roberto314/Unicomp3/USB-Serial InputBoard/pdf/USB-Serial InputBoard.pdf

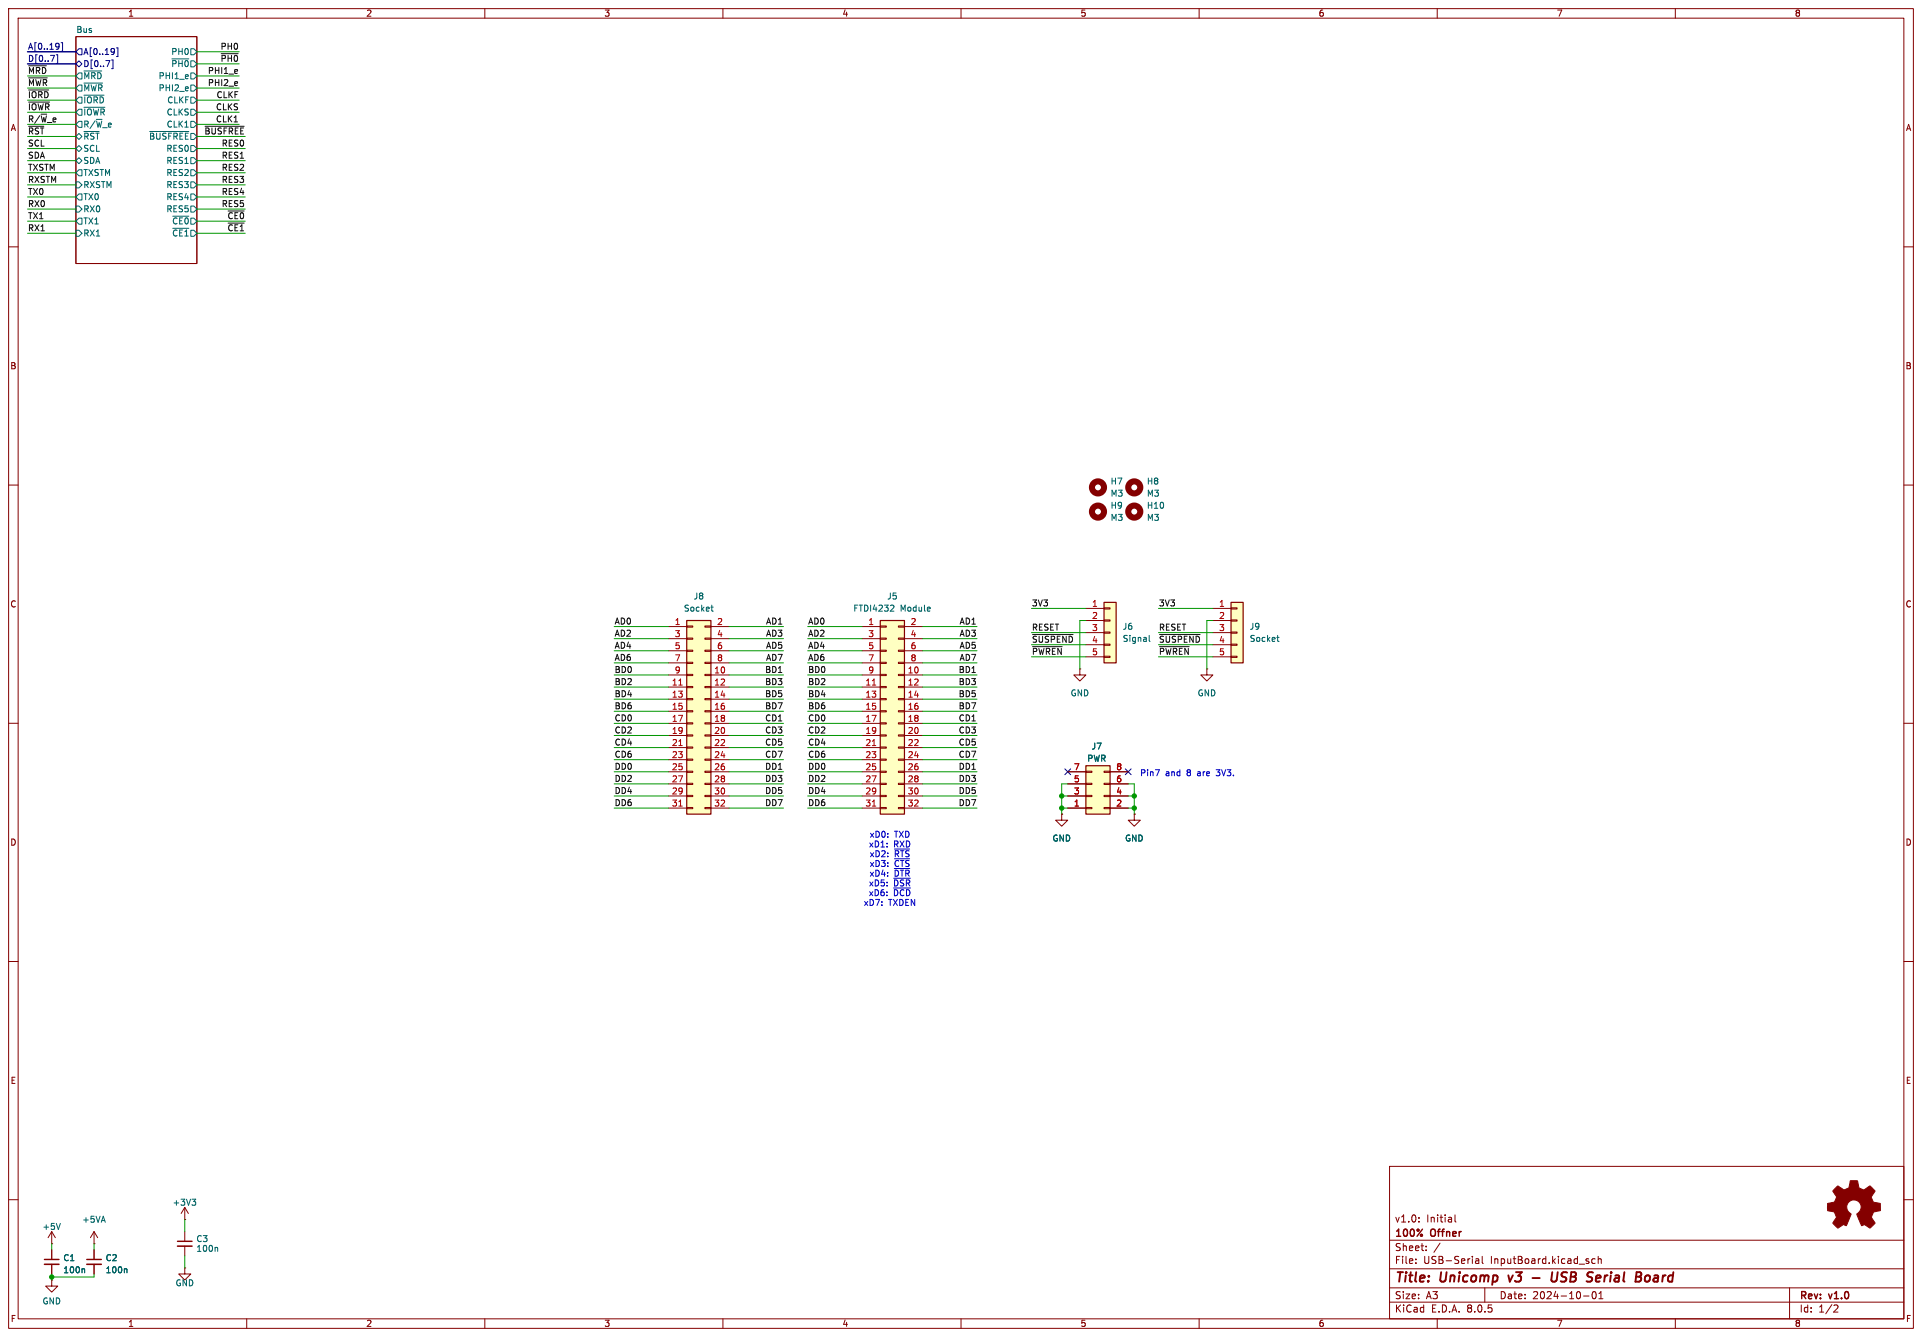
[picture p14: page 1]

xD0: TXD
xD1: RXD
xD2: ~{RTS} xD3: ~{CTS} xD4: ~{DTR} xD5: ~{DSR} xD6: ~{DCD} xD7: TXDEN

Id: 1/2 Title: Unicomp v3 - USB Serial Board

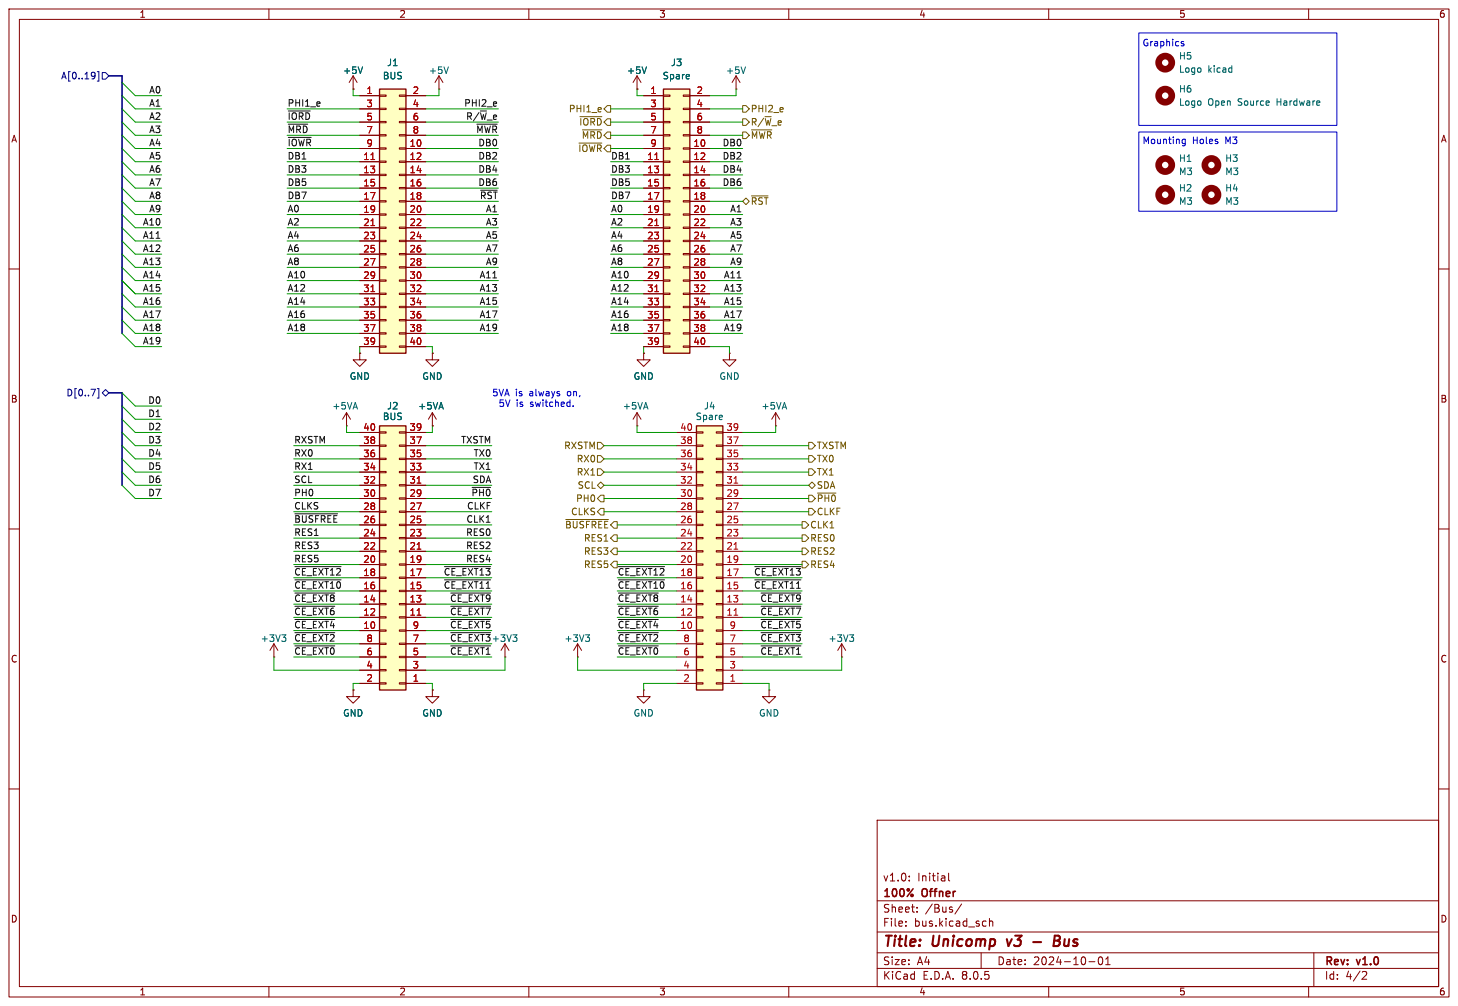
[picture p15: page 2]

Id: 4/2 Title: Unicomp v3 - Bus
