roberto314/Unicomp3/empty Boards/cpu_template_with_buffer/pdf/cpu_template_with_buffer.pdf

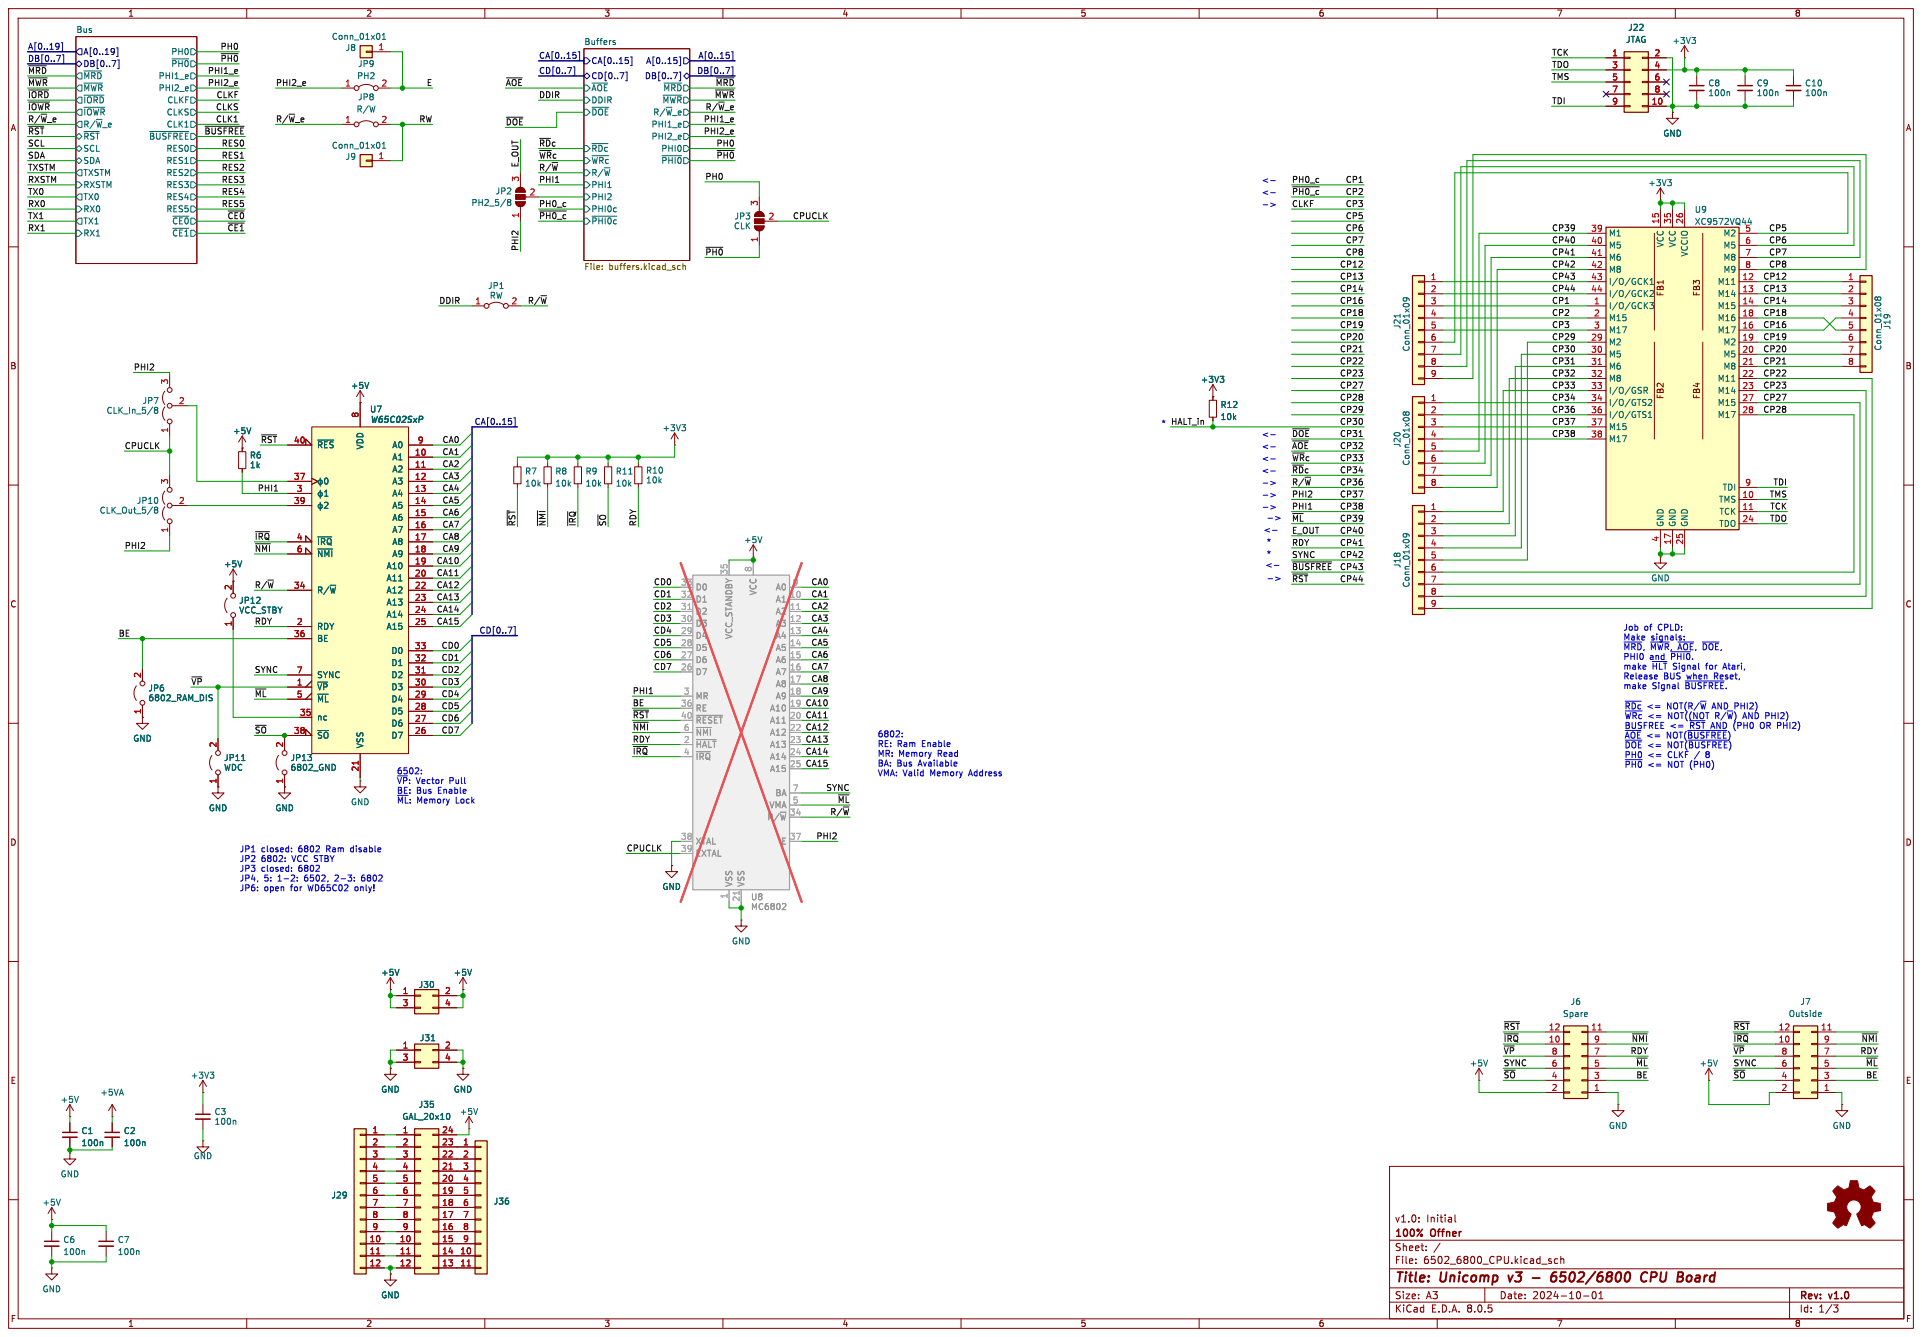
[picture p16: page 1]

DB[0..7] Buffers File: buffers.kicad_sch
PHI1_e CD6

~{DOE}<= NOT(~{BUSFREE}) PH0 <= CLKF / 8 ~{PH0}<= NOT (PH0) * <-

<- <- 6502: ~{VP}:Vector Pull BE: Bus Enable ~{ML}:Memory Lock

~{MRD},~{MWR},~{AOE},~{DOE}, PHI0 and ~{PHI0}. make ~{HLT}Signal for Atari, Release BUS when Reset, make Signal ~{BUSFREE}. <-
E_OUT

1 A1 10 A2 11 A3 12 A4 13 A5 14 A6 15 A7 16 A8 17 A9 18 A10 19 ~{HALT} 2 A11 20 VSS 21 A12 22 A13 23 A14 24 A15 25 D7 26 D6 27 D5 28 D4 29 MR 3 D3 30 D2 31 D1 32 D0 33 R/~{W}34 VCC_STANDBY 35 RE 36 E

~{RDc}<= NOT(R/~{W}AND PHI2)
~{WRc}<= NOT((NOT R/~{W})AND PHI2) BUSFREE <= ~{RST}AND (PH0 OR PHI2)

6802: RE: Ram Enable MR: Memory Read BA: Bus Available VMA: Valid Memory Address

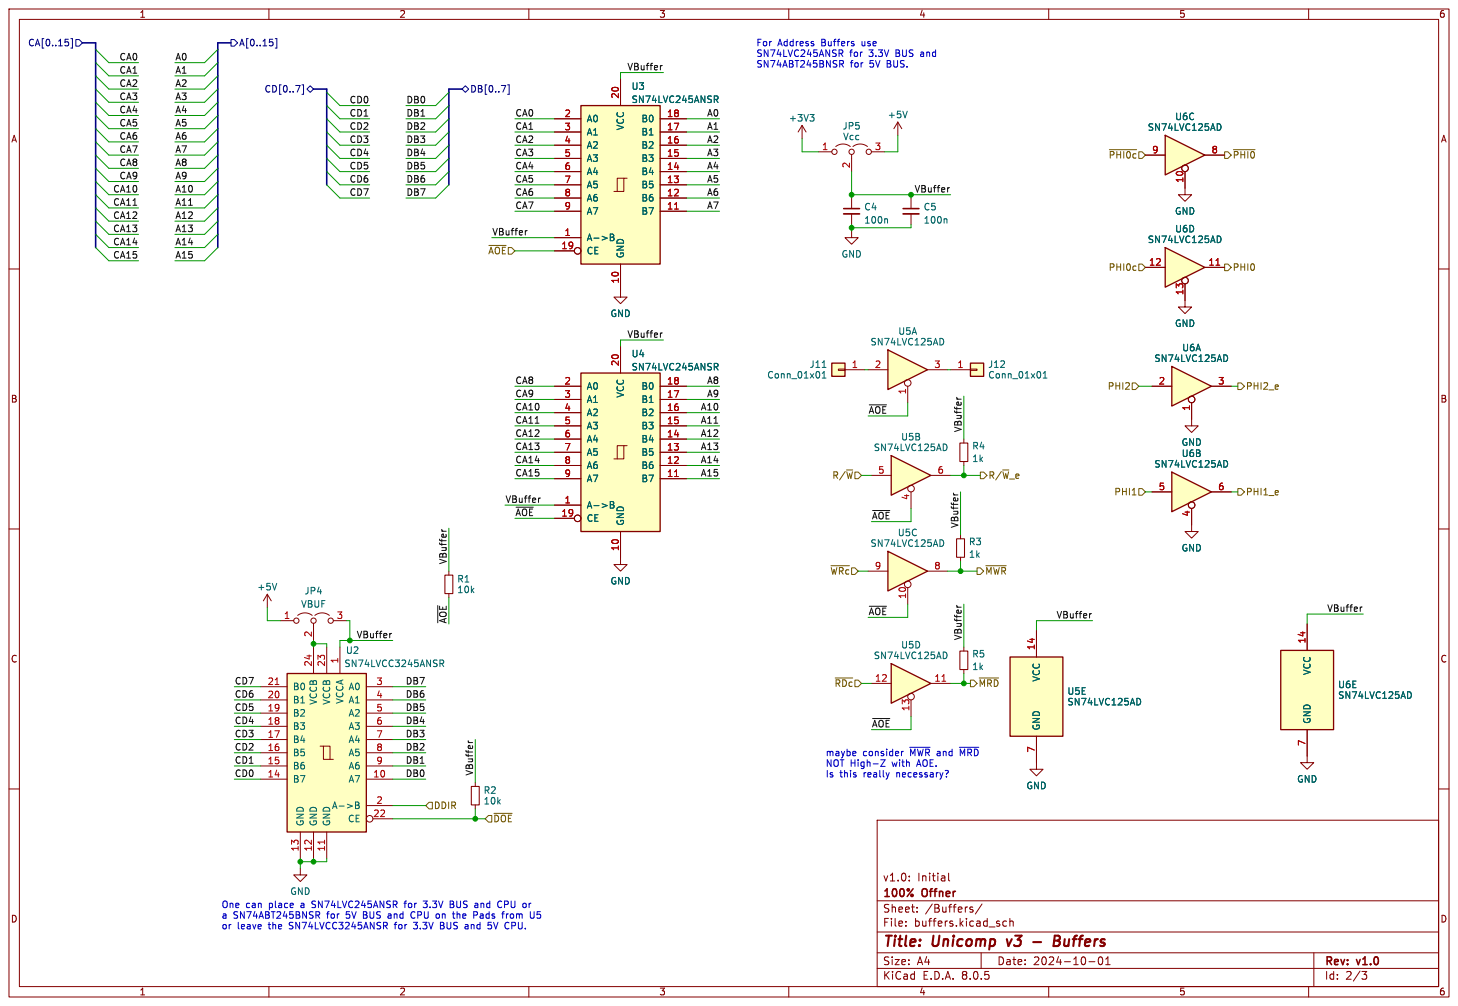
[picture p17: page 2]

1 A7 10 GND 11 GND 12 GND 13 B7 14 B6 15 B5 16 B4 17 B3 18 B2 19 A->B 2 B1 20 B0 21 CE 22 VCCB 23 VCCB 24 A0 3 A1 4 A2 5 A3 6 A4 7 A5 8 A6 9 U2 SN74LVCC3245ANSR

One can place a SN74LVC245ANSR for 3.3V BUS and CPU or a SN74ABT245BNSR for 5V BUS and CPU on the Pads from U5

Id: 2/3 Title: Unicomp v3 - Buffers

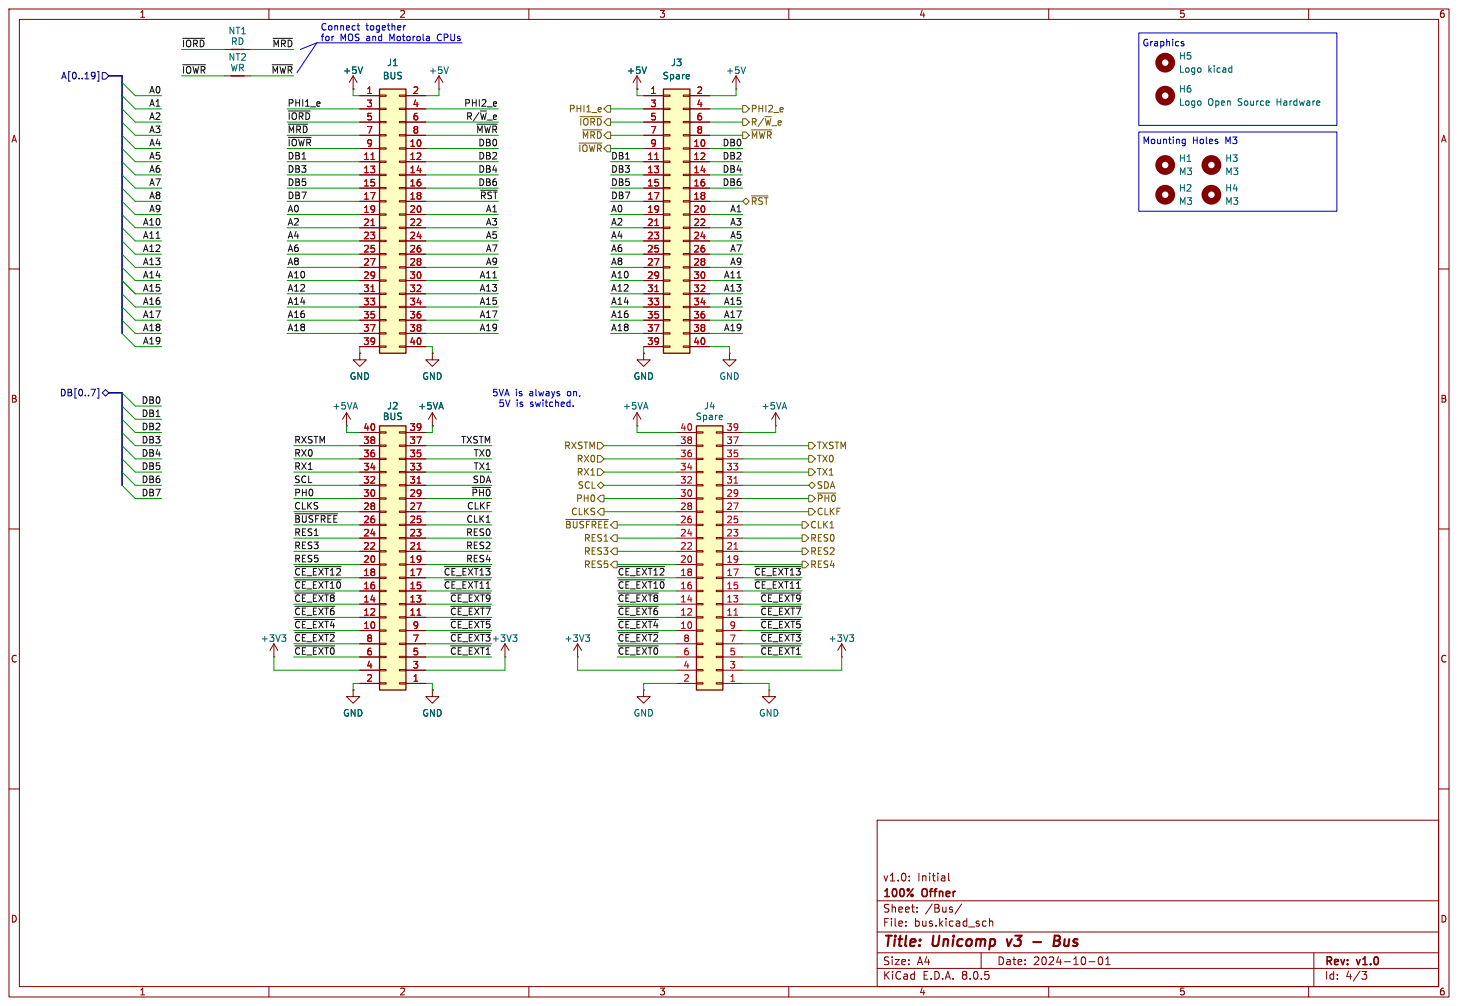
[picture p18: page 3]

Id: 4/3 Title: Unicomp v3 - Bus
