roberto314/Unicomp3/empty Boards/emptyBoard/pdf/emptyBoard.pdf

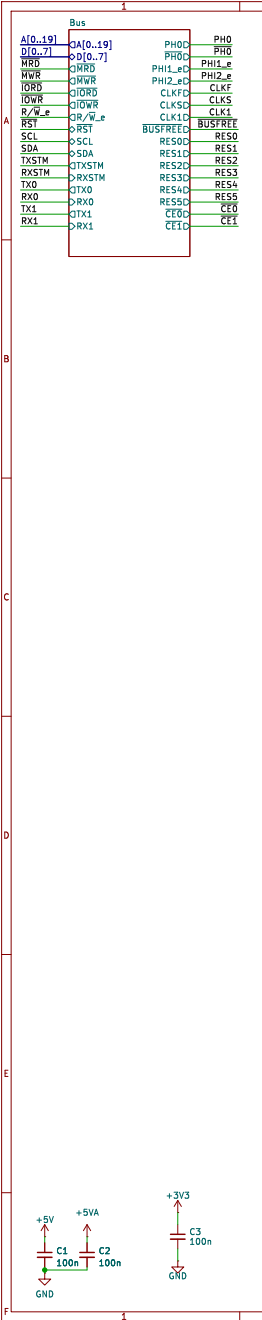
[picture p19: page 1]

Id: 1/2 Title: Unicomp v3 - xxx Board

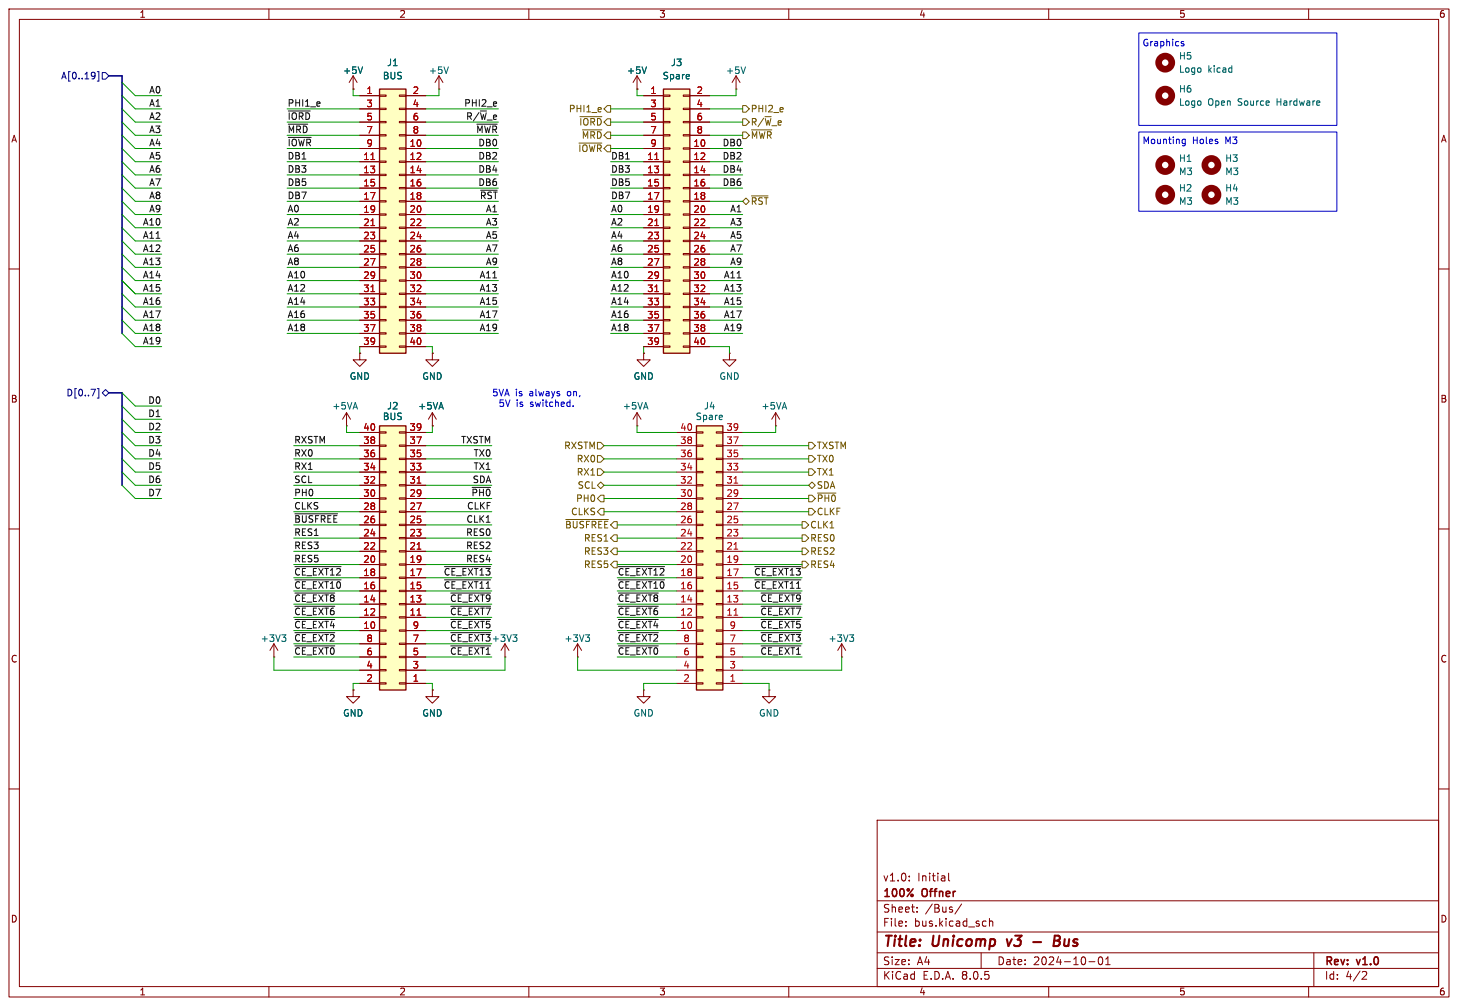
[picture p20: page 2]

Logo Open Source Hardware H5

Id: 4/2 Title: Unicomp v3 - Bus
