roberto314/Unicomp3/SerialBoards/MOT_SerialBoard/MOT_Serial_v11/pdf/MOT_Serial_v11.pdf

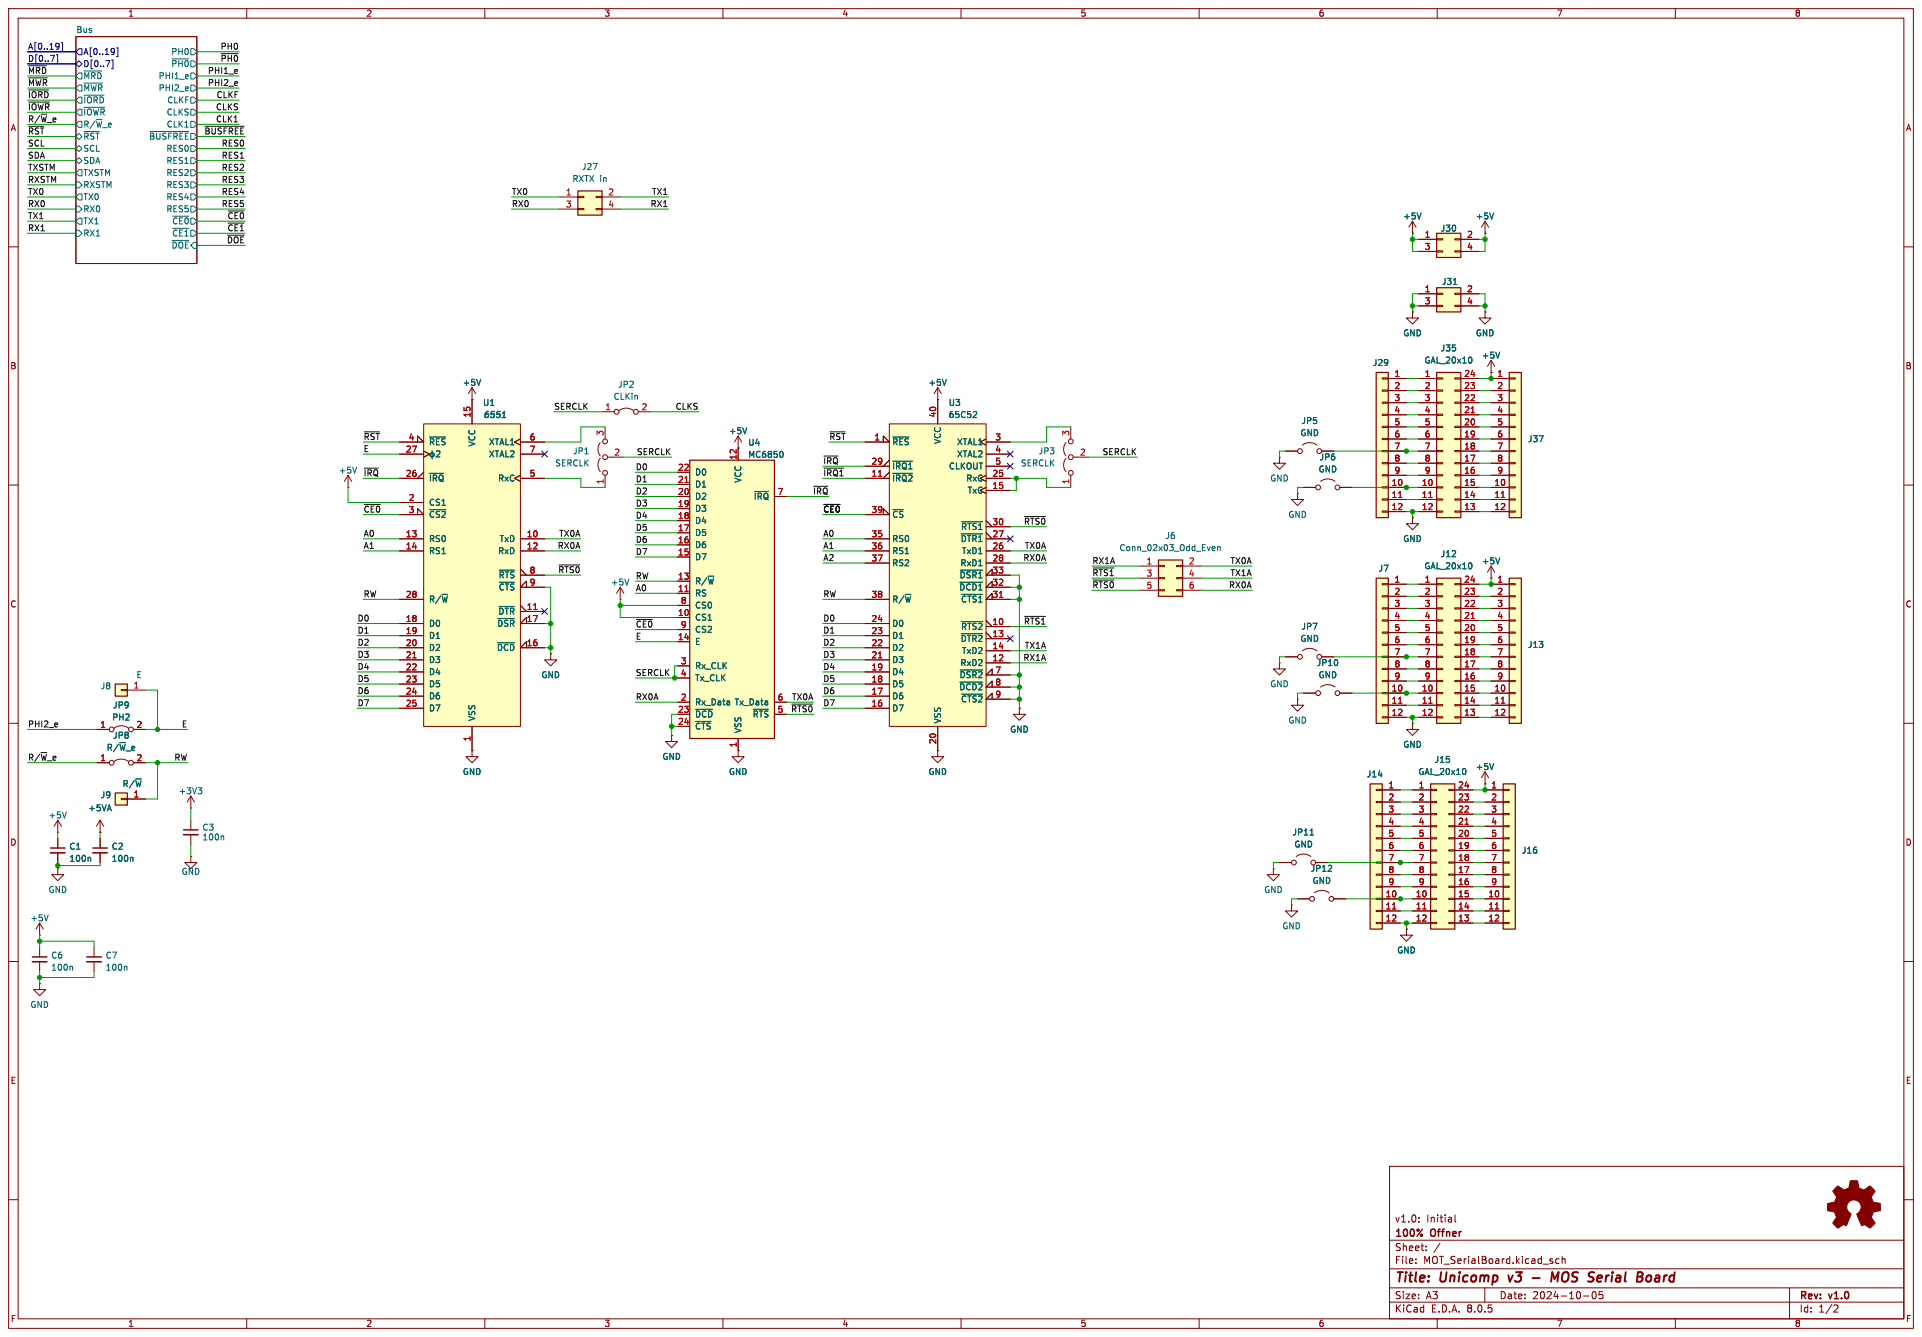
[picture p23: page 1]

1 TxD 10 ~{DTR}11 RxD 12 RS0 13 RS1 14 VCC 15

Id: 1/2 Title: Unicomp v3 - MOS Serial Board

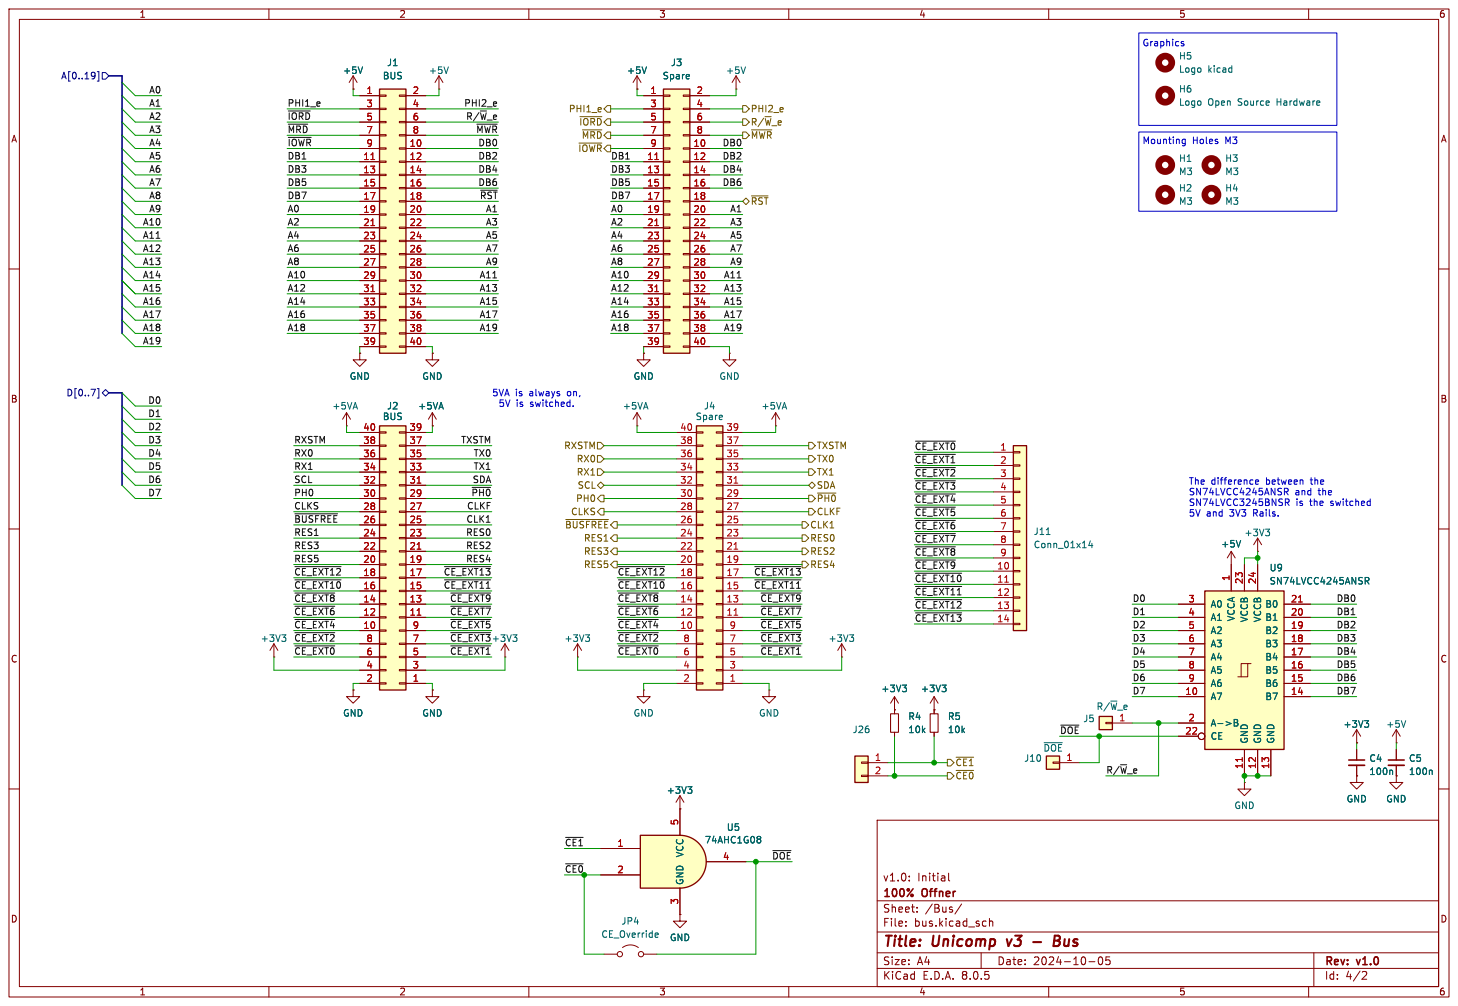
[picture p24: page 2]

5V and 3V3 Rails. Mounting Holes M3 Graphics 5VA is always on, 5V is switched. GND
DB3 DB7 ~{MRD}
~{IOWR}

Logo Open Source Hardware

1 A7 10 GND 11 GND 12 GND 13 B7 14 B6 15 B5 16 B4 17 B3 18 B2 19 A->B 2 B1 20 B0 21 CE 22 VCCB 23 VCCB 24 A0 3 A1 4 A2 5 A3 6 A4 7 A5 8 A6 9 +3V3 GND GND GND

1 A7 10 GND 11 GND 12 GND 13 B7 14 B6 15 B5 16 B4 17 B3 18 B2 19 A->B 2 B1 20 B0 21 CE 22 VCCB 23 VCCB 24 A0 3 A1 4 A2 5 A3 6 A4 7 A5 8 A6 9 U9SN74LVCC4245ANSR

Id: 4/2 Title: Unicomp v3 - Bus
