roberto314/Unicomp3/ParallelBoards/IEC_Extension/IEC_Extension_v1.0/pdf/IEC_Extension.pdf

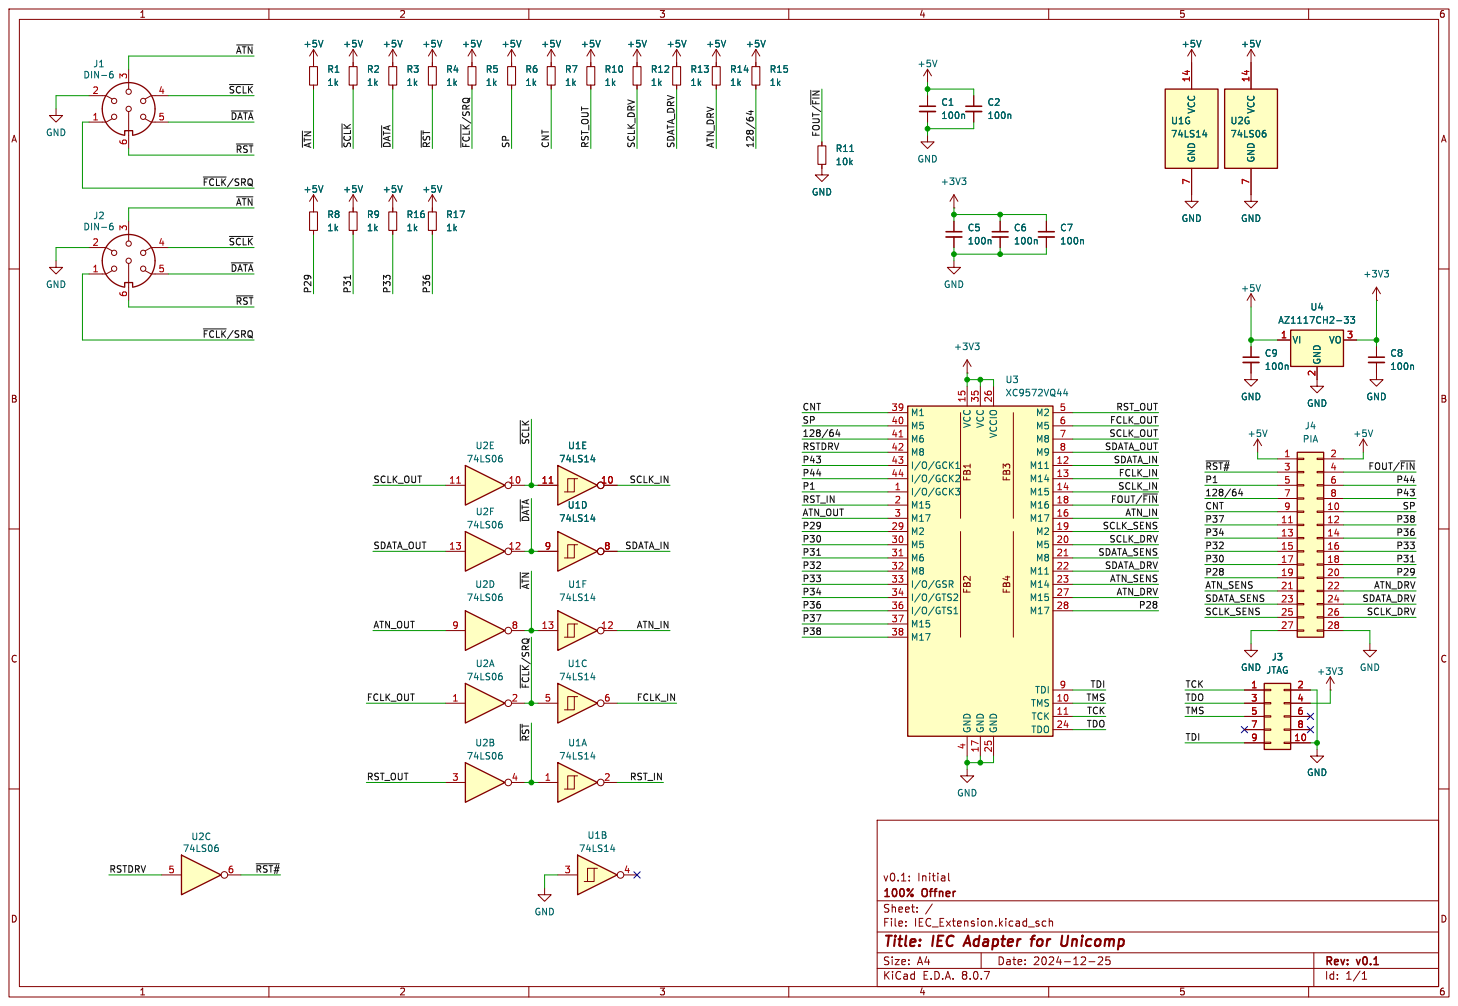
[picture p25: page 1]

Id: 1/1 Title: IEC Adapter for Unicomp
