roberto314/Unicomp3/CPU_Boards/AdapterBoards/6803DIP_Addon/pdf/6803_Addon.pdf

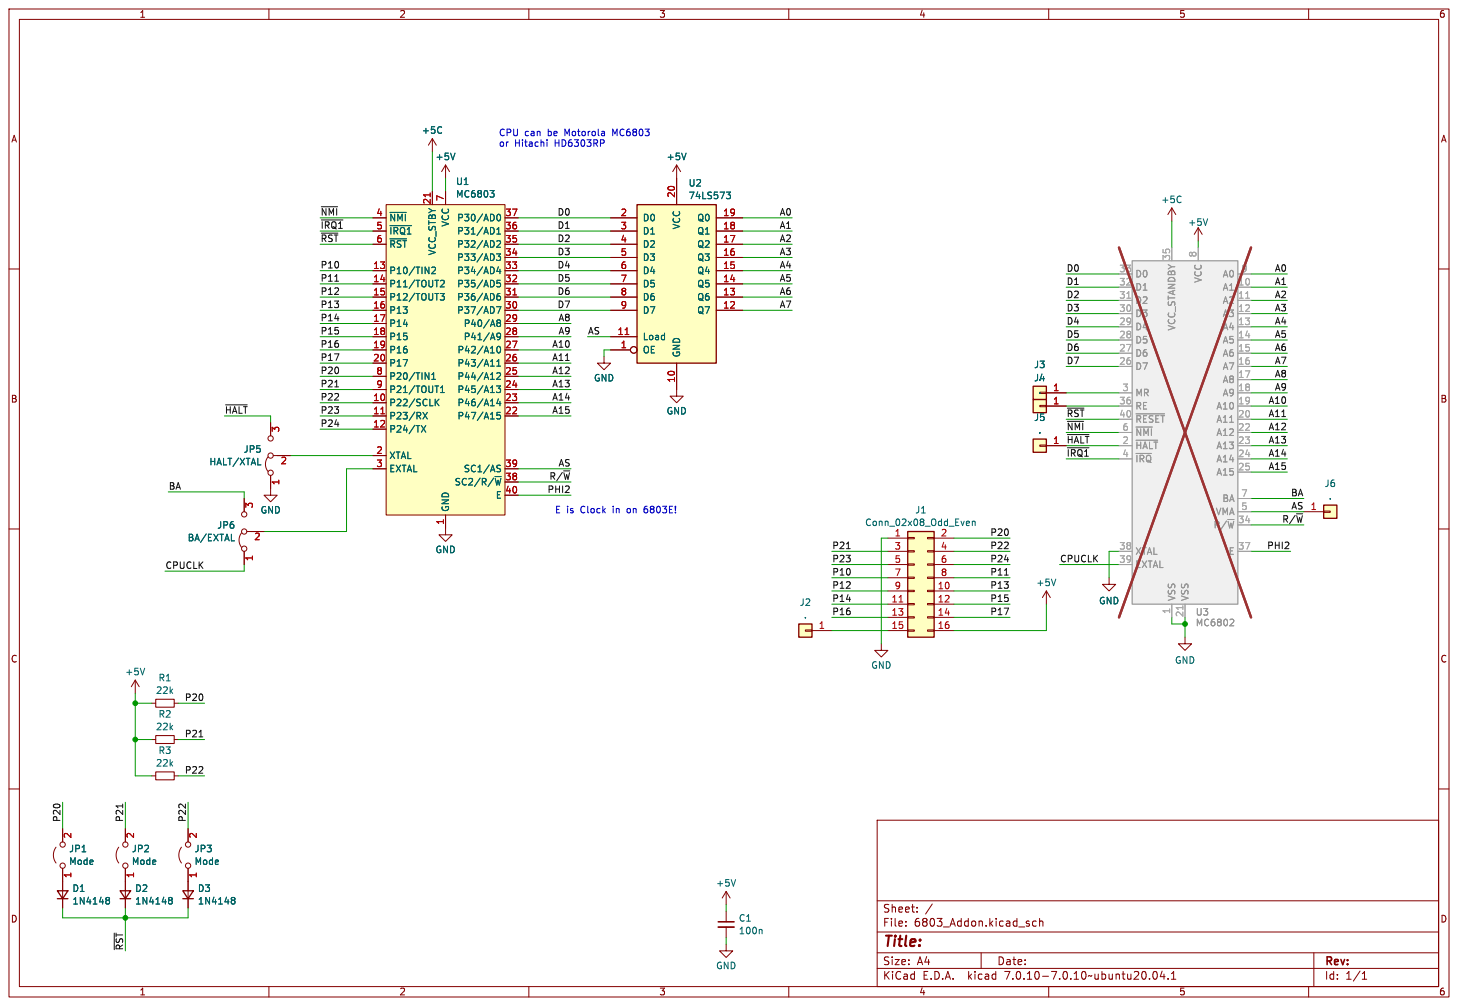
[picture p26: page 1]

1 P22/SCLK 10 P23/RX 11 P24/TX 12 P10/TIN2 13 P11/TOUT2 14 P12/TOUT3 15 P13 16 P14 17 P15 18 P16 19 XTAL 2 P17 20 VCC_STBY 21 P47/A15 22 P46/A14 23 P45/A13 24 P44/A12 25 P43/A11 26 P42/A10 27 P41/A9 28 P40/A8 29 EXTAL 3 P37/AD7 30 P36/AD6 31 P35/AD5 32 P34/AD4 33 P33/AD3 34 P32/AD2 35 P31/AD1 36 P30/AD0 37 SC2/R/~{W}38 SC1/AS 39 ~{NMI} 4 E

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

Id: 1/1 Title: File: 6803_Addon.kicad_sch Sheet: /
