roberto314/Unicomp3/RamRomBoard/schematics_v10/pdf/RamRomBoard.pdf

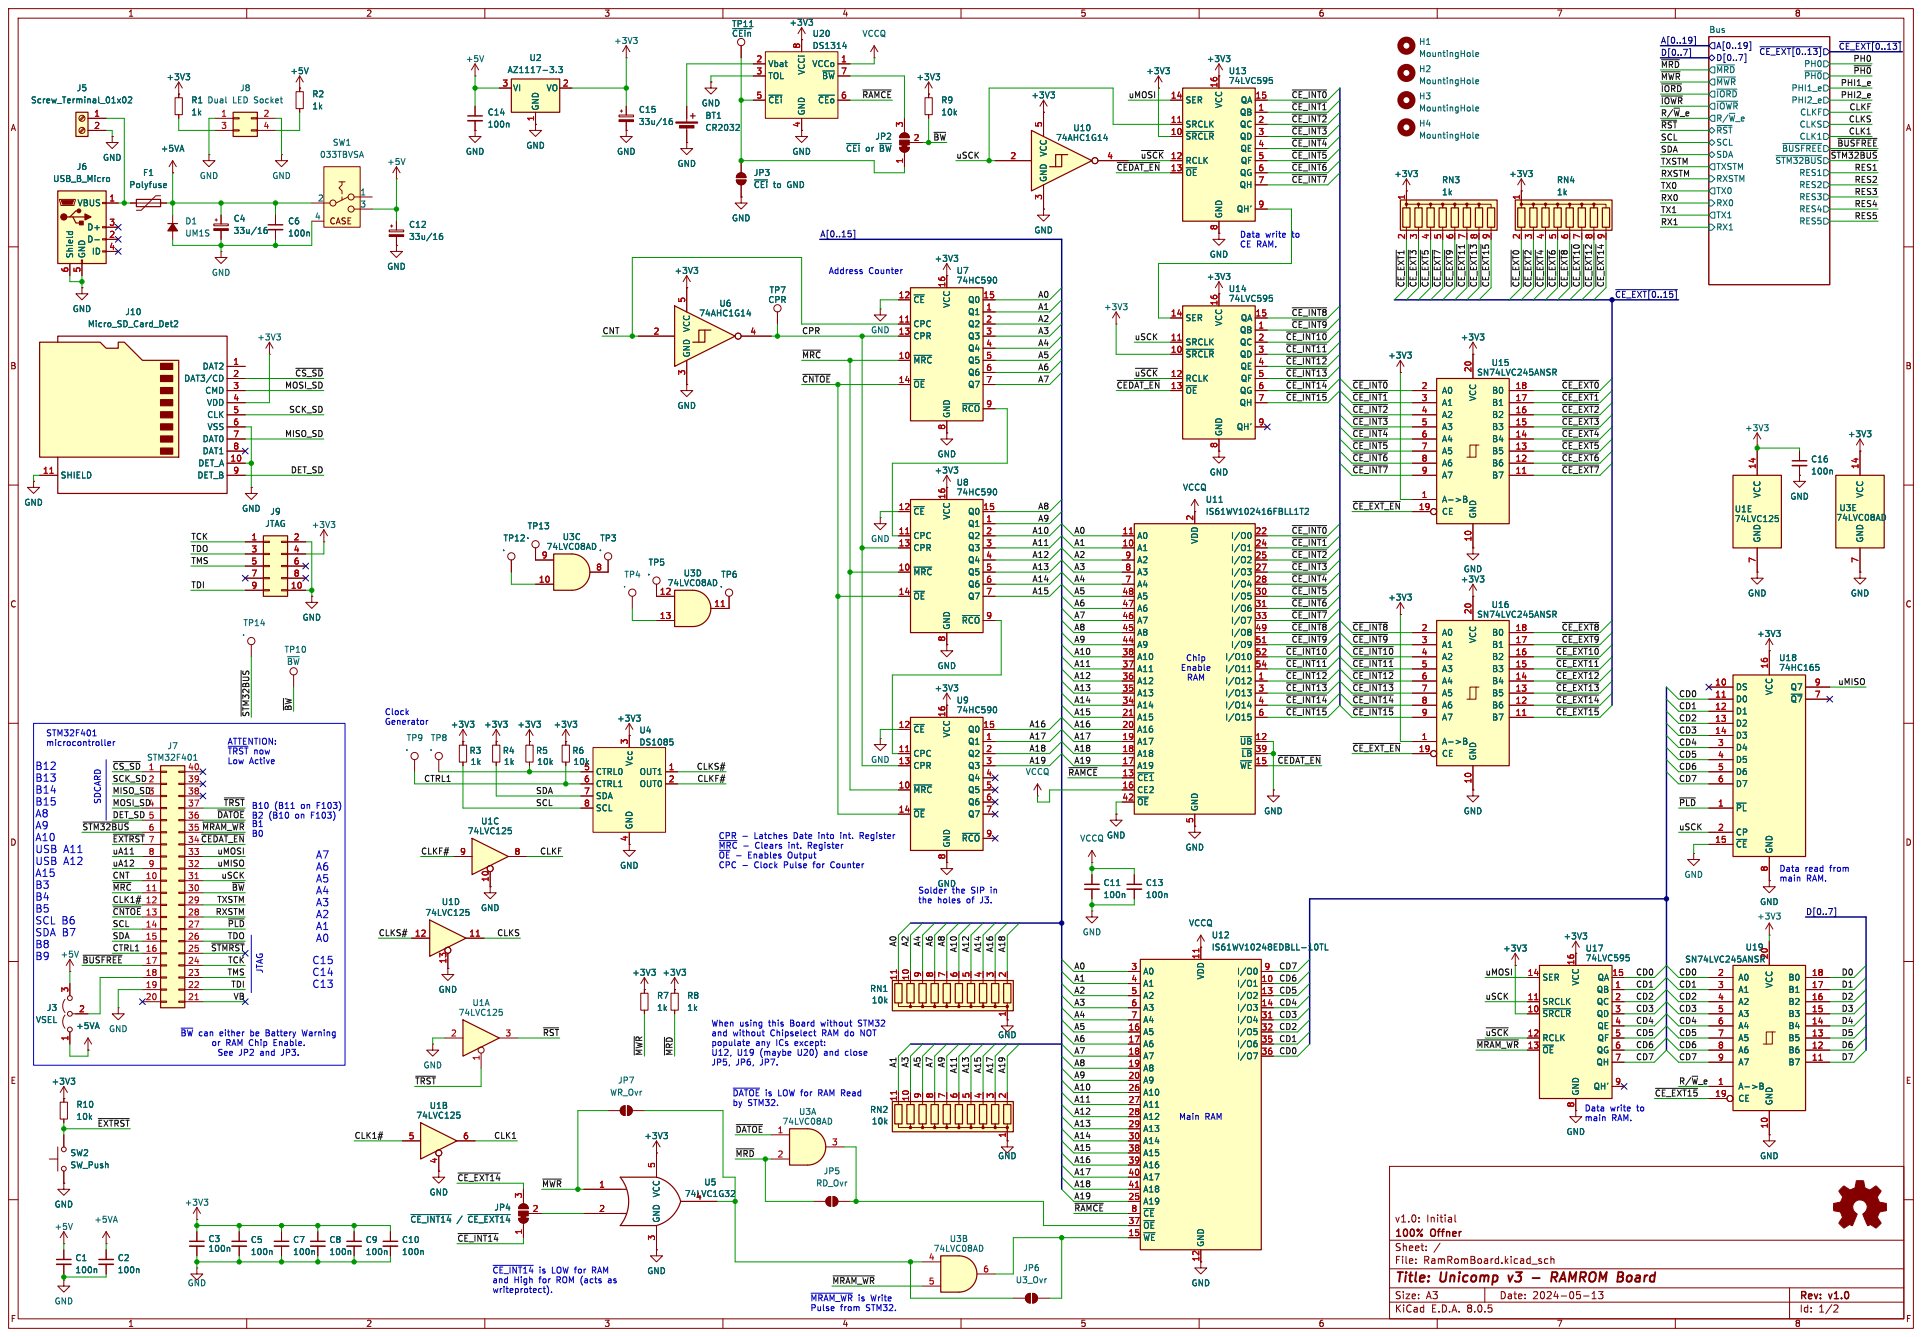
[picture p27: page 1]

+3V3 GND GND GND
TP11 ~{CEin} JP3 ~{CEi}to GND GND
JP2 ~{CEi}or ~{BW} +3V3 GND

3 U20 DS1314 VCCo 1 Vbat 2 TOL 3 GND

4 ~{CEi} 5 ~{CEo}6 ~{BW} VCCi 7

Data write to CE RAM. B10 (B11 on F103) B2 (B10 on F103) ATTENTION: ~{TRST}now

and High for ROM (acts as writeprotect). SDCARD
~{RST} MISO_SD

CPR - Latches Date into int. Register
~{MRC}- Clears int. Register
1k GND

main RAM. Solder the SIP in

the holes of J3. ~{CE_INT14}is LOW for RAM

~{DATOE}is LOW for RAM Read

Id: 1/2 Title: Unicomp v3 - RAMROM Board

~{MRAM_WR}is Write Pulse from STM32.

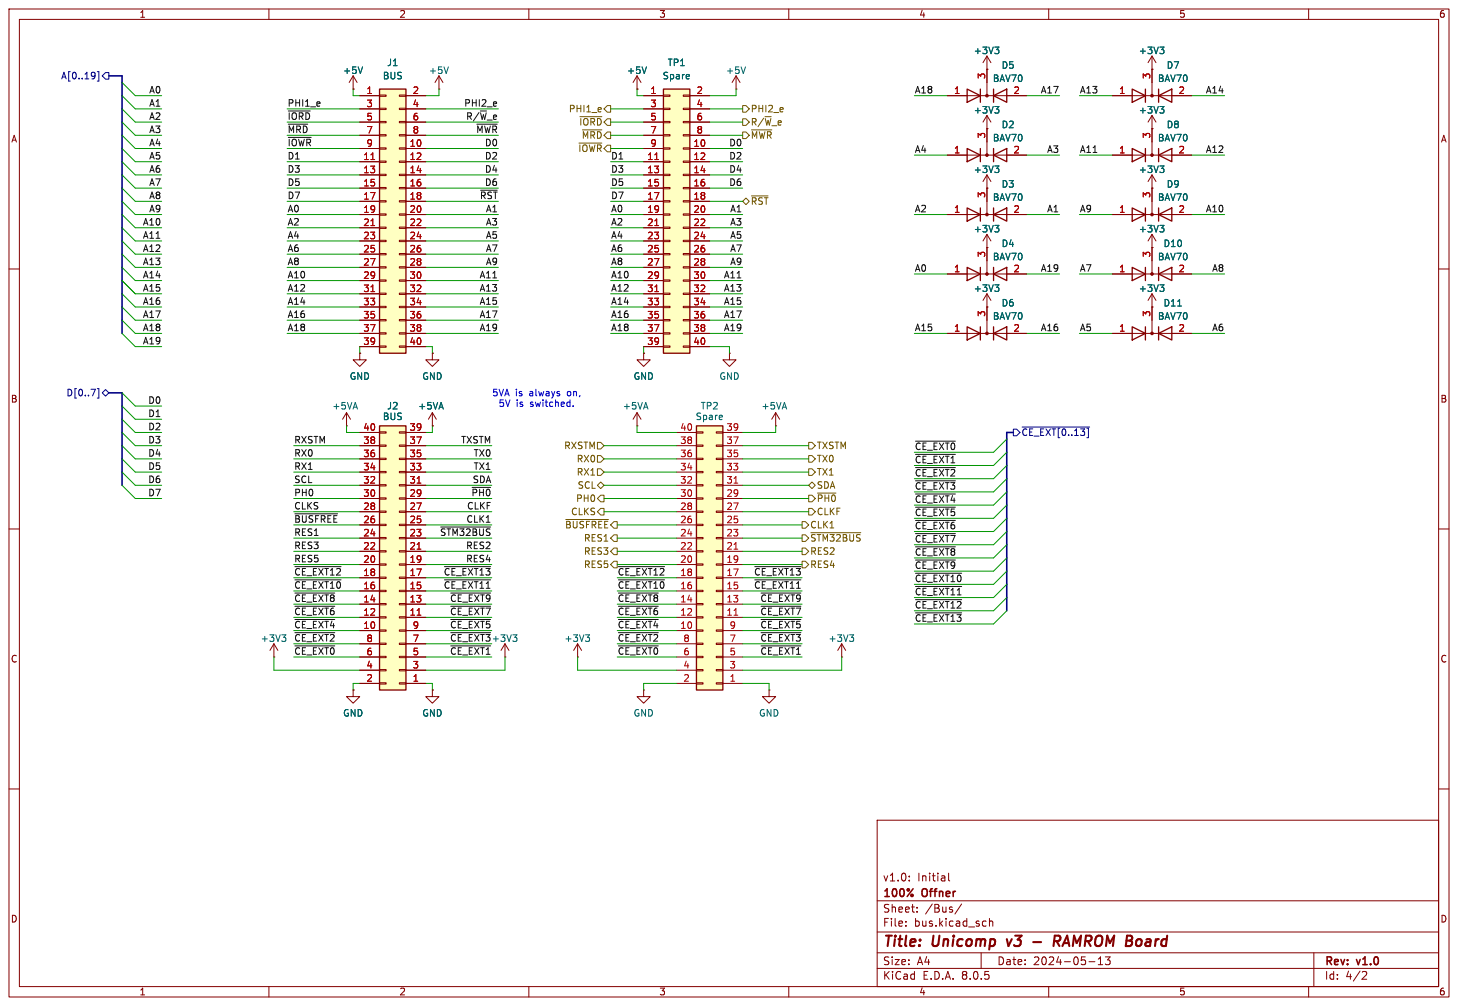
[picture p28: page 2]

Id: 4/2 Title: Unicomp v3 - RAMROM Board
