roberto314/Unicomp3/CPU_Boards/6809_CPU/schematics_v10/pdf/6809_CPU.pdf

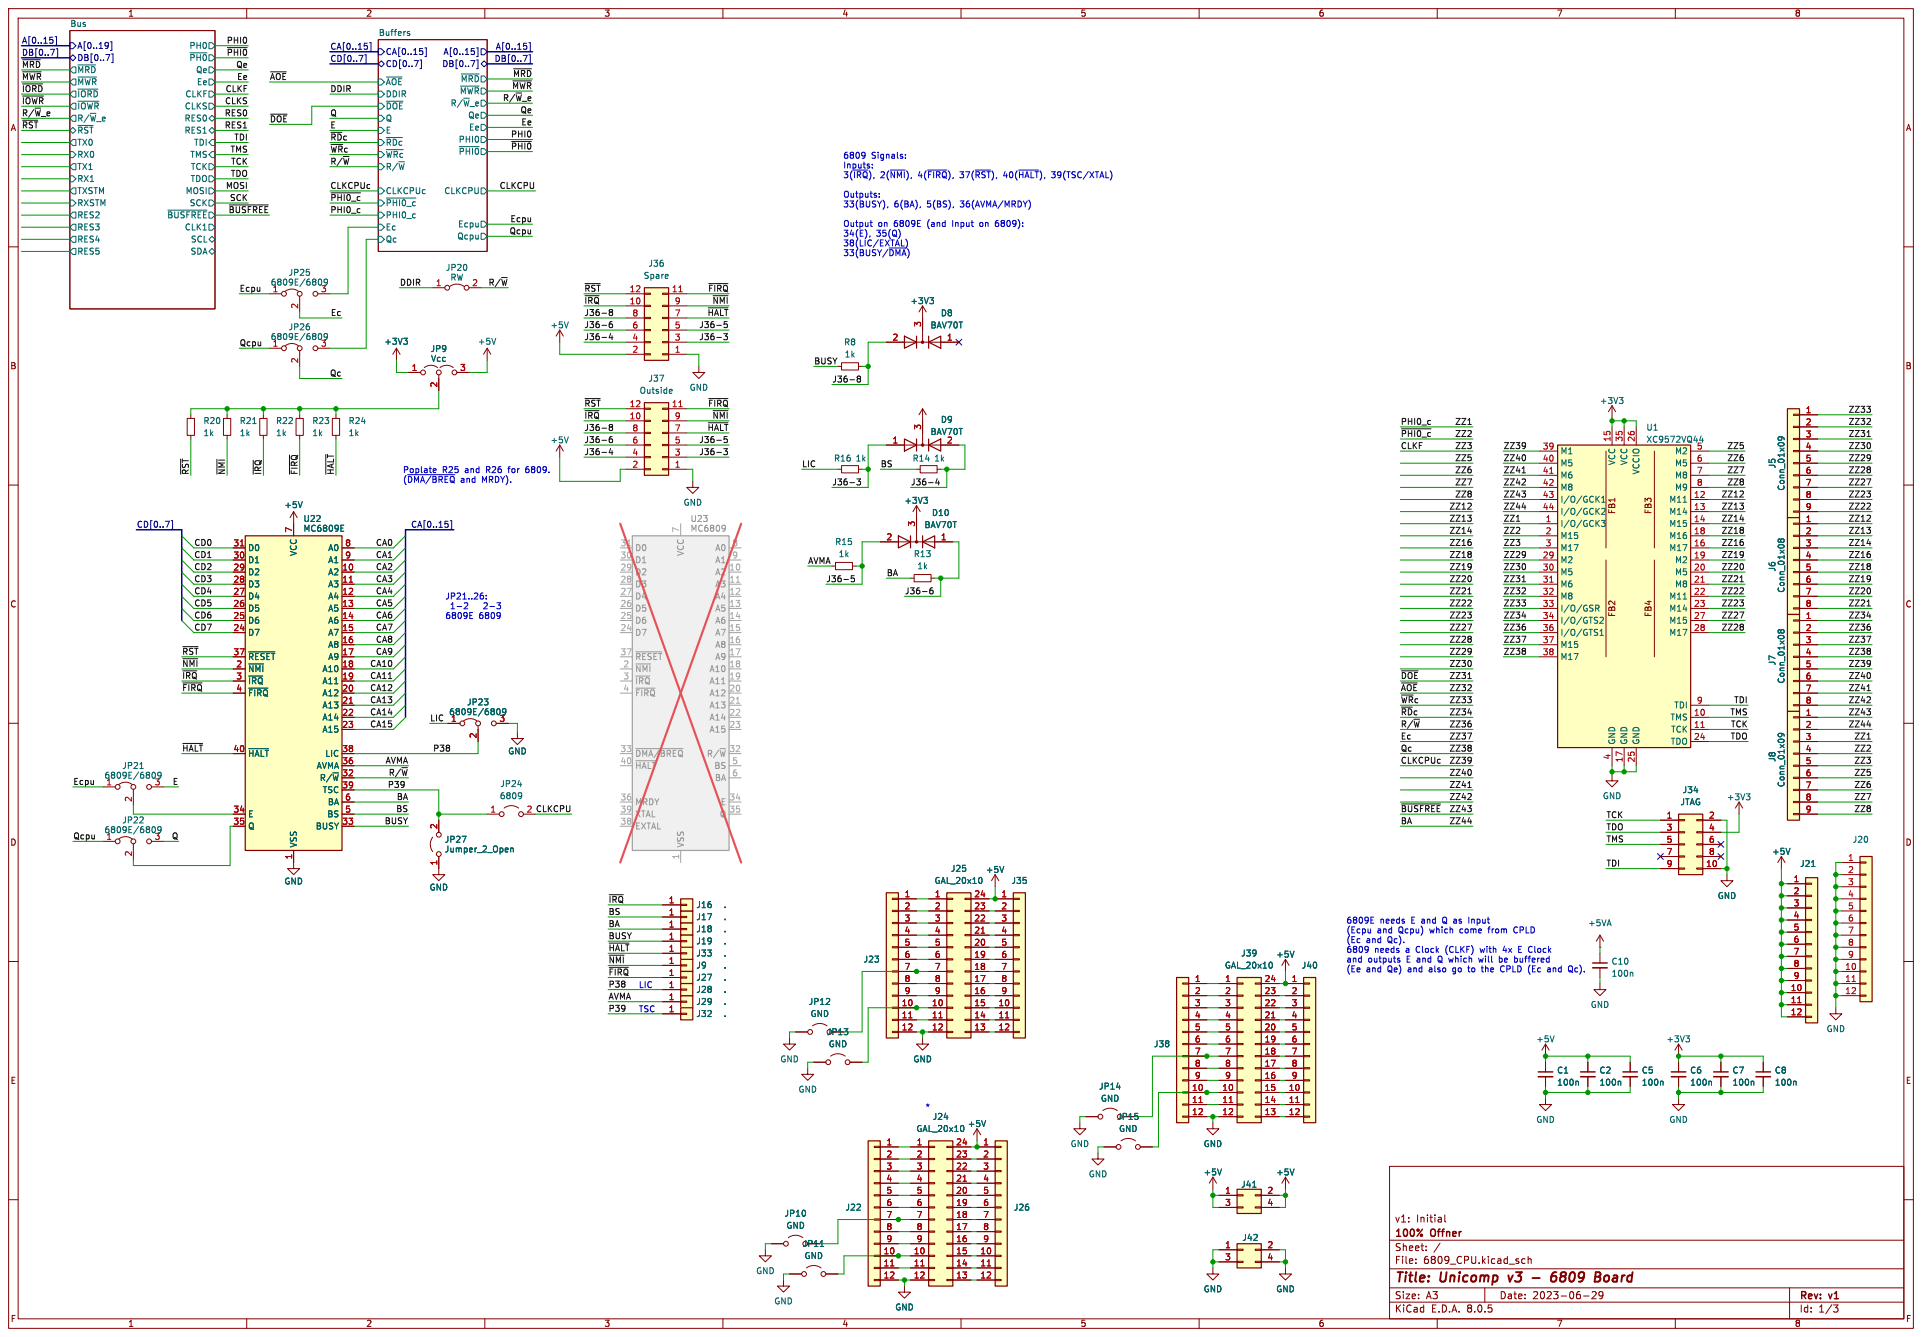
[picture p29: page 1]

TDI RES0 RES1 TCK MOSI SCK
J36-8 ~{RST} CLKCPU
J36 Spare GND

Inputs:
3(~{IRQ}),2(~{NMI}),4(~{FIRQ}),37(~{RST}),40(~{HALT}),39(TSC/XTAL)

Outputs:
33(BUSY), 6(BA), 5(BS), 36(AVMA/MRDY)

Output on 6809E (and Input on 6809):
38(LIC/EXTAL)
33(BUSY/~{DMA})

1 A2 10 A3 11 A4 12 A5 13 A6 14 A7 15 A8 16 A9 17 A10 18 A11 19 ~{NMI} 2 A12 20 A13 21 A14 22 A15 23 D7 24 D6 25 D5 26 D4 27 D3 28 D2 29 ~{IRQ} 3 D1 30 D0 31 R/~{W}32 ~{DMA/BREQ} 33 E

(Ee and Qe) and also go to the CPLD (Ec and Qc). LIC
TSC

(Ecpu and Qcpu) which come from CPLD
(Ec and Qc). 6809 needs a Clock (CLKF) with 4x E Clock and outputs E and Q which will be buffered

Id: 1/3 Title: Unicomp v3 - 6809 Board

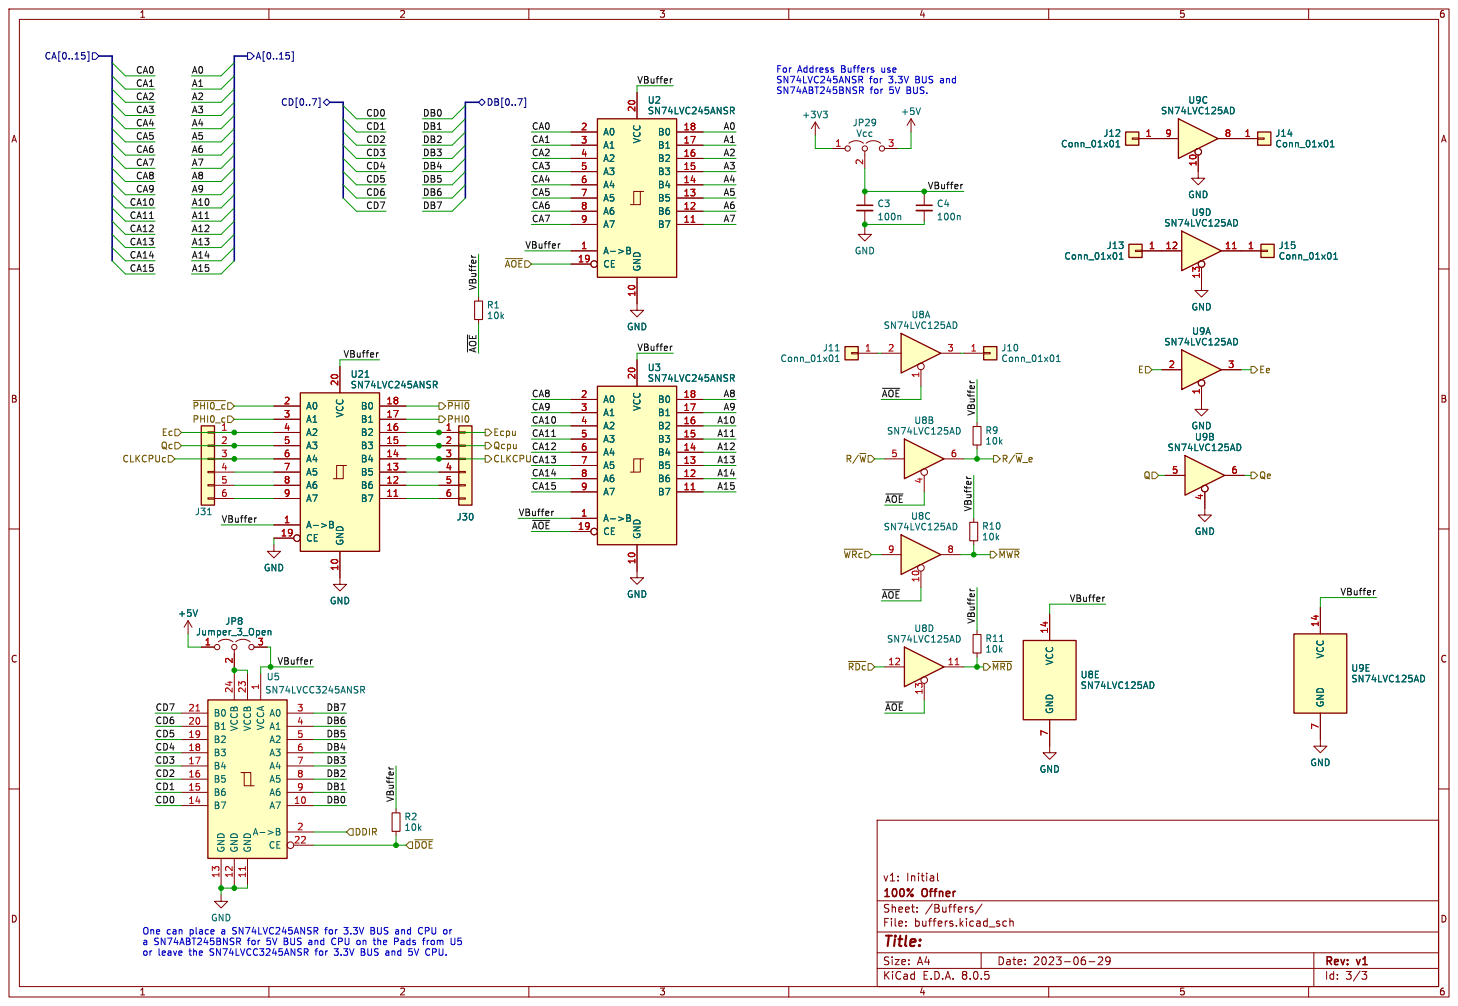
[picture p30: page 2]

1 A7 10 GND 11 GND 12 GND 13 B7 14 B6 15 B5 16 B4 17 B3 18 B2 19 A->B 2 B1 20 B0 21 CE 22 VCCB 23 VCCB 24 A0 3 A1 4 A2 5 A3 6 A4 7 A5 8 A6 9 U5 SN74LVCC3245ANSR

One can place a SN74LVC245ANSR for 3.3V BUS and CPU or a SN74ABT245BNSR for 5V BUS and CPU on the Pads from U5

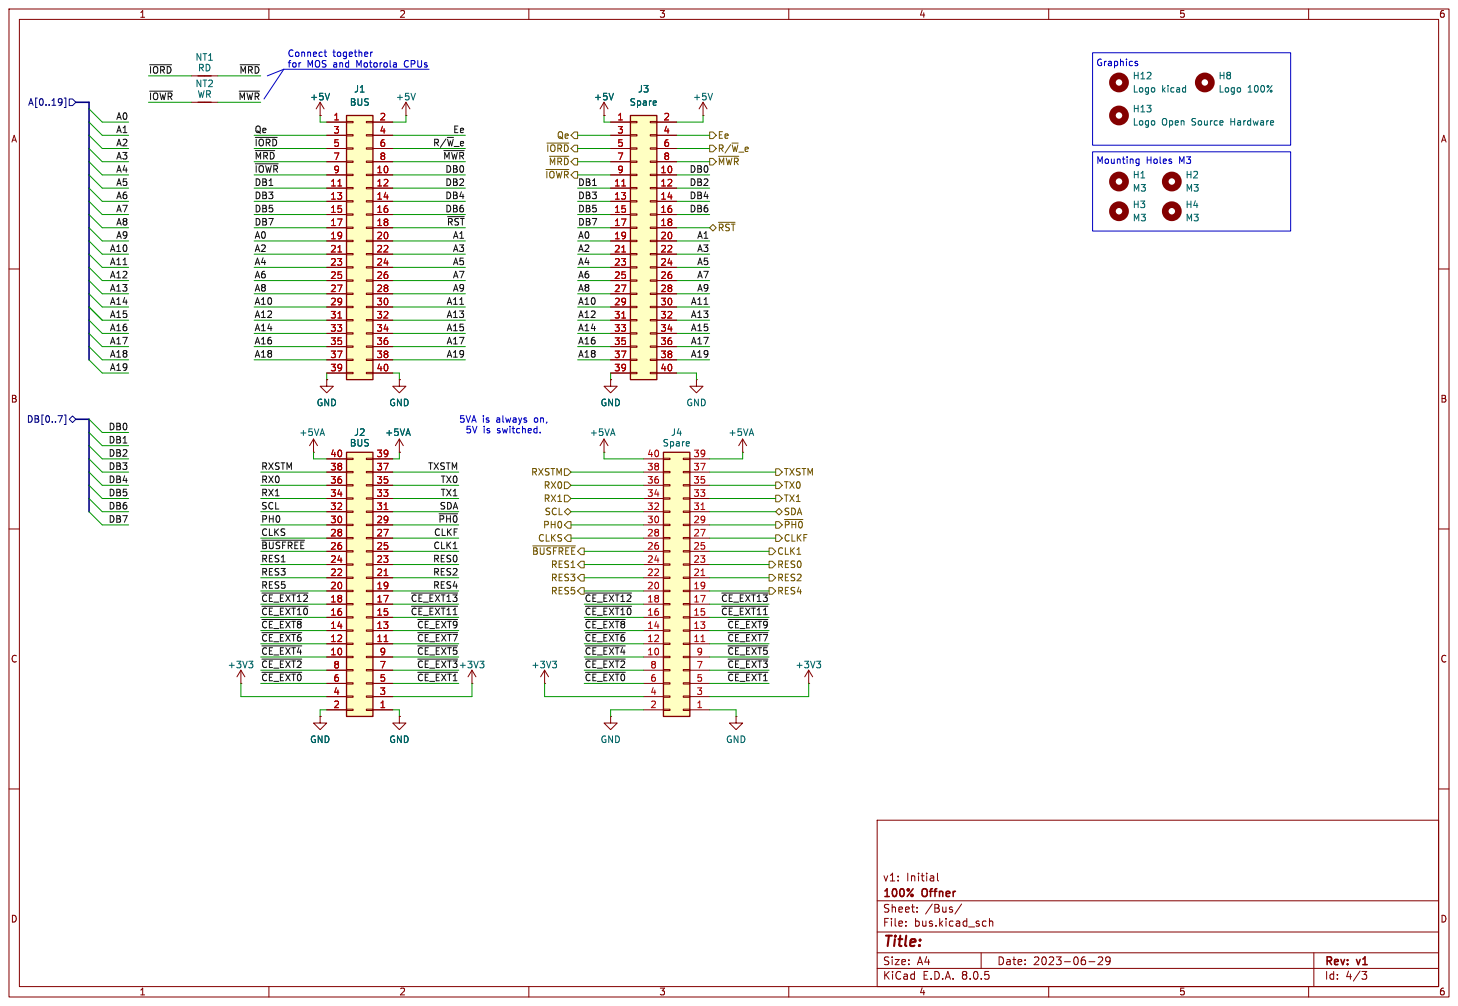
[picture p31: page 3]

Logo Open Source Hardware NT2 WR
