roberto314/Unicomp3/FloppyControllerBoards/schematics_v10/WD1771_Board/pdf/WD1771_Board.pdf

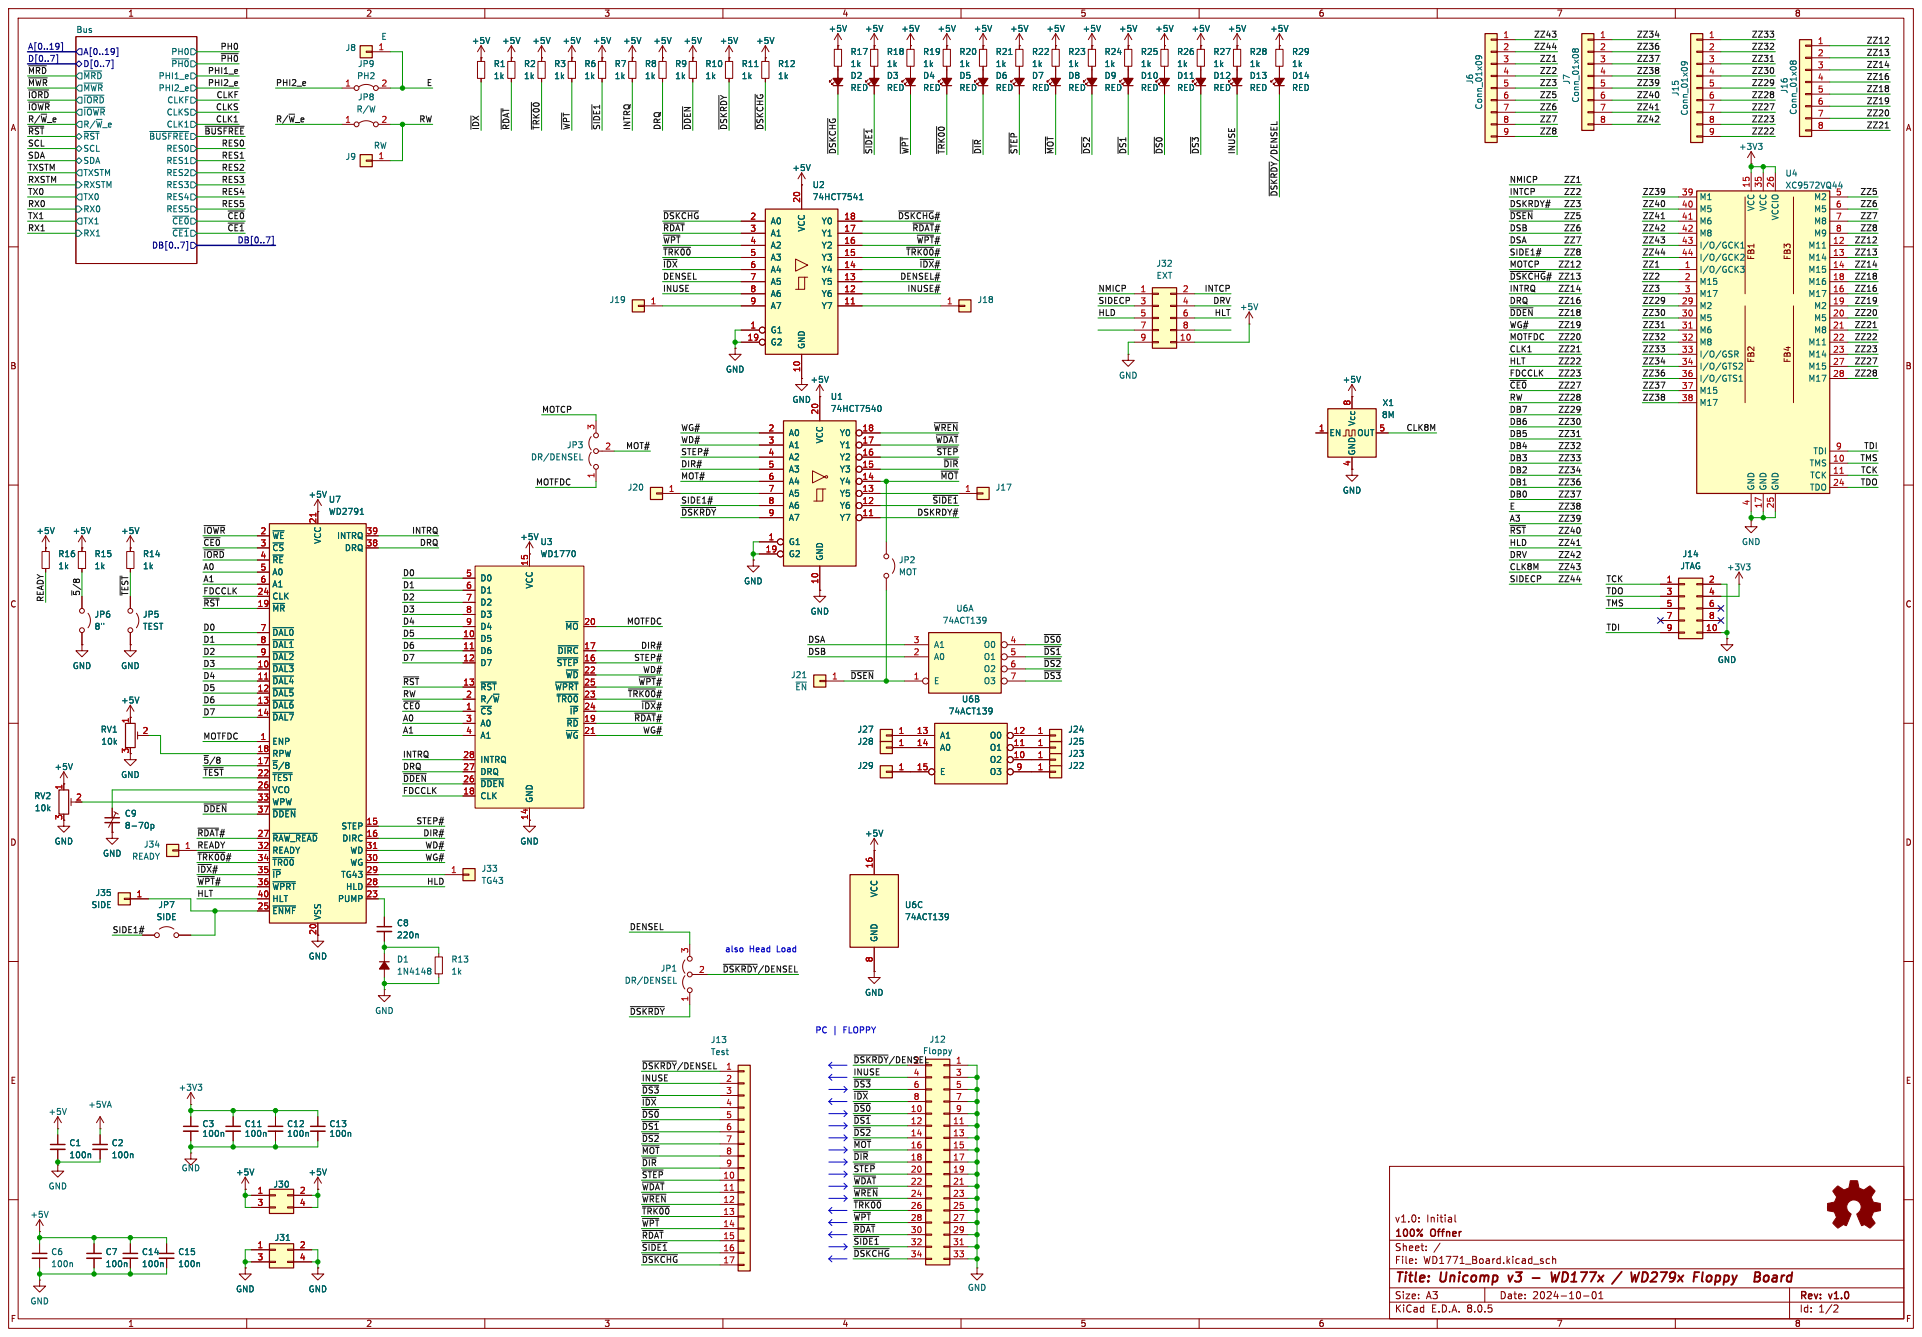
[picture p32: page 1]

~{IDX}# DENSEL# ~{IDX} DRQ

INUSE# STEP# WD# DIR# WG# MOT#

~{RST} SIDECP DRV HLD

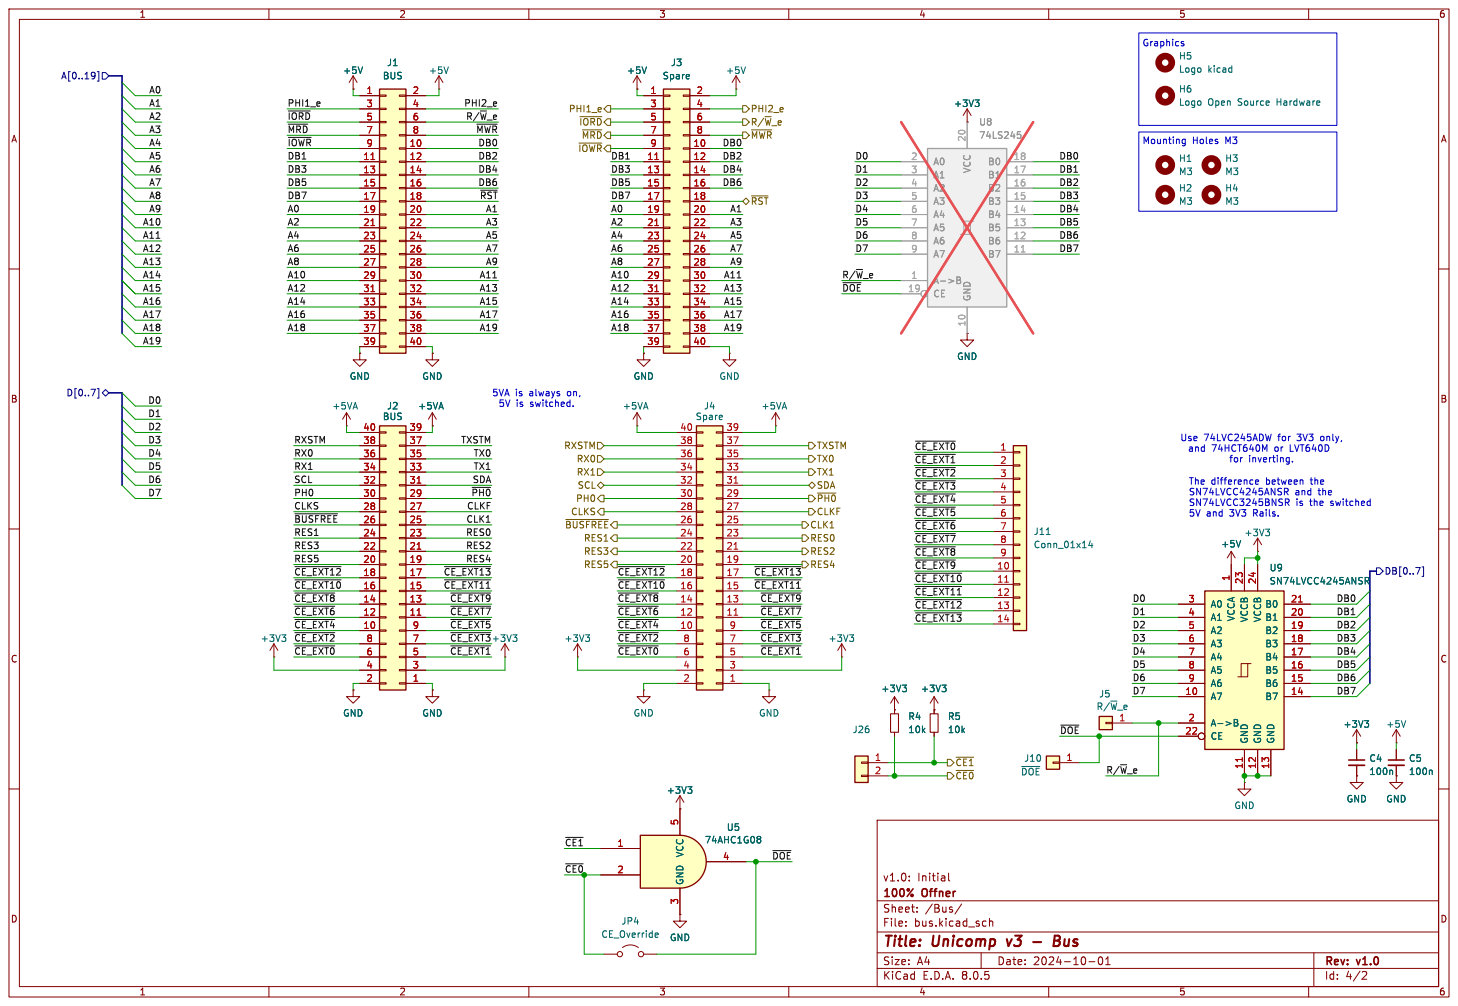
[picture p33: page 2]

5V and 3V3 Rails. Use 74LVC245ADW for 3V3 only, and 74HCT640M or LVT640D

1 A7 10 GND 11 GND 12 GND 13 B7 14 B6 15 B5 16 B4 17 B3 18 B2 19 A->B 2 B1 20 B0 21 CE 22 VCCB 23 VCCB 24 A0 3 A1 4 A2 5 A3 6 A4 7 A5 8 A6 9 U9SN74LVCC4245ANSR

1 A7 10 GND 11 GND 12 GND 13 B7 14 B6 15 B5 16 B4 17 B3 18 B2 19 A->B 2 B1 20 B0 21 CE 22 VCCB 23 VCCB 24 A0 3 A1 4 A2 5 A3 6 A4 7 A5 8 A6 9 +3V3

Id: 4/2 Title: Unicomp v3 - Bus
