roberto314/Unicomp3/MMU_Board/schematics/MMU_v1/MMU_v1.kicad_pcb

## KiCad design MMU_Board/schematics/MMU_v1/MMU_v1.kicad_pcb (2025-03-13)

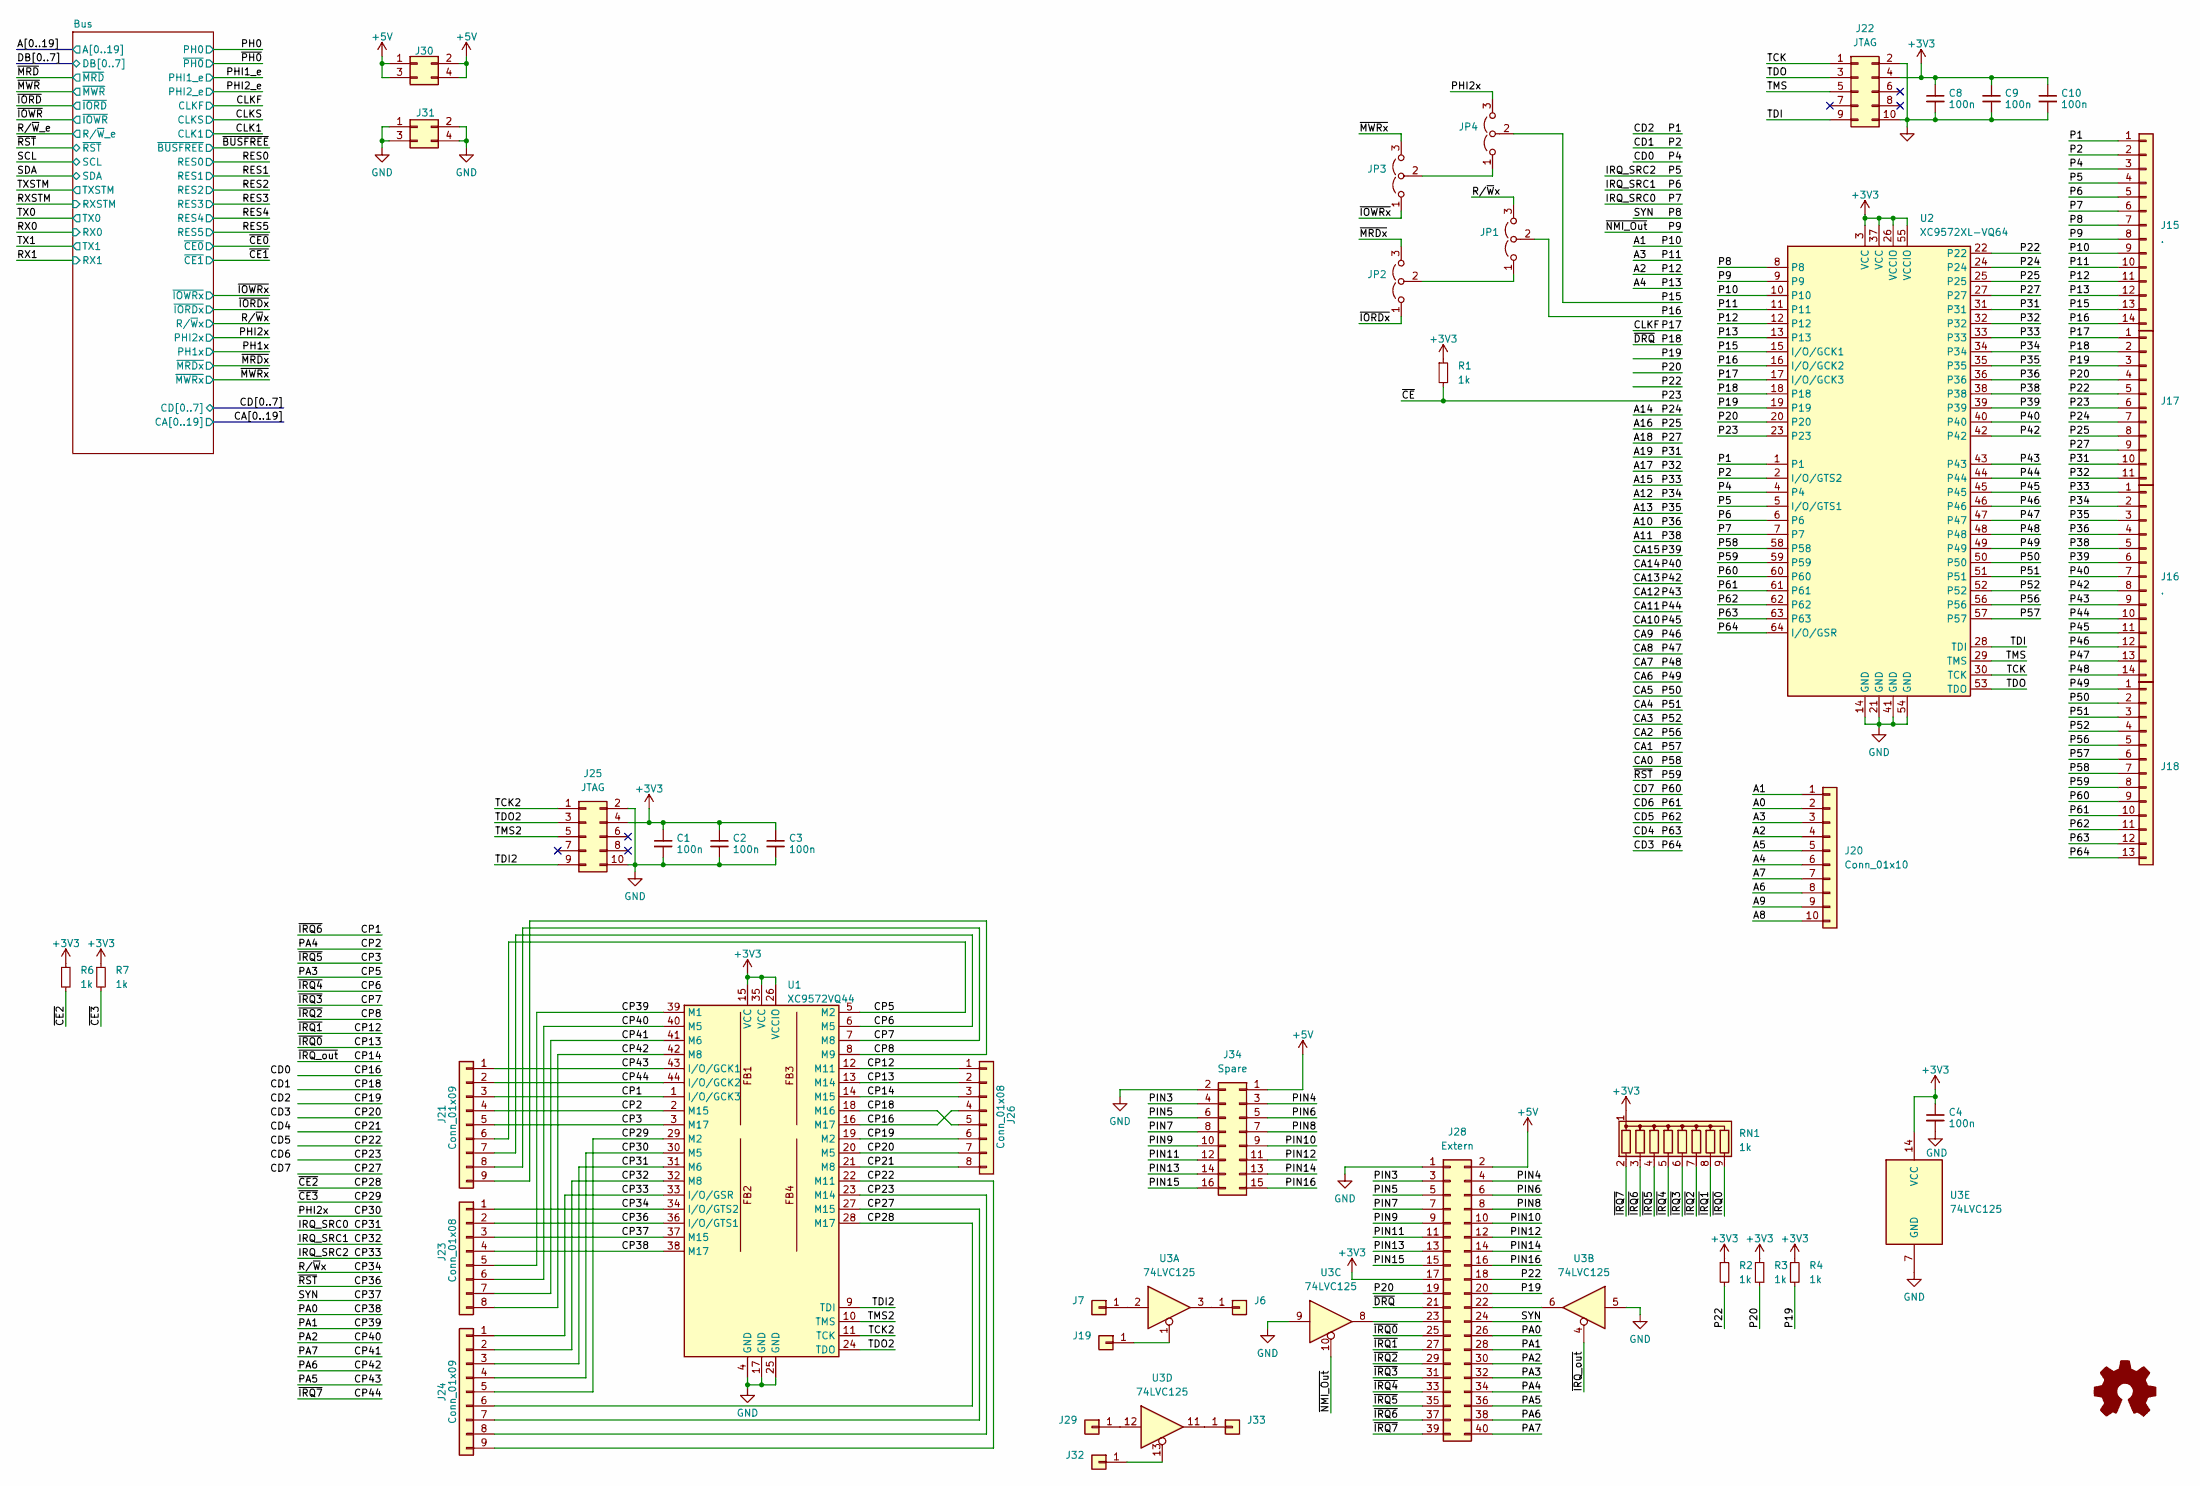
[picture p71: schematic MMU_v1.kicad_sch, Unicomp v3 - MMU Board]

Parts:
C1, C2, C3, C4, C8, C9, C10: 100n; C_1206_3216Metric
J6, J7, J19, J29, J32, J33: Conn_01x01; PinSocket_1x01_P1.27mm_Vertical
J15, J16: .; PinSocket_1x14_P2.00mm_Vertical
J17: Conn_01x11; PinSocket_1x11_P2.00mm_Vertical
J18: Conn_01x13; PinSocket_1x13_P2.00mm_Vertical
J20: Conn_01x10; PinSocket_1x10_P2.00mm_Vertical
J21, J24: Conn_01x09; PinHeader_1x09_P2.54mm_Vertical
J22, J25: JTAG; PinHeader_2x05_P2.54mm_Horizontal
J23, J26: Conn_01x08; PinHeader_1x08_P2.54mm_Vertical
J28: Extern; PinHeader_2x20_P2.54mm_Horizontal
J30, J31: Conn_02x02_Odd_Even; PinSocket_2x02_P2.54mm_Vertical
J34: Spare; PinSocket_2x08_P2.54mm_Vertical
JP1, JP2, JP3, JP4: Jumper_3_Open; SolderJumper-3_P1.3mm_Open_RoundedPad1.0x1.5mm
R1, R2, R3, R4, R6, R7: 1k; R_1206_3216Metric_Pad1.30x1.75mm_HandSolder
RN1: 1k; R_Array_SIP9
U1: XC9572VQ44; TQFP-44_10x10mm_P0.8mm
U2: XC9572XL-VQ64; TQFP-64_10x10mm_P0.5mm
U3: 74LVC125; SOIC-14_3.9x8.7mm_P1.27mm

Connections:
+3V3: C1.1, C2.1, C3.1, C4.1, C8.1, C9.1, C10.1, J22.4, J25.4, J28.17, R1.1, R2.1, R3.1, R4.1, R6.1, R7.1, RN1.1 (common), U1.15 (VCC), U1.26 (VCCIO), U1.35 (VCC), U2.3 (VCC), U2.26 (VCCIO), U2.37 (VCC), U2.55 (VCCIO), U3.14 (VCC); also elsewhere on the board
+5V: J28.2, J30.1, J30.2, J30.3, J30.4, J34.1; also elsewhere on the board
/A0: J20.2; also elsewhere on the board
/A1: J15.9, J20.1, U2.10; also elsewhere on the board
/A2: J15.11, J20.4, U2.12; also elsewhere on the board
/A3: J15.10, J20.3, U2.11; also elsewhere on the board
/A4: J15.12, J20.6, U2.13; also elsewhere on the board
/A5: J20.5; also elsewhere on the board
/A6: J20.8; also elsewhere on the board
/A7: J20.7; also elsewhere on the board
/A8: J20.10; also elsewhere on the board
/A9: J20.9; also elsewhere on the board
/A10: J16.4, U2.36; also elsewhere on the board
/A11: J16.5, U2.38; also elsewhere on the board
/A12: J16.2, U2.34; also elsewhere on the board
/A13: J16.3, U2.35; also elsewhere on the board
/A14: J17.7, U2.24; also elsewhere on the board
/A15: J16.1, U2.33; also elsewhere on the board
/A16: J17.8, U2.25; also elsewhere on the board
/A17: J17.11, U2.32; also elsewhere on the board
/A18: J17.9, U2.27; also elsewhere on the board
/A19: J17.10, U2.31; also elsewhere on the board
/CA0: J18.7, U2.58; also elsewhere on the board
/CA1: J18.6, U2.57; also elsewhere on the board
/CA2: J18.5, U2.56; also elsewhere on the board
/CA3: J18.4, U2.52; also elsewhere on the board
/CA4: J18.3, U2.51; also elsewhere on the board
/CA5: J18.2, U2.50; also elsewhere on the board
/CA6: J18.1, U2.49; also elsewhere on the board
/CA7: J16.14, U2.48; also elsewhere on the board
/CA8: J16.13, U2.47; also elsewhere on the board
/CA9: J16.12, U2.46; also elsewhere on the board
/CA10: J16.11, U2.45; also elsewhere on the board
/CA11: J16.10, U2.44; also elsewhere on the board
/CA12: J16.9, U2.43; also elsewhere on the board
/CA13: J16.8, U2.42; also elsewhere on the board
/CA14: J16.7, U2.40; also elsewhere on the board
/CA15: J16.6, U2.39; also elsewhere on the board
/CD0: J15.3, U2.4; also elsewhere on the board
/CD1: J15.2, U2.2 (I/O/GTS2); also elsewhere on the board
/CD2: J15.1, U2.1; also elsewhere on the board
/CD3: J18.13, U2.64 (I/O/GSR); also elsewhere on the board
/CD4: J18.12, U2.63; also elsewhere on the board
/CD5: J18.11, U2.62; also elsewhere on the board
/CD6: J18.10, U2.61; also elsewhere on the board
/CD7: J18.9, U2.60; also elsewhere on the board
/CLKF: J17.1, U2.17 (I/O/GCK3); also elsewhere on the board
/CP1: J21.3, J28.37, RN1.3 (R2), U1.1 (I/O/GCK3)
/CP2: J21.4, J28.34, U1.2 (M15)
/CP3: J21.5, J28.35, RN1.4 (R3), U1.3 (M17)
/CP5: J21.6, J28.32, U1.5 (M2)
/CP6: J21.7, J28.33, RN1.5 (R4), U1.6 (M5)
/CP7: J21.8, J28.31, RN1.6 (R5), U1.7 (M8)
/CP8: J21.9, J28.29, RN1.7 (R6), U1.8 (M9)
/CP12: J26.1, J28.27, RN1.8 (R7), U1.12 (M11)
/CP13: J26.2, J28.25, RN1.9 (R8), U1.13 (M14)
/CP14: J26.3, U1.14 (M15), U3.4
/CP16: J26.4, U1.16 (M17)
/CP18: J26.5, U1.18 (M16)
/CP19: J26.6, U1.19 (M2)
/CP20: J26.7, U1.20 (M5)
/CP21: J26.8, U1.21 (M8)
/CP22: J24.9, U1.22 (M11)
/CP23: J24.8, U1.23 (M14)
/CP27: J24.7, U1.27 (M15)
/CP28: J24.6, R6.2, U1.28 (M17)
/CP29: J24.5, R7.2, U1.29 (M2)
/CP30: J24.4, JP4.3 (B), U1.30 (M5); also elsewhere on the board
/CP31: J15.6, J24.3, U1.31 (M6), U2.7
/CP32: J15.5, J24.2, U1.32 (M8), U2.6
/CP33: J15.4, J24.1, U1.33 (I/O/GSR), U2.5 (I/O/GTS1)
/CP34: J23.1, JP1.3 (B), U1.34 (I/O/GTS2); also elsewhere on the board
/CP36: J18.8, J23.2, U1.36 (I/O/GTS1), U2.59; also elsewhere on the board
/CP37: J15.7, J23.3, J28.24, U1.37 (M15), U2.8
/CP38: J23.4, J28.26, U1.38 (M17)
/CP39: J23.5, J28.28, U1.39 (M1)
/CP40: J23.6, J28.30, U1.40 (M5)
/CP41: J23.7, J28.40, U1.41 (M6)
/CP42: J23.8, J28.38, U1.42 (M8)
/CP43: J21.1, J28.36, U1.43 (I/O/GCK1)
/CP44: J21.2, J28.39, RN1.2 (R1), U1.44 (I/O/GCK2)
/P9: J15.8, U2.9, U3.10
/P15: J15.13, JP4.2 (C), U2.15 (I/O/GCK1)
/P16: J15.14, JP1.2 (C), U2.16 (I/O/GCK2)
/P18: J17.2, J28.21, U2.18
/P19: J17.3, J28.20, R4.2, U2.19
/P20: J17.4, J28.19, R3.2, U2.20
/P22: J17.5, J28.18, R2.2, U2.22
/P23: J17.6, R1.2, U2.23
/PIN3: J28.3, J34.4
/PIN4: J28.4, J34.3
/PIN5: J28.5, J34.6
/PIN6: J28.6, J34.5
/PIN7: J28.7, J34.8
/PIN8: J28.8, J34.7
/PIN9: J28.9, J34.10
/PIN10: J28.10, J34.9
/PIN11: J28.11, J34.12
/PIN12: J28.12, J34.11
/PIN13: J28.13, J34.14
/PIN14: J28.14, J34.13
/PIN15: J28.15, J34.16
/PIN16: J28.16, J34.15
/TCK: J22.1, U2.30 (TCK)
/TCK2: J25.1, U1.11 (TCK)
/TDI: J22.9, U2.28 (TDI)
/TDI2: J25.9, U1.9 (TDI)
/TDO: J22.3, U2.53 (TDO)
/TDO2: J25.3, U1.24 (TDO)
/TMS: J22.5, U2.29 (TMS)
/TMS2: J25.5, U1.10 (TMS)
/~IORDx: JP2.1 (A); also elsewhere on the board
/~IOWRx: JP3.1 (A); also elsewhere on the board
/~MRDx: JP2.3 (B); also elsewhere on the board
/~MWRx: JP3.3 (B); also elsewhere on the board
GND: C1.2, C2.2, C3.2, C4.2, C8.2, C9.2, C10.2, J22.2, J22.10, J25.2, J25.10, J28.1, J31.1, J31.2, J31.3, J31.4, J34.2, U1.4 (GND), U1.17 (GND), U1.25 (GND), U2.14 (GND), U2.21 (GND), U2.41 (GND), U2.54 (GND), U3.5, U3.7 (GND), U3.9; also elsewhere on the board
unnamed: J6.1, U3.3
unnamed: J7.1, U3.2
unnamed: J19.1, U3.1
unnamed: J28.22, U3.6
unnamed: J28.23, U3.8
unnamed: J29.1, U3.12
unnamed: J32.1, U3.13
unnamed: J33.1, U3.11
unnamed: JP1.1 (A), JP2.2 (C)
unnamed: JP3.2 (C), JP4.1 (A)
