roberto314/Unicomp3/MMU_Board/schematics/MMU_v1/MMU_v1.kicad_pcb

## KiCad design MMU_Board/schematics/MMU_v1/MMU_v1.kicad_pcb (continued)

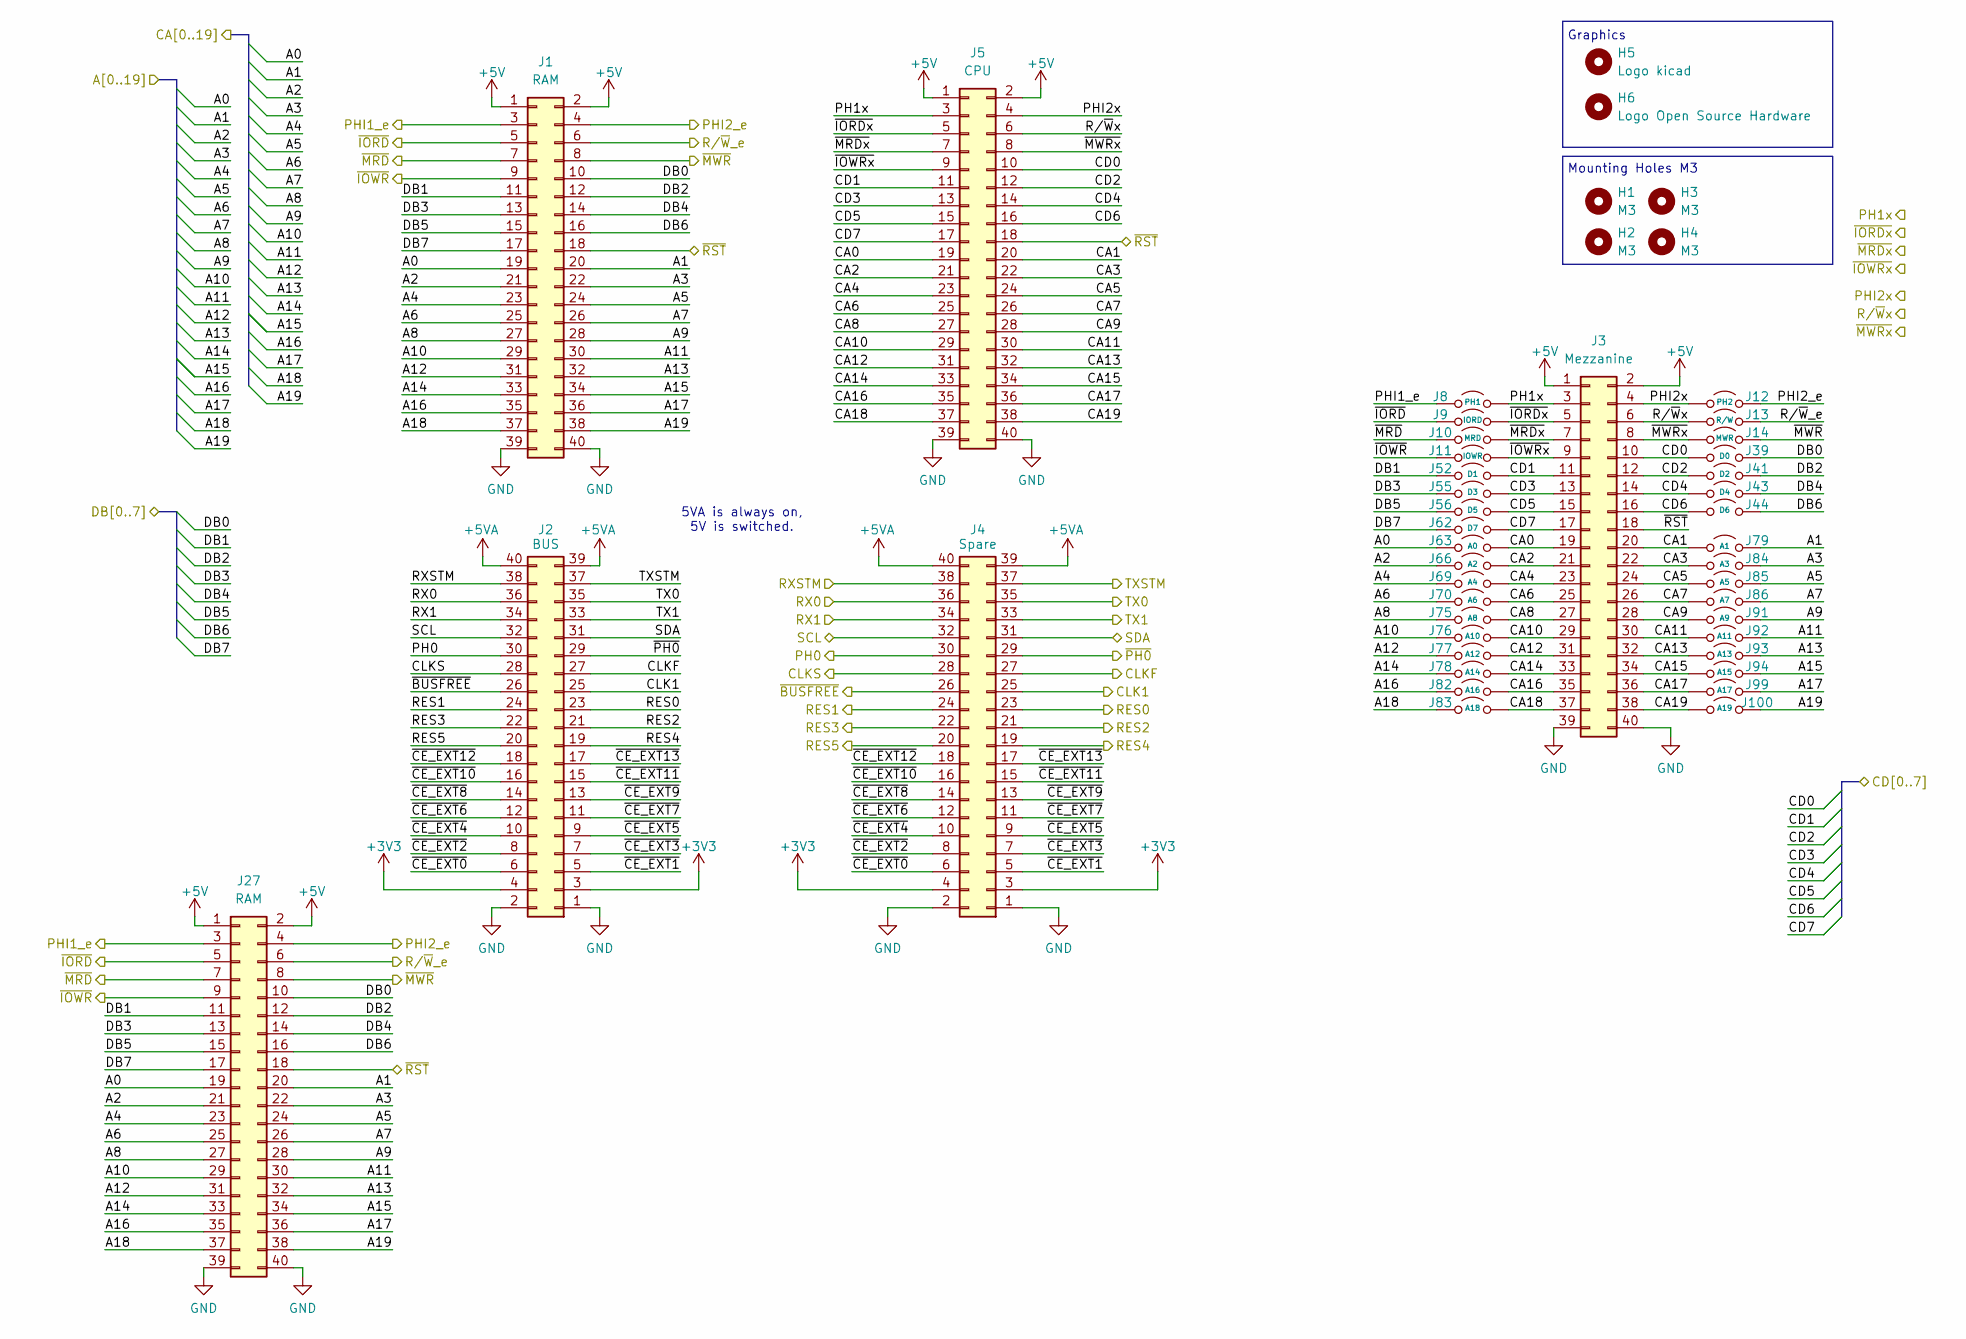
[picture p72: schematic bus.kicad_sch, Unicomp v3 - Bus]

Parts:
H1, H2, H3, H4: M3; MountingHole_3.2mm_M3
H5: Logo kicad; KiCad-Logo2_6mm_SilkScreen
H6: Logo Open Source Hardware; OSHW-Logo2_7.3x6mm_SilkScreen
J1, J27: RAM; PinSocket_2x20_P2.54mm_Vertical
J2: BUS; PinSocket_2x20_P2.54mm_Vertical
J3: Mezzanine; PinSocket_2x20_P2.54mm_Vertical_SMD
J4: Spare; PinSocket_2x20_P2.54mm_Vertical
J5: CPU; PinSocket_2x20_P2.54mm_Vertical
J8: PH1; SolderJumper-2_P1.3mm_Open_RoundedPad1.0x1.5mm
J9: IORD; SolderJumper-2_P1.3mm_Open_RoundedPad1.0x1.5mm
J10: MRD; SolderJumper-2_P1.3mm_Open_RoundedPad1.0x1.5mm
J11: IOWR; SolderJumper-2_P1.3mm_Open_RoundedPad1.0x1.5mm
J12: PH2; SolderJumper-2_P1.3mm_Open_RoundedPad1.0x1.5mm
J13: R/W; SolderJumper-2_P1.3mm_Open_RoundedPad1.0x1.5mm
J14: MWR; SolderJumper-2_P1.3mm_Open_RoundedPad1.0x1.5mm
J39: D0; SolderJumper-2_P1.3mm_Open_RoundedPad1.0x1.5mm
J41: D2; SolderJumper-2_P1.3mm_Open_RoundedPad1.0x1.5mm
J43: D4; SolderJumper-2_P1.3mm_Open_RoundedPad1.0x1.5mm
J44: D6; SolderJumper-2_P1.3mm_Open_RoundedPad1.0x1.5mm
J52: D1; SolderJumper-2_P1.3mm_Open_RoundedPad1.0x1.5mm
J55: D3; SolderJumper-2_P1.3mm_Open_RoundedPad1.0x1.5mm
J56: D5; SolderJumper-2_P1.3mm_Open_RoundedPad1.0x1.5mm
J62: D7; SolderJumper-2_P1.3mm_Open_RoundedPad1.0x1.5mm
J63: A0; SolderJumper-2_P1.3mm_Open_RoundedPad1.0x1.5mm
J66: A2; SolderJumper-2_P1.3mm_Open_RoundedPad1.0x1.5mm
J69: A4; SolderJumper-2_P1.3mm_Open_RoundedPad1.0x1.5mm
J70: A6; SolderJumper-2_P1.3mm_Open_RoundedPad1.0x1.5mm
J75: A8; SolderJumper-2_P1.3mm_Open_RoundedPad1.0x1.5mm
J76: A10; SolderJumper-2_P1.3mm_Open_RoundedPad1.0x1.5mm
J77: A12; SolderJumper-2_P1.3mm_Open_RoundedPad1.0x1.5mm
J78: A14; SolderJumper-2_P1.3mm_Open_RoundedPad1.0x1.5mm
J79: A1; SolderJumper-2_P1.3mm_Open_RoundedPad1.0x1.5mm
J82: A16; SolderJumper-2_P1.3mm_Open_RoundedPad1.0x1.5mm
J83: A18; SolderJumper-2_P1.3mm_Open_RoundedPad1.0x1.5mm
J84: A3; SolderJumper-2_P1.3mm_Open_RoundedPad1.0x1.5mm
J85: A5; SolderJumper-2_P1.3mm_Open_RoundedPad1.0x1.5mm
J86: A7; SolderJumper-2_P1.3mm_Open_RoundedPad1.0x1.5mm
J91: A9; SolderJumper-2_P1.3mm_Open_RoundedPad1.0x1.5mm
J92: A11; SolderJumper-2_P1.3mm_Open_RoundedPad1.0x1.5mm
J93: A13; SolderJumper-2_P1.3mm_Open_RoundedPad1.0x1.5mm
J94: A15; SolderJumper-2_P1.3mm_Open_RoundedPad1.0x1.5mm
J99: A17; SolderJumper-2_P1.3mm_Open_RoundedPad1.0x1.5mm
J100: A19; SolderJumper-2_P1.3mm_Open_RoundedPad1.0x1.5mm

Connections:
+3V3: J2.3, J2.4, J4.3, J4.4; also elsewhere on the board
+5V: J1.1, J1.2, J3.1, J3.2, J5.1, J5.2, J27.1, J27.2; also elsewhere on the board
+5VA: J2.39, J2.40, J4.39, J4.40
/A0: J1.19, J27.19, J63.1 (A); also elsewhere on the board
/A1: J1.20, J27.20, J79.1 (A); also elsewhere on the board
/A2: J1.21, J27.21, J66.1 (A); also elsewhere on the board
/A3: J1.22, J27.22, J84.1 (A); also elsewhere on the board
/A4: J1.23, J27.23, J69.1 (A); also elsewhere on the board
/A5: J1.24, J27.24, J85.1 (A); also elsewhere on the board
/A6: J1.25, J27.25, J70.1 (A); also elsewhere on the board
/A7: J1.26, J27.26, J86.1 (A); also elsewhere on the board
/A8: J1.27, J27.27, J75.1 (A); also elsewhere on the board
/A9: J1.28, J27.28, J91.1 (A); also elsewhere on the board
/A10: J1.29, J27.29, J76.1 (A); also elsewhere on the board
/A11: J1.30, J27.30, J92.1 (A); also elsewhere on the board
/A12: J1.31, J27.31, J77.1 (A); also elsewhere on the board
/A13: J1.32, J27.32, J93.1 (A); also elsewhere on the board
/A14: J1.33, J27.33, J78.1 (A); also elsewhere on the board
/A15: J1.34, J27.34, J94.1 (A); also elsewhere on the board
/A16: J1.35, J27.35, J82.1 (A); also elsewhere on the board
/A17: J1.36, J27.36, J99.1 (A); also elsewhere on the board
/A18: J1.37, J27.37, J83.1 (A); also elsewhere on the board
/A19: J1.38, J27.38, J100.1 (A); also elsewhere on the board
/Bus/~CE_EXT0: J2.6, J4.6
/Bus/~CE_EXT1: J2.5, J4.5
/Bus/~CE_EXT2: J2.8, J4.8
/Bus/~CE_EXT3: J2.7, J4.7
/Bus/~CE_EXT4: J2.10, J4.10
/Bus/~CE_EXT5: J2.9, J4.9
/Bus/~CE_EXT6: J2.12, J4.12
/Bus/~CE_EXT7: J2.11, J4.11
/Bus/~CE_EXT8: J2.14, J4.14
/Bus/~CE_EXT9: J2.13, J4.13
/Bus/~CE_EXT10: J2.16, J4.16
/Bus/~CE_EXT11: J2.15, J4.15
/Bus/~CE_EXT12: J2.18, J4.18
/Bus/~CE_EXT13: J2.17, J4.17
/CA0: J3.19, J5.19, J63.2 (B); also elsewhere on the board
/CA1: J3.20, J5.20, J79.2 (B); also elsewhere on the board
/CA2: J3.21, J5.21, J66.2 (B); also elsewhere on the board
/CA3: J3.22, J5.22, J84.2 (B); also elsewhere on the board
/CA4: J3.23, J5.23, J69.2 (B); also elsewhere on the board
/CA5: J3.24, J5.24, J85.2 (B); also elsewhere on the board
/CA6: J3.25, J5.25, J70.2 (B); also elsewhere on the board
/CA7: J3.26, J5.26, J86.2 (B); also elsewhere on the board
/CA8: J3.27, J5.27, J75.2 (B); also elsewhere on the board
/CA9: J3.28, J5.28, J91.2 (B); also elsewhere on the board
/CA10: J3.29, J5.29, J76.2 (B); also elsewhere on the board
/CA11: J3.30, J5.30, J92.2 (B); also elsewhere on the board
/CA12: J3.31, J5.31, J77.2 (B); also elsewhere on the board
/CA13: J3.32, J5.32, J93.2 (B); also elsewhere on the board
/CA14: J3.33, J5.33, J78.2 (B); also elsewhere on the board
/CA15: J3.34, J5.34, J94.2 (B); also elsewhere on the board
/CA16: J3.35, J5.35, J82.2 (B)
/CA17: J3.36, J5.36, J99.2 (B)
/CA18: J3.37, J5.37, J83.2 (B)
/CA19: J3.38, J5.38, J100.2 (B)
/CD0: J3.10, J5.10, J39.2 (B); also elsewhere on the board
/CD1: J3.11, J5.11, J52.2 (B); also elsewhere on the board
/CD2: J3.12, J5.12, J41.2 (B); also elsewhere on the board
/CD3: J3.13, J5.13, J55.2 (B); also elsewhere on the board
/CD4: J3.14, J5.14, J43.2 (B); also elsewhere on the board
/CD5: J3.15, J5.15, J56.2 (B); also elsewhere on the board
/CD6: J3.16, J5.16, J44.2 (B); also elsewhere on the board
/CD7: J3.17, J5.17, J62.2 (B); also elsewhere on the board
/CLK1: J2.25, J4.25
/CLKF: J2.27, J4.27; also elsewhere on the board
/CLKS: J2.28, J4.28
/CP30: J3.4, J5.4, J12.2 (B); also elsewhere on the board
/CP34: J3.6, J5.6, J13.2 (B); also elsewhere on the board
/CP36: J1.18, J3.18, J5.18, J27.18; also elsewhere on the board
/DB0: J1.10, J27.10, J39.1 (A)
/DB1: J1.11, J27.11, J52.1 (A)
/DB2: J1.12, J27.12, J41.1 (A)
/DB3: J1.13, J27.13, J55.1 (A)
/DB4: J1.14, J27.14, J43.1 (A)
/DB5: J1.15, J27.15, J56.1 (A)
/DB6: J1.16, J27.16, J44.1 (A)
/DB7: J1.17, J27.17, J62.1 (A)
/PH0: J2.30, J4.30
/PH1x: J3.3, J5.3, J8.2 (B)
/PHI1_e: J1.3, J8.1 (A), J27.3
/PHI2_e: J1.4, J12.1 (A), J27.4
/RES0: J2.23, J4.23
/RES1: J2.24, J4.24
/RES2: J2.21, J4.21
/RES3: J2.22, J4.22
/RES4: J2.19, J4.19
/RES5: J2.20, J4.20
/RX0: J2.36, J4.36
/RX1: J2.34, J4.34
/RXSTM: J2.38, J4.38
/R/~W_e: J1.6, J13.1 (A), J27.6
/SCL: J2.32, J4.32
/SDA: J2.31, J4.31
/TX0: J2.35, J4.35
/TX1: J2.33, J4.33
/TXSTM: J2.37, J4.37
/~BUSFREE: J2.26, J4.26
/~IORDx: J3.5, J5.5, J9.2 (B); also elsewhere on the board
/~IORD: J1.5, J9.1 (A), J27.5
/~IOWRx: J3.9, J5.9, J11.2 (B); also elsewhere on the board
/~IOWR: J1.9, J11.1 (A), J27.9
/~MRDx: J3.7, J5.7, J10.2 (B); also elsewhere on the board
/~MRD: J1.7, J10.1 (A), J27.7
/~MWRx: J3.8, J5.8, J14.2 (B); also elsewhere on the board
/~MWR: J1.8, J14.1 (A), J27.8
/~PH0: J2.29, J4.29
GND: J1.39, J1.40, J2.1, J2.2, J3.39, J3.40, J4.1, J4.2, J5.39, J5.40, J27.39, J27.40; also elsewhere on the board

Notes on the sheet:
Graphics
5VA is always on, 5V is switched.
Mounting Holes M3

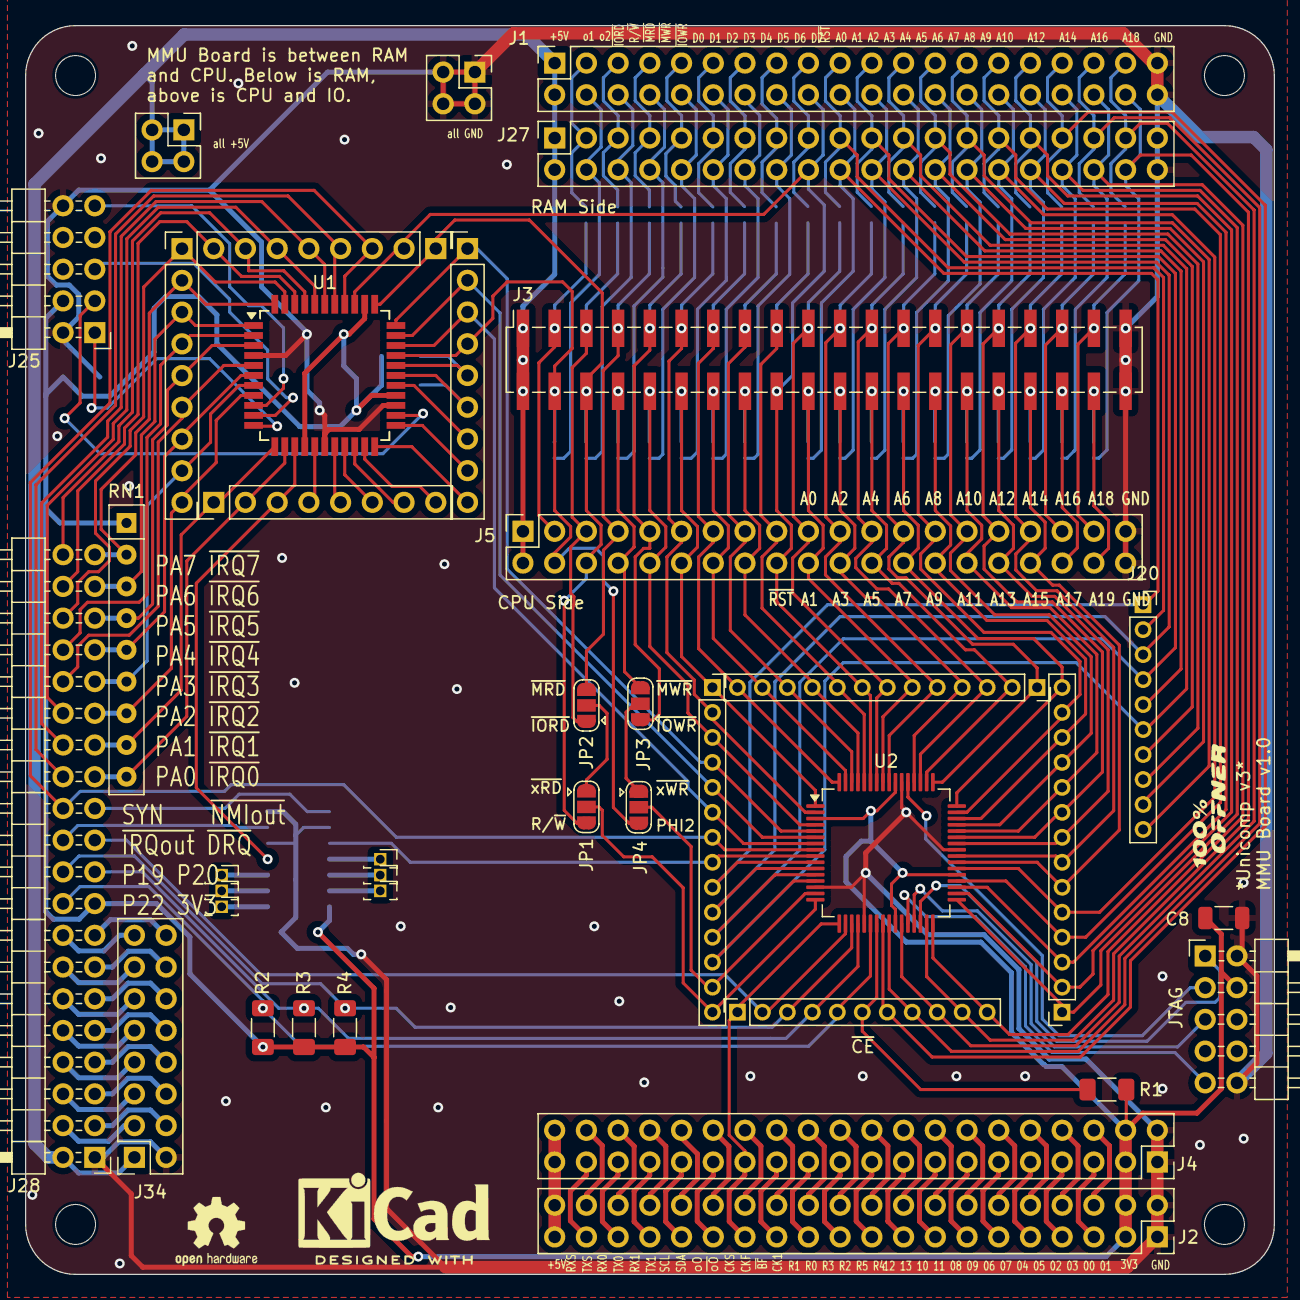
[picture p73: board MMU_v1.kicad_pcb from above]

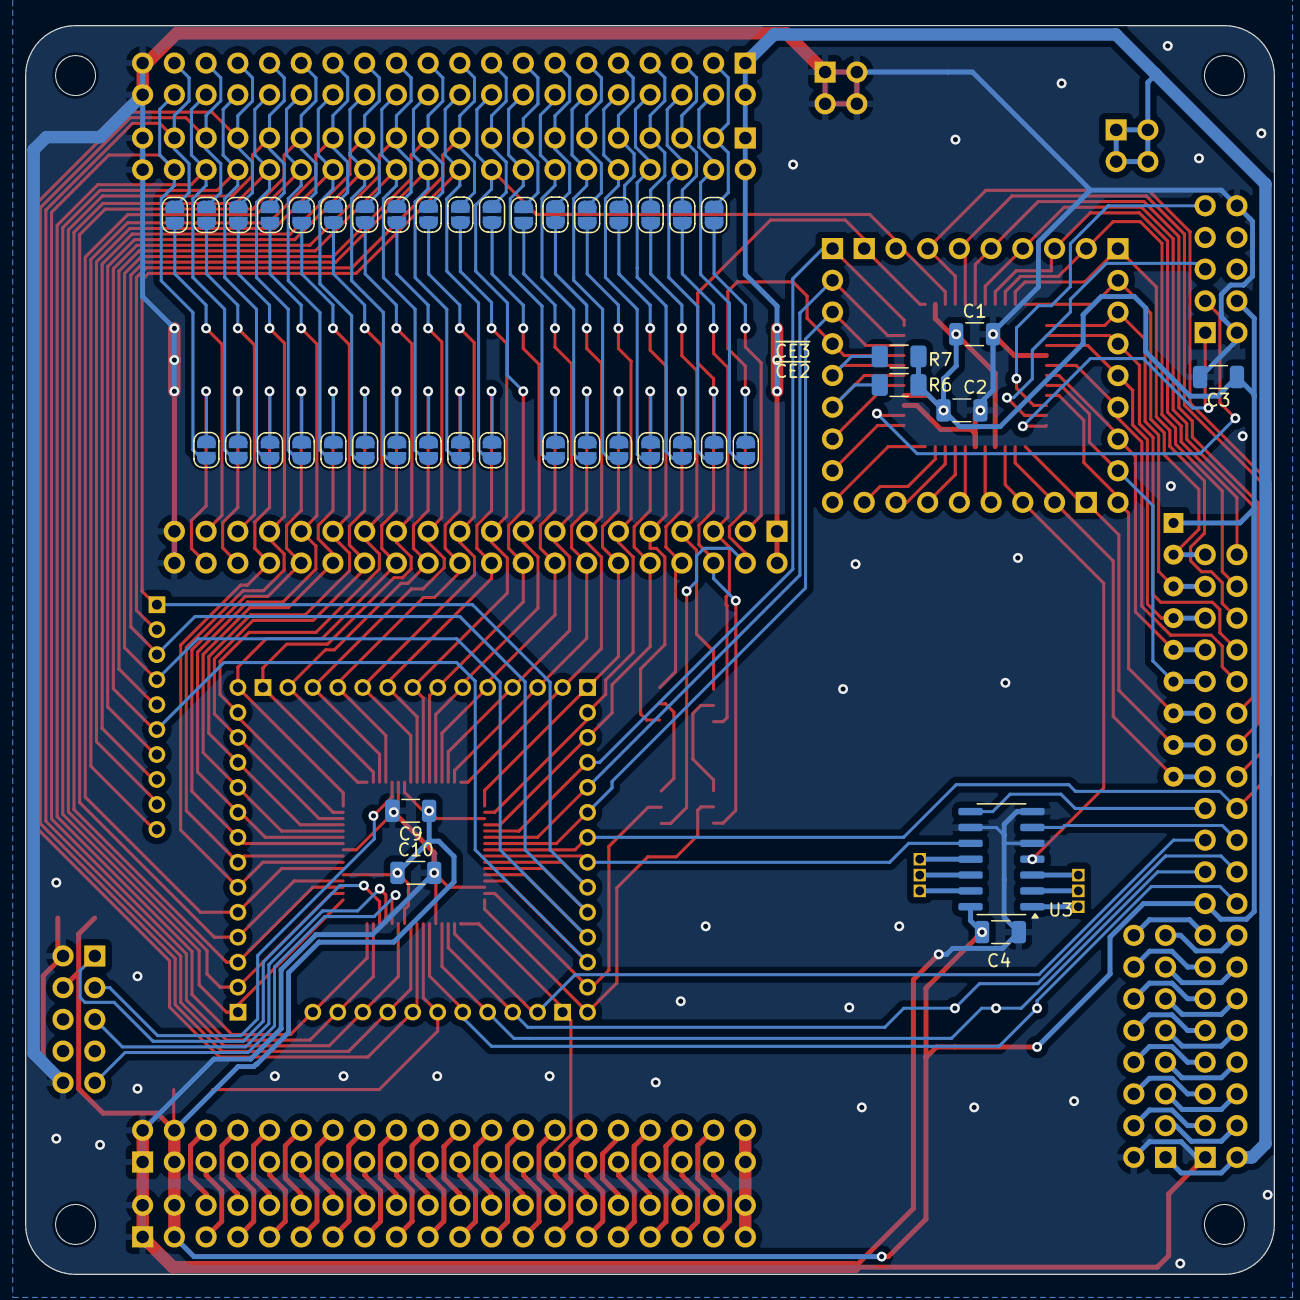
[picture p74: board MMU_v1.kicad_pcb from below]

Board: 2 copper layers, 100.0 x 100.0 mm, 89 parts (44 on the bottom side), 180 nets.
