roberto314/Unicomp3/ParallelBoards/MOS_Parallel_Board/MOS_Parallel_v1.0/MP_Board.kicad_pcb

## KiCad design ParallelBoards/MOS_Parallel_Board/MOS_Parallel_v1.0/MP_Board.kicad_pcb (2024-10-24)

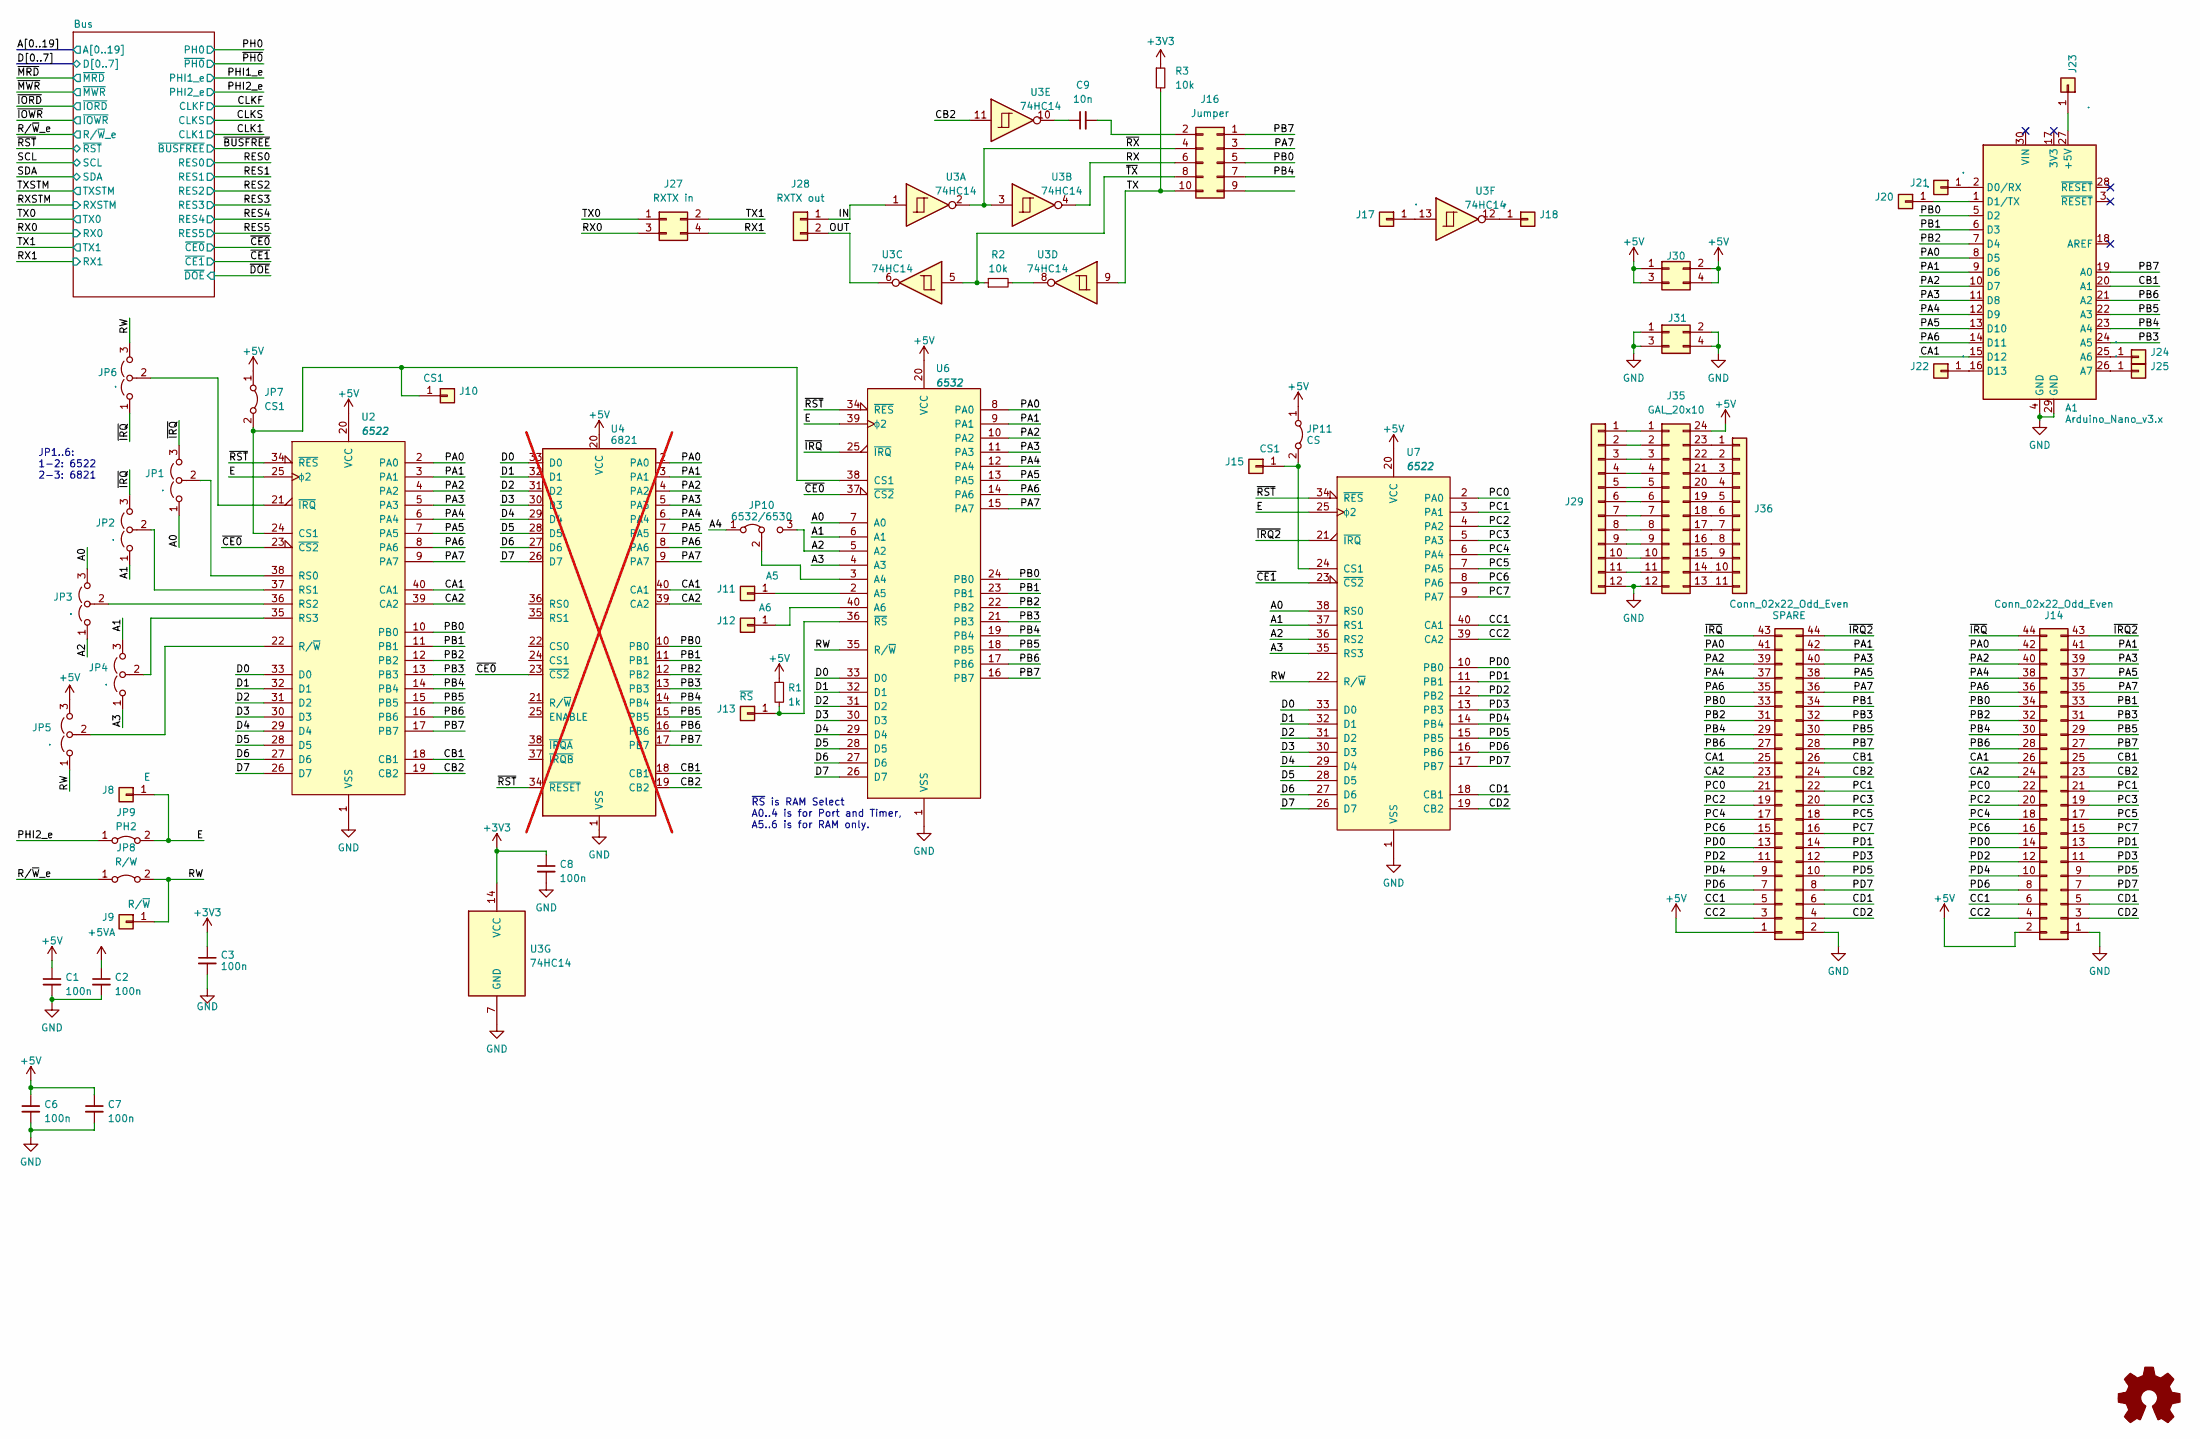
[picture p75: schematic MP_Board.kicad_sch, Unicomp v3 - MOS Parallel Board]

Parts:
A1: Arduino_Nano_v3.x; Arduino_Nano
C1, C2, C3, C6, C7, C8: 100n; C_1206_3216Metric
C9: 10n; C_1206_3216Metric
J8: E; PinHeader_1x01_P2.00mm_Vertical
J9: R/~{W}; PinHeader_1x01_P2.00mm_Vertical
J10, J15: CS1; PinHeader_1x01_P2.00mm_Vertical
J11: A5; PinHeader_1x01_P2.00mm_Vertical
J12: A6; PinHeader_1x01_P2.00mm_Vertical
J13: ~{RS}; PinHeader_1x01_P2.00mm_Vertical
J14: Conn_02x22_Odd_Even; PinHeader_2x22_P2.54mm_Horizontal
J16: Jumper; PinSocket_2x05_P2.54mm_Vertical
J17, J18, J20, J21, J22, J23, J24, J25: .; PinHeader_1x01_P2.00mm_Vertical
J27: RXTX in; PinSocket_2x02_P2.54mm_Vertical
J28: RXTX out; PinSocket_1x02_P2.54mm_Vertical
J29: Conn_01x12; PinSocket_1x12_P2.54mm_Vertical
J30, J31: Conn_02x02_Odd_Even; PinSocket_2x02_P2.54mm_Vertical
J35: GAL_20x10; DIP-24_W7.62mm
J36: Conn_01x11; PinSocket_1x11_P2.54mm_Vertical
JP1, JP2, JP3, JP4, JP5, JP6: .; PinHeader_1x03_P2.54mm_Vertical
JP7: CS1; SolderJumper-2_P1.3mm_Bridged_RoundedPad1.0x1.5mm
JP8: R/W; SolderJumper-2_P1.3mm_Bridged_RoundedPad1.0x1.5mm
JP9: PH2; SolderJumper-2_P1.3mm_Bridged_RoundedPad1.0x1.5mm
JP10: 6532/6530; SolderJumper-3_P1.3mm_Bridged12_Pad1.0x1.5mm_NumberLabels
JP11: CS; SolderJumper-2_P1.3mm_Bridged_RoundedPad1.0x1.5mm
R1: 1k; R_1206_3216Metric_Pad1.30x1.75mm_HandSolder
R2, R3: 10k; R_1206_3216Metric_Pad1.30x1.75mm_HandSolder
SPARE: Conn_02x22_Odd_Even; PinSocket_2x22_P2.54mm_Vertical
U2, U7: 6522; DIP-40_W15.24mm_Socket
U3: 74HC14; SOIC-14_3.9x8.7mm_P1.27mm
U4: 6821; DIP-40_W15.24mm; not fitted
U6: 6532; DIP-40_W15.24mm_Socket

Connections:
+3V3: C3.1, C8.1, R3.1, U3.14 (VCC); also elsewhere on the board
+5V: C1.1, C6.1, C7.1, J14.2, J30.1, J30.2, J30.3, J30.4, J35.24, JP5.3 (B), JP7.1 (A), JP11.1 (A), R1.1, SPARE.1, U2.20 (VCC), U4.20 (VCC), U6.20 (VCC), U7.20 (VCC); also elsewhere on the board
+5VA: C2.1; also elsewhere on the board
/A0: JP1.1 (A), JP3.3 (B), U6.7 (A0), U7.38 (RS0); also elsewhere on the board
/A1: JP2.1 (A), JP4.3 (B), U6.6 (A1), U7.37 (RS1); also elsewhere on the board
/A2: JP3.1 (A), JP10.3 (B), U6.5 (A2), U7.36 (RS2); also elsewhere on the board
/A3: JP4.1 (A), U6.4 (A3), U7.35 (RS3); also elsewhere on the board
/A4: JP10.1 (A); also elsewhere on the board
/CA1: A1.15 (D12), J14.26, SPARE.25, U2.40 (CA1), U4.40 (CA1); also elsewhere on the board
/CA2: J14.24, SPARE.23, U2.39 (CA2), U4.39 (CA2); also elsewhere on the board
/CB1: A1.20 (A1), J14.25, SPARE.26, U2.18 (CB1), U4.18 (CB1); also elsewhere on the board
/CB2: J14.23, SPARE.24, U2.19 (CB2), U3.11, U4.19 (CB2); also elsewhere on the board
/CC1: J14.6, SPARE.5, U7.40 (CA1); also elsewhere on the board
/CC2: J14.4, SPARE.3, U7.39 (CA2); also elsewhere on the board
/CD1: J14.5, SPARE.6, U7.18 (CB1); also elsewhere on the board
/CD2: J14.3, SPARE.4, U7.19 (CB2); also elsewhere on the board
/D0: U2.33 (D0), U4.33 (D0), U6.33 (D0), U7.33 (D0); also elsewhere on the board
/D1: U2.32 (D1), U4.32 (D1), U6.32 (D1), U7.32 (D1); also elsewhere on the board
/D2: U2.31 (D2), U4.31 (D2), U6.31 (D2), U7.31 (D2); also elsewhere on the board
/D3: U2.30 (D3), U4.30 (D3), U6.30 (D3), U7.30 (D3); also elsewhere on the board
/D4: U2.29 (D4), U4.29 (D4), U6.29 (D4), U7.29 (D4); also elsewhere on the board
/D5: U2.28 (D5), U4.28 (D5), U6.28 (D5), U7.28 (D5); also elsewhere on the board
/D6: U2.27 (D6), U4.27 (D6), U6.27 (D6), U7.27 (D6); also elsewhere on the board
/D7: U2.26 (D7), U4.26 (D7), U6.26 (D7), U7.26 (D7); also elsewhere on the board
/E: J8.1, JP9.2 (B), U2.25 (ϕ2), U6.39 (ϕ2), U7.25 (ϕ2)
/IN: J28.1, U3.1
/OUT: J28.2, U3.6
/PA0: A1.8 (D5), J14.42, SPARE.41, U2.2 (PA0), U4.2 (PA0), U6.8 (PA0); also elsewhere on the board
/PA1: A1.9 (D6), J14.41, SPARE.42, U2.3 (PA1), U4.3 (PA1), U6.9 (PA1); also elsewhere on the board
/PA2: A1.10 (D7), J14.40, SPARE.39, U2.4 (PA2), U4.4 (PA2), U6.10 (PA2); also elsewhere on the board
/PA3: A1.11 (D8), J14.39, SPARE.40, U2.5 (PA3), U4.5 (PA3), U6.11 (PA3); also elsewhere on the board
/PA4: A1.12 (D9), J14.38, SPARE.37, U2.6 (PA4), U4.6 (PA4), U6.12 (PA4); also elsewhere on the board
/PA5: A1.13 (D10), J14.37, SPARE.38, U2.7 (PA5), U4.7 (PA5), U6.13 (PA5); also elsewhere on the board
/PA6: A1.14 (D11), J14.36, SPARE.35, U2.8 (PA6), U4.8 (PA6), U6.14 (PA6); also elsewhere on the board
/PA7: J14.35, J16.3, SPARE.36, U2.9 (PA7), U4.9 (PA7), U6.15 (PA7); also elsewhere on the board
/PB0: A1.5 (D2), J14.34, J16.5, SPARE.33, U2.10 (PB0), U4.10 (PB0), U6.24 (PB0); also elsewhere on the board
/PB1: A1.6 (D3), J14.33, SPARE.34, U2.11 (PB1), U4.11 (PB1), U6.23 (PB1); also elsewhere on the board
/PB2: A1.7 (D4), J14.32, SPARE.31, U2.12 (PB2), U4.12 (PB2), U6.22 (PB2); also elsewhere on the board
/PB3: A1.24 (A5), J14.31, SPARE.32, U2.13 (PB3), U4.13 (PB3), U6.21 (PB3); also elsewhere on the board
/PB4: A1.23 (A4), J14.30, J16.7, SPARE.29, U2.14 (PB4), U4.14 (PB4), U6.19 (PB4); also elsewhere on the board
/PB5: A1.22 (A3), J14.29, SPARE.30, U2.15 (PB5), U4.15 (PB5), U6.18 (PB5); also elsewhere on the board
/PB6: A1.21 (A2), J14.28, SPARE.27, U2.16 (PB6), U4.16 (PB6), U6.17 (PB6); also elsewhere on the board
/PB7: A1.19 (A0), J14.27, J16.1, SPARE.28, U2.17 (PB7), U4.17 (PB7), U6.16 (PB7); also elsewhere on the board
/PC0: J14.22, SPARE.21, U7.2 (PA0); also elsewhere on the board
/PC1: J14.21, SPARE.22, U7.3 (PA1); also elsewhere on the board
/PC2: J14.20, SPARE.19, U7.4 (PA2); also elsewhere on the board
/PC3: J14.19, SPARE.20, U7.5 (PA3); also elsewhere on the board
/PC4: J14.18, SPARE.17, U7.6 (PA4); also elsewhere on the board
/PC5: J14.17, SPARE.18, U7.7 (PA5); also elsewhere on the board
/PC6: J14.16, SPARE.15, U7.8 (PA6); also elsewhere on the board
/PC7: J14.15, SPARE.16, U7.9 (PA7); also elsewhere on the board
/PD0: J14.14, SPARE.13, U7.10 (PB0); also elsewhere on the board
/PD1: J14.13, SPARE.14, U7.11 (PB1); also elsewhere on the board
/PD2: J14.12, SPARE.11, U7.12 (PB2); also elsewhere on the board
/PD3: J14.11, SPARE.12, U7.13 (PB3); also elsewhere on the board
/PD4: J14.10, SPARE.9, U7.14 (PB4); also elsewhere on the board
/PD5: J14.9, SPARE.10, U7.15 (PB5); also elsewhere on the board
/PD6: J14.8, SPARE.7, U7.16 (PB6); also elsewhere on the board
/PD7: J14.7, SPARE.8, U7.17 (PB7); also elsewhere on the board
/PHI2_e: JP9.1 (A); also elsewhere on the board
/RW: J9.1, JP5.1 (A), JP6.3 (B), JP8.2 (B), U6.35 (R/~W), U7.22 (R/~W)
/RX: J16.6, U3.4
/RX0: J27.3; also elsewhere on the board
/RX1: J27.4; also elsewhere on the board
/R/~W_e: JP8.1 (A); also elsewhere on the board
/TX: J16.10, R3.2, U3.9
/TX0: J27.1; also elsewhere on the board
/TX1: J27.2; also elsewhere on the board
/~CE0: U2.23 (~CS2), U4.23 (~CS2), U6.37 (~CS2); also elsewhere on the board
/~CE1: U7.23 (~CS2); also elsewhere on the board
/~IRQ2: J14.43, SPARE.44, U7.21 (~IRQ); also elsewhere on the board
/~IRQ: J14.44, JP1.3 (B), JP2.3 (B), JP6.1 (A), SPARE.43, U6.25 (~IRQ); also elsewhere on the board
/~RST: U2.34 (~RES), U4.34 (~RESET), U6.34 (~RES), U7.34 (~RES); also elsewhere on the board
/~RX: J16.4, U3.2, U3.3
/~TX: J16.8, R2.1, U3.5
GND: A1.4 (GND), A1.29 (GND), C1.2, C2.2, C3.2, C6.2, C7.2, C8.2, J14.1, J29.12, J31.1, J31.2, J31.3, J31.4, J35.12, SPARE.2, U2.1 (VSS), U3.7 (GND), U4.1 (VSS), U6.1 (VSS), U7.1 (VSS); also elsewhere on the board
unnamed: A1.27 (+5V), J23.1
unnamed: A1.25 (A6), J24.1
unnamed: A1.26 (A7), J25.1
unnamed: A1.2 (D0/RX), J21.1
unnamed: A1.1 (D1/TX), J20.1
unnamed: A1.16 (D13), J22.1
unnamed: C9.1, U3.10
unnamed: J10.1, JP7.2 (B), U2.24 (CS1), U6.38 (CS1)
unnamed: J11.1, U6.2 (A5)
unnamed: J12.1, U6.40 (A6)
unnamed: J13.1, R1.2, U6.36 (~RS)
unnamed: J15.1, JP11.2 (B), U7.24 (CS1)
unnamed: C9.2, J16.2
unnamed: J17.1, U3.13
unnamed: J18.1, U3.12
unnamed: J29.1, J35.1
unnamed: J29.2, J35.2
unnamed: J29.3, J35.3
unnamed: J29.4, J35.4
unnamed: J29.5, J35.5
unnamed: J29.6, J35.6
unnamed: J29.7, J35.7
unnamed: J29.8, J35.8
unnamed: J29.9, J35.9
unnamed: J29.10, J35.10
unnamed: J29.11, J35.11
unnamed: J35.13, J36.11
unnamed: J35.14, J36.10
unnamed: J35.15, J36.9
unnamed: J35.16, J36.8
unnamed: J35.17, J36.7
unnamed: J35.18, J36.6
unnamed: J35.19, J36.5
unnamed: J35.20, J36.4
unnamed: J35.21, J36.3
unnamed: J35.22, J36.2
unnamed: J35.23, J36.1
unnamed: JP1.2 (C), U2.38 (RS0)
unnamed: JP2.2 (C), U2.37 (RS1)
unnamed: JP3.2 (C), U2.36 (RS2)
unnamed: JP4.2 (C), U2.35 (RS3)
unnamed: JP5.2 (C), U2.22 (R/~W)
unnamed: JP6.2 (C), U2.21 (~IRQ)
unnamed: JP10.2 (C), U6.3 (A4)
unnamed: R2.2, U3.8

Notes on the sheet:
~{RS} is RAM Select A0..4 is for Port and Timer, A5..6 is for RAM only.
JP1..6: 1-2: 6522 2-3: 6821
