roberto314/Unicomp3/ParallelBoards/MOS_Parallel_Board/MOS_Parallel_v1.0/MP_Board.kicad_pcb

## KiCad design ParallelBoards/MOS_Parallel_Board/MOS_Parallel_v1.0/MP_Board.kicad_pcb (continued)

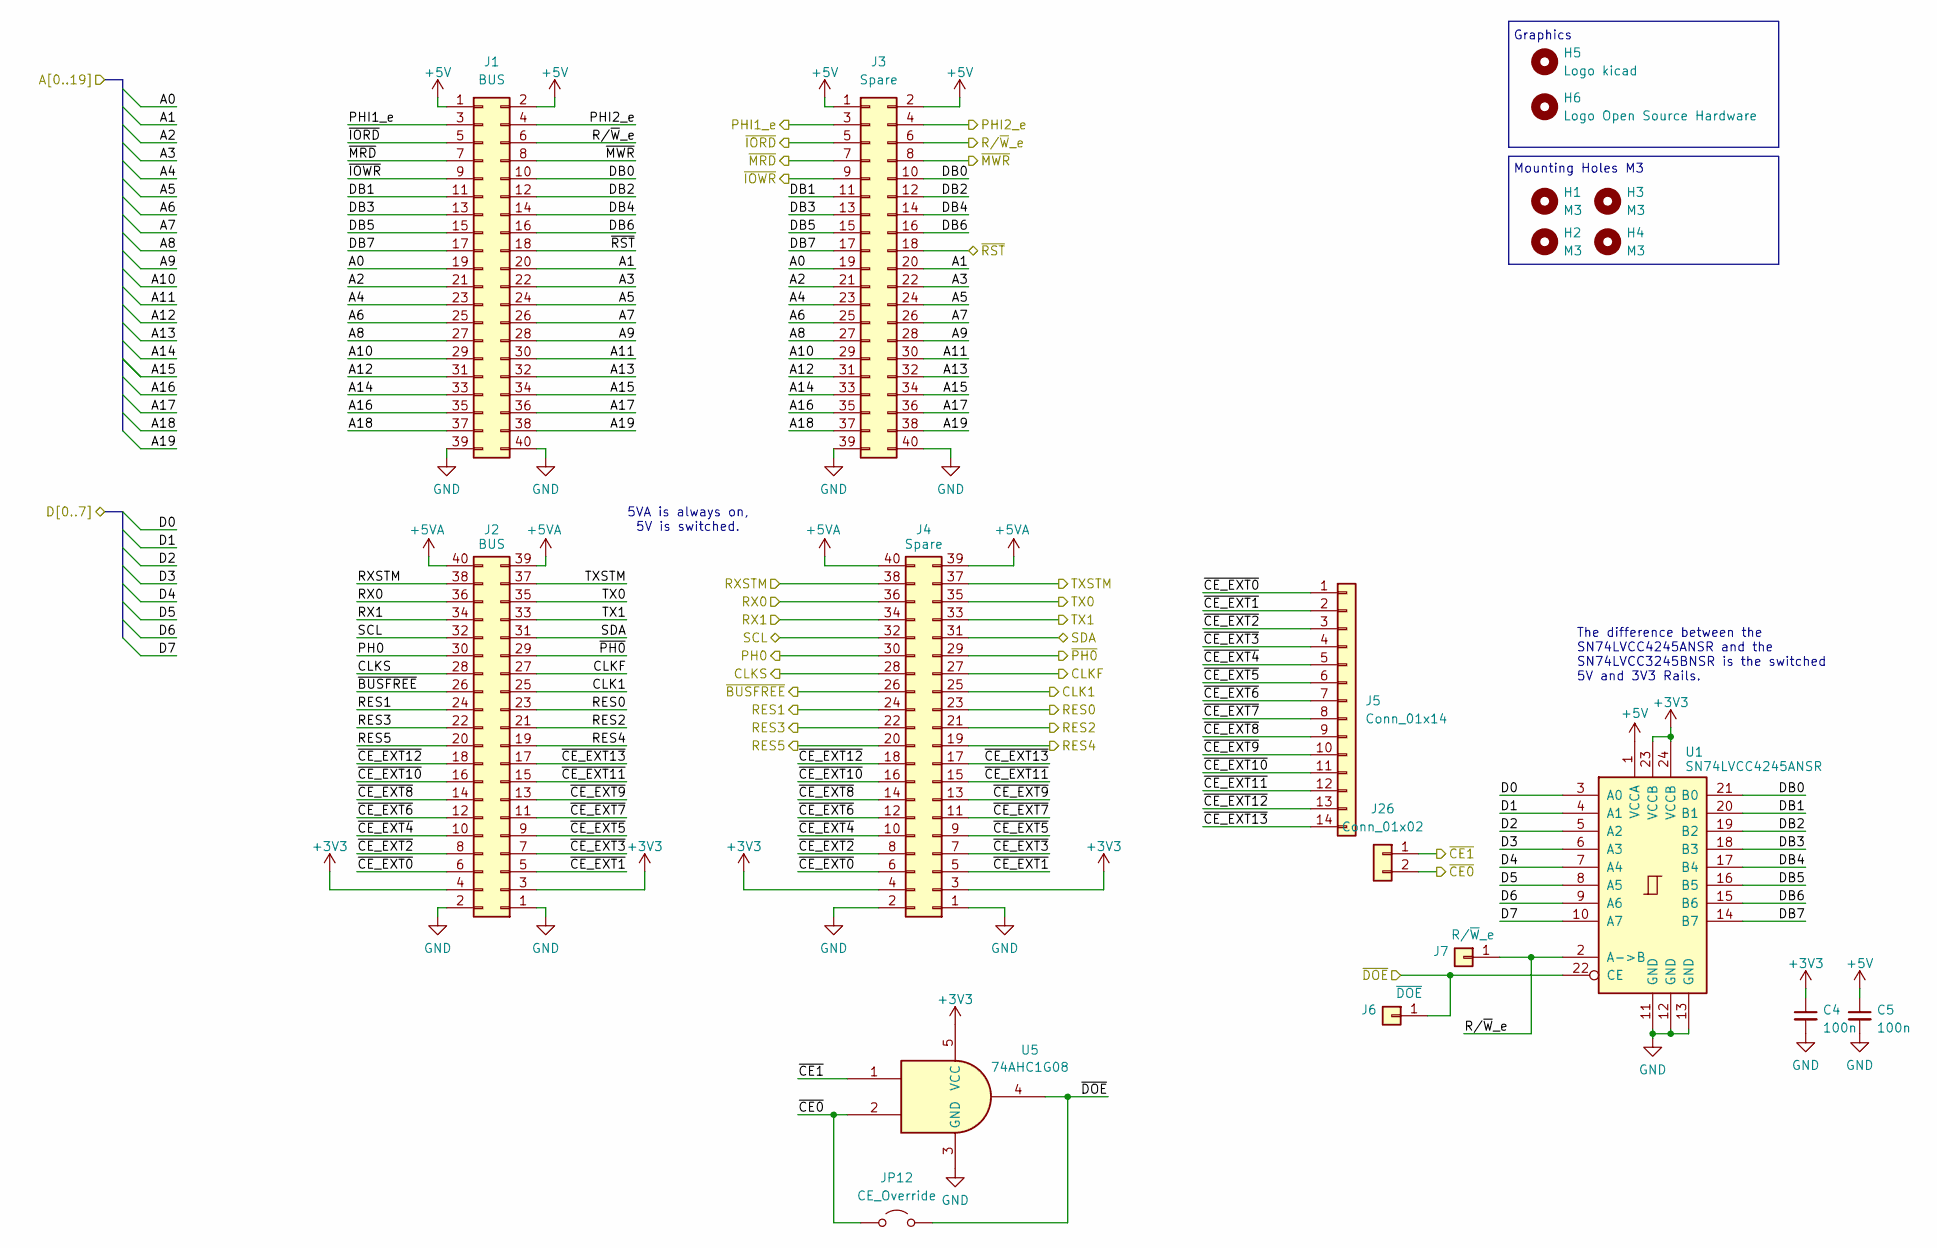
[picture p76: schematic bus.kicad_sch, Unicomp v3 - Bus]

Parts:
C4, C5: 100n; C_1206_3216Metric
H1, H2, H3, H4: M3; MountingHole_3.2mm_M3
H5: Logo kicad; KiCad-Logo2_6mm_SilkScreen
H6: Logo Open Source Hardware; OSHW-Logo2_7.3x6mm_SilkScreen
J1, J2: BUS; PinSocket_2x20_P2.54mm_Vertical
J3, J4: Spare; PinSocket_2x20_P2.54mm_Vertical
J5: Conn_01x14; PinSocket_1x14_P2.54mm_Vertical
J6: ~{DOE}; PinHeader_1x01_P2.00mm_Vertical
J7: R/~{W}_e; PinHeader_1x01_P2.00mm_Vertical
J26: Conn_01x02; PinSocket_1x02_P2.54mm_Vertical
JP12: CE_Override; SolderJumper-2_P1.3mm_Open_RoundedPad1.0x1.5mm
U1: SN74LVCC4245ANSR; SO-24_5.3x15mm_P1.27mm
U5: 74AHC1G08; SOT-23-5_HandSoldering

Connections:
+3V3: C4.1, J2.3, J2.4, J4.3, J4.4, U1.23 (VCCB), U1.24 (VCCB), U5.5 (VCC); also elsewhere on the board
+5V: C5.1, J1.1, J1.2, J3.1, J3.2, U1.1 (VCCA); also elsewhere on the board
+5VA: J2.39, J2.40, J4.39, J4.40; also elsewhere on the board
/A0: J1.19, J3.19; also elsewhere on the board
/A1: J1.20, J3.20; also elsewhere on the board
/A2: J1.21, J3.21; also elsewhere on the board
/A3: J1.22, J3.22; also elsewhere on the board
/A4: J1.23, J3.23; also elsewhere on the board
/A5: J1.24, J3.24
/A6: J1.25, J3.25
/A7: J1.26, J3.26
/A8: J1.27, J3.27
/A9: J1.28, J3.28
/A10: J1.29, J3.29
/A11: J1.30, J3.30
/A12: J1.31, J3.31
/A13: J1.32, J3.32
/A14: J1.33, J3.33
/A15: J1.34, J3.34
/A16: J1.35, J3.35
/A17: J1.36, J3.36
/A18: J1.37, J3.37
/A19: J1.38, J3.38
/Bus/DB0: J1.10, J3.10, U1.21 (B0)
/Bus/DB1: J1.11, J3.11, U1.20 (B1)
/Bus/DB2: J1.12, J3.12, U1.19 (B2)
/Bus/DB3: J1.13, J3.13, U1.18 (B3)
/Bus/DB4: J1.14, J3.14, U1.17 (B4)
/Bus/DB5: J1.15, J3.15, U1.16 (B5)
/Bus/DB6: J1.16, J3.16, U1.15 (B6)
/Bus/DB7: J1.17, J3.17, U1.14 (B7)
/Bus/~CE_EXT0: J2.6, J4.6, J5.1
/Bus/~CE_EXT1: J2.5, J4.5, J5.2
/Bus/~CE_EXT2: J2.8, J4.8, J5.3
/Bus/~CE_EXT3: J2.7, J4.7, J5.4
/Bus/~CE_EXT4: J2.10, J4.10, J5.5
/Bus/~CE_EXT5: J2.9, J4.9, J5.6
/Bus/~CE_EXT6: J2.12, J4.12, J5.7
/Bus/~CE_EXT7: J2.11, J4.11, J5.8
/Bus/~CE_EXT8: J2.14, J4.14, J5.9
/Bus/~CE_EXT9: J2.13, J4.13, J5.10
/Bus/~CE_EXT10: J2.16, J4.16, J5.11
/Bus/~CE_EXT11: J2.15, J4.15, J5.12
/Bus/~CE_EXT12: J2.18, J4.18, J5.13
/Bus/~CE_EXT13: J2.17, J4.17, J5.14
/CLK1: J2.25, J4.25
/CLKF: J2.27, J4.27
/CLKS: J2.28, J4.28
/D0: U1.3 (A0); also elsewhere on the board
/D1: U1.4 (A1); also elsewhere on the board
/D2: U1.5 (A2); also elsewhere on the board
/D3: U1.6 (A3); also elsewhere on the board
/D4: U1.7 (A4); also elsewhere on the board
/D5: U1.8 (A5); also elsewhere on the board
/D6: U1.9 (A6); also elsewhere on the board
/D7: U1.10 (A7); also elsewhere on the board
/PH0: J2.30, J4.30
/PHI1_e: J1.3, J3.3
/PHI2_e: J1.4, J3.4; also elsewhere on the board
/RES0: J2.23, J4.23
/RES1: J2.24, J4.24
/RES2: J2.21, J4.21
/RES3: J2.22, J4.22
/RES4: J2.19, J4.19
/RES5: J2.20, J4.20
/RX0: J2.36, J4.36; also elsewhere on the board
/RX1: J2.34, J4.34; also elsewhere on the board
/RXSTM: J2.38, J4.38
/R/~W_e: J1.6, J3.6, J7.1, U1.2 (A->B); also elsewhere on the board
/SCL: J2.32, J4.32
/SDA: J2.31, J4.31
/TX0: J2.35, J4.35; also elsewhere on the board
/TX1: J2.33, J4.33; also elsewhere on the board
/TXSTM: J2.37, J4.37
/~BUSFREE: J2.26, J4.26
/~CE0: J26.2, JP12.1 (A), U5.2; also elsewhere on the board
/~CE1: J26.1, U5.1; also elsewhere on the board
/~DOE: J6.1, JP12.2 (B), U1.22 (CE), U5.4
/~IORD: J1.5, J3.5
/~IOWR: J1.9, J3.9
/~MRD: J1.7, J3.7
/~MWR: J1.8, J3.8
/~PH0: J2.29, J4.29
/~RST: J1.18, J3.18; also elsewhere on the board
GND: C4.2, C5.2, J1.39, J1.40, J2.1, J2.2, J3.39, J3.40, J4.1, J4.2, U1.11 (GND), U1.12 (GND), U1.13 (GND), U5.3 (GND); also elsewhere on the board

Notes on the sheet:
Graphics
5VA is always on, 5V is switched.
Mounting Holes M3
The difference between the SN74LVCC4245ANSR and the SN74LVCC3245BNSR is the switched 5V and 3V3 Rails.

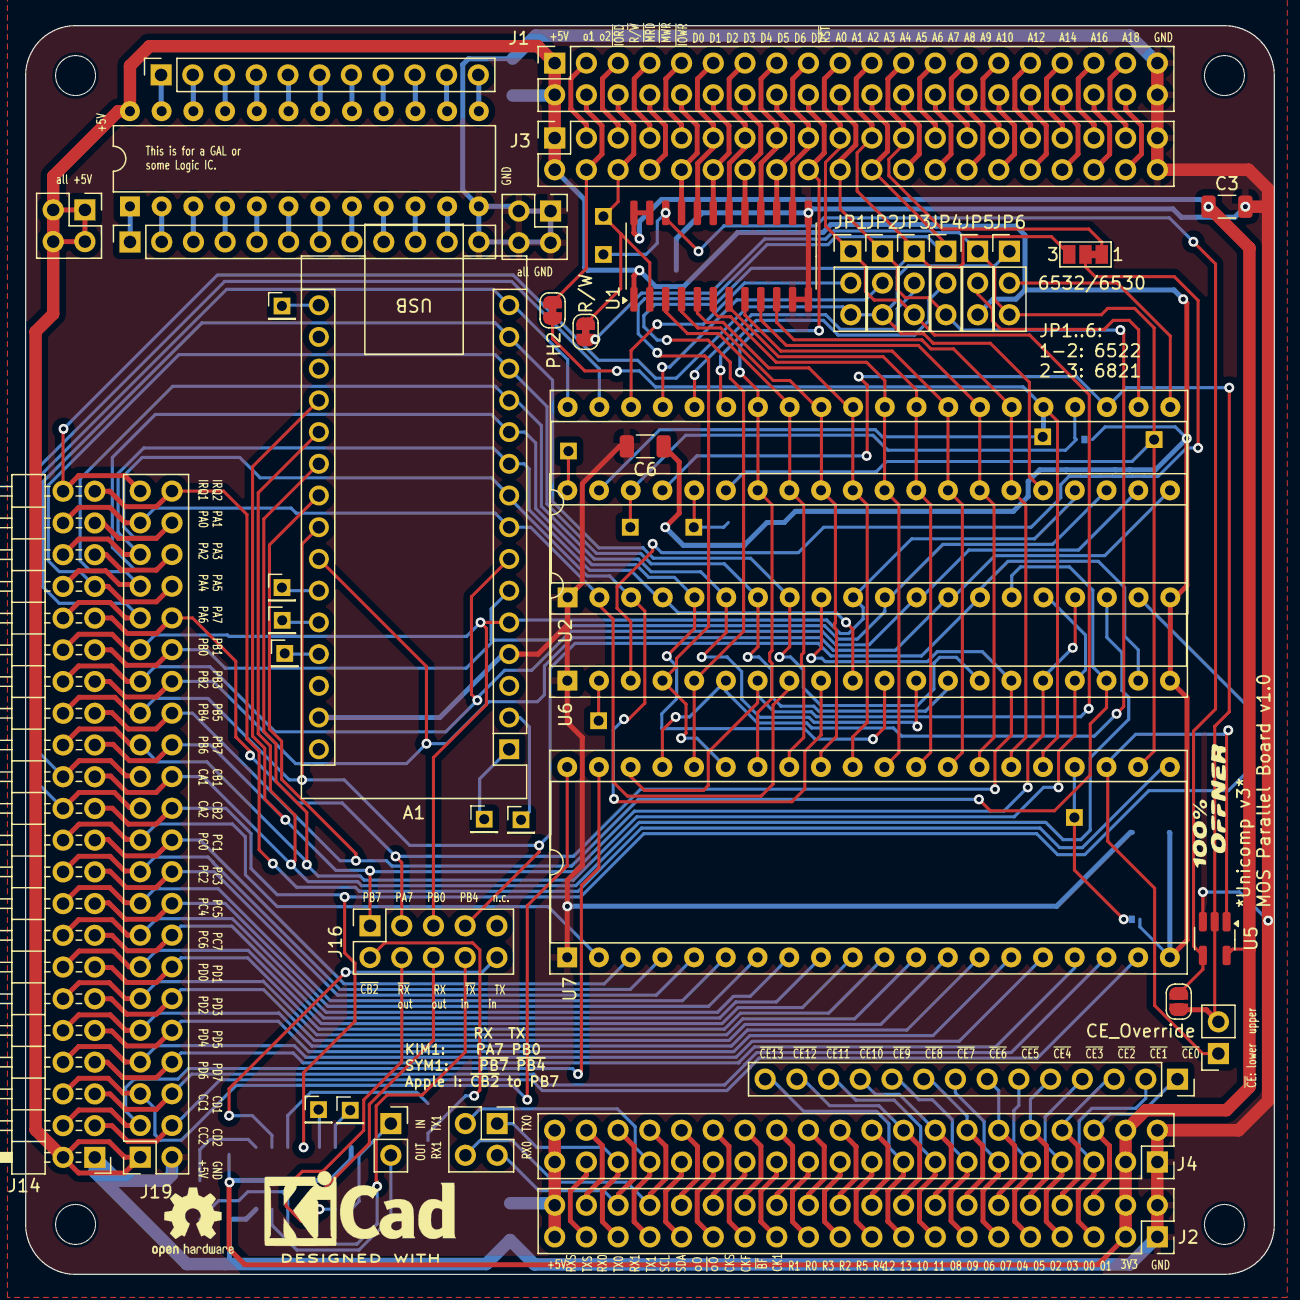
[picture p77: board MP_Board.kicad_pcb from above]

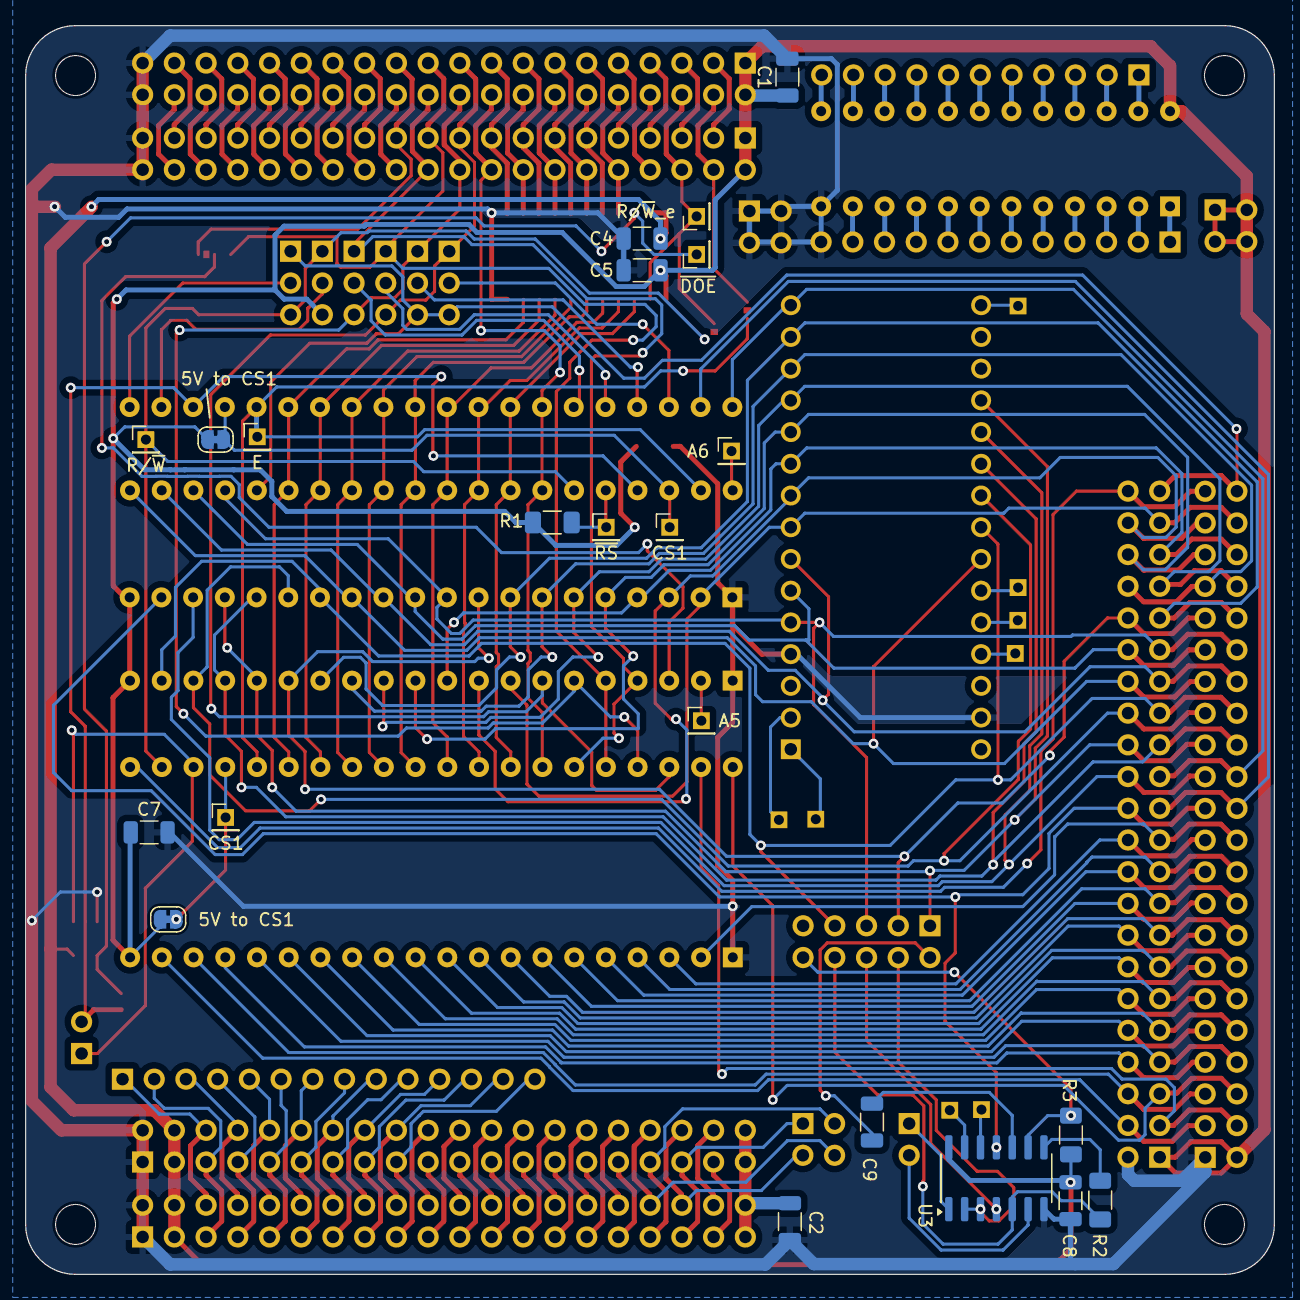
[picture p78: board MP_Board.kicad_pcb from below]

Board: 2 copper layers, 100.0 x 100.0 mm, 70 parts (22 on the bottom side), 180 nets.

Other parts of the board:
J19: Conn_02x22_Odd_Even; PinSocket_2x22_P2.54mm_Vertical

Their connections:
+5V: J19.1; also elsewhere on the board
/CA1: J19.25; also elsewhere on the board
/CA2: J19.23; also elsewhere on the board
/CB1: J19.26; also elsewhere on the board
/CB2: J19.24; also elsewhere on the board
/CC1: J19.5; also elsewhere on the board
/CC2: J19.3; also elsewhere on the board
/CD1: J19.6; also elsewhere on the board
/CD2: J19.4; also elsewhere on the board
/PA0: J19.41; also elsewhere on the board
/PA1: J19.42; also elsewhere on the board
/PA2: J19.39; also elsewhere on the board
/PA3: J19.40; also elsewhere on the board
/PA4: J19.37; also elsewhere on the board
/PA5: J19.38; also elsewhere on the board
/PA6: J19.35; also elsewhere on the board
/PA7: J19.36; also elsewhere on the board
/PB0: J19.33; also elsewhere on the board
/PB1: J19.34; also elsewhere on the board
/PB2: J19.31; also elsewhere on the board
/PB3: J19.32; also elsewhere on the board
/PB4: J19.29; also elsewhere on the board
/PB5: J19.30; also elsewhere on the board
/PB6: J19.27; also elsewhere on the board
/PB7: J19.28; also elsewhere on the board
/PC0: J19.21; also elsewhere on the board
/PC1: J19.22; also elsewhere on the board
/PC2: J19.19; also elsewhere on the board
/PC3: J19.20; also elsewhere on the board
/PC4: J19.17; also elsewhere on the board
/PC5: J19.18; also elsewhere on the board
/PC6: J19.15; also elsewhere on the board
/PC7: J19.16; also elsewhere on the board
/PD0: J19.13; also elsewhere on the board
/PD1: J19.14; also elsewhere on the board
/PD2: J19.11; also elsewhere on the board
/PD3: J19.12; also elsewhere on the board
/PD4: J19.9; also elsewhere on the board
/PD5: J19.10; also elsewhere on the board
/PD6: J19.7; also elsewhere on the board
/PD7: J19.8; also elsewhere on the board
/~IRQ2: J19.44; also elsewhere on the board
/~IRQ: J19.43; also elsewhere on the board
GND: J19.2; also elsewhere on the board
