roberto314/Unicomp3/VideoBoard/schematics/EF9345/EF9345.kicad_pcb

## KiCad design VideoBoard/schematics/EF9345/EF9345.kicad_pcb (2025-03-13)

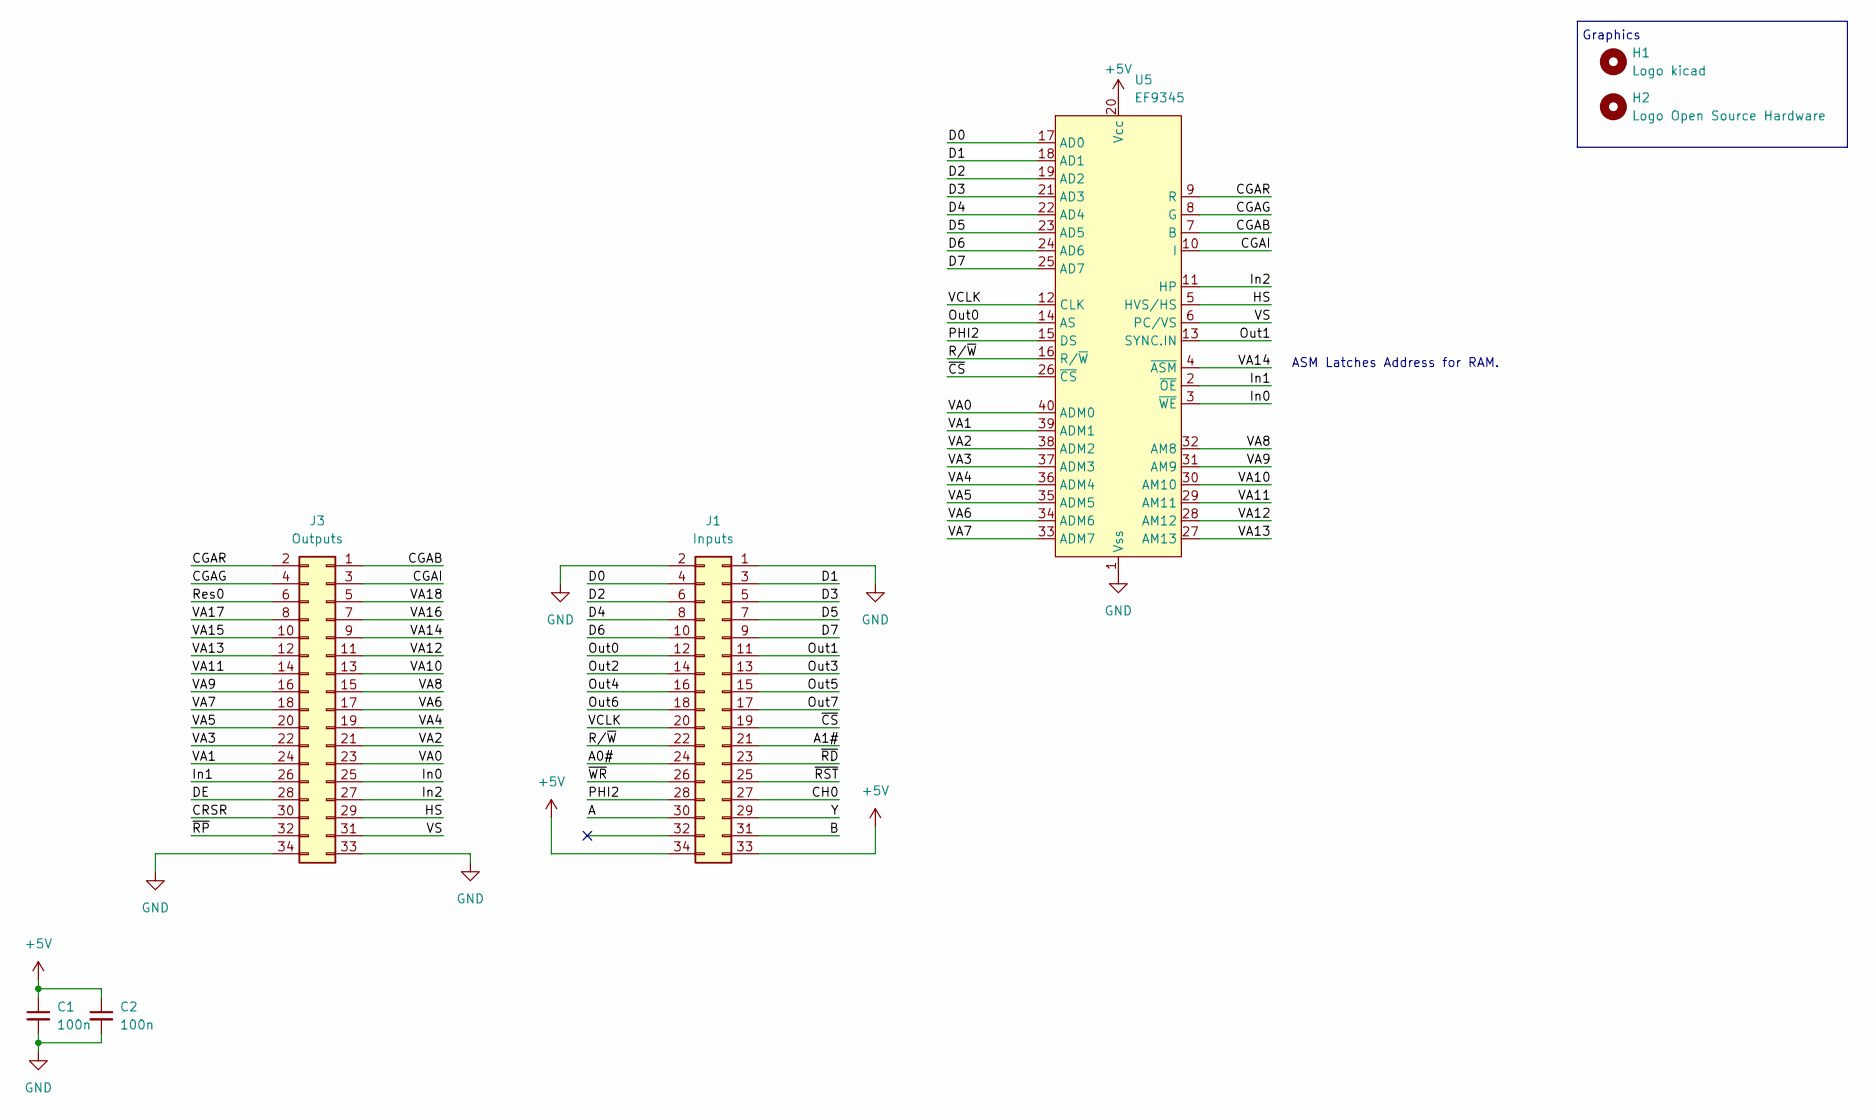
[picture p79: schematic EF9345.kicad_sch, Unicomp v3 - Video Board - EF9345 Adapter]

Parts:
C1, C2: 100n; C_1206_3216Metric_Pad1.33x1.80mm_HandSolder
H1: Logo kicad; KiCad-Logo2_6mm_SilkScreen
H2: Logo Open Source Hardware; OSHW-Logo2_7.3x6mm_SilkScreen
J1: Inputs; PinHeader_2x17_P2.54mm_Vertical
J3: Outputs; PinHeader_2x17_P2.54mm_Vertical
U5: EF9345; DIP-40_W15.24mm_Socket

Connections:
+5V: C1.1, C2.1, J1.33, J1.34, U5.20 (Vcc)
/A: J1.30
/A0#: J1.24
/A1#: J1.21
/B: J1.31
/CGAB: J3.1, U5.7 (B)
/CGAG: J3.4, U5.8 (G)
/CGAI: J3.3, U5.10 (I)
/CGAR: J3.2, U5.9 (R)
/CH0: J1.27
/CRSR: J3.30
/D0: J1.4, U5.17 (AD0)
/D1: J1.3, U5.18 (AD1)
/D2: J1.6, U5.19 (AD2)
/D3: J1.5, U5.21 (AD3)
/D4: J1.8, U5.22 (AD4)
/D5: J1.7, U5.23 (AD5)
/D6: J1.10, U5.24 (AD6)
/D7: J1.9, U5.25 (AD7)
/DE: J3.28
/HS: J3.29, U5.5 (HVS/HS)
/In0: J3.25, U5.3 (~WE)
/In1: J3.26, U5.2 (~OE)
/In2: J3.27, U5.11 (HP)
/Out0: J1.12, U5.14 (AS)
/Out1: J1.11, U5.13 (SYNC.IN)
/Out2: J1.14
/Out3: J1.13
/Out4: J1.16
/Out5: J1.15
/Out6: J1.18
/Out7: J1.17
/PHI2: J1.28, U5.15 (DS)
/Res0: J3.6
/R/~W: J1.22, U5.16 (R/~W)
/VA0: J3.23, U5.40 (ADM0)
/VA1: J3.24, U5.39 (ADM1)
/VA2: J3.21, U5.38 (ADM2)
/VA3: J3.22, U5.37 (ADM3)
/VA4: J3.19, U5.36 (ADM4)
/VA5: J3.20, U5.35 (ADM5)
/VA6: J3.17, U5.34 (ADM6)
/VA7: J3.18, U5.33 (ADM7)
/VA8: J3.15, U5.32 (AM8)
/VA9: J3.16, U5.31 (AM9)
/VA10: J3.13, U5.30 (AM10)
/VA11: J3.14, U5.29 (AM11)
/VA12: J3.11, U5.28 (AM12)
/VA13: J3.12, U5.27 (AM13)
/VA14: J3.9, U5.4 (~ASM)
/VA15: J3.10
/VA16: J3.7
/VA17: J3.8
/VA18: J3.5
/VCLK: J1.20, U5.12 (CLK)
/VS: J3.31, U5.6 (PC/VS)
/Y: J1.29
/~CS: J1.19, U5.26 (~CS)
/~RD: J1.23
/~RP: J3.32
/~RST: J1.25
/~WR: J1.26
GND: C1.2, C2.2, J1.1, J1.2, J3.33, J3.34, U5.1 (Vss)

Notes on the sheet:
Graphics
ASM Latches Address for RAM.

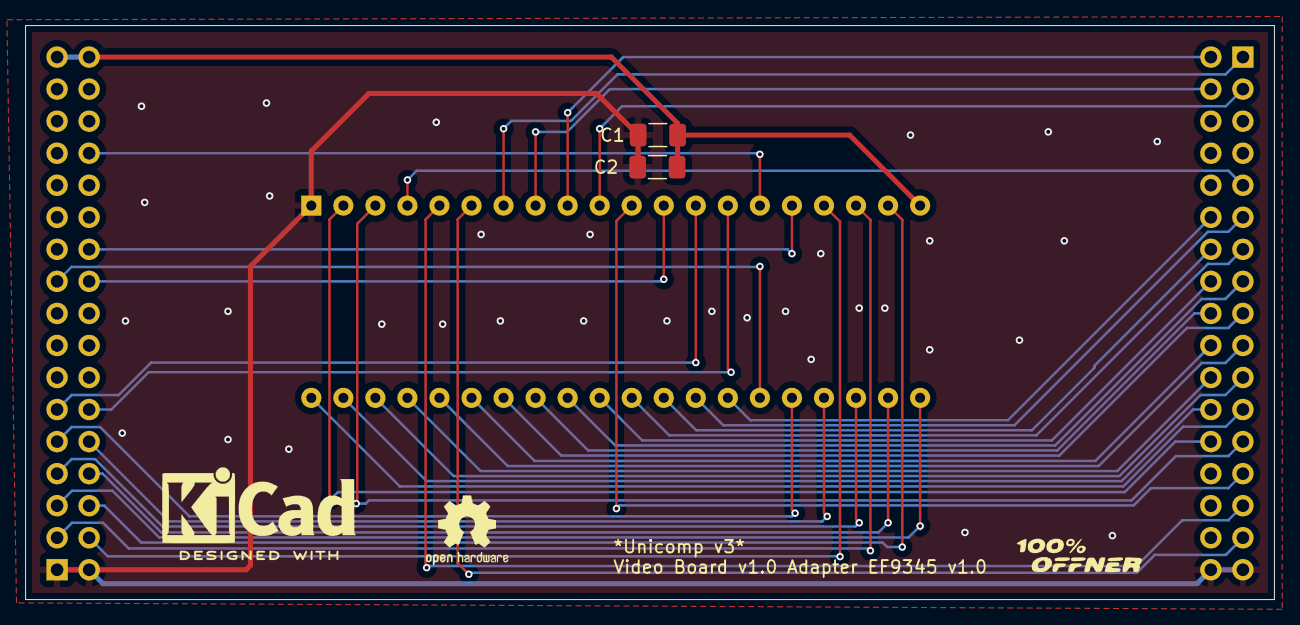
[picture p80: board EF9345.kicad_pcb from above]

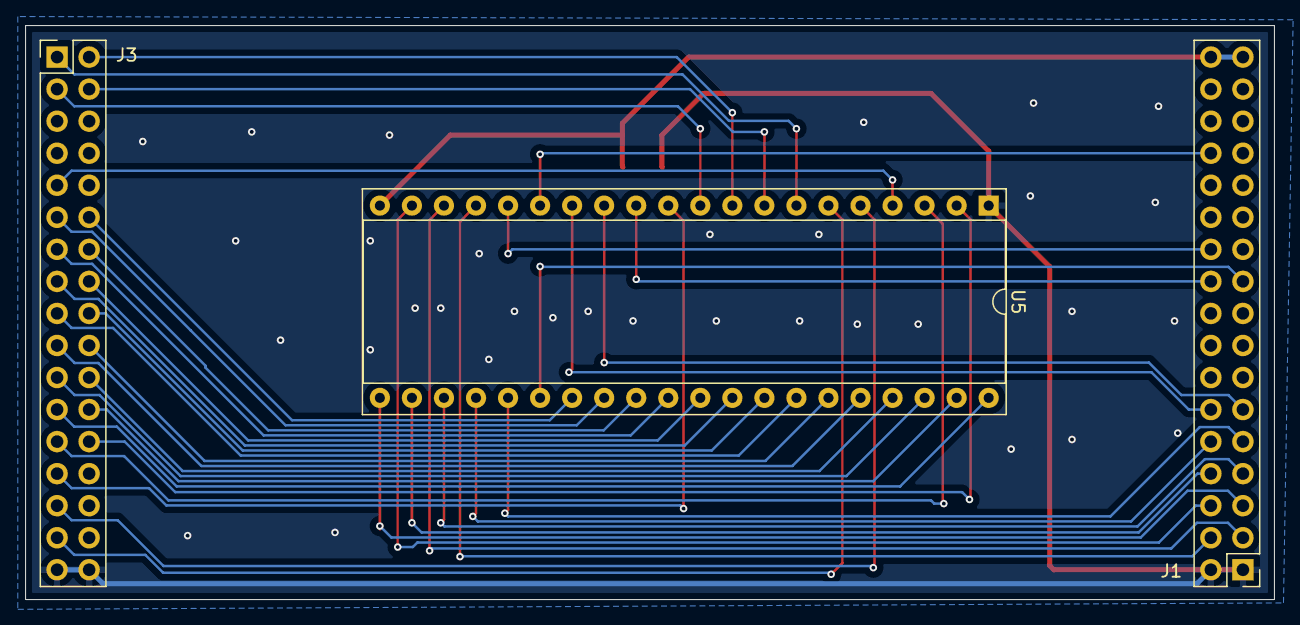
[picture p81: board EF9345.kicad_pcb from below]

Board: 2 copper layers, 99.0 x 45.5 mm, 7 parts (3 on the bottom side), 40 nets.
