roberto314/Unicomp3/VideoBoard/schematics/6847_v1/6847_v1.kicad_pcb

## KiCad design VideoBoard/schematics/6847_v1/6847_v1.kicad_pcb (2025-03-13)

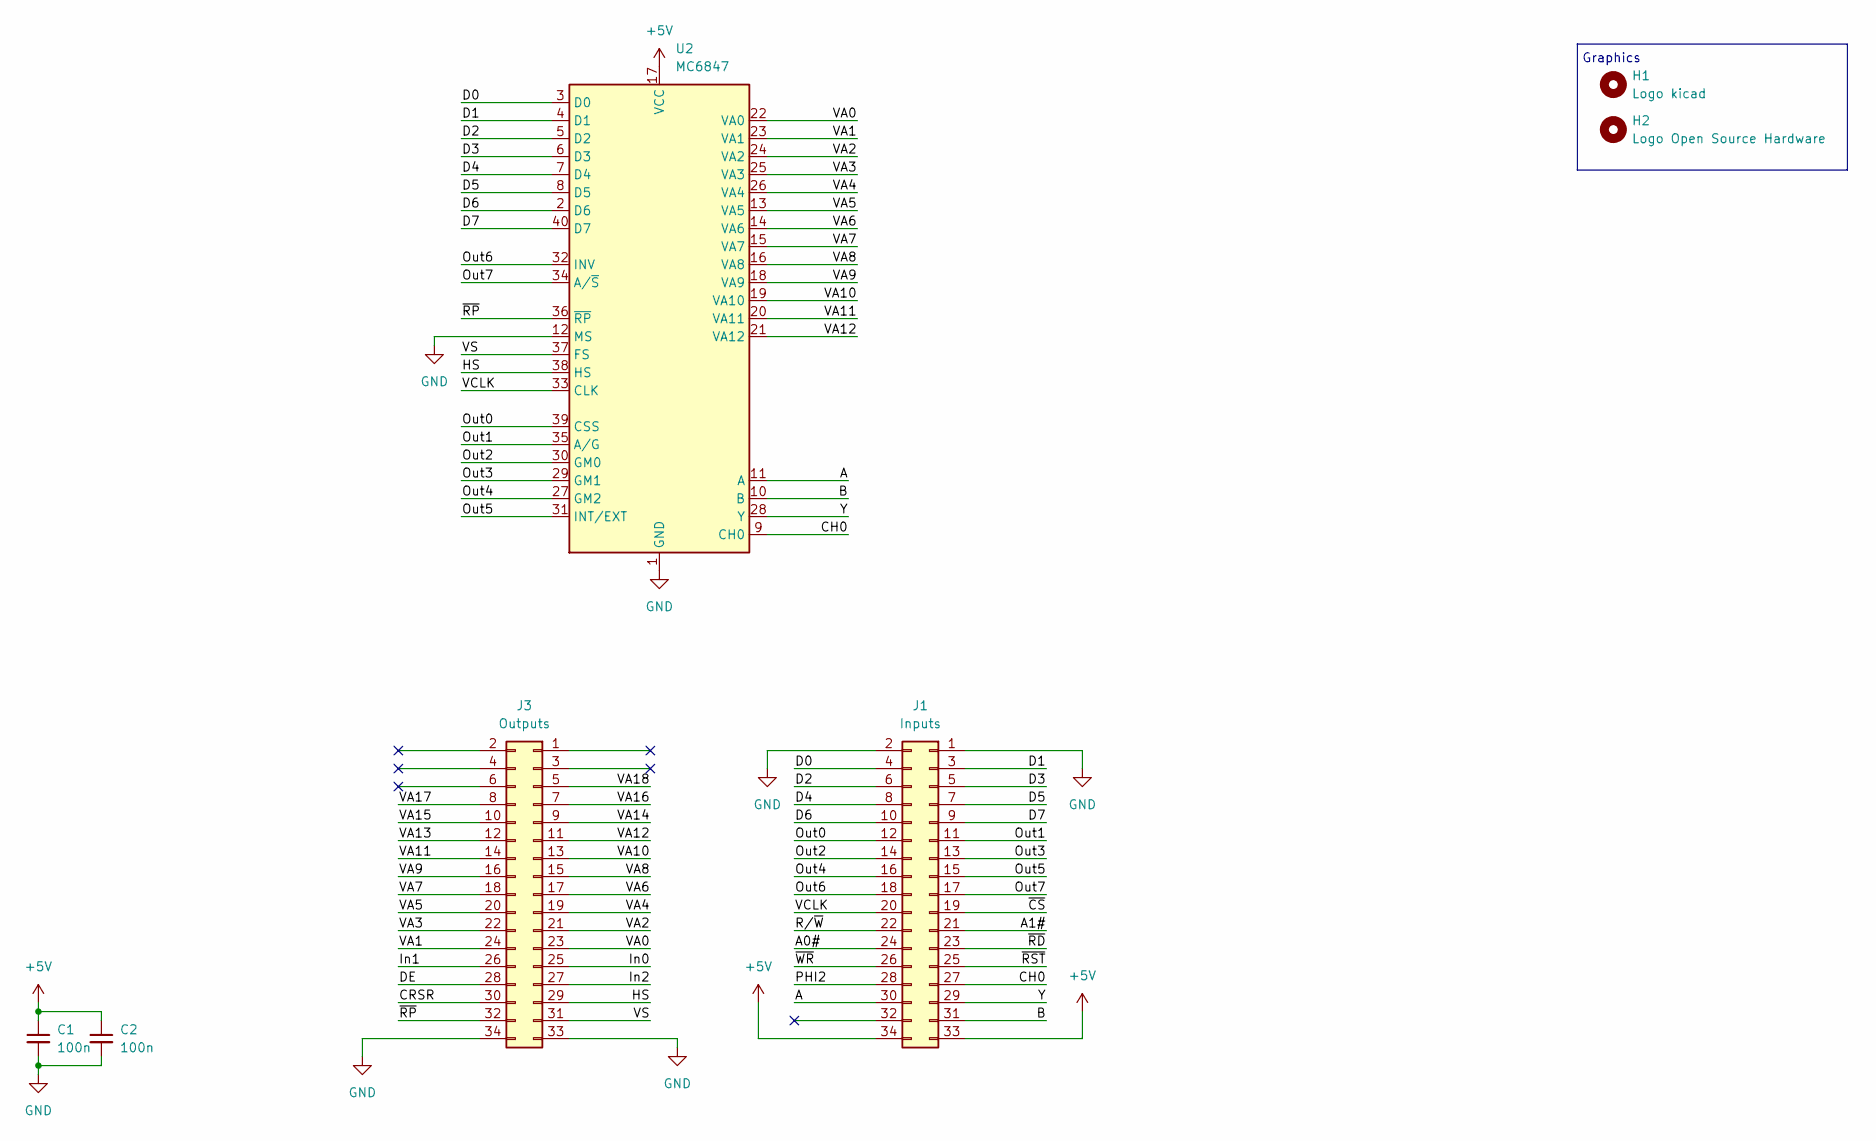
[picture p82: schematic 6847_v1.kicad_sch, Unicomp v3 - Video Board - MC9847 Adapter]

Parts:
C1, C2: 100n; C_1206_3216Metric_Pad1.33x1.80mm_HandSolder
H1: Logo kicad; KiCad-Logo2_6mm_SilkScreen
H2: Logo Open Source Hardware; OSHW-Logo2_7.3x6mm_SilkScreen
J1: Inputs; PinHeader_2x17_P2.54mm_Vertical
J3: Outputs; PinHeader_2x17_P2.54mm_Vertical
U2: MC6847; DIP-40_W15.24mm

Connections:
+5V: C1.1, C2.1, J1.33, J1.34, U2.17 (VCC)
/A: J1.30, U2.11 (A)
/A0#: J1.24
/A1#: J1.21
/B: J1.31, U2.10 (B)
/CH0: J1.27, U2.9 (CH0)
/CRSR: J3.30
/D0: J1.4, U2.3 (D0)
/D1: J1.3, U2.4 (D1)
/D2: J1.6, U2.5 (D2)
/D3: J1.5, U2.6 (D3)
/D4: J1.8, U2.7 (D4)
/D5: J1.7, U2.8 (D5)
/D6: J1.10, U2.2 (D6)
/D7: J1.9, U2.40 (D7)
/DE: J3.28
/HS: J3.29, U2.38 (HS)
/In0: J3.25
/In1: J3.26
/In2: J3.27
/Out0: J1.12, U2.39 (CSS)
/Out1: J1.11, U2.35 (A/G)
/Out2: J1.14, U2.30 (GM0)
/Out3: J1.13, U2.29 (GM1)
/Out4: J1.16, U2.27 (GM2)
/Out5: J1.15, U2.31 (INT/EXT)
/Out6: J1.18, U2.32 (INV)
/Out7: J1.17, U2.34 (A/~S)
/PHI2: J1.28
/R/~W: J1.22
/VA0: J3.23, U2.22 (VA0)
/VA1: J3.24, U2.23 (VA1)
/VA2: J3.21, U2.24 (VA2)
/VA3: J3.22, U2.25 (VA3)
/VA4: J3.19, U2.26 (VA4)
/VA5: J3.20, U2.13 (VA5)
/VA6: J3.17, U2.14 (VA6)
/VA7: J3.18, U2.15 (VA7)
/VA8: J3.15, U2.16 (VA8)
/VA9: J3.16, U2.18 (VA9)
/VA10: J3.13, U2.19 (VA10)
/VA11: J3.14, U2.20 (VA11)
/VA12: J3.11, U2.21 (VA12)
/VA13: J3.12
/VA14: J3.9
/VA15: J3.10
/VA16: J3.7
/VA17: J3.8
/VA18: J3.5
/VCLK: J1.20, U2.33 (CLK)
/VS: J3.31, U2.37 (FS)
/Y: J1.29, U2.28 (Y)
/~CS: J1.19
/~RD: J1.23
/~RP: J3.32, U2.36 (~RP)
/~RST: J1.25
/~WR: J1.26
GND: C1.2, C2.2, J1.1, J1.2, J3.33, J3.34, U2.1 (GND), U2.12 (MS)

Notes on the sheet:
Graphics

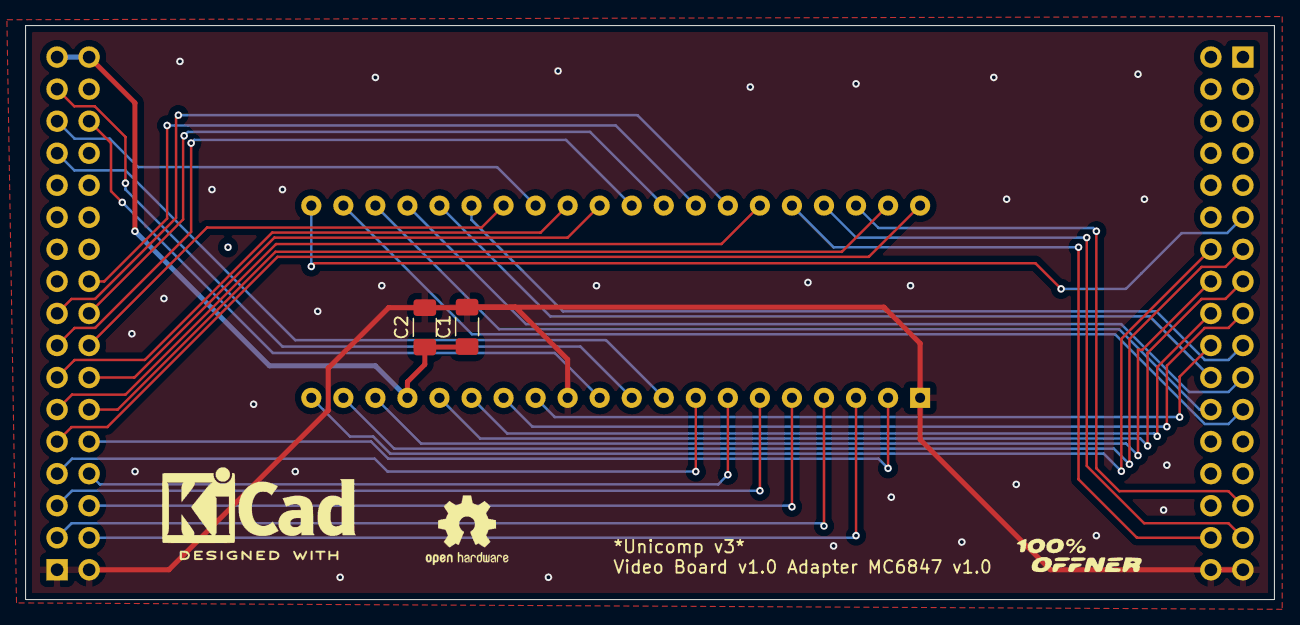
[picture p83: board 6847_v1.kicad_pcb from above]

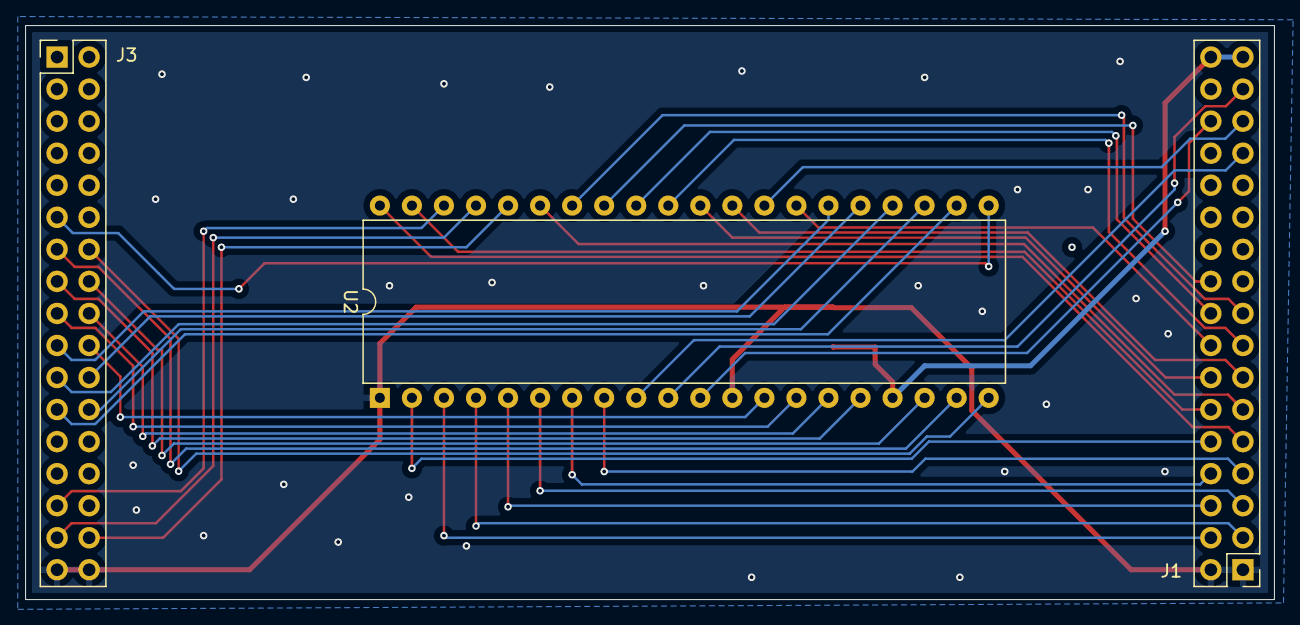
[picture p84: board 6847_v1.kicad_pcb from below]

Board: 2 copper layers, 99.0 x 45.5 mm, 7 parts (3 on the bottom side), 39 nets.
