roberto314/Unicomp3/RamRomBoard/schematics_v11/schematics_v11.kicad_pcb

## KiCad design RamRomBoard/schematics_v11/schematics_v11.kicad_pcb (2025-03-13, an earlier design)

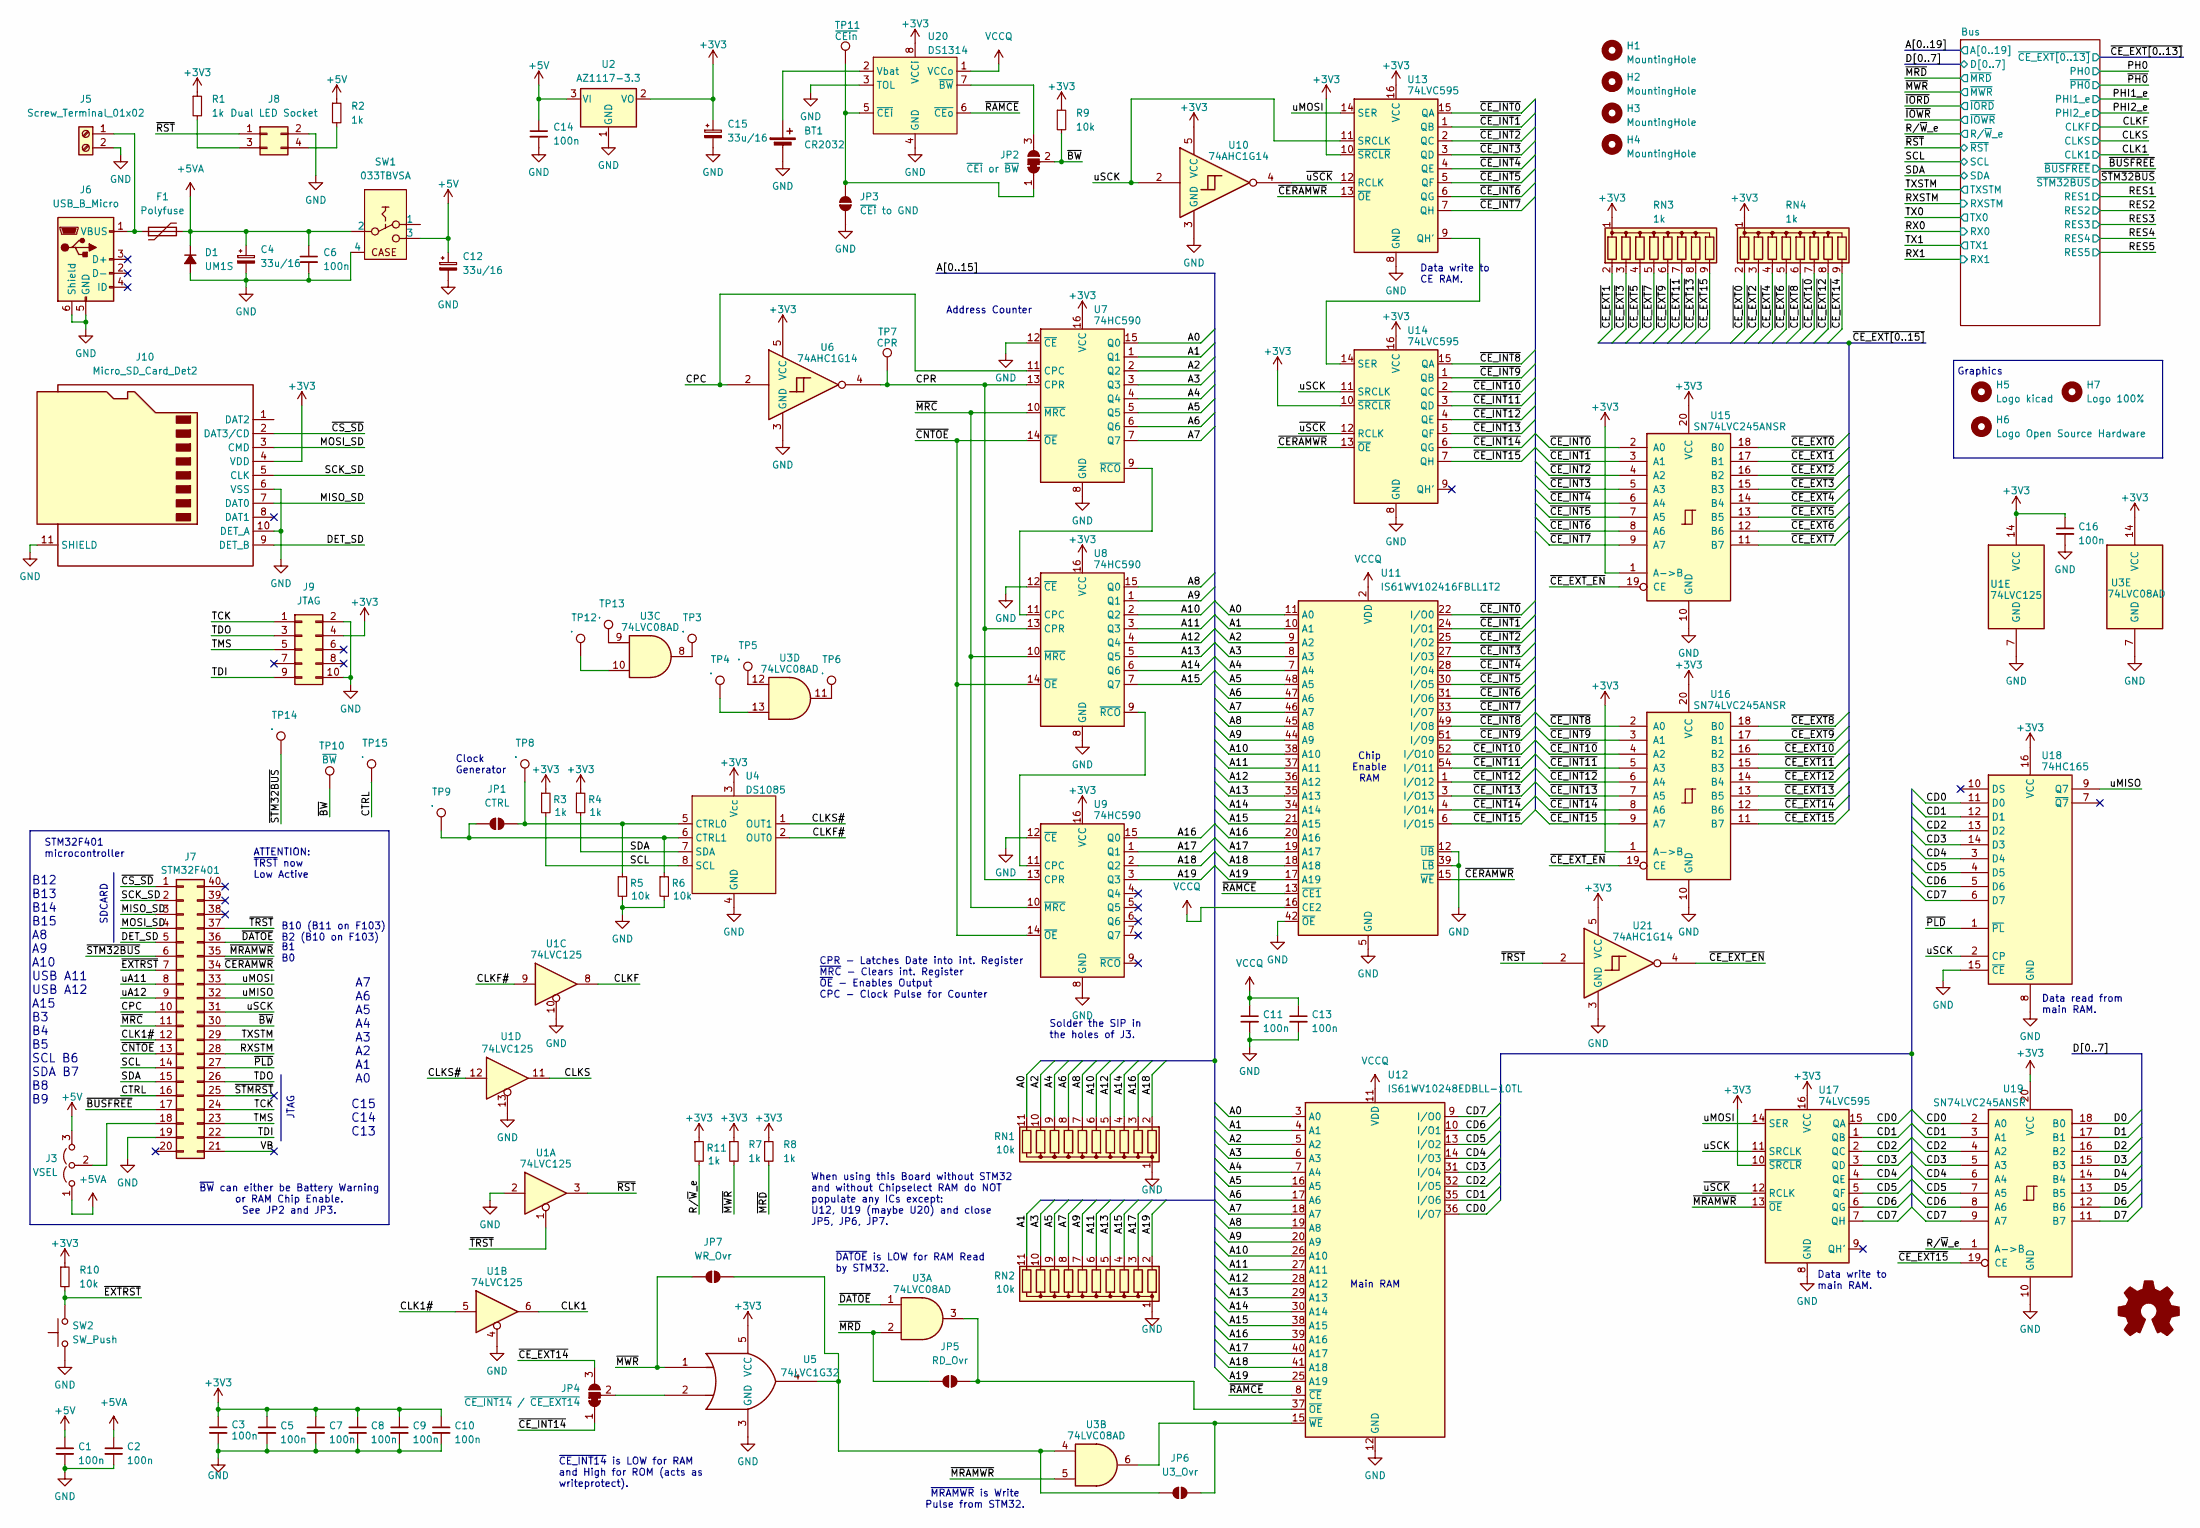
[picture p85: schematic schematics_v11.kicad_sch, Unicomp v3 - RAMROM Board]

Parts:
BT1: CR2032; Battery_CR2032_Horizontal_ThreeHoles
C1, C2, C3, C5, C6, C7, C8, C9, C10, C11, C13, C14, C16: 100n; C_1206_3216Metric
C4, C12, C15: 33u/16; CP_EIA-7343-31_Kemet-D
D1: UM1S; D_SMB
F1: Polyfuse; Fuse_Littelfuse_395Series
H1, H2, H3, H4: MountingHole; MountingHole_3.2mm_M3
H5: Logo kicad; KiCad-Logo2_6mm_SilkScreen
H6: Logo Open Source Hardware; OSHW-Logo2_7.3x6mm_SilkScreen
H7: Logo 100%; Logo_100ProzentOffner_10x2.7mm
J3: VSEL; PinHeader_1x03_P2.54mm_Vertical
J5: Screw_Terminal_01x02; TerminalBlock_RND_205-00012_1x02_P5.00mm_Horizontal
J6: USB_B_Micro; USB_Micro-B_Amphenol_10104110_Horizontal
J7: STM32F401; DIP-40_W15.24mm_Socket_LongPads
J8: Dual LED Socket; PinHeader_2x02_P2.54mm_Vertical
J9: JTAG; PinHeader_2x05_P2.54mm_Horizontal
J10: Micro_SD_Card_Det2; microSD_HC_Hirose_DM3D-SF
JP1: CTRL; SolderJumper-2_P1.3mm_Open_RoundedPad1.0x1.5mm
JP2: ~{CEi} or ~{BW}; SolderJumper-3_P1.3mm_Bridged12_RoundedPad1.0x1.5mm
JP3: ~{CEi} to GND; SolderJumper-2_P1.3mm_Open_RoundedPad1.0x1.5mm
JP4: ~{CE_INT14} / ~{CE_EXT14}; SolderJumper-3_P1.3mm_Bridged12_RoundedPad1.0x1.5mm
JP5: RD_Ovr; SolderJumper-2_P1.3mm_Open_RoundedPad1.0x1.5mm
JP6: U3_Ovr; SolderJumper-2_P1.3mm_Open_RoundedPad1.0x1.5mm
JP7: WR_Ovr; SolderJumper-2_P1.3mm_Open_RoundedPad1.0x1.5mm
R1, R2, R3, R4, R7, R8, R11: 1k; R_1206_3216Metric
R5, R6, R9, R10: 10k; R_1206_3216Metric
RN1, RN2: 10k; R_Array_SIP11
RN3, RN4: 1k; R_Array_SIP9
SW1: 033TBVSA; ToggleSwitch_CTS_033TBVS
SW2: SW_Push; SW_Tactile_SPST_Angled_PTS645Vx31-2LFS
TP3, TP4, TP5, TP6, TP8, TP9, TP12, TP13, TP14, TP15: .; PinHeader_1x01_P1.00mm_Vertical
TP7: CPR; PinHeader_1x01_P1.00mm_Vertical
TP10: ~{BW}; PinHeader_1x01_P1.00mm_Vertical
TP11: ~{CEin}; PinHeader_1x01_P1.00mm_Vertical
U1: 74LVC125; SOIC-14_3.9x8.7mm_P1.27mm
U2: AZ1117-3.3; SOT-223-3_TabPin2
U3: 74LVC08AD; SOIC-14_3.9x8.7mm_P1.27mm
U4: DS1085; SOIC-8_3.9x4.9mm_P1.27mm
U5: 74LVC1G32; SOT-23-5_HandSoldering
U6, U10, U21: 74AHC1G14; SOT-23-5
U7, U8, U9: 74HC590; SOIC-16_3.9x9.9mm_P1.27mm
U11: IS61WV102416FBLL1T2; TSOP-II-54_22.2x10.16mm_P0.8mm
U12: IS61WV10248EDBLL-10TL; TSOP-II-44_10.16x18.41mm_P0.8mm
U13, U14, U17: 74LVC595; SO-16_3.9x9.9mm_P1.27mm
U15, U16, U19: SN74LVC245ANSR; SO-20_5.3x12.6mm_P1.27mm
U18: 74HC165; SOIC-16_3.9x9.9mm_P1.27mm
U20: DS1314; SOIC-8_3.9x4.9mm_P1.27mm

Connections:
+3V3: C3.1, C5.1, C7.1, C8.1, C9.1, C10.1, C15.1, C16.1, J9.4, J10.4 (VDD), R1.1, R3.1, R4.1, R7.1, R8.1, R9.1, R10.1, R11.1, RN3.1 (common), RN4.1 (common), U1.14 (VCC), U2.2 (VO), U3.14 (VCC), U4.3 (Vcc), U5.5 (VCC), U6.5 (VCC), U7.16 (VCC), U8.16 (VCC), U9.16 (VCC), U10.5 (VCC), U13.10 (~SRCLR), U13.16 (VCC), U14.10 (~SRCLR), U14.16 (VCC), U15.1 (A->B), U15.20 (VCC), U16.1 (A->B), U16.20 (VCC), U17.10 (~SRCLR), U17.16 (VCC), U18.16 (VCC), U19.20 (VCC), U20.8 (VCCi), U21.5 (VCC); also elsewhere on the board
+5V: C1.1, C12.1, C14.1, J3.3 (B), R2.1, SW1.3, U2.3 (VI); also elsewhere on the board
+5VA: C2.1, C4.1, C6.1, D1.1 (K), F1.2, J3.1 (A), SW1.2; also elsewhere on the board
/A0: RN1.11 (R10), U7.15 (Q0), U11.11 (A0), U12.3 (A0); also elsewhere on the board
/A1: RN2.11 (R10), U7.1 (Q1), U11.10 (A1), U12.4 (A1); also elsewhere on the board
/A2: RN1.10 (R9), U7.2 (Q2), U11.9 (A2), U12.5 (A2); also elsewhere on the board
/A3: RN2.10 (R9), U7.3 (Q3), U11.8 (A3), U12.6 (A3); also elsewhere on the board
/A4: RN1.9 (R8), U7.4 (Q4), U11.7 (A4), U12.7 (A4); also elsewhere on the board
/A5: RN2.9 (R8), U7.5 (Q5), U11.48 (A5), U12.16 (A5); also elsewhere on the board
/A6: RN1.8 (R7), U7.6 (Q6), U11.47 (A6), U12.17 (A6); also elsewhere on the board
/A7: RN2.8 (R7), U7.7 (Q7), U11.46 (A7), U12.18 (A7); also elsewhere on the board
/A8: RN1.7 (R6), U8.15 (Q0), U11.45 (A8), U12.19 (A8); also elsewhere on the board
/A9: RN2.7 (R6), U8.1 (Q1), U11.44 (A9), U12.20 (A9); also elsewhere on the board
/A10: RN1.6 (R5), U8.2 (Q2), U11.38 (A10), U12.26 (A10); also elsewhere on the board
/A11: RN2.6 (R5), U8.3 (Q3), U11.37 (A11), U12.27 (A11); also elsewhere on the board
/A12: RN1.5 (R4), U8.4 (Q4), U11.36 (A12), U12.28 (A12); also elsewhere on the board
/A13: RN2.5 (R4), U8.5 (Q5), U11.35 (A13), U12.29 (A13); also elsewhere on the board
/A14: RN1.4 (R3), U8.6 (Q6), U11.34 (A14), U12.30 (A14); also elsewhere on the board
/A15: RN2.4 (R3), U8.7 (Q7), U11.21 (A15), U12.38 (A15); also elsewhere on the board
/A16: RN1.3 (R2), U9.15 (Q0), U11.20 (A16), U12.39 (A16); also elsewhere on the board
/A17: RN2.3 (R2), U9.1 (Q1), U11.19 (A17), U12.40 (A17); also elsewhere on the board
/A18: RN1.2 (R1), U9.2 (Q2), U11.18 (A18), U12.41 (A18); also elsewhere on the board
/A19: RN2.2 (R1), U9.3 (Q3), U11.17 (A19), U12.25 (A19); also elsewhere on the board
/CD0: U12.36 (I/O7), U17.15 (QA), U18.11 (D0), U19.2 (A0)
/CD1: U12.35 (I/O6), U17.1 (QB), U18.12 (D1), U19.3 (A1)
/CD2: U12.32 (I/O5), U17.2 (QC), U18.13 (D2), U19.4 (A2)
/CD3: U12.31 (I/O4), U17.3 (QD), U18.14 (D3), U19.5 (A3)
/CD4: U12.14 (I/O3), U17.4 (QE), U18.3 (D4), U19.6 (A4)
/CD5: U12.13 (I/O2), U17.5 (QF), U18.4 (D5), U19.7 (A5)
/CD6: U12.10 (I/O1), U17.6 (QG), U18.5 (D6), U19.8 (A6)
/CD7: U12.9 (I/O0), U17.7 (QH), U18.6 (D7), U19.9 (A7)
/CLK1: U1.6; also elsewhere on the board
/CLK1#: J7.12, U1.5
/CLKF: U1.8; also elsewhere on the board
/CLKF#: U1.9, U4.2 (OUT0)
/CLKS: U1.11; also elsewhere on the board
/CLKS#: U1.12, U4.1 (OUT1)
/CPC: J7.10, U6.2, U7.11 (CPC)
/CPR: TP7.1, U6.4, U7.13 (CPR), U8.13 (CPR), U9.13 (CPR)
/CTRL: J7.16, TP15.1
/D0: U19.18 (B0); also elsewhere on the board
/D1: U19.17 (B1); also elsewhere on the board
/D2: U19.16 (B2); also elsewhere on the board
/D3: U19.15 (B3); also elsewhere on the board
/D4: U19.14 (B4); also elsewhere on the board
/D5: U19.13 (B5); also elsewhere on the board
/D6: U19.12 (B6); also elsewhere on the board
/D7: U19.11 (B7); also elsewhere on the board
/DET_SD: J7.5, J10.9 (DET_B)
/MISO_SD: J7.3, J10.7 (DAT0)
/MOSI_SD: J7.4, J10.3 (CMD)
/RXSTM: J7.28; also elsewhere on the board
/R/~W_e: R11.2, U19.1 (A->B); also elsewhere on the board
/SCK_SD: J7.2, J10.5 (CLK)
/SCL: J7.14, R3.2, U4.8 (SCL); also elsewhere on the board
/SDA: J7.15, R4.2, U4.7 (SDA); also elsewhere on the board
/TCK: J7.24, J9.1
/TDI: J7.22, J9.9
/TDO: J7.26, J9.3
/TMS: J7.23, J9.5
/TXSTM: J7.29; also elsewhere on the board
/VB: J7.21
/uA11: J7.8
/uA12: J7.9
/uMISO: J7.32, U18.9 (Q7)
/uMOSI: J7.33, U13.14 (SER), U17.14 (SER)
/uSCK: J7.31, U10.2, U13.11 (SRCLK), U14.11 (SRCLK), U17.11 (SRCLK), U18.2 (CP)
/~BUSFREE: J7.17; also elsewhere on the board
/~BW: J7.30, JP2.2 (C), R9.2, TP10.1
/~CERAMWR: J7.34, U11.15 (~WE), U13.13 (~OE), U14.13 (~OE)
/~CE_EXT0: RN4.2 (R1), U15.18 (B0); also elsewhere on the board
/~CE_EXT1: RN3.2 (R1), U15.17 (B1); also elsewhere on the board
/~CE_EXT2: RN4.3 (R2), U15.16 (B2); also elsewhere on the board
/~CE_EXT3: RN3.3 (R2), U15.15 (B3); also elsewhere on the board
/~CE_EXT4: RN4.4 (R3), U15.14 (B4); also elsewhere on the board
/~CE_EXT5: RN3.4 (R3), U15.13 (B5); also elsewhere on the board
/~CE_EXT6: RN4.5 (R4), U15.12 (B6); also elsewhere on the board
/~CE_EXT7: RN3.5 (R4), U15.11 (B7); also elsewhere on the board
/~CE_EXT8: RN4.6 (R5), U16.18 (B0); also elsewhere on the board
/~CE_EXT9: RN3.6 (R5), U16.17 (B1); also elsewhere on the board
/~CE_EXT10: RN4.7 (R6), U16.16 (B2); also elsewhere on the board
/~CE_EXT11: RN3.7 (R6), U16.15 (B3); also elsewhere on the board
/~CE_EXT12: RN4.8 (R7), U16.14 (B4); also elsewhere on the board
/~CE_EXT13: RN3.8 (R7), U16.13 (B5); also elsewhere on the board
/~CE_EXT14: JP4.3 (B), RN4.9 (R8), U16.12 (B6)
/~CE_EXT15: RN3.9 (R8), U16.11 (B7), U19.19 (CE)
/~CE_EXT_EN: U15.19 (CE), U16.19 (CE), U21.4
/~CE_INT0: U11.22 (I/O0), U13.15 (QA), U15.2 (A0)
/~CE_INT1: U11.24 (I/O1), U13.1 (QB), U15.3 (A1)
/~CE_INT2: U11.25 (I/O2), U13.2 (QC), U15.4 (A2)
/~CE_INT3: U11.27 (I/O3), U13.3 (QD), U15.5 (A3)
/~CE_INT4: U11.28 (I/O4), U13.4 (QE), U15.6 (A4)
/~CE_INT5: U11.30 (I/O5), U13.5 (QF), U15.7 (A5)
/~CE_INT6: U11.31 (I/O6), U13.6 (QG), U15.8 (A6)
/~CE_INT7: U11.33 (I/O7), U13.7 (QH), U15.9 (A7)
/~CE_INT8: U11.49 (I/O8), U14.15 (QA), U16.2 (A0)
/~CE_INT9: U11.51 (I/O9), U14.1 (QB), U16.3 (A1)
/~CE_INT10: U11.52 (I/O10), U14.2 (QC), U16.4 (A2)
/~CE_INT11: U11.54 (I/O11), U14.3 (QD), U16.5 (A3)
/~CE_INT12: U11.1 (I/O12), U14.4 (QE), U16.6 (A4)
/~CE_INT13: U11.3 (I/O13), U14.5 (QF), U16.7 (A5)
/~CE_INT14: JP4.1 (A), U11.4 (I/O14), U14.6 (QG), U16.8 (A6)
/~CE_INT15: U11.6 (I/O15), U14.7 (QH), U16.9 (A7)
/~CNTOE: J7.13, U7.14 (~OE), U8.14 (~OE), U9.14 (~OE)
/~CS_SD: J7.1, J10.2 (DAT3/CD)
/~DATOE: J7.36, U3.1
/~EXTRST: J7.7, R10.2, SW2.2
/~MRAMWR: J7.35, U3.5, U17.13 (~OE)
/~MRC: J7.11, U7.10 (~MRC), U8.10 (~MRC), U9.10 (~MRC)
/~MRD: JP5.2 (B), R8.2, U3.2; also elsewhere on the board
/~MWR: JP7.2 (B), R7.2, U5.1; also elsewhere on the board
/~PLD: J7.27, U18.1 (~PL)
/~RAMCE: U11.13 (~CE1), U12.8 (~CE), U20.6 (~CEo)
/~RST: J8.1, U1.3; also elsewhere on the board
/~STM32BUS: J7.6, TP14.1; also elsewhere on the board
/~STMRST: J7.25
/~TRST: J7.37, U1.1, U21.2
/~uSCK: U10.4, U13.12 (RCLK), U14.12 (RCLK), U17.12 (RCLK)
GND: BT1.2 (-), C1.2, C2.2, C3.2, C4.2, C5.2, C6.2, C7.2, C8.2, C9.2, C10.2, C11.2, C12.2, C13.2, C14.2, C15.2, C16.2, D1.2 (A), J5.2, J6.5 (GND), J6.6 (Shield), J7.19, J8.2, J9.2, J9.10, J10.6 (VSS), J10.10 (DET_A), J10.11 (SHIELD), JP3.1 (A), R5.2, R6.2, RN1.1 (common), RN2.1 (common), SW1.4, SW2.1, U1.2, U1.4, U1.7 (GND), U1.10, U1.13, U2.1 (GND), U3.7 (GND), U4.4 (GND), U5.3 (GND), U6.3 (GND), U7.8 (GND), U7.12 (~CE), U8.8 (GND), U8.12 (~CE), U9.8 (GND), U9.12 (~CE), U10.3 (GND), U11.5 (GND), U11.12 (~UB), U11.26 (GND), U11.32 (GND), U11.39 (~LB), U11.41 (GND), U11.42 (~OE), U11.53 (GND), U12.12 (GND), U12.34 (GND), U13.8 (GND), U14.8 (GND), U15.10 (GND), U16.10 (GND), U17.8 (GND), U18.8 (GND), U18.15 (~CE), U19.10 (GND), U20.3 (TOL), U20.4 (GND), U21.3 (GND); also elsewhere on the board
unnamed: BT1.1 (+), U20.2 (Vbat)
unnamed: J3.2 (C), J7.18
unnamed: F1.1, J5.1, J6.1 (VBUS)
unnamed: J8.3, R1.2
unnamed: J8.4, R2.2
unnamed: JP1.1 (A), R5.1, TP8.1, U4.5 (CTRL0)
unnamed: JP1.2 (B), R6.1, TP9.1, U4.6 (CTRL1)
unnamed: JP2.1 (A), JP3.2 (B), TP11.1, U20.5 (~CEi)
unnamed: JP2.3 (B), U20.7 (~BW)
unnamed: JP4.2 (C), U5.2
unnamed: JP5.1 (A), U3.3, U12.37 (~OE)
unnamed: JP6.1 (A), U3.6, U12.15 (~WE)
unnamed: JP6.2 (B), JP7.1 (A), U3.4, U5.4
unnamed: TP3.1, U3.8
unnamed: TP4.1, U3.13
unnamed: TP5.1, U3.12
unnamed: TP6.1, U3.11
unnamed: TP12.1, U3.10
unnamed: TP13.1, U3.9
unnamed: U7.9 (~RCO), U8.11 (CPC)
unnamed: U8.9 (~RCO), U9.11 (CPC)
unnamed: U13.9 (QH'), U14.14 (SER)
VCCQ: C11.1, C13.1, U11.2 (VDD), U11.14 (VDD), U11.16 (CE2), U11.23 (VDD), U11.29 (VDD), U11.50 (VDD), U12.11 (VDD), U12.33 (VDD), U20.1 (VCCo)

Notes on the sheet:
SDCARD
B1 B0
When using this Board without STM32 and without Chipselect RAM do NOT populate any ICs except: U12, U19 (maybe U20) and close JP5, JP6, JP7.
Data write to main RAM.
JTAG
ATTENTION: ~{TRST} now Low Active
CPR - Latches Date into int. Register ~{MRC} - Clears int. Register ~{OE} - Enables Output CPC - Clock Pulse for Counter
Graphics
~{CE_INT14} is LOW for RAM and High for ROM (acts as writeprotect).
Data write to CE RAM.
~{BW} can either be Battery Warning or RAM Chip Enable. See JP2 and JP3.
B10 (B11 on F103) B2 (B10 on F103)
Chip Enable RAM
~{DATOE} is LOW for RAM Read by STM32.
A7 A6 A5 A4 A3 A2 A1 A0
Clock Generator
~{MRAMWR} is Write Pulse from STM32.
Solder the SIP in the holes of J3.
B12 B13 B14 B15 A8 A9 A10 USB A11 USB A12 A15 B3 B4 B5 SCL B6 SDA B7 B8 B9
Main RAM
C15 C14 C13
Data read from main RAM.
STM32F401 microcontroller
Address Counter

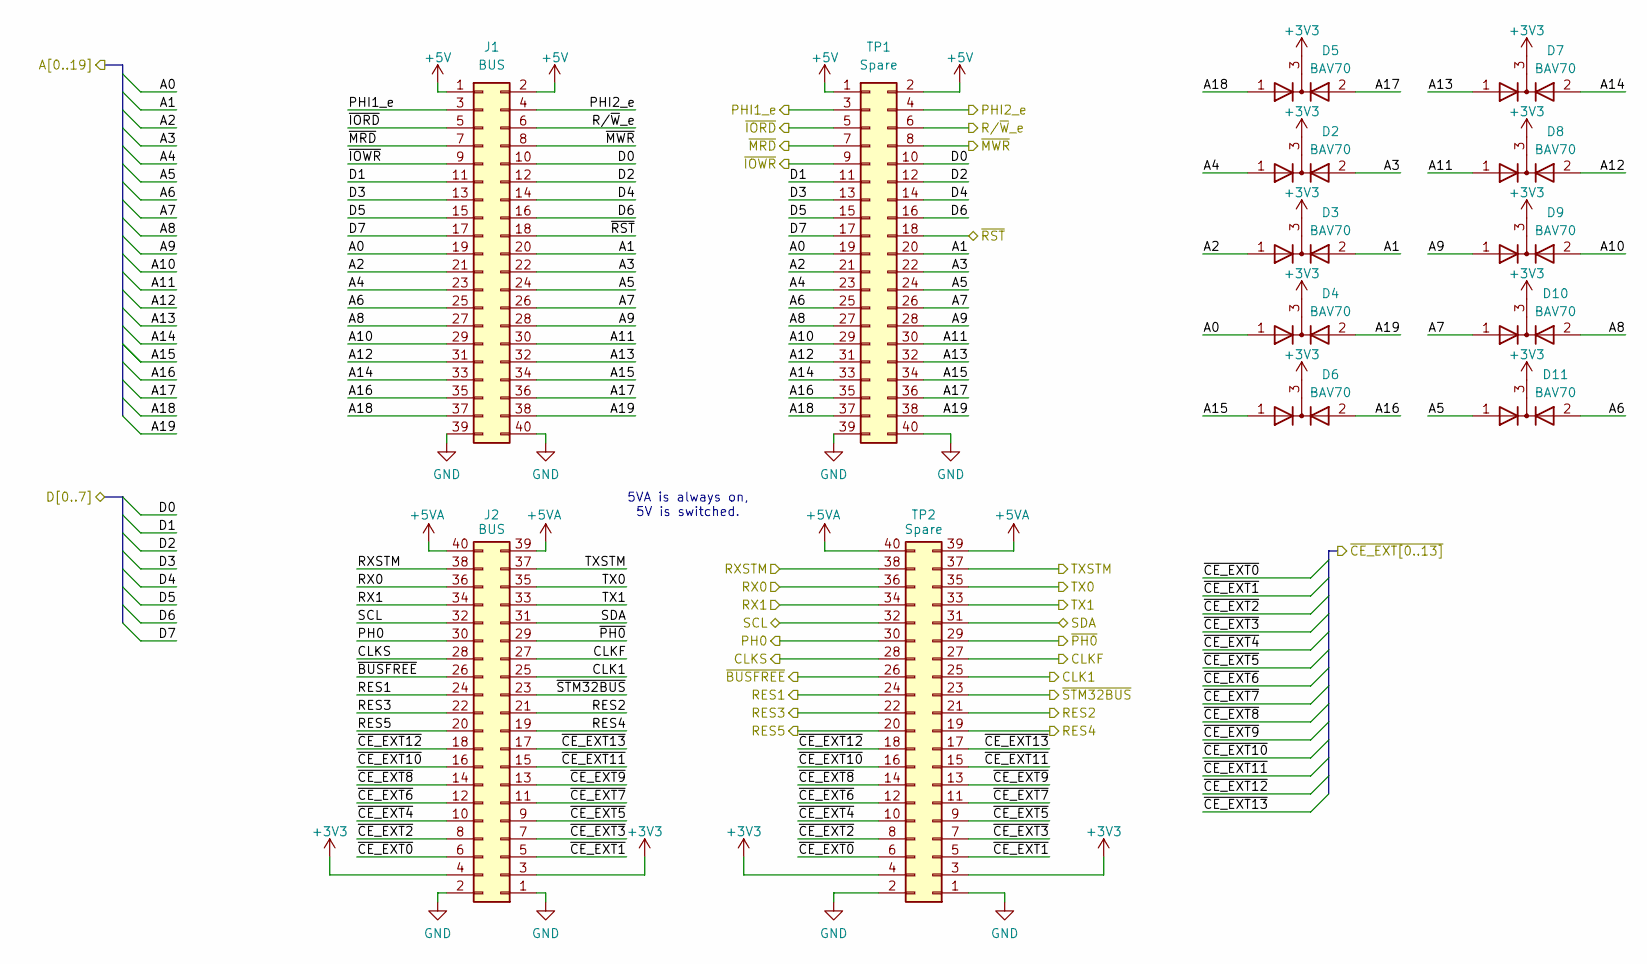
[picture p86: schematic bus.kicad_sch, Unicomp v3 - RAMROM Board]

Parts:
D2, D3, D4, D5, D6, D7, D8, D9, D10, D11: BAV70; SOT-23
J1, J2: BUS; PinSocket_2x20_P2.54mm_Vertical
TP1, TP2: Spare; PinSocket_2x20_P2.54mm_Vertical

Connections:
+3V3: D2.3 (K), D3.3 (K), D4.3 (K), D5.3 (K), D6.3 (K), D7.3 (K), D8.3 (K), D9.3 (K), D10.3 (K), D11.3 (K), J2.3, J2.4, TP2.3, TP2.4; also elsewhere on the board
+5V: J1.1, J1.2, TP1.1, TP1.2; also elsewhere on the board
+5VA: J2.39, J2.40, TP2.39, TP2.40; also elsewhere on the board
/A0: D4.1 (A), J1.19, TP1.19; also elsewhere on the board
/A1: D3.2 (A), J1.20, TP1.20; also elsewhere on the board
/A2: D3.1 (A), J1.21, TP1.21; also elsewhere on the board
/A3: D2.2 (A), J1.22, TP1.22; also elsewhere on the board
/A4: D2.1 (A), J1.23, TP1.23; also elsewhere on the board
/A5: D11.1 (A), J1.24, TP1.24; also elsewhere on the board
/A6: D11.2 (A), J1.25, TP1.25; also elsewhere on the board
/A7: D10.1 (A), J1.26, TP1.26; also elsewhere on the board
/A8: D10.2 (A), J1.27, TP1.27; also elsewhere on the board
/A9: D9.1 (A), J1.28, TP1.28; also elsewhere on the board
/A10: D9.2 (A), J1.29, TP1.29; also elsewhere on the board
/A11: D8.1 (A), J1.30, TP1.30; also elsewhere on the board
/A12: D8.2 (A), J1.31, TP1.31; also elsewhere on the board
/A13: D7.1 (A), J1.32, TP1.32; also elsewhere on the board
/A14: D7.2 (A), J1.33, TP1.33; also elsewhere on the board
/A15: D6.1 (A), J1.34, TP1.34; also elsewhere on the board
/A16: D6.2 (A), J1.35, TP1.35; also elsewhere on the board
/A17: D5.2 (A), J1.36, TP1.36; also elsewhere on the board
/A18: D5.1 (A), J1.37, TP1.37; also elsewhere on the board
/A19: D4.2 (A), J1.38, TP1.38; also elsewhere on the board
/CLK1: J2.25, TP2.25; also elsewhere on the board
/CLKF: J2.27, TP2.27; also elsewhere on the board
/CLKS: J2.28, TP2.28; also elsewhere on the board
/D0: J1.10, TP1.10; also elsewhere on the board
/D1: J1.11, TP1.11; also elsewhere on the board
/D2: J1.12, TP1.12; also elsewhere on the board
/D3: J1.13, TP1.13; also elsewhere on the board
/D4: J1.14, TP1.14; also elsewhere on the board
/D5: J1.15, TP1.15; also elsewhere on the board
/D6: J1.16, TP1.16; also elsewhere on the board
/D7: J1.17, TP1.17; also elsewhere on the board
/PH0: J2.30, TP2.30
/PHI1_e: J1.3, TP1.3
/PHI2_e: J1.4, TP1.4
/RES1: J2.24, TP2.24
/RES2: J2.21, TP2.21
/RES3: J2.22, TP2.22
/RES4: J2.19, TP2.19
/RES5: J2.20, TP2.20
/RX0: J2.36, TP2.36
/RX1: J2.34, TP2.34
/RXSTM: J2.38, TP2.38; also elsewhere on the board
/R/~W_e: J1.6, TP1.6; also elsewhere on the board
/SCL: J2.32, TP2.32; also elsewhere on the board
/SDA: J2.31, TP2.31; also elsewhere on the board
/TX0: J2.35, TP2.35
/TX1: J2.33, TP2.33
/TXSTM: J2.37, TP2.37; also elsewhere on the board
/~BUSFREE: J2.26, TP2.26; also elsewhere on the board
/~CE_EXT0: J2.6, TP2.6; also elsewhere on the board
/~CE_EXT1: J2.5, TP2.5; also elsewhere on the board
/~CE_EXT2: J2.8, TP2.8; also elsewhere on the board
/~CE_EXT3: J2.7, TP2.7; also elsewhere on the board
/~CE_EXT4: J2.10, TP2.10; also elsewhere on the board
/~CE_EXT5: J2.9, TP2.9; also elsewhere on the board
/~CE_EXT6: J2.12, TP2.12; also elsewhere on the board
/~CE_EXT7: J2.11, TP2.11; also elsewhere on the board
/~CE_EXT8: J2.14, TP2.14; also elsewhere on the board
/~CE_EXT9: J2.13, TP2.13; also elsewhere on the board
/~CE_EXT10: J2.16, TP2.16; also elsewhere on the board
/~CE_EXT11: J2.15, TP2.15; also elsewhere on the board
/~CE_EXT12: J2.18, TP2.18; also elsewhere on the board
/~CE_EXT13: J2.17, TP2.17; also elsewhere on the board
/~IORD: J1.5, TP1.5
/~IOWR: J1.9, TP1.9
/~MRD: J1.7, TP1.7; also elsewhere on the board
/~MWR: J1.8, TP1.8; also elsewhere on the board
/~PH0: J2.29, TP2.29
/~RST: J1.18, TP1.18; also elsewhere on the board
/~STM32BUS: J2.23, TP2.23; also elsewhere on the board
GND: J1.39, J1.40, J2.1, J2.2, TP1.39, TP1.40, TP2.1, TP2.2; also elsewhere on the board

Notes on the sheet:
5VA is always on, 5V is switched.

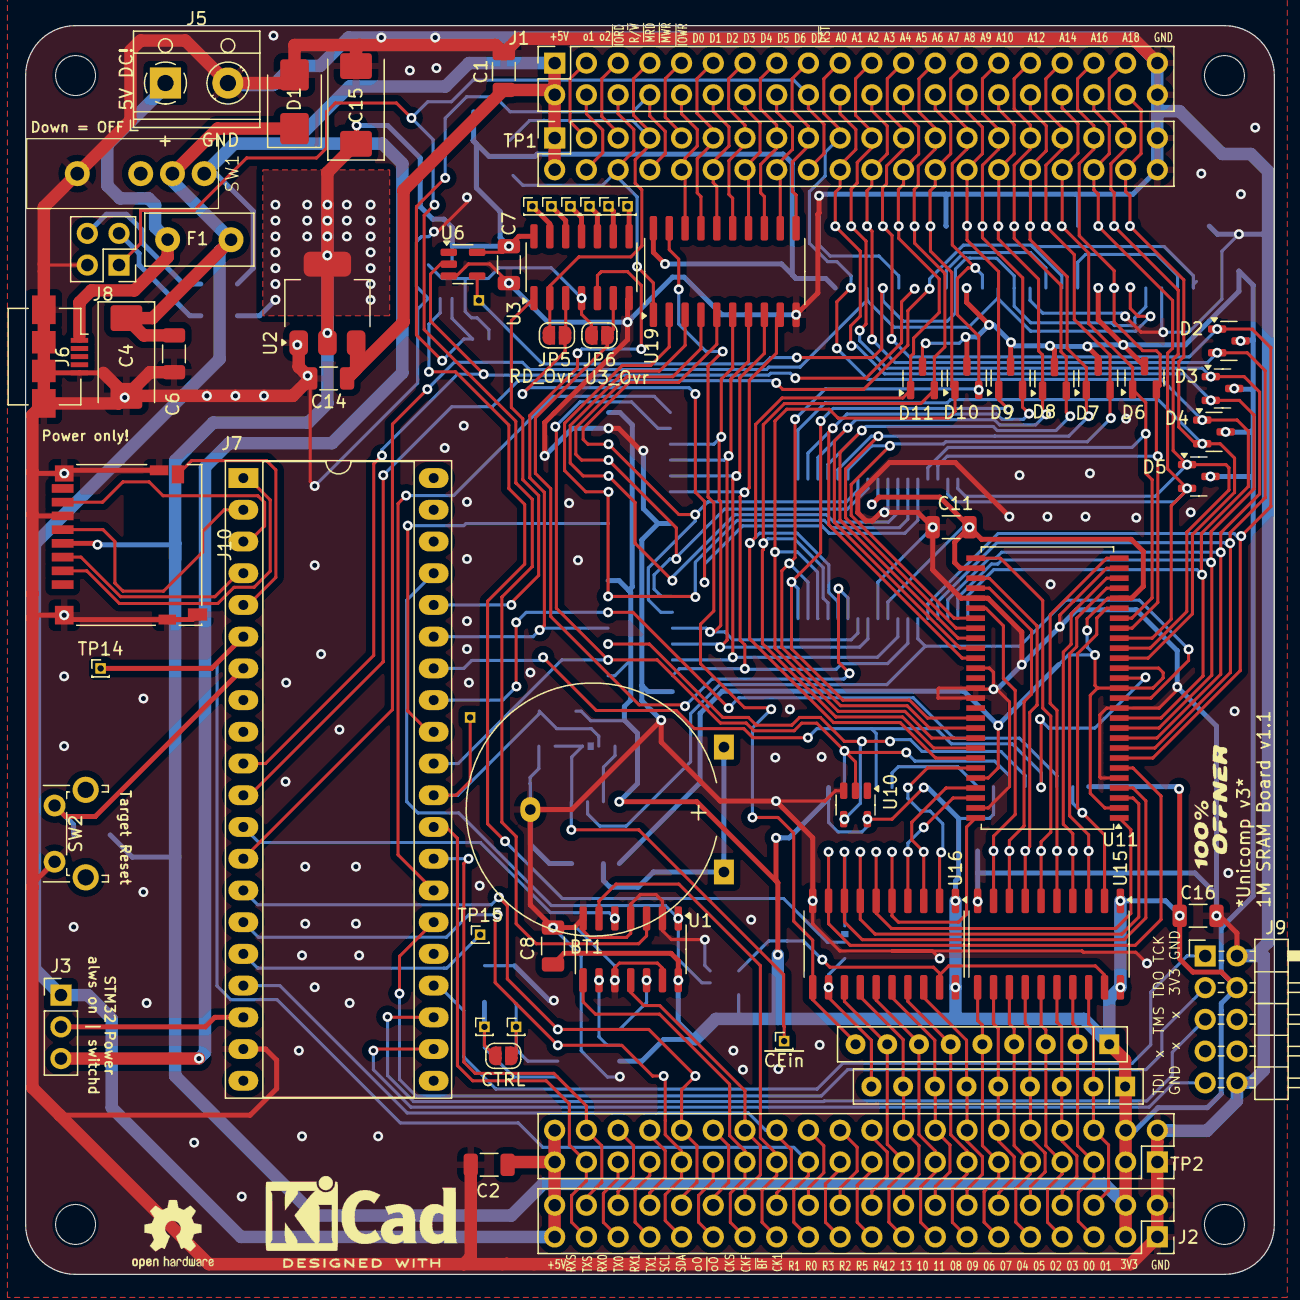
[picture p87: board RamRomBoard/schematics_v11/schematics_v11.kicad_pcb from above]

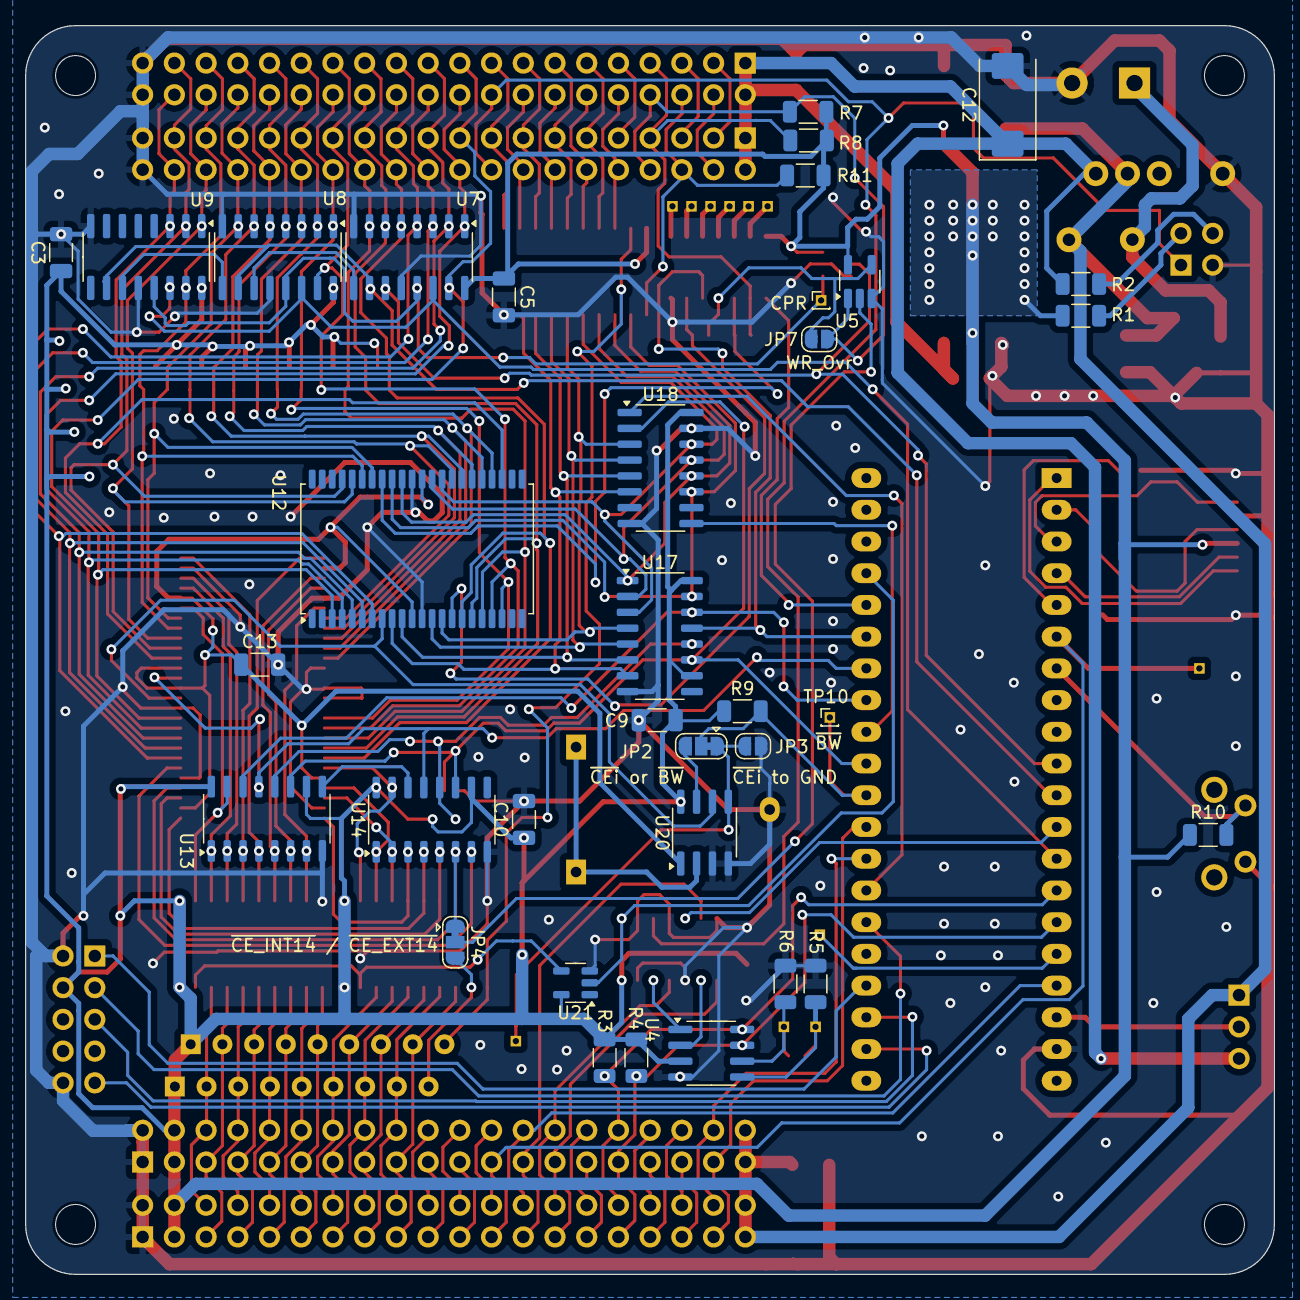
[picture p88: board RamRomBoard/schematics_v11/schematics_v11.kicad_pcb from below]

Board: 2 copper layers, 100.0 x 100.0 mm, 103 parts (35 on the bottom side), 153 nets.
