roberto314/Unicomp3/CPU_Boards/6502_6800_CPU/schematics_v10/6502_6800_CPU.kicad_pcb

## KiCad design CPU_Boards/6502_6800_CPU/schematics_v10/6502_6800_CPU.kicad_pcb (2024-10-24)

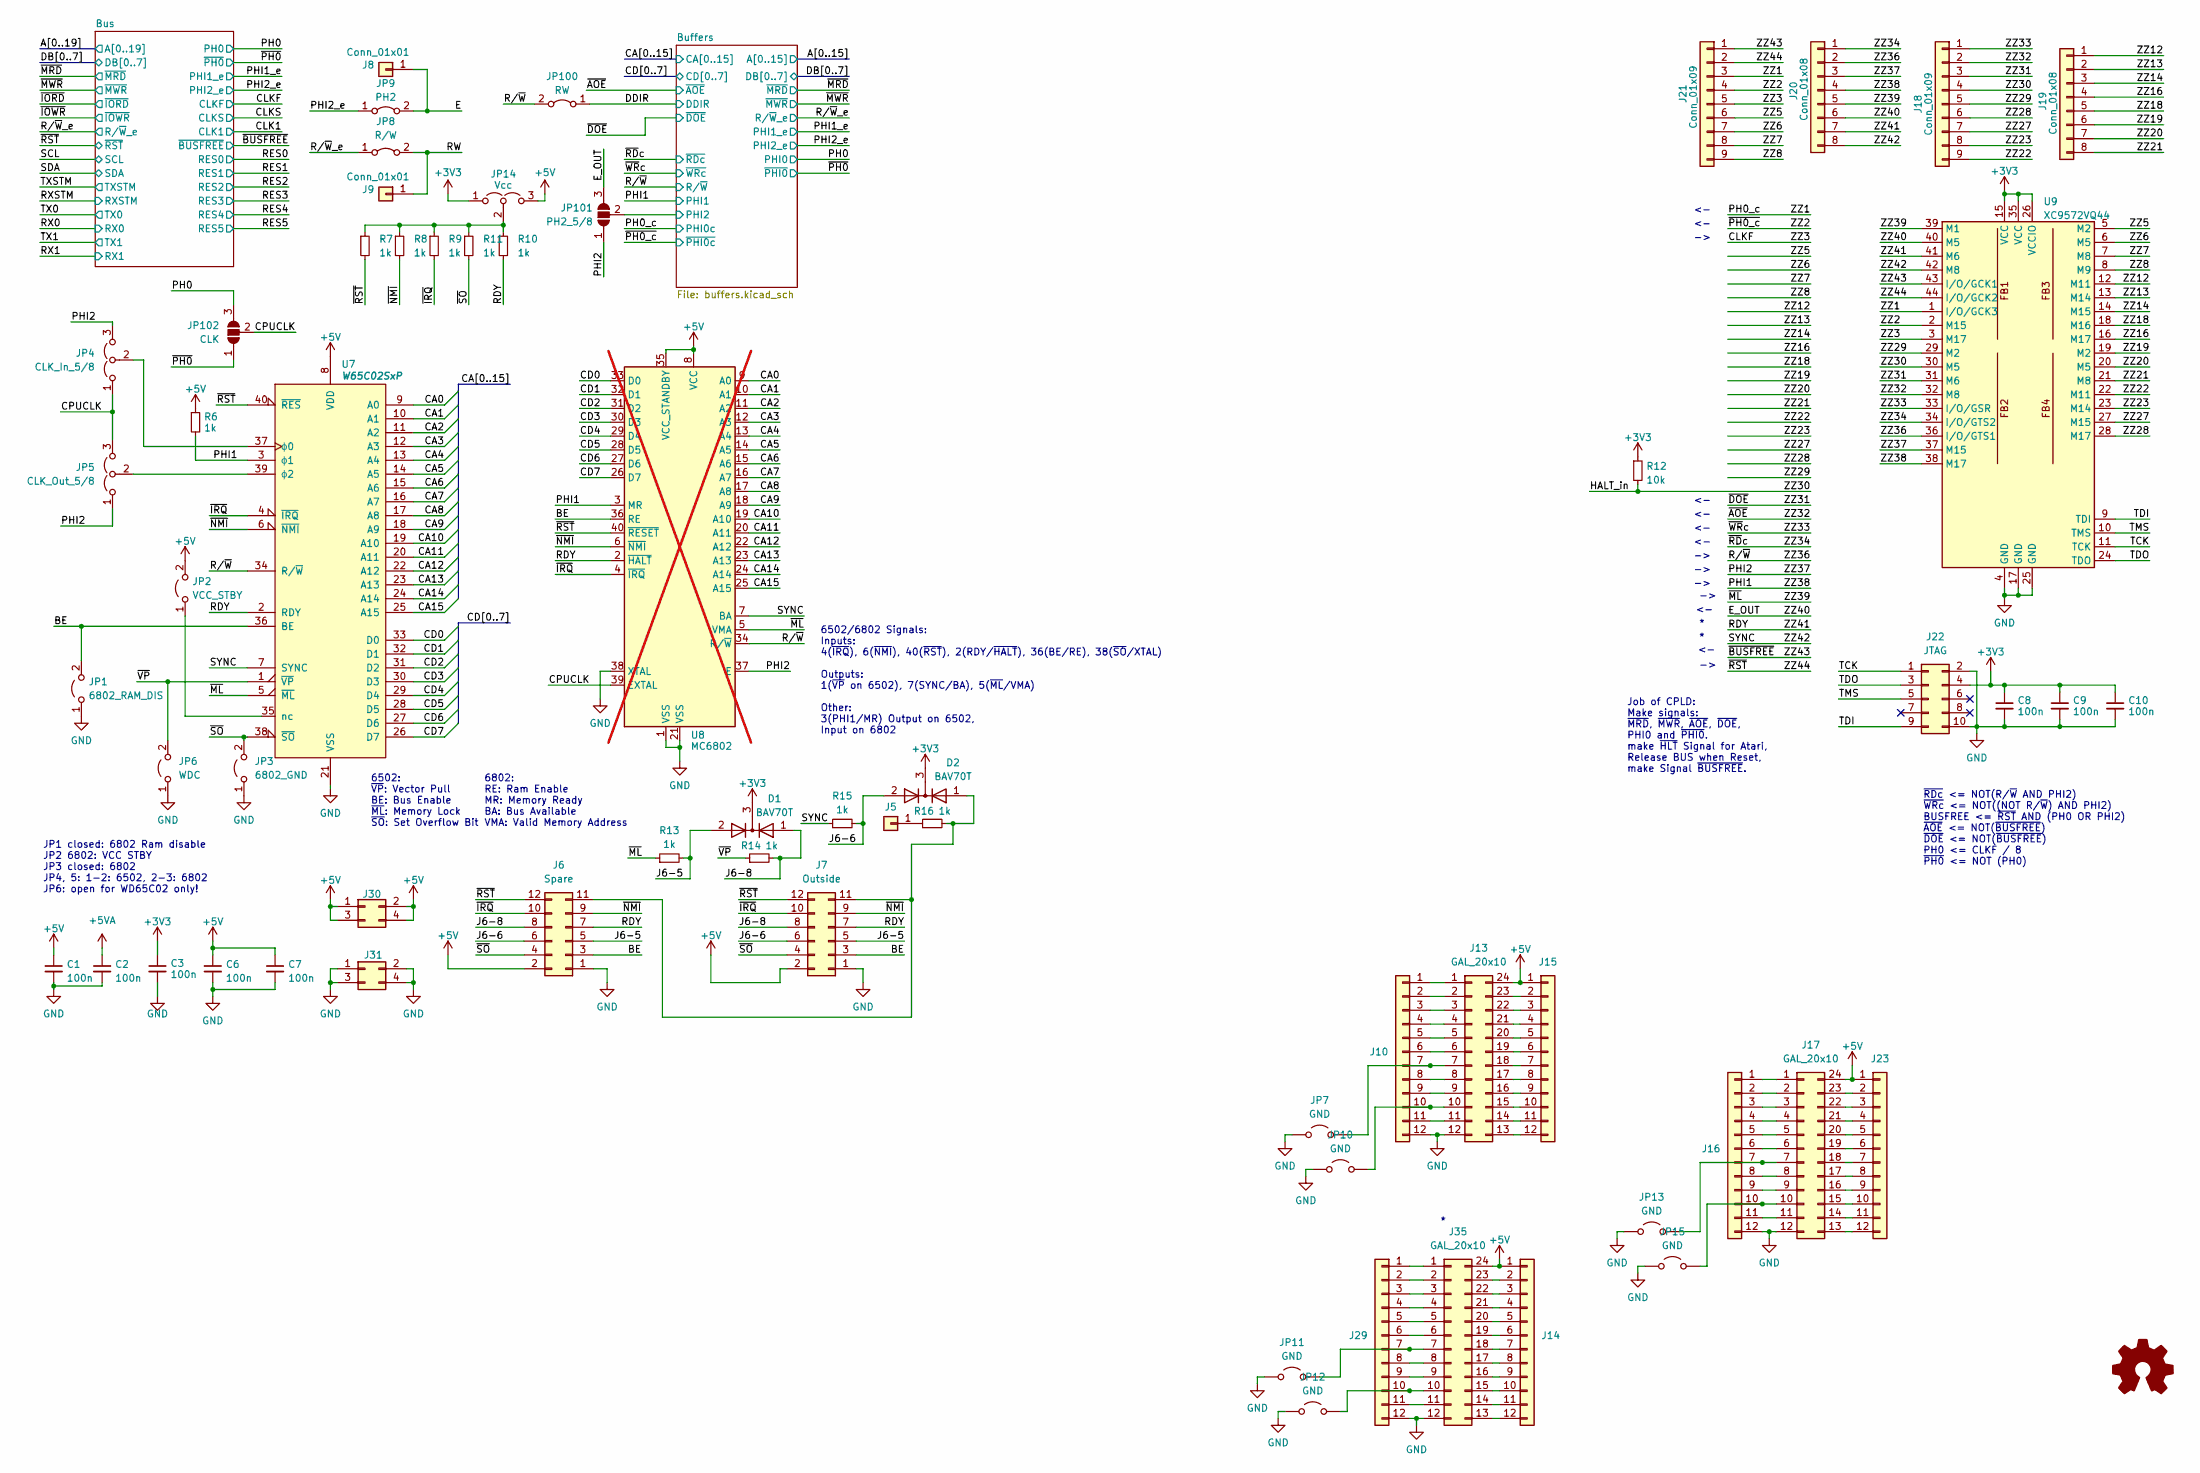
[picture p89: schematic 6502_6800_CPU.kicad_sch, Unicomp v3 - 6502/6800 CPU Board]

Parts:
C1, C2, C3, C6, C7, C8, C9, C10: 100n; C_1206_3216Metric
D1, D2: BAV70T; SOT-23_Handsoldering
J5: Conn_01x01; PinSocket_1x01_P1.27mm_Vertical
J6: Spare; PinHeader_2x06_P2.54mm_Vertical
J7: Outside; PinHeader_2x06_P2.54mm_Horizontal
J8, J9: Conn_01x01; PinHeader_1x01_P2.00mm_Vertical
J10, J14, J15, J16, J23, J29: Conn_01x12; PinSocket_1x12_P2.54mm_Vertical
J13, J17, J35: GAL_20x10; DIP-24_W7.62mm
J18, J21: Conn_01x09; PinHeader_1x09_P2.54mm_Vertical
J19, J20: Conn_01x08; PinHeader_1x08_P2.54mm_Vertical
J22: JTAG; PinHeader_2x05_P2.54mm_Horizontal
J30, J31: Conn_02x02_Odd_Even; PinSocket_2x02_P2.54mm_Vertical
JP1: 6802_RAM_DIS; SolderJumper-2_P1.3mm_Open_RoundedPad1.0x1.5mm
JP2: VCC_STBY; SolderJumper-2_P1.3mm_Open_RoundedPad1.0x1.5mm
JP3: 6802_GND; SolderJumper-2_P1.3mm_Open_RoundedPad1.0x1.5mm
JP4: CLK_In_5/8; SolderJumper-3_P1.3mm_Open_Pad1.0x1.5mm_NumberLabels
JP5: CLK_Out_5/8; SolderJumper-3_P1.3mm_Open_Pad1.0x1.5mm_NumberLabels
JP6: WDC; SolderJumper-2_P1.3mm_Open_RoundedPad1.0x1.5mm
JP7, JP10, JP11, JP12, JP13, JP15: GND; SolderJumper-2_P1.3mm_Open_RoundedPad1.0x1.5mm
JP8: R/W; SolderJumper-2_P1.3mm_Bridged_RoundedPad1.0x1.5mm
JP9: PH2; SolderJumper-2_P1.3mm_Bridged_RoundedPad1.0x1.5mm
JP14: Vcc; SolderJumper-3_P1.3mm_Open_RoundedPad1.0x1.5mm_NumberLabels
JP100: RW; SolderJumper-2_P1.3mm_Bridged_RoundedPad1.0x1.5mm
JP101: PH2_5/8; SolderJumper-3_P1.3mm_Open_RoundedPad1.0x1.5mm_NumberLabels
JP102: CLK; SolderJumper-3_P1.3mm_Open_RoundedPad1.0x1.5mm_NumberLabels
R6, R7, R8, R9, R10, R11, R13, R14, R15, R16: 1k; R_1206_3216Metric_Pad1.30x1.75mm_HandSolder
R12: 10k; R_1206_3216Metric_Pad1.30x1.75mm_HandSolder
U7: W65C02SxP; DIP-40_W15.24mm_Socket_LongPads
U8: MC6802; DIP-40_W15.24mm; not fitted
U9: XC9572VQ44; TQFP-44_10x10mm_P0.8mm

Connections:
+3V3: C3.1, C8.1, C9.1, C10.1, D1.3 (K), D2.3 (K), J22.4, JP14.1 (A), R12.1, U9.15 (VCC), U9.26 (VCCIO), U9.35 (VCC); also elsewhere on the board
+5V: C1.1, C6.1, C7.1, J6.2, J7.2, J13.24, J14.1, J15.1, J17.24, J23.1, J30.1, J30.2, J30.3, J30.4, J35.24, JP2.2 (B), JP14.3 (B), R6.1, U7.8 (VDD), U8.8 (VCC), U8.35 (VCC_STANDBY); also elsewhere on the board
+5VA: C2.1; also elsewhere on the board
/BE: J6.3, J7.3, JP1.2 (B), U7.36 (BE), U8.36 (RE)
/Buffers/PHI2: JP101.2 (C); also elsewhere on the board
/CA0: U7.9 (A0), U8.9 (A0); also elsewhere on the board
/CA1: U7.10 (A1), U8.10 (A1); also elsewhere on the board
/CA2: U7.11 (A2), U8.11 (A2); also elsewhere on the board
/CA3: U7.12 (A3), U8.12 (A3); also elsewhere on the board
/CA4: U7.13 (A4), U8.13 (A4); also elsewhere on the board
/CA5: U7.14 (A5), U8.14 (A5); also elsewhere on the board
/CA6: U7.15 (A6), U8.15 (A6); also elsewhere on the board
/CA7: U7.16 (A7), U8.16 (A7); also elsewhere on the board
/CA8: U7.17 (A8), U8.17 (A8); also elsewhere on the board
/CA9: U7.18 (A9), U8.18 (A9); also elsewhere on the board
/CA10: U7.19 (A10), U8.19 (A10); also elsewhere on the board
/CA11: U7.20 (A11), U8.20 (A11); also elsewhere on the board
/CA12: U7.22 (A12), U8.22 (A12); also elsewhere on the board
/CA13: U7.23 (A13), U8.23 (A13); also elsewhere on the board
/CA14: U7.24 (A14), U8.24 (A14); also elsewhere on the board
/CA15: U7.25 (A15), U8.25 (A15); also elsewhere on the board
/CD0: U7.33 (D0), U8.33 (D0); also elsewhere on the board
/CD1: U7.32 (D1), U8.32 (D1); also elsewhere on the board
/CD2: U7.31 (D2), U8.31 (D2); also elsewhere on the board
/CD3: U7.30 (D3), U8.30 (D3); also elsewhere on the board
/CD4: U7.29 (D4), U8.29 (D4); also elsewhere on the board
/CD5: U7.28 (D5), U8.28 (D5); also elsewhere on the board
/CD6: U7.27 (D6), U8.27 (D6); also elsewhere on the board
/CD7: U7.26 (D7), U8.26 (D7); also elsewhere on the board
/CLKF: J21.5, U9.3 (M17); also elsewhere on the board
/CPUCLK: JP4.1 (A), JP5.3 (B), JP102.2 (C), U8.39 (EXTAL)
/DDIR: JP100.1 (A); also elsewhere on the board
/E: J8.1, JP9.2 (B)
/E_OUT: J20.6, JP101.3 (B), U9.40 (M5)
/HALT_in: J18.4, R12.2, U9.30 (M5)
/J6-5: D1.2 (A), J6.5, J7.5, R13.2
/J6-6: D2.2 (A), J6.6, J7.6, R15.2
/J6-8: D1.1 (A), J6.8, J7.8, R14.2
/PH0: JP102.3 (B); also elsewhere on the board
/PH0_c: J21.3, U9.1 (I/O/GCK3); also elsewhere on the board
/PHI1: J20.4, R6.2, U7.3 (ϕ1), U8.3 (MR), U9.38 (M17); also elsewhere on the board
/PHI2: J20.3, JP4.3 (B), JP5.1 (A), JP101.1 (A), U8.37 (E), U9.37 (M15)
/PHI2_e: JP9.1 (A); also elsewhere on the board
/RDY: J6.7, J7.7, J20.7, R10.2, U7.2 (RDY), U8.2 (~HALT), U9.41 (M6)
/RW: J9.1, JP8.2 (B)
/R/~W: J20.2, JP100.2 (B), U7.34 (R/~W), U8.34 (R/~W), U9.36 (I/O/GTS1); also elsewhere on the board
/R/~W_e: JP8.1 (A); also elsewhere on the board
/SYNC: J20.8, R15.1, U7.7 (SYNC), U8.7 (BA), U9.42 (M8)
/TCK: J22.1, U9.11 (TCK)
/TDI: J22.9, U9.9 (TDI)
/TDO: J22.3, U9.24 (TDO)
/TMS: J22.5, U9.10 (TMS)
/ZZ2: J21.4, U9.2 (M15); also elsewhere on the board
/ZZ5: J21.6, U9.5 (M2)
/ZZ6: J21.7, U9.6 (M5)
/ZZ7: J21.8, U9.7 (M8)
/ZZ8: J21.9, U9.8 (M9)
/ZZ12: J19.1, U9.12 (M11)
/ZZ13: J19.2, U9.13 (M14)
/ZZ14: J19.3, U9.14 (M15)
/ZZ16: J19.4, U9.16 (M17)
/ZZ18: J19.5, U9.18 (M16)
/ZZ19: J19.6, U9.19 (M2)
/ZZ20: J19.7, U9.20 (M5)
/ZZ21: J19.8, U9.21 (M8)
/ZZ22: J18.9, U9.22 (M11)
/ZZ23: J18.8, U9.23 (M14)
/ZZ27: J18.7, U9.27 (M15)
/ZZ28: J18.6, U9.28 (M17)
/ZZ29: J18.5, U9.29 (M2)
/ZZ31: J18.3, U9.31 (M6); also elsewhere on the board
/ZZ32: J18.2, U9.32 (M8); also elsewhere on the board
/ZZ33: J18.1, U9.33 (I/O/GSR); also elsewhere on the board
/ZZ34: J20.1, U9.34 (I/O/GTS2); also elsewhere on the board
/ZZ39: J20.5, R13.1, U7.5 (~ML), U8.5 (VMA), U9.39 (M1)
/ZZ43: J21.1, U9.43 (I/O/GCK1); also elsewhere on the board
/ZZ44: J6.12, J7.12, J21.2, R7.2, U7.40 (~RES), U8.40 (~RESET), U9.44 (I/O/GCK2); also elsewhere on the board
/~IRQ: J6.10, J7.10, R9.2, U7.4 (~IRQ), U8.4 (~IRQ)
/~NMI: J6.9, J7.9, R8.2, U7.6 (~NMI), U8.6 (~NMI)
/~PH0: JP102.1 (A); also elsewhere on the board
/~SO: J6.4, J7.4, JP3.2 (B), R11.2, U7.38 (~SO)
/~VP: JP6.2 (B), R14.1, U7.1 (~VP)
GND: C1.2, C2.2, C3.2, C6.2, C7.2, C8.2, C9.2, C10.2, J6.1, J7.1, J10.12, J13.12, J16.12, J17.12, J22.2, J22.10, J29.12, J31.1, J31.2, J31.3, J31.4, J35.12, JP1.1 (A), JP3.1 (A), JP6.1 (A), JP7.1 (A), JP10.1 (A), JP11.1 (A), JP12.1 (A), JP13.1 (A), JP15.1 (A), U7.21 (VSS), U8.1 (VSS), U8.21 (VSS), U8.38 (XTAL), U9.4 (GND), U9.17 (GND), U9.25 (GND); also elsewhere on the board
unnamed: J5.1, R16.1
unnamed: D2.1 (A), J6.11, J7.11, R16.2
unnamed: J10.1, J13.1
unnamed: J10.2, J13.2
unnamed: J10.3, J13.3
unnamed: J10.4, J13.4
unnamed: J10.5, J13.5
unnamed: J10.6, J13.6
unnamed: J10.7, J13.7, JP7.2 (B)
unnamed: J10.8, J13.8
unnamed: J10.9, J13.9
unnamed: J10.10, J13.10, JP10.2 (B)
unnamed: J10.11, J13.11
unnamed: J13.13, J15.12
unnamed: J13.14, J15.11
unnamed: J13.15, J15.10
unnamed: J13.16, J15.9
unnamed: J13.17, J15.8
unnamed: J13.18, J15.7
unnamed: J13.19, J15.6
unnamed: J13.20, J15.5
unnamed: J13.21, J15.4
unnamed: J13.22, J15.3
unnamed: J13.23, J15.2
unnamed: J14.2, J35.23
unnamed: J14.3, J35.22
unnamed: J14.4, J35.21
unnamed: J14.5, J35.20
unnamed: J14.6, J35.19
unnamed: J14.7, J35.18
unnamed: J14.8, J35.17
unnamed: J14.9, J35.16
unnamed: J14.10, J35.15
unnamed: J14.11, J35.14
unnamed: J14.12, J35.13
unnamed: J16.1, J17.1
unnamed: J16.2, J17.2
unnamed: J16.3, J17.3
unnamed: J16.4, J17.4
unnamed: J16.5, J17.5
unnamed: J16.6, J17.6
unnamed: J16.7, J17.7, JP13.2 (B)
unnamed: J16.8, J17.8
unnamed: J16.9, J17.9
unnamed: J16.10, J17.10, JP15.2 (B)
unnamed: J16.11, J17.11
unnamed: J17.13, J23.12
unnamed: J17.14, J23.11
unnamed: J17.15, J23.10
unnamed: J17.16, J23.9
unnamed: J17.17, J23.8
unnamed: J17.18, J23.7
unnamed: J17.19, J23.6
unnamed: J17.20, J23.5
unnamed: J17.21, J23.4
unnamed: J17.22, J23.3
unnamed: J17.23, J23.2
unnamed: J29.1, J35.1
unnamed: J29.2, J35.2
unnamed: J29.3, J35.3
unnamed: J29.4, J35.4
unnamed: J29.5, J35.5
unnamed: J29.6, J35.6
unnamed: J29.7, J35.7, JP11.2 (B)
unnamed: J29.8, J35.8
unnamed: J29.9, J35.9
unnamed: J29.10, J35.10, JP12.2 (B)
unnamed: J29.11, J35.11
unnamed: JP2.1 (A), U7.35 (nc)
unnamed: JP4.2 (C), U7.37 (ϕ0)
unnamed: JP5.2 (C), U7.39 (ϕ2)
unnamed: JP14.2 (C), R7.1, R8.1, R9.1, R10.1, R11.1

Notes on the sheet:
6502/6802 Signals: Inputs: 4(~{IRQ}), 6(~{NMI}), 40(~{RST}), 2(RDY/~{HALT}), 36(BE/RE), 38(~{SO}/XTAL) Outputs: 1(~{VP} on 6502), 7(SYNC/BA), 5(~{ML}/VMA) Other: 3(PHI1/MR) Output on 6502, Input on 6802
JP1 closed: 6802 Ram disable JP2 6802: VCC STBY JP3 closed: 6802 JP4, 5: 1-2: 6502, 2-3: 6802 JP6: open for WD65C02 only!
6502: ~{VP}: Vector Pull BE: Bus Enable ~{ML}: Memory Lock ~{SO}: Set Overflow Bit
Job of CPLD: Make signals: ~{MRD}, ~{MWR}, ~{AOE}, ~{DOE}, PHI0 and ~{PHI0}. make ~{HLT} Signal for Atari, Release BUS when Reset, make Signal ~{BUSFREE}.
~{RDc} <= NOT(R/~{W} AND PHI2) ~{WRc} <= NOT((NOT R/~{W}) AND PHI2) BUSFREE <= ~{RST} AND (PH0 OR PHI2) ~{AOE} <= NOT(~{BUSFREE}) ~{DOE} <= NOT(~{BUSFREE}) PH0 <= CLKF / 8 ~{PH0} <= NOT (PH0)
6802: RE: Ram Enable MR: Memory Ready BA: Bus Available VMA: Valid Memory Address

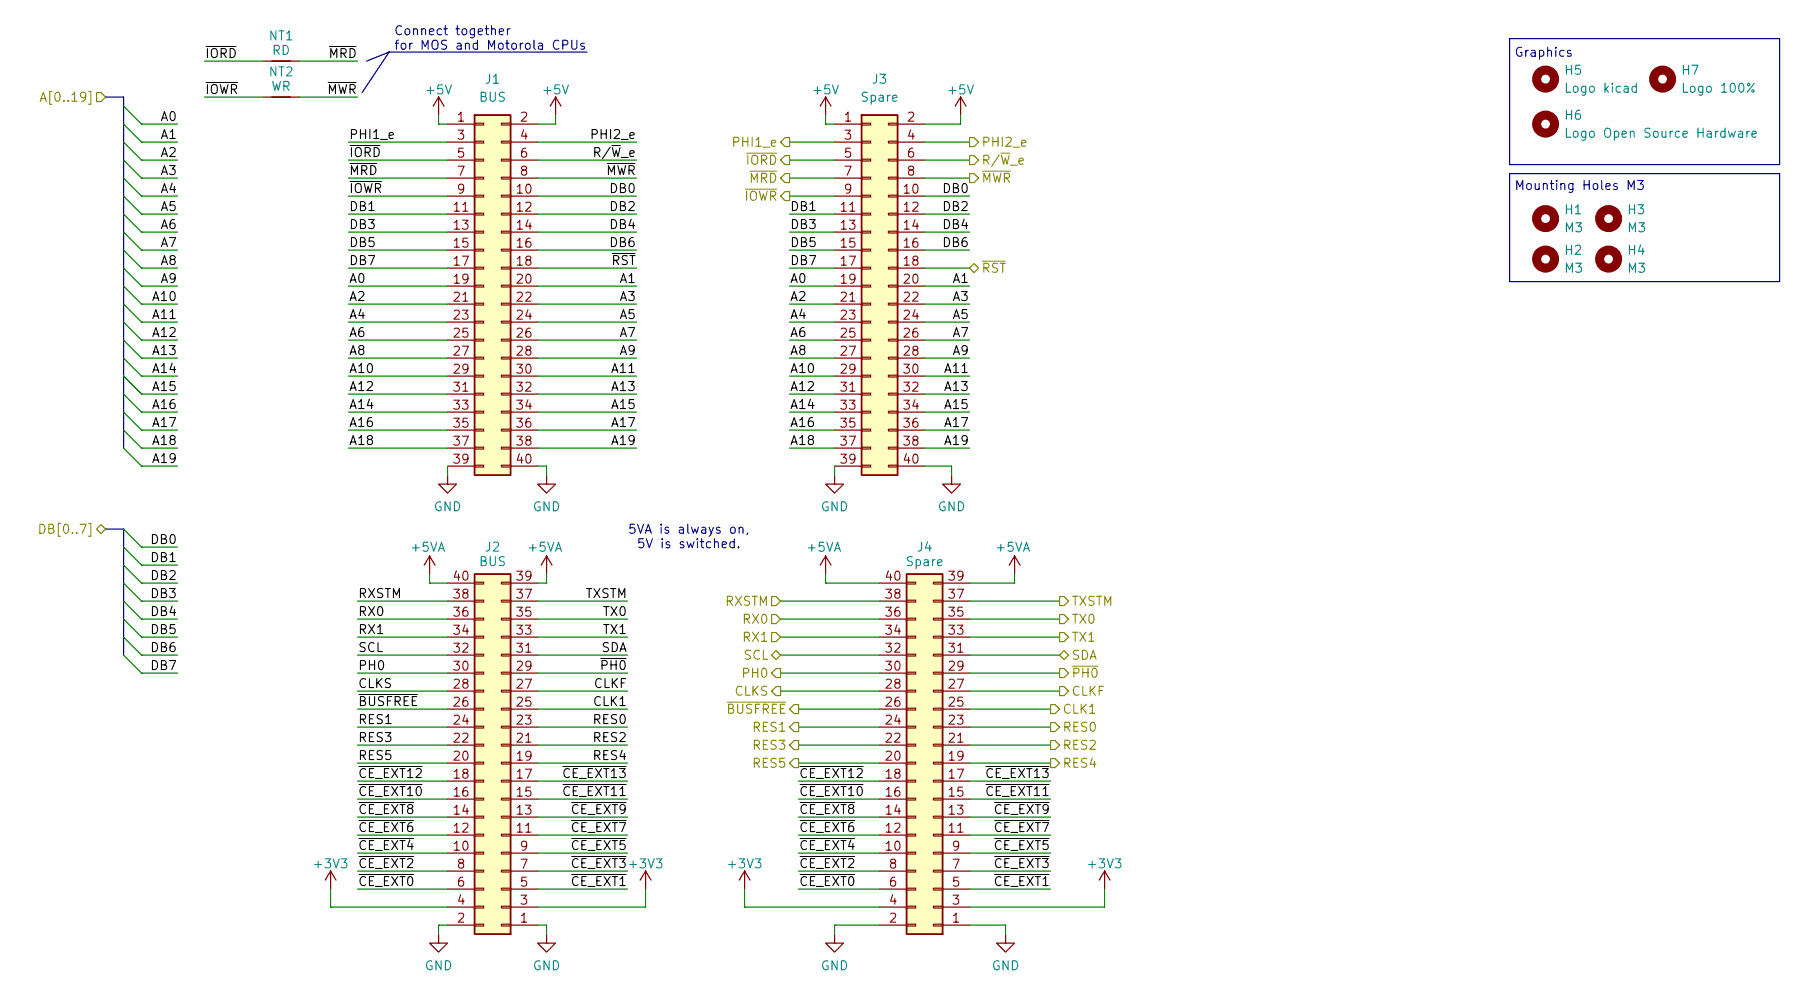
[picture p90: schematic bus.kicad_sch, Unicomp v3 - Bus]

Parts:
H1, H2, H3, H4: M3; MountingHole_3.2mm_M3
H5: Logo kicad; KiCad-Logo2_6mm_SilkScreen
H6: Logo Open Source Hardware; OSHW-Logo2_7.3x6mm_SilkScreen
H7: Logo 100%; Logo_100ProzentOffner_10x2.7mm
J1, J2: BUS; PinSocket_2x20_P2.54mm_Vertical
J3, J4: Spare; PinSocket_2x20_P2.54mm_Vertical
NT1: RD; NetTie-2_SMD_Pad0.5mm
NT2: WR; NetTie-2_SMD_Pad0.5mm

Connections:
+3V3: J2.3, J2.4, J4.3, J4.4; also elsewhere on the board
+5V: J1.1, J1.2, J3.1, J3.2; also elsewhere on the board
+5VA: J2.39, J2.40, J4.39, J4.40; also elsewhere on the board
/A0: J1.19, J3.19; also elsewhere on the board
/A1: J1.20, J3.20; also elsewhere on the board
/A2: J1.21, J3.21; also elsewhere on the board
/A3: J1.22, J3.22; also elsewhere on the board
/A4: J1.23, J3.23; also elsewhere on the board
/A5: J1.24, J3.24; also elsewhere on the board
/A6: J1.25, J3.25; also elsewhere on the board
/A7: J1.26, J3.26; also elsewhere on the board
/A8: J1.27, J3.27; also elsewhere on the board
/A9: J1.28, J3.28; also elsewhere on the board
/A10: J1.29, J3.29; also elsewhere on the board
/A11: J1.30, J3.30; also elsewhere on the board
/A12: J1.31, J3.31; also elsewhere on the board
/A13: J1.32, J3.32; also elsewhere on the board
/A14: J1.33, J3.33; also elsewhere on the board
/A15: J1.34, J3.34; also elsewhere on the board
/A16: J1.35, J3.35
/A17: J1.36, J3.36
/A18: J1.37, J3.37
/A19: J1.38, J3.38
/Bus/~CE_EXT0: J2.6, J4.6
/Bus/~CE_EXT1: J2.5, J4.5
/Bus/~CE_EXT2: J2.8, J4.8
/Bus/~CE_EXT3: J2.7, J4.7
/Bus/~CE_EXT4: J2.10, J4.10
/Bus/~CE_EXT5: J2.9, J4.9
/Bus/~CE_EXT6: J2.12, J4.12
/Bus/~CE_EXT7: J2.11, J4.11
/Bus/~CE_EXT8: J2.14, J4.14
/Bus/~CE_EXT9: J2.13, J4.13
/Bus/~CE_EXT10: J2.16, J4.16
/Bus/~CE_EXT11: J2.15, J4.15
/Bus/~CE_EXT12: J2.18, J4.18
/Bus/~CE_EXT13: J2.17, J4.17
/CLK1: J2.25, J4.25
/CLKF: J2.27, J4.27; also elsewhere on the board
/CLKS: J2.28, J4.28
/DB0: J1.10, J3.10; also elsewhere on the board
/DB1: J1.11, J3.11; also elsewhere on the board
/DB2: J1.12, J3.12; also elsewhere on the board
/DB3: J1.13, J3.13; also elsewhere on the board
/DB4: J1.14, J3.14; also elsewhere on the board
/DB5: J1.15, J3.15; also elsewhere on the board
/DB6: J1.16, J3.16; also elsewhere on the board
/DB7: J1.17, J3.17; also elsewhere on the board
/PH0: J2.30, J4.30; also elsewhere on the board
/PHI1_e: J1.3, J3.3; also elsewhere on the board
/PHI2_e: J1.4, J3.4; also elsewhere on the board
/RES0: J2.23, J4.23
/RES1: J2.24, J4.24
/RES2: J2.21, J4.21
/RES3: J2.22, J4.22
/RES4: J2.19, J4.19
/RES5: J2.20, J4.20
/RX0: J2.36, J4.36
/RX1: J2.34, J4.34
/RXSTM: J2.38, J4.38
/R/~W_e: J1.6, J3.6; also elsewhere on the board
/SCL: J2.32, J4.32
/SDA: J2.31, J4.31
/TX0: J2.35, J4.35
/TX1: J2.33, J4.33
/TXSTM: J2.37, J4.37
/ZZ43: J2.26, J4.26; also elsewhere on the board
/ZZ44: J1.18, J3.18; also elsewhere on the board
/~IORD: J1.5, J3.5, NT1.1
/~IOWR: J1.9, J3.9, NT2.1
/~MRD: J1.7, J3.7, NT1.2; also elsewhere on the board
/~MWR: J1.8, J3.8, NT2.2; also elsewhere on the board
/~PH0: J2.29, J4.29; also elsewhere on the board
GND: J1.39, J1.40, J2.1, J2.2, J3.39, J3.40, J4.1, J4.2; also elsewhere on the board

Notes on the sheet:
Graphics
Connect together for MOS and Motorola CPUs
5VA is always on, 5V is switched.
Mounting Holes M3

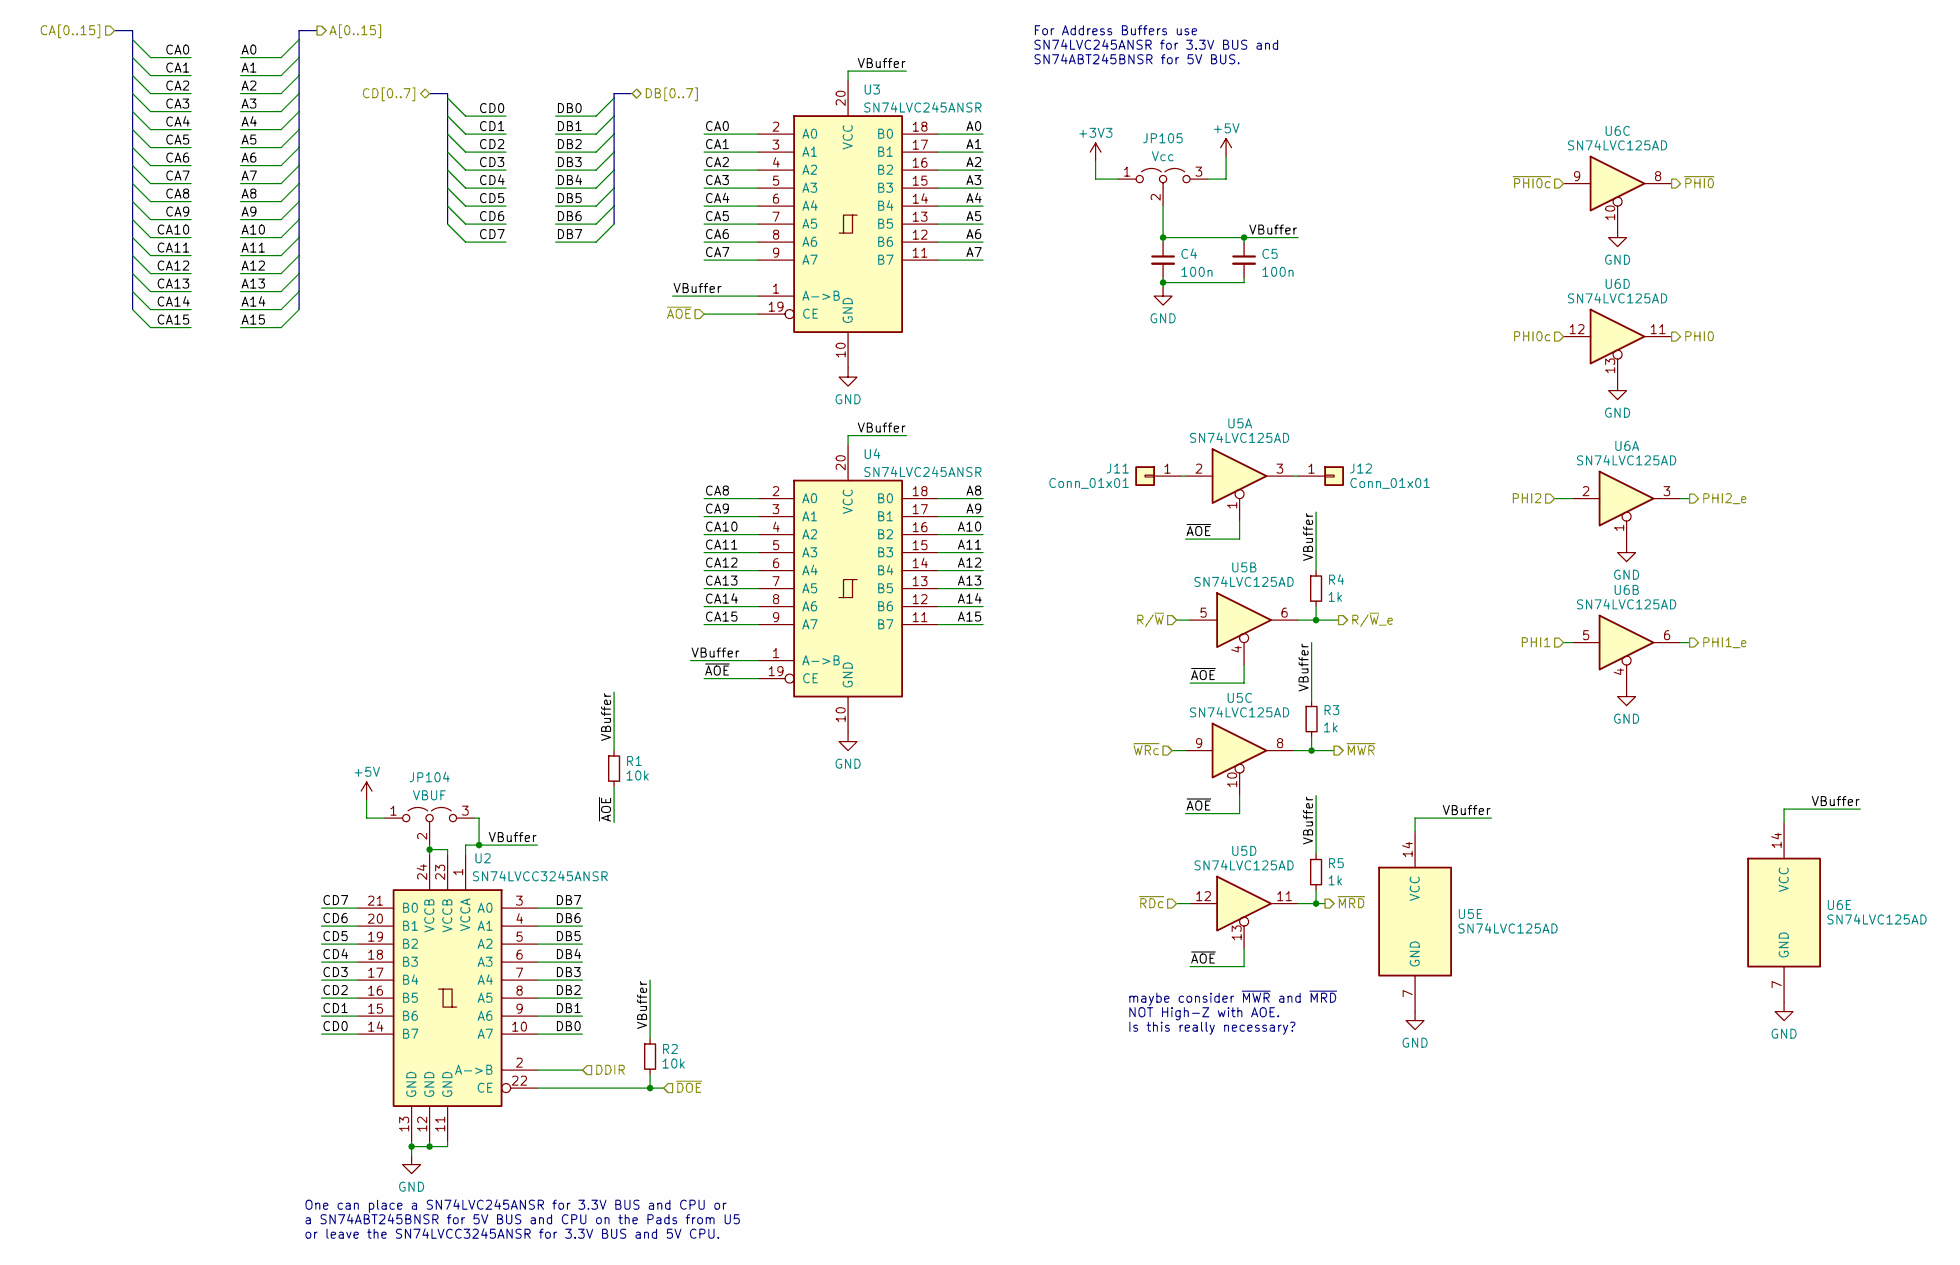
[picture p91: schematic buffers.kicad_sch, Unicomp v3 - Buffers]

Parts:
C4, C5: 100n; C_1206_3216Metric
J11, J12: Conn_01x01; PinHeader_1x01_P1.27mm_Vertical
JP104: VBUF; SolderJumper-3_P1.3mm_Open_Pad1.0x1.5mm_NumberLabels
JP105: Vcc; SolderJumper-3_P1.3mm_Open_RoundedPad1.0x1.5mm_NumberLabels
R1, R2: 10k; R_1206_3216Metric_Pad1.30x1.75mm_HandSolder
R3, R4, R5: 1k; R_1206_3216Metric_Pad1.30x1.75mm_HandSolder
U2: SN74LVCC3245ANSR; SO-24_5.3x15mm_P1.27mm
U3, U4: SN74LVC245ANSR; SO-20_5.3x12.6mm_P1.27mm
U5, U6: SN74LVC125AD; SOIC-14_3.9x8.7mm_P1.27mm

Connections:
+3V3: JP105.1 (A); also elsewhere on the board
+5V: JP104.1 (A), JP105.3 (B); also elsewhere on the board
/A0: U3.18 (B0); also elsewhere on the board
/A1: U3.17 (B1); also elsewhere on the board
/A2: U3.16 (B2); also elsewhere on the board
/A3: U3.15 (B3); also elsewhere on the board
/A4: U3.14 (B4); also elsewhere on the board
/A5: U3.13 (B5); also elsewhere on the board
/A6: U3.12 (B6); also elsewhere on the board
/A7: U3.11 (B7); also elsewhere on the board
/A8: U4.18 (B0); also elsewhere on the board
/A9: U4.17 (B1); also elsewhere on the board
/A10: U4.16 (B2); also elsewhere on the board
/A11: U4.15 (B3); also elsewhere on the board
/A12: U4.14 (B4); also elsewhere on the board
/A13: U4.13 (B5); also elsewhere on the board
/A14: U4.12 (B6); also elsewhere on the board
/A15: U4.11 (B7); also elsewhere on the board
/Buffers/PHI2: U6.2; also elsewhere on the board
/Buffers/VBuffer: C4.1, C5.1, JP104.3 (B), JP105.2 (C), R1.1, R2.1, R3.1, R4.1, R5.1, U2.1 (VCCA), U3.1 (A->B), U3.20 (VCC), U4.1 (A->B), U4.20 (VCC), U5.14 (VCC), U6.14 (VCC)
/CA0: U3.2 (A0); also elsewhere on the board
/CA1: U3.3 (A1); also elsewhere on the board
/CA2: U3.4 (A2); also elsewhere on the board
/CA3: U3.5 (A3); also elsewhere on the board
/CA4: U3.6 (A4); also elsewhere on the board
/CA5: U3.7 (A5); also elsewhere on the board
/CA6: U3.8 (A6); also elsewhere on the board
/CA7: U3.9 (A7); also elsewhere on the board
/CA8: U4.2 (A0); also elsewhere on the board
/CA9: U4.3 (A1); also elsewhere on the board
/CA10: U4.4 (A2); also elsewhere on the board
/CA11: U4.5 (A3); also elsewhere on the board
/CA12: U4.6 (A4); also elsewhere on the board
/CA13: U4.7 (A5); also elsewhere on the board
/CA14: U4.8 (A6); also elsewhere on the board
/CA15: U4.9 (A7); also elsewhere on the board
/CD0: U2.14 (B7); also elsewhere on the board
/CD1: U2.15 (B6); also elsewhere on the board
/CD2: U2.16 (B5); also elsewhere on the board
/CD3: U2.17 (B4); also elsewhere on the board
/CD4: U2.18 (B3); also elsewhere on the board
/CD5: U2.19 (B2); also elsewhere on the board
/CD6: U2.20 (B1); also elsewhere on the board
/CD7: U2.21 (B0); also elsewhere on the board
/DB0: U2.10 (A7); also elsewhere on the board
/DB1: U2.9 (A6); also elsewhere on the board
/DB2: U2.8 (A5); also elsewhere on the board
/DB3: U2.7 (A4); also elsewhere on the board
/DB4: U2.6 (A3); also elsewhere on the board
/DB5: U2.5 (A2); also elsewhere on the board
/DB6: U2.4 (A1); also elsewhere on the board
/DB7: U2.3 (A0); also elsewhere on the board
/DDIR: U2.2 (A->B); also elsewhere on the board
/PH0: U6.11; also elsewhere on the board
/PH0_c: U6.12; also elsewhere on the board
/PHI1: U6.5; also elsewhere on the board
/PHI1_e: U6.6; also elsewhere on the board
/PHI2_e: U6.3; also elsewhere on the board
/R/~W: U5.5; also elsewhere on the board
/R/~W_e: R4.2, U5.6; also elsewhere on the board
/ZZ2: U6.9; also elsewhere on the board
/ZZ31: R2.2, U2.22 (CE); also elsewhere on the board
/ZZ32: R1.2, U3.19 (CE), U4.19 (CE), U5.1, U5.4, U5.10, U5.13; also elsewhere on the board
/ZZ33: U5.9; also elsewhere on the board
/ZZ34: U5.12; also elsewhere on the board
/~MRD: R5.2, U5.11; also elsewhere on the board
/~MWR: R3.2, U5.8; also elsewhere on the board
/~PH0: U6.8; also elsewhere on the board
GND: C4.2, C5.2, U2.11 (GND), U2.12 (GND), U2.13 (GND), U3.10 (GND), U4.10 (GND), U5.7 (GND), U6.1, U6.4, U6.7 (GND), U6.10, U6.13; also elsewhere on the board
unnamed: J11.1, U5.2
unnamed: J12.1, U5.3
unnamed: JP104.2 (C), U2.23 (VCCB), U2.24 (VCCB)

Notes on the sheet:
For Address Buffers use SN74LVC245ANSR for 3.3V BUS and SN74ABT245BNSR for 5V BUS.
One can place a SN74LVC245ANSR for 3.3V BUS and CPU or a SN74ABT245BNSR for 5V BUS and CPU on the Pads from U5 or leave the SN74LVCC3245ANSR for 3.3V BUS and 5V CPU.
maybe consider ~{MWR} and ~{MRD} NOT High-Z with AOE. Is this really necessary?

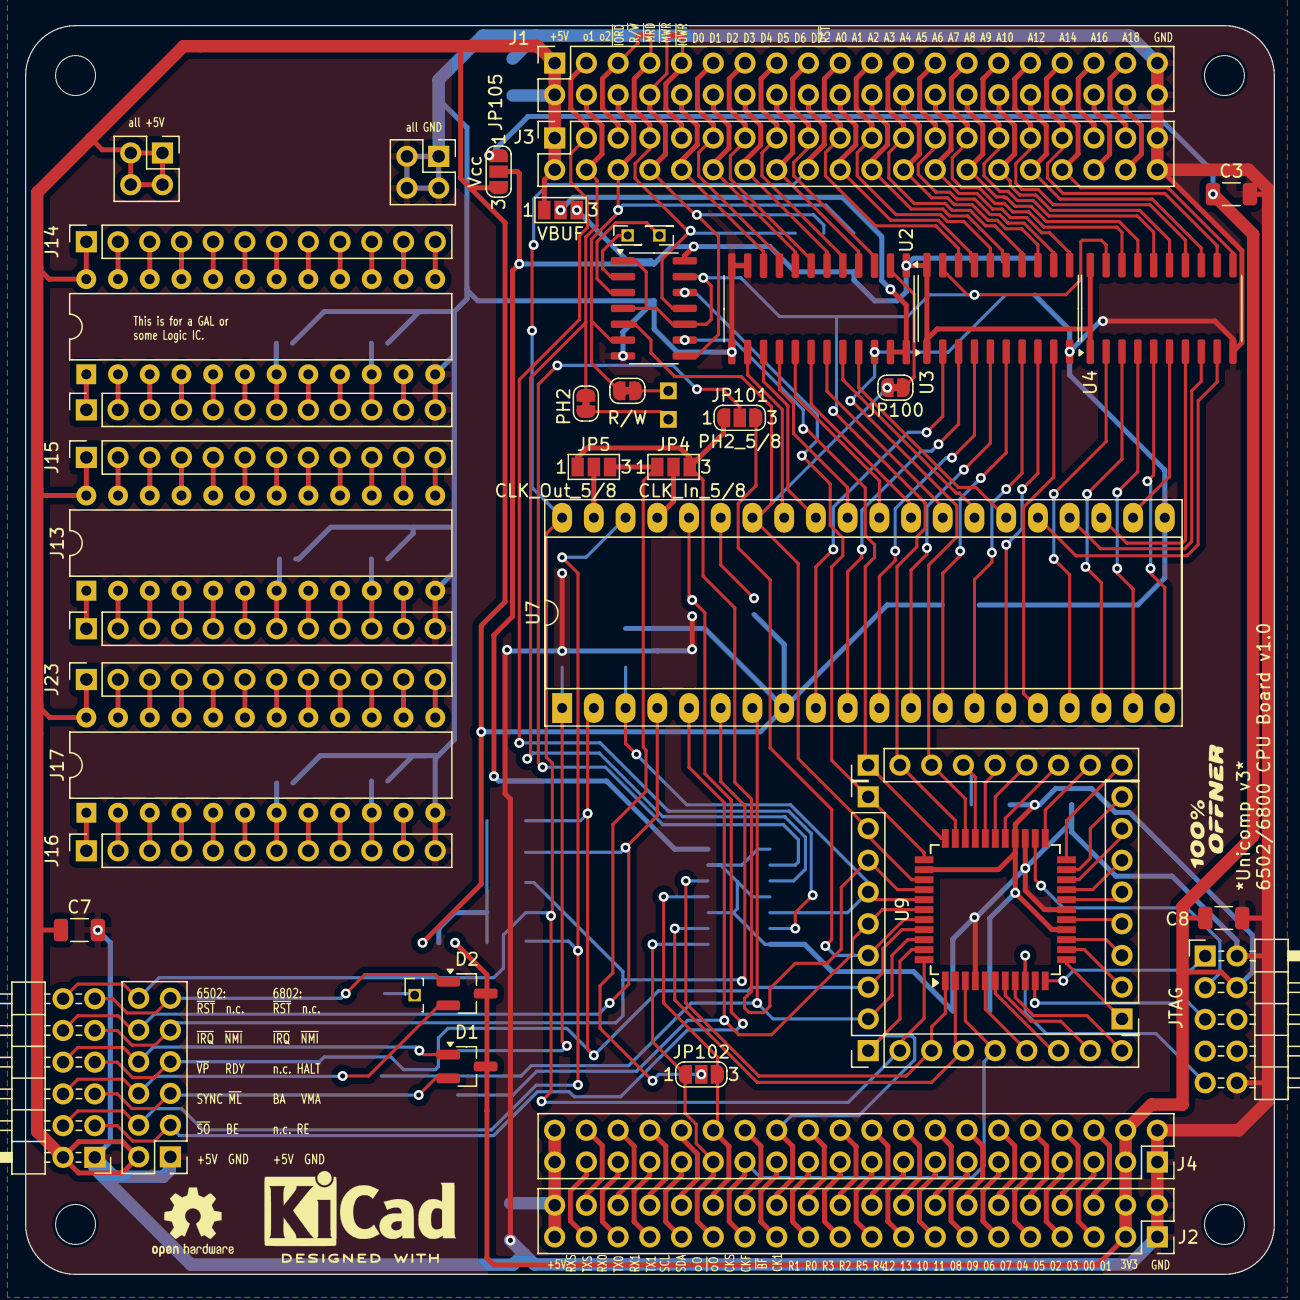
[picture p92: board 6502_6800_CPU.kicad_pcb from above]

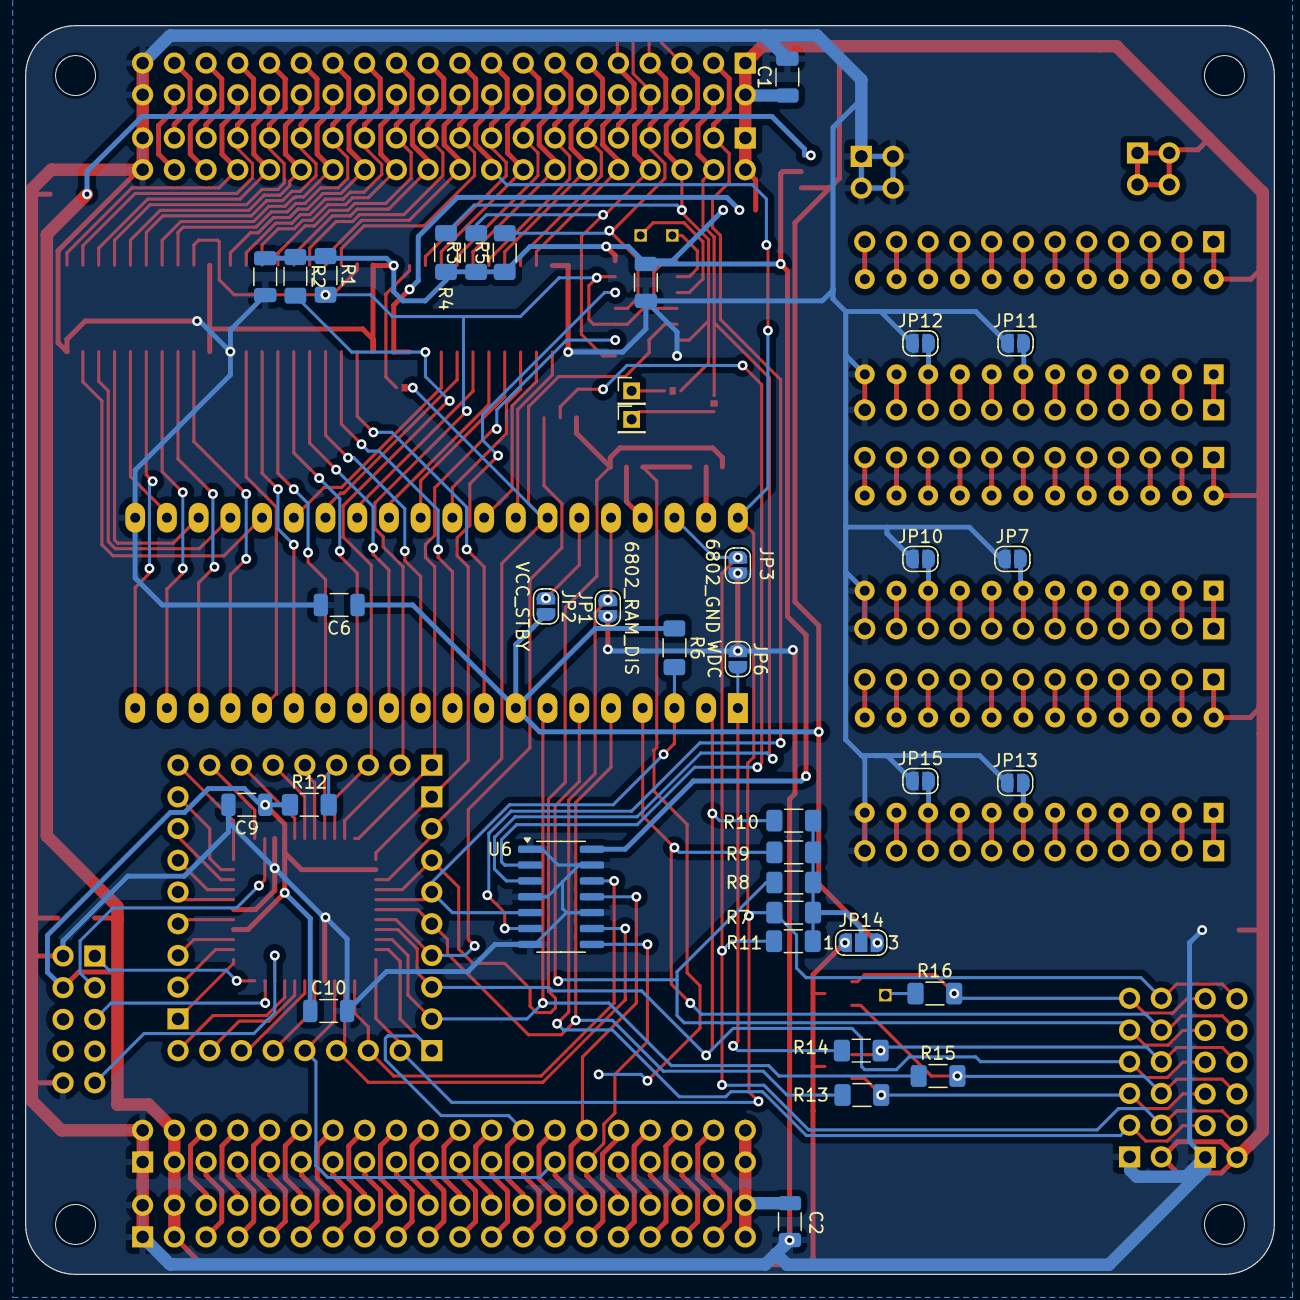
[picture p93: board 6502_6800_CPU.kicad_pcb from below]

Board: 2 copper layers, 100.0 x 100.0 mm, 91 parts (37 on the bottom side), 222 nets.
