roberto314/Unicomp3/CPU_Boards/AdapterBoards/M50747_SDIP/M50747_SDIP.kicad_pcb

## KiCad design CPU_Boards/AdapterBoards/M50747_SDIP/M50747_SDIP.kicad_pcb (2024-10-12)

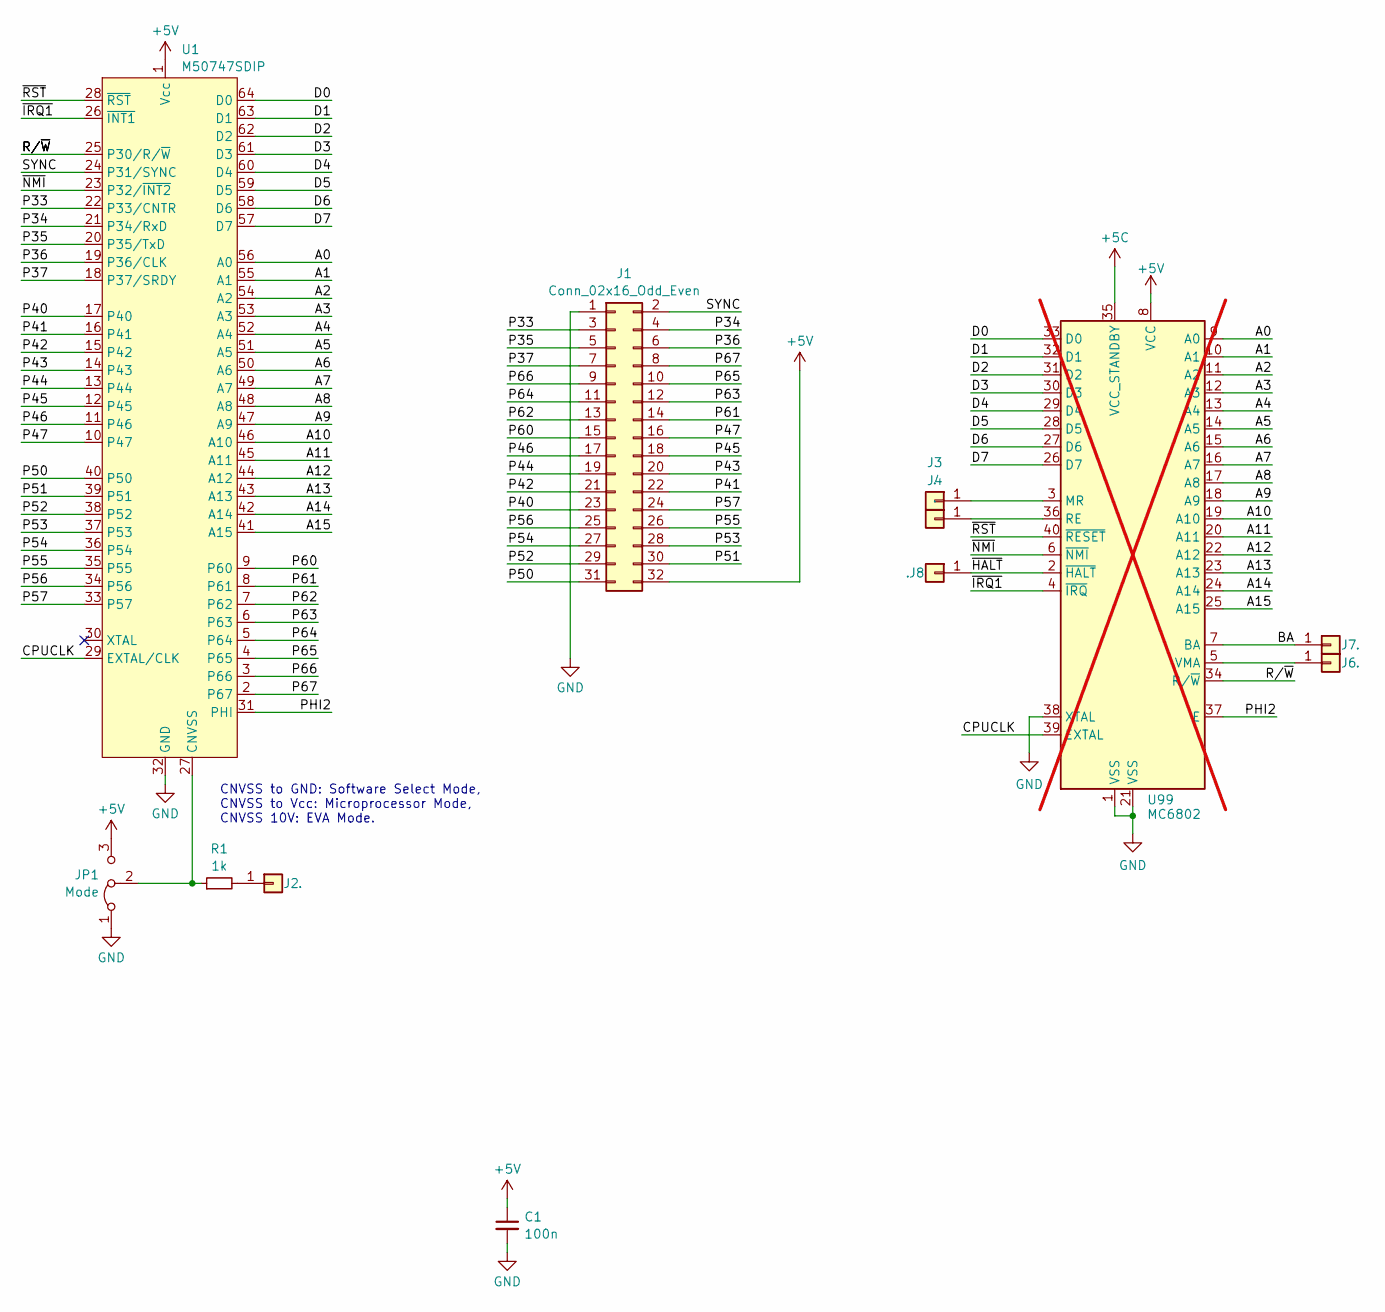
[picture p94: schematic M50747_SDIP.kicad_sch]

Parts:
C1: 100n; C_1206_3216Metric_Pad1.33x1.80mm_HandSolder
J1: Conn_02x16_Odd_Even; PinHeader_2x16_P2.54mm_Horizontal
J2, J3, J4, J6, J7, J8: .; PinHeader_1x01_P2.00mm_Vertical
JP1: Mode; SolderJumper-3_P1.3mm_Open_Pad1.0x1.5mm
R1: 1k; R_1206_3216Metric
U1: M50747SDIP; DIP-64_P1.778_W19.05
U99: MC6802; DIP-40_W15.24mm; not fitted

Connections:
+5V: C1.1, J1.32, JP1.3 (B), U1.1 (Vcc); also elsewhere on the board
/A0: U1.56 (A0); also elsewhere on the board
/A1: U1.55 (A1); also elsewhere on the board
/A2: U1.54 (A2); also elsewhere on the board
/A3: U1.53 (A3); also elsewhere on the board
/A4: U1.52 (A4); also elsewhere on the board
/A5: U1.51 (A5); also elsewhere on the board
/A6: U1.50 (A6); also elsewhere on the board
/A7: U1.49 (A7); also elsewhere on the board
/A8: U1.48 (A8); also elsewhere on the board
/A9: U1.47 (A9); also elsewhere on the board
/A10: U1.46 (A10); also elsewhere on the board
/A11: U1.45 (A11); also elsewhere on the board
/A12: U1.44 (A12); also elsewhere on the board
/A13: U1.43 (A13); also elsewhere on the board
/A14: U1.42 (A14); also elsewhere on the board
/A15: U1.41 (A15); also elsewhere on the board
/BA: J7.1; also elsewhere on the board
/CPUCLK: U1.29 (EXTAL/CLK); also elsewhere on the board
/D0: U1.64 (D0); also elsewhere on the board
/D1: U1.63 (D1); also elsewhere on the board
/D2: U1.62 (D2); also elsewhere on the board
/D3: U1.61 (D3); also elsewhere on the board
/D4: U1.60 (D4); also elsewhere on the board
/D5: U1.59 (D5); also elsewhere on the board
/D6: U1.58 (D6); also elsewhere on the board
/D7: U1.57 (D7); also elsewhere on the board
/P33: J1.3, U1.22 (P33/CNTR)
/P34: J1.4, U1.21 (P34/RxD)
/P35: J1.5, U1.20 (P35/TxD)
/P36: J1.6, U1.19 (P36/CLK)
/P37: J1.7, U1.18 (P37/SRDY)
/P40: J1.23, U1.17 (P40)
/P41: J1.22, U1.16 (P41)
/P42: J1.21, U1.15 (P42)
/P43: J1.20, U1.14 (P43)
/P44: J1.19, U1.13 (P44)
/P45: J1.18, U1.12 (P45)
/P46: J1.17, U1.11 (P46)
/P47: J1.16, U1.10 (P47)
/P50: J1.31, U1.40 (P50)
/P51: J1.30, U1.39 (P51)
/P52: J1.29, U1.38 (P52)
/P53: J1.28, U1.37 (P53)
/P54: J1.27, U1.36 (P54)
/P55: J1.26, U1.35 (P55)
/P56: J1.25, U1.34 (P56)
/P57: J1.24, U1.33 (P57)
/P60: J1.15, U1.9 (P60)
/P61: J1.14, U1.8 (P61)
/P62: J1.13, U1.7 (P62)
/P63: J1.12, U1.6 (P63)
/P64: J1.11, U1.5 (P64)
/P65: J1.10, U1.4 (P65)
/P66: J1.9, U1.3 (P66)
/P67: J1.8, U1.2 (P67)
/PHI2: U1.31 (PHI); also elsewhere on the board
/R/~W: U1.25 (P30/R/~W); also elsewhere on the board
/SYNC: J1.2, U1.24 (P31/SYNC)
/~HALT: J8.1; also elsewhere on the board
/~IRQ1: U1.26 (~INT1); also elsewhere on the board
/~NMI: U1.23 (P32/~INT2); also elsewhere on the board
/~RST: U1.28 (~RST); also elsewhere on the board
GND: C1.2, J1.1, JP1.1 (A), U1.32 (GND); also elsewhere on the board
unnamed: J2.1, R1.2
unnamed 66: J3.1; also elsewhere on the board
unnamed 67: J4.1; also elsewhere on the board
unnamed 68: J6.1; also elsewhere on the board
unnamed: JP1.2 (C), R1.1, U1.27 (CNVSS)

Notes on the sheet:
CNVSS to GND: Software Select Mode, CNVSS to Vcc: Microprocessor Mode, CNVSS 10V: EVA Mode.

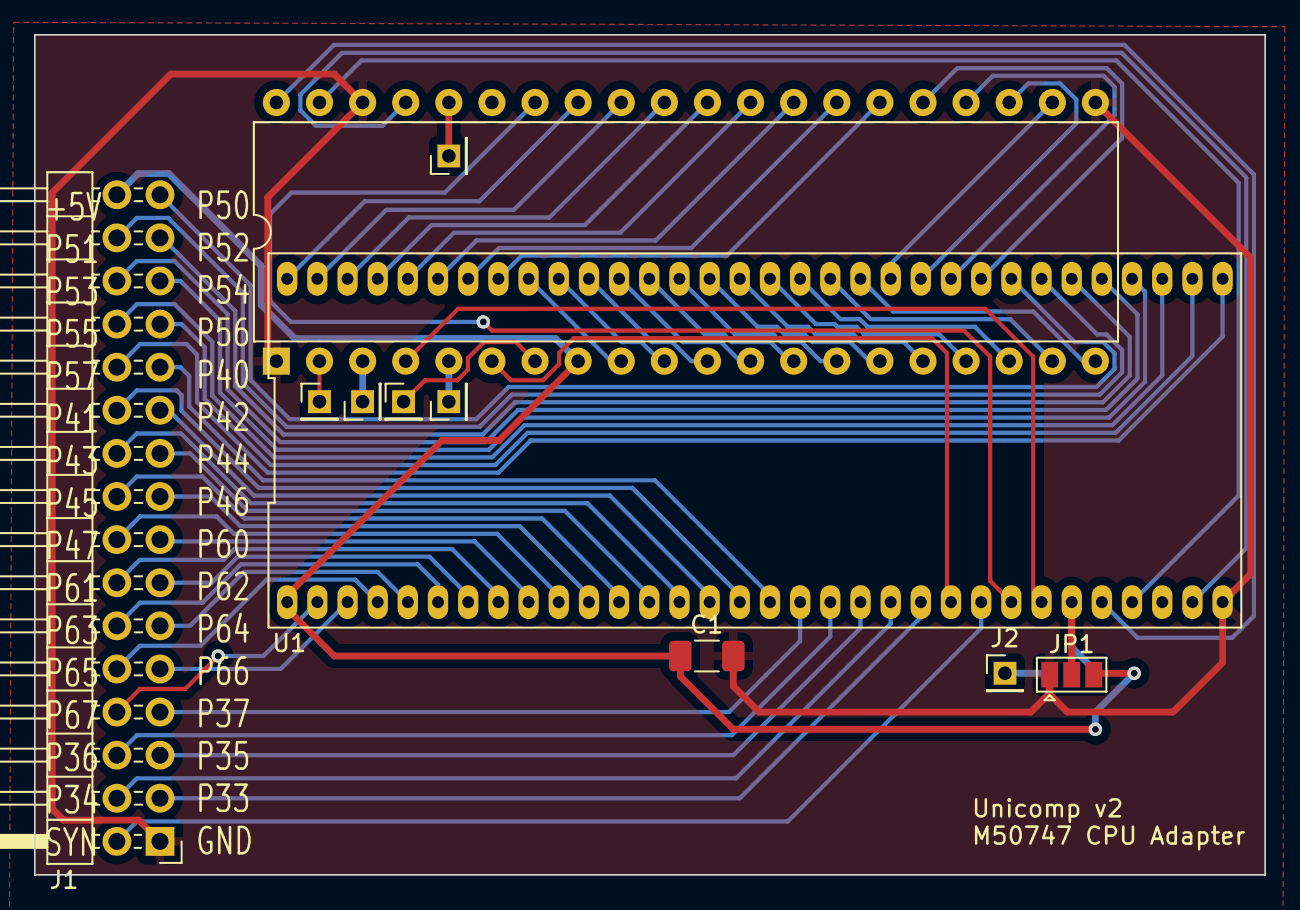
[picture p95: board M50747_SDIP.kicad_pcb from above]

Board: 2 copper layers, 72.5 x 49.5 mm, 12 parts (1 on the bottom side), 69 nets.

Other parts of the board:
U3: MC6802; DIP-40_W15.24mm

Their connections:
+5V: U3.8 (VCC); also elsewhere on the board
/A0: U3.9 (A0); also elsewhere on the board
/A1: U3.10 (A1); also elsewhere on the board
/A2: U3.11 (A2); also elsewhere on the board
/A3: U3.12 (A3); also elsewhere on the board
/A4: U3.13 (A4); also elsewhere on the board
/A5: U3.14 (A5); also elsewhere on the board
/A6: U3.15 (A6); also elsewhere on the board
/A7: U3.16 (A7); also elsewhere on the board
/A8: U3.17 (A8); also elsewhere on the board
/A9: U3.18 (A9); also elsewhere on the board
/A10: U3.19 (A10); also elsewhere on the board
/A11: U3.20 (A11); also elsewhere on the board
/A12: U3.22 (A12); also elsewhere on the board
/A13: U3.23 (A13); also elsewhere on the board
/A14: U3.24 (A14); also elsewhere on the board
/A15: U3.25 (A15); also elsewhere on the board
/BA: U3.7 (BA); also elsewhere on the board
/CPUCLK: U3.39 (EXTAL); also elsewhere on the board
/D0: U3.33 (D0); also elsewhere on the board
/D1: U3.32 (D1); also elsewhere on the board
/D2: U3.31 (D2); also elsewhere on the board
/D3: U3.30 (D3); also elsewhere on the board
/D4: U3.29 (D4); also elsewhere on the board
/D5: U3.28 (D5); also elsewhere on the board
/D6: U3.27 (D6); also elsewhere on the board
/D7: U3.26 (D7); also elsewhere on the board
/PHI2: U3.37 (E); also elsewhere on the board
/R/~W: U3.34 (R/~W); also elsewhere on the board
/~HALT: U3.2 (~HALT); also elsewhere on the board
/~IRQ1: U3.4 (~IRQ); also elsewhere on the board
/~NMI: U3.6 (~NMI); also elsewhere on the board
/~RST: U3.40 (~RESET); also elsewhere on the board
GND: U3.1 (VSS), U3.21 (VSS), U3.38 (XTAL); also elsewhere on the board
unnamed 66: U3.3 (MR); also elsewhere on the board
unnamed 67: U3.36 (RE); also elsewhere on the board
unnamed 68: U3.5 (VMA); also elsewhere on the board
