roberto314/Unicomp3/CPU_Boards/AdapterBoards/6303R_PLCC_Addon/6303_PLCC.kicad_pcb

## KiCad design CPU_Boards/AdapterBoards/6303R_PLCC_Addon/6303_PLCC.kicad_pcb (2024-10-12)

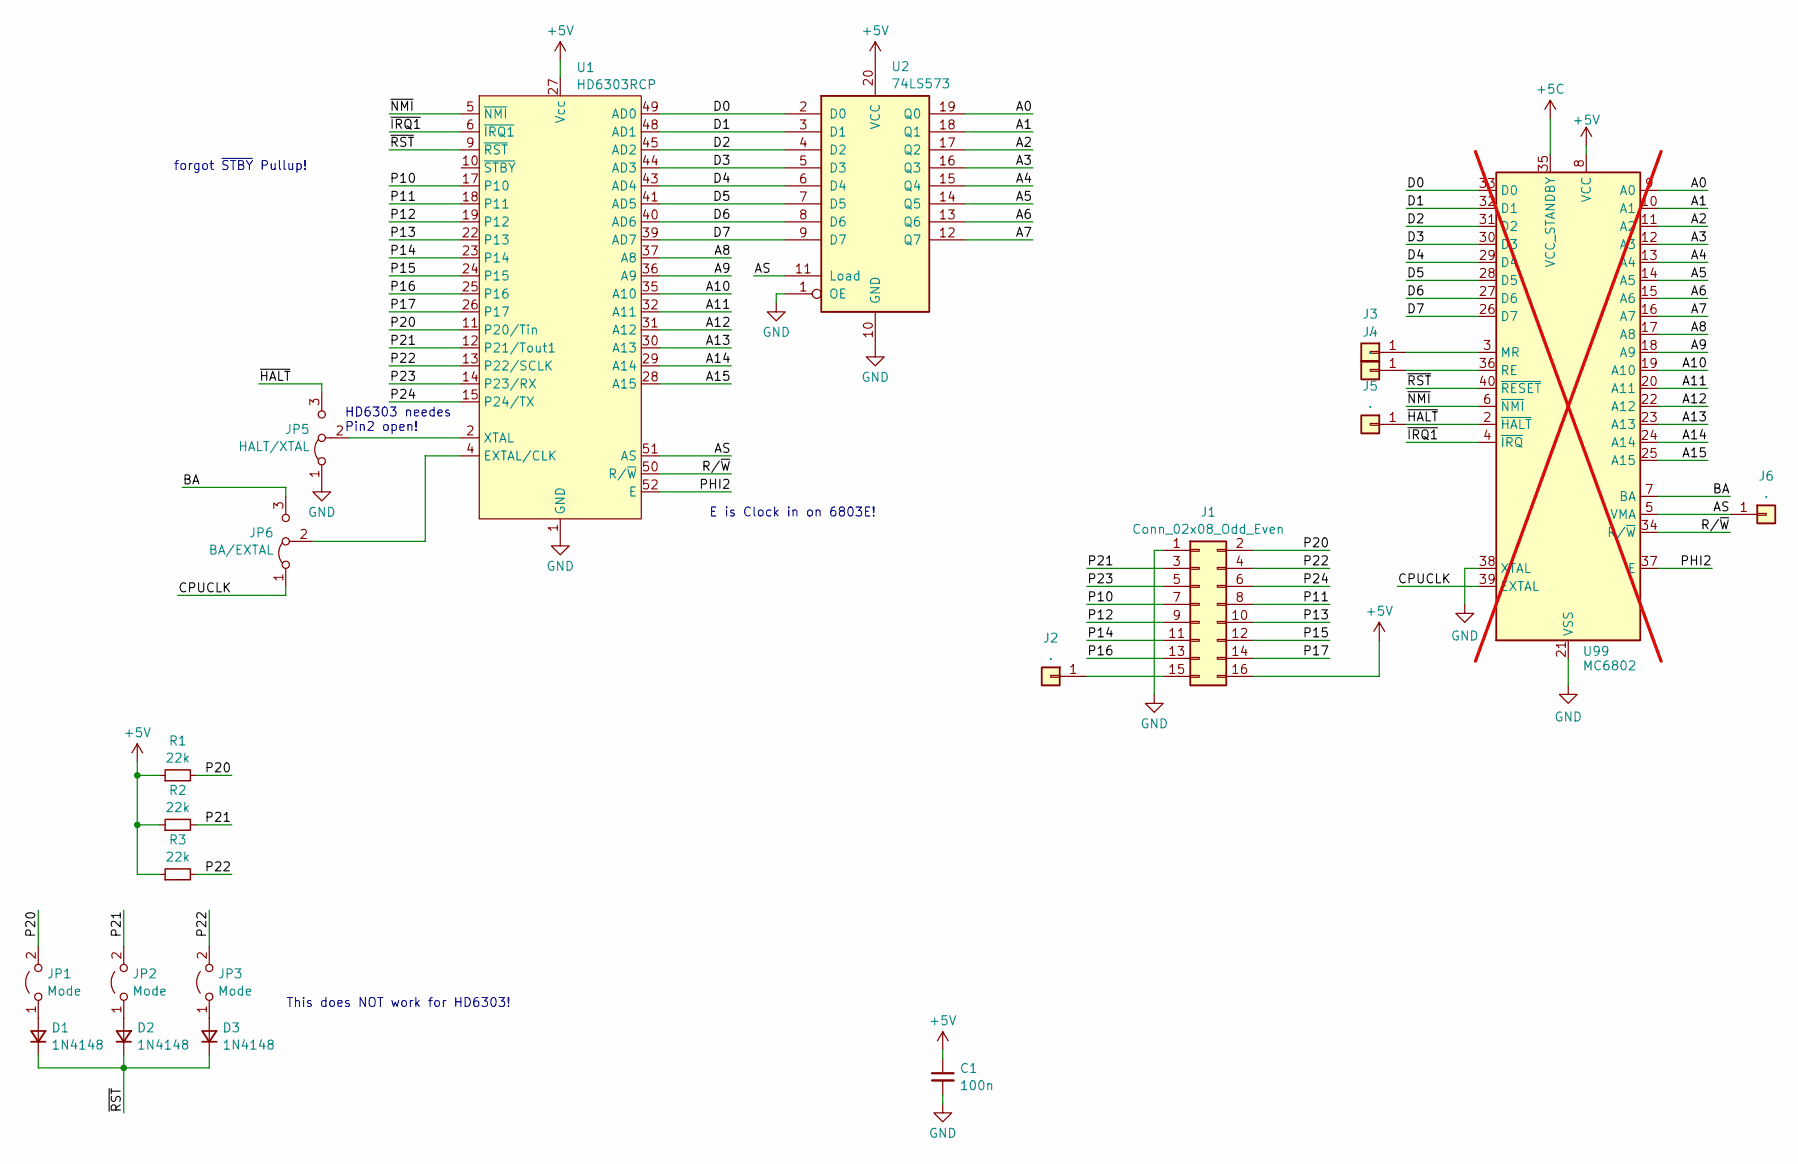
[picture p96: schematic 6303_PLCC.kicad_sch]

Parts:
C1: 100n; C_1206_3216Metric_Pad1.33x1.80mm_HandSolder
D1, D2, D3: 1N4148; D_1206_3216Metric_Pad1.42x1.75mm_HandSolder
J1: Conn_02x08_Odd_Even; PinHeader_2x08_P2.54mm_Horizontal
J2, J3, J4, J5, J6: .; PinHeader_1x01_P2.00mm_Vertical
JP1, JP2, JP3: Mode; PinHeader_1x02_P2.54mm_Vertical
JP5: HALT/XTAL; PinHeader_1x03_P2.54mm_Vertical
JP6: BA/EXTAL; PinHeader_1x03_P2.54mm_Vertical
R1, R2, R3: 22k; R_1206_3216Metric_Pad1.30x1.75mm_HandSolder
U1: HD6303RCP; PLCC-52_SMD-Socket
U2: 74LS573; DIP-20_W7.62mm_Socket_LongPads
U99: MC6802; DIP-40_W15.24mm; not fitted

Connections:
+5V: C1.1, J1.16, R1.1, R2.1, R3.1, U1.27 (Vcc), U2.20 (VCC); also elsewhere on the board
/A0: U2.19 (Q0); also elsewhere on the board
/A1: U2.18 (Q1); also elsewhere on the board
/A2: U2.17 (Q2); also elsewhere on the board
/A3: U2.16 (Q3); also elsewhere on the board
/A4: U2.15 (Q4); also elsewhere on the board
/A5: U2.14 (Q5); also elsewhere on the board
/A6: U2.13 (Q6); also elsewhere on the board
/A7: U2.12 (Q7); also elsewhere on the board
/A8: U1.37 (A8); also elsewhere on the board
/A9: U1.36 (A9); also elsewhere on the board
/A10: U1.35 (A10); also elsewhere on the board
/A11: U1.32 (A11); also elsewhere on the board
/A12: U1.31 (A12); also elsewhere on the board
/A13: U1.30 (A13); also elsewhere on the board
/A14: U1.29 (A14); also elsewhere on the board
/A15: U1.28 (A15); also elsewhere on the board
/AS: J6.1, U1.51 (AS), U2.11 (Load); also elsewhere on the board
/BA: JP6.3 (B); also elsewhere on the board
/CPUCLK: JP6.1 (A); also elsewhere on the board
/D0: U1.49 (AD0), U2.2 (D0); also elsewhere on the board
/D1: U1.48 (AD1), U2.3 (D1); also elsewhere on the board
/D2: U1.45 (AD2), U2.4 (D2); also elsewhere on the board
/D3: U1.44 (AD3), U2.5 (D3); also elsewhere on the board
/D4: U1.43 (AD4), U2.6 (D4); also elsewhere on the board
/D5: U1.41 (AD5), U2.7 (D5); also elsewhere on the board
/D6: U1.40 (AD6), U2.8 (D6); also elsewhere on the board
/D7: U1.39 (AD7), U2.9 (D7); also elsewhere on the board
/P10: J1.7, U1.17 (P10)
/P11: J1.8, U1.18 (P11)
/P12: J1.9, U1.19 (P12)
/P13: J1.10, U1.22 (P13)
/P14: J1.11, U1.23 (P14)
/P15: J1.12, U1.24 (P15)
/P16: J1.13, U1.25 (P16)
/P17: J1.14, U1.26 (P17)
/P20: J1.2, JP1.2 (B), R1.2, U1.11 (P20/Tin)
/P21: J1.3, JP2.2 (B), R2.2, U1.12 (P21/Tout1)
/P22: J1.4, JP3.2 (B), R3.2, U1.13 (P22/SCLK)
/P23: J1.5, U1.14 (P23/RX)
/P24: J1.6, U1.15 (P24/TX)
/PHI2: U1.52 (E); also elsewhere on the board
/R/~W: U1.50 (R/~W); also elsewhere on the board
/~HALT: J5.1, JP5.3 (B); also elsewhere on the board
/~IRQ1: U1.6 (~IRQ1); also elsewhere on the board
/~NMI: U1.5 (~NMI); also elsewhere on the board
/~RST: D1.1 (K), D2.1 (K), D3.1 (K), U1.9 (~RST); also elsewhere on the board
GND: C1.2, J1.1, JP5.1 (A), U1.1 (GND), U2.1 (OE), U2.10 (GND); also elsewhere on the board
unnamed: D1.2 (A), JP1.1 (A)
unnamed: D2.2 (A), JP2.1 (A)
unnamed: D3.2 (A), JP3.1 (A)
unnamed: J1.15, J2.1
unnamed 53: J3.1; also elsewhere on the board
unnamed 54: J4.1; also elsewhere on the board
unnamed: JP5.2 (C), U1.2 (XTAL)
unnamed: JP6.2 (C), U1.4 (EXTAL/CLK)

Notes on the sheet:
forgot ~{STBY} Pullup!
This does NOT work for HD6303!
E is Clock in on 6803E!
HD6303 needes Pin2 open!

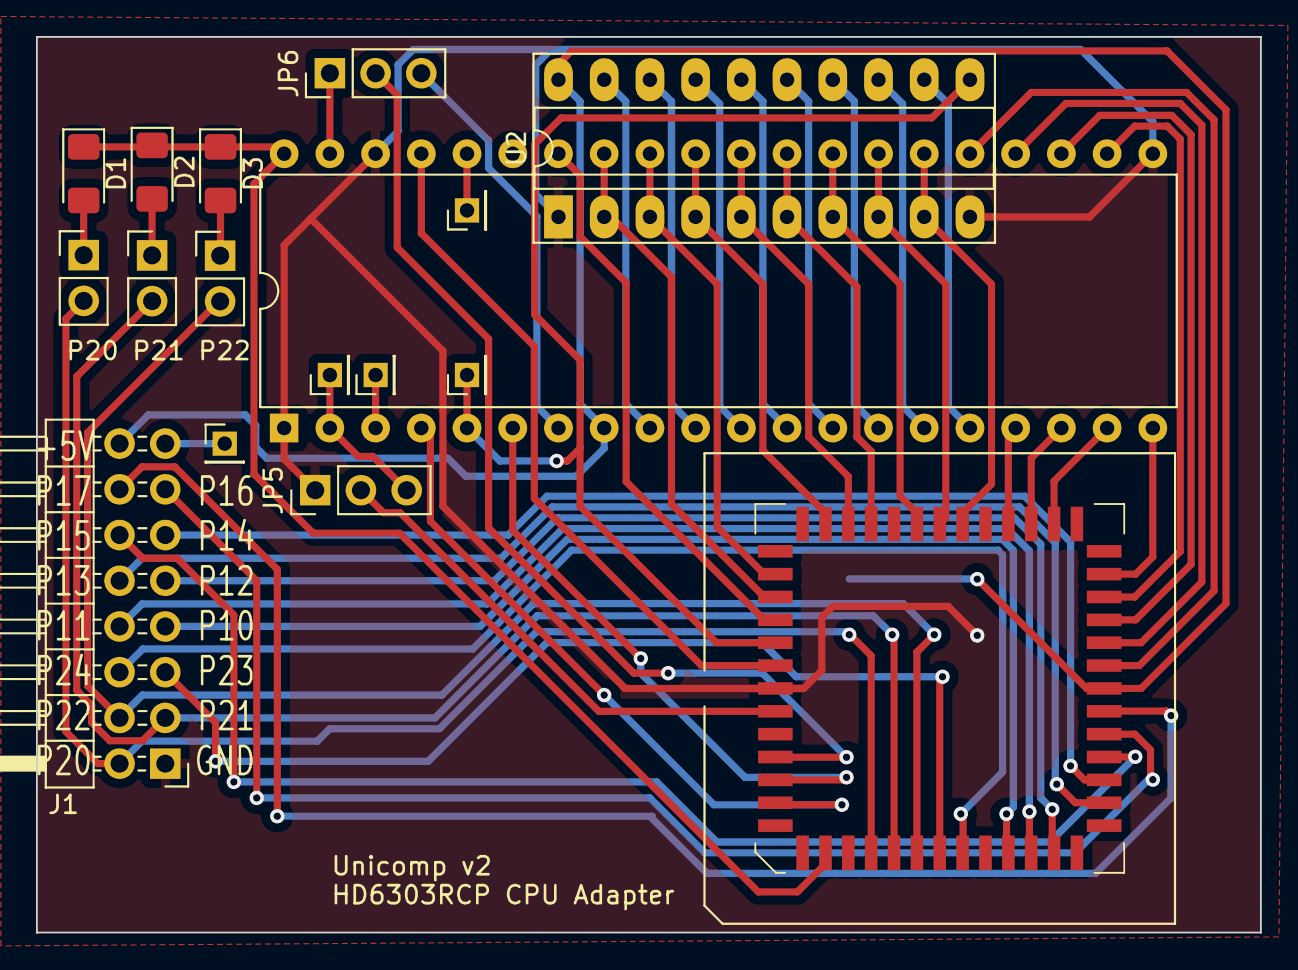
[picture p97: board 6303_PLCC.kicad_pcb from above]

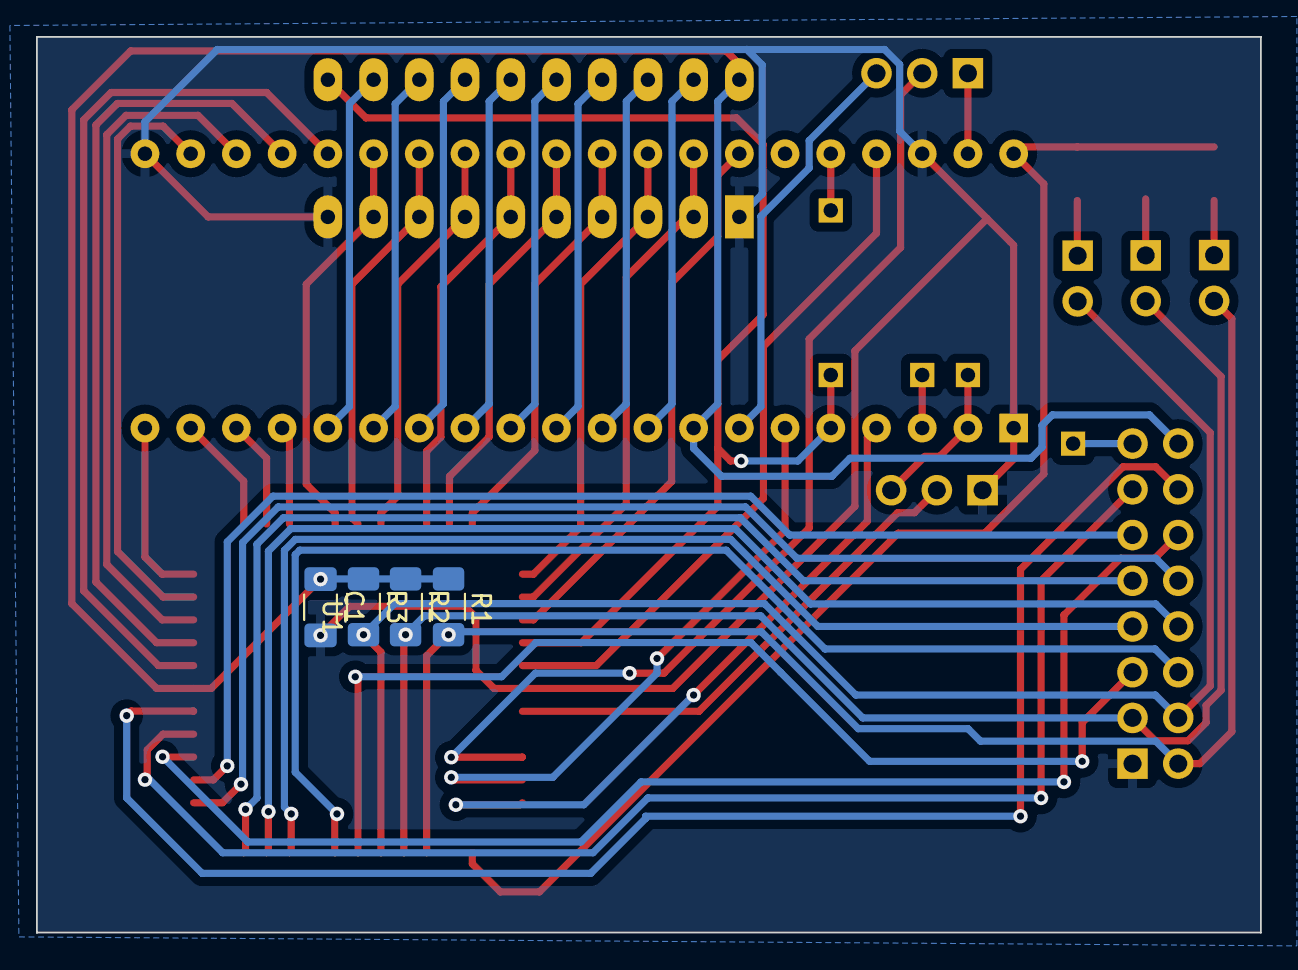
[picture p98: board 6303_PLCC.kicad_pcb from below]

Board: 2 copper layers, 68.0 x 49.8 mm, 21 parts (4 on the bottom side), 56 nets.

Other parts of the board:
U3: MC6802; DIP-40_W15.24mm

Their connections:
+5V: U3.8 (VCC); also elsewhere on the board
/A0: U3.9 (A0); also elsewhere on the board
/A1: U3.10 (A1); also elsewhere on the board
/A2: U3.11 (A2); also elsewhere on the board
/A3: U3.12 (A3); also elsewhere on the board
/A4: U3.13 (A4); also elsewhere on the board
/A5: U3.14 (A5); also elsewhere on the board
/A6: U3.15 (A6); also elsewhere on the board
/A7: U3.16 (A7); also elsewhere on the board
/A8: U3.17 (A8); also elsewhere on the board
/A9: U3.18 (A9); also elsewhere on the board
/A10: U3.19 (A10); also elsewhere on the board
/A11: U3.20 (A11); also elsewhere on the board
/A12: U3.22 (A12); also elsewhere on the board
/A13: U3.23 (A13); also elsewhere on the board
/A14: U3.24 (A14); also elsewhere on the board
/A15: U3.25 (A15); also elsewhere on the board
/AS: U3.5 (VMA); also elsewhere on the board
/BA: U3.7 (BA); also elsewhere on the board
/CPUCLK: U3.39 (EXTAL); also elsewhere on the board
/D0: U3.33 (D0); also elsewhere on the board
/D1: U3.32 (D1); also elsewhere on the board
/D2: U3.31 (D2); also elsewhere on the board
/D3: U3.30 (D3); also elsewhere on the board
/D4: U3.29 (D4); also elsewhere on the board
/D5: U3.28 (D5); also elsewhere on the board
/D6: U3.27 (D6); also elsewhere on the board
/D7: U3.26 (D7); also elsewhere on the board
/PHI2: U3.37 (E); also elsewhere on the board
/R/~W: U3.34 (R/~W); also elsewhere on the board
/~HALT: U3.2 (~HALT); also elsewhere on the board
/~IRQ1: U3.4 (~IRQ); also elsewhere on the board
/~NMI: U3.6 (~NMI); also elsewhere on the board
/~RST: U3.40 (~RESET); also elsewhere on the board
GND: U3.1 (VSS), U3.21 (VSS), U3.38 (XTAL); also elsewhere on the board
unnamed 53: U3.3 (MR); also elsewhere on the board
unnamed 54: U3.36 (RE); also elsewhere on the board
