roberto314/Unicomp3/USB-Serial InputBoard/USB-Serial InputBoard.kicad_pcb

## KiCad design USB-Serial InputBoard/USB-Serial InputBoard.kicad_pcb (2024-10-12)

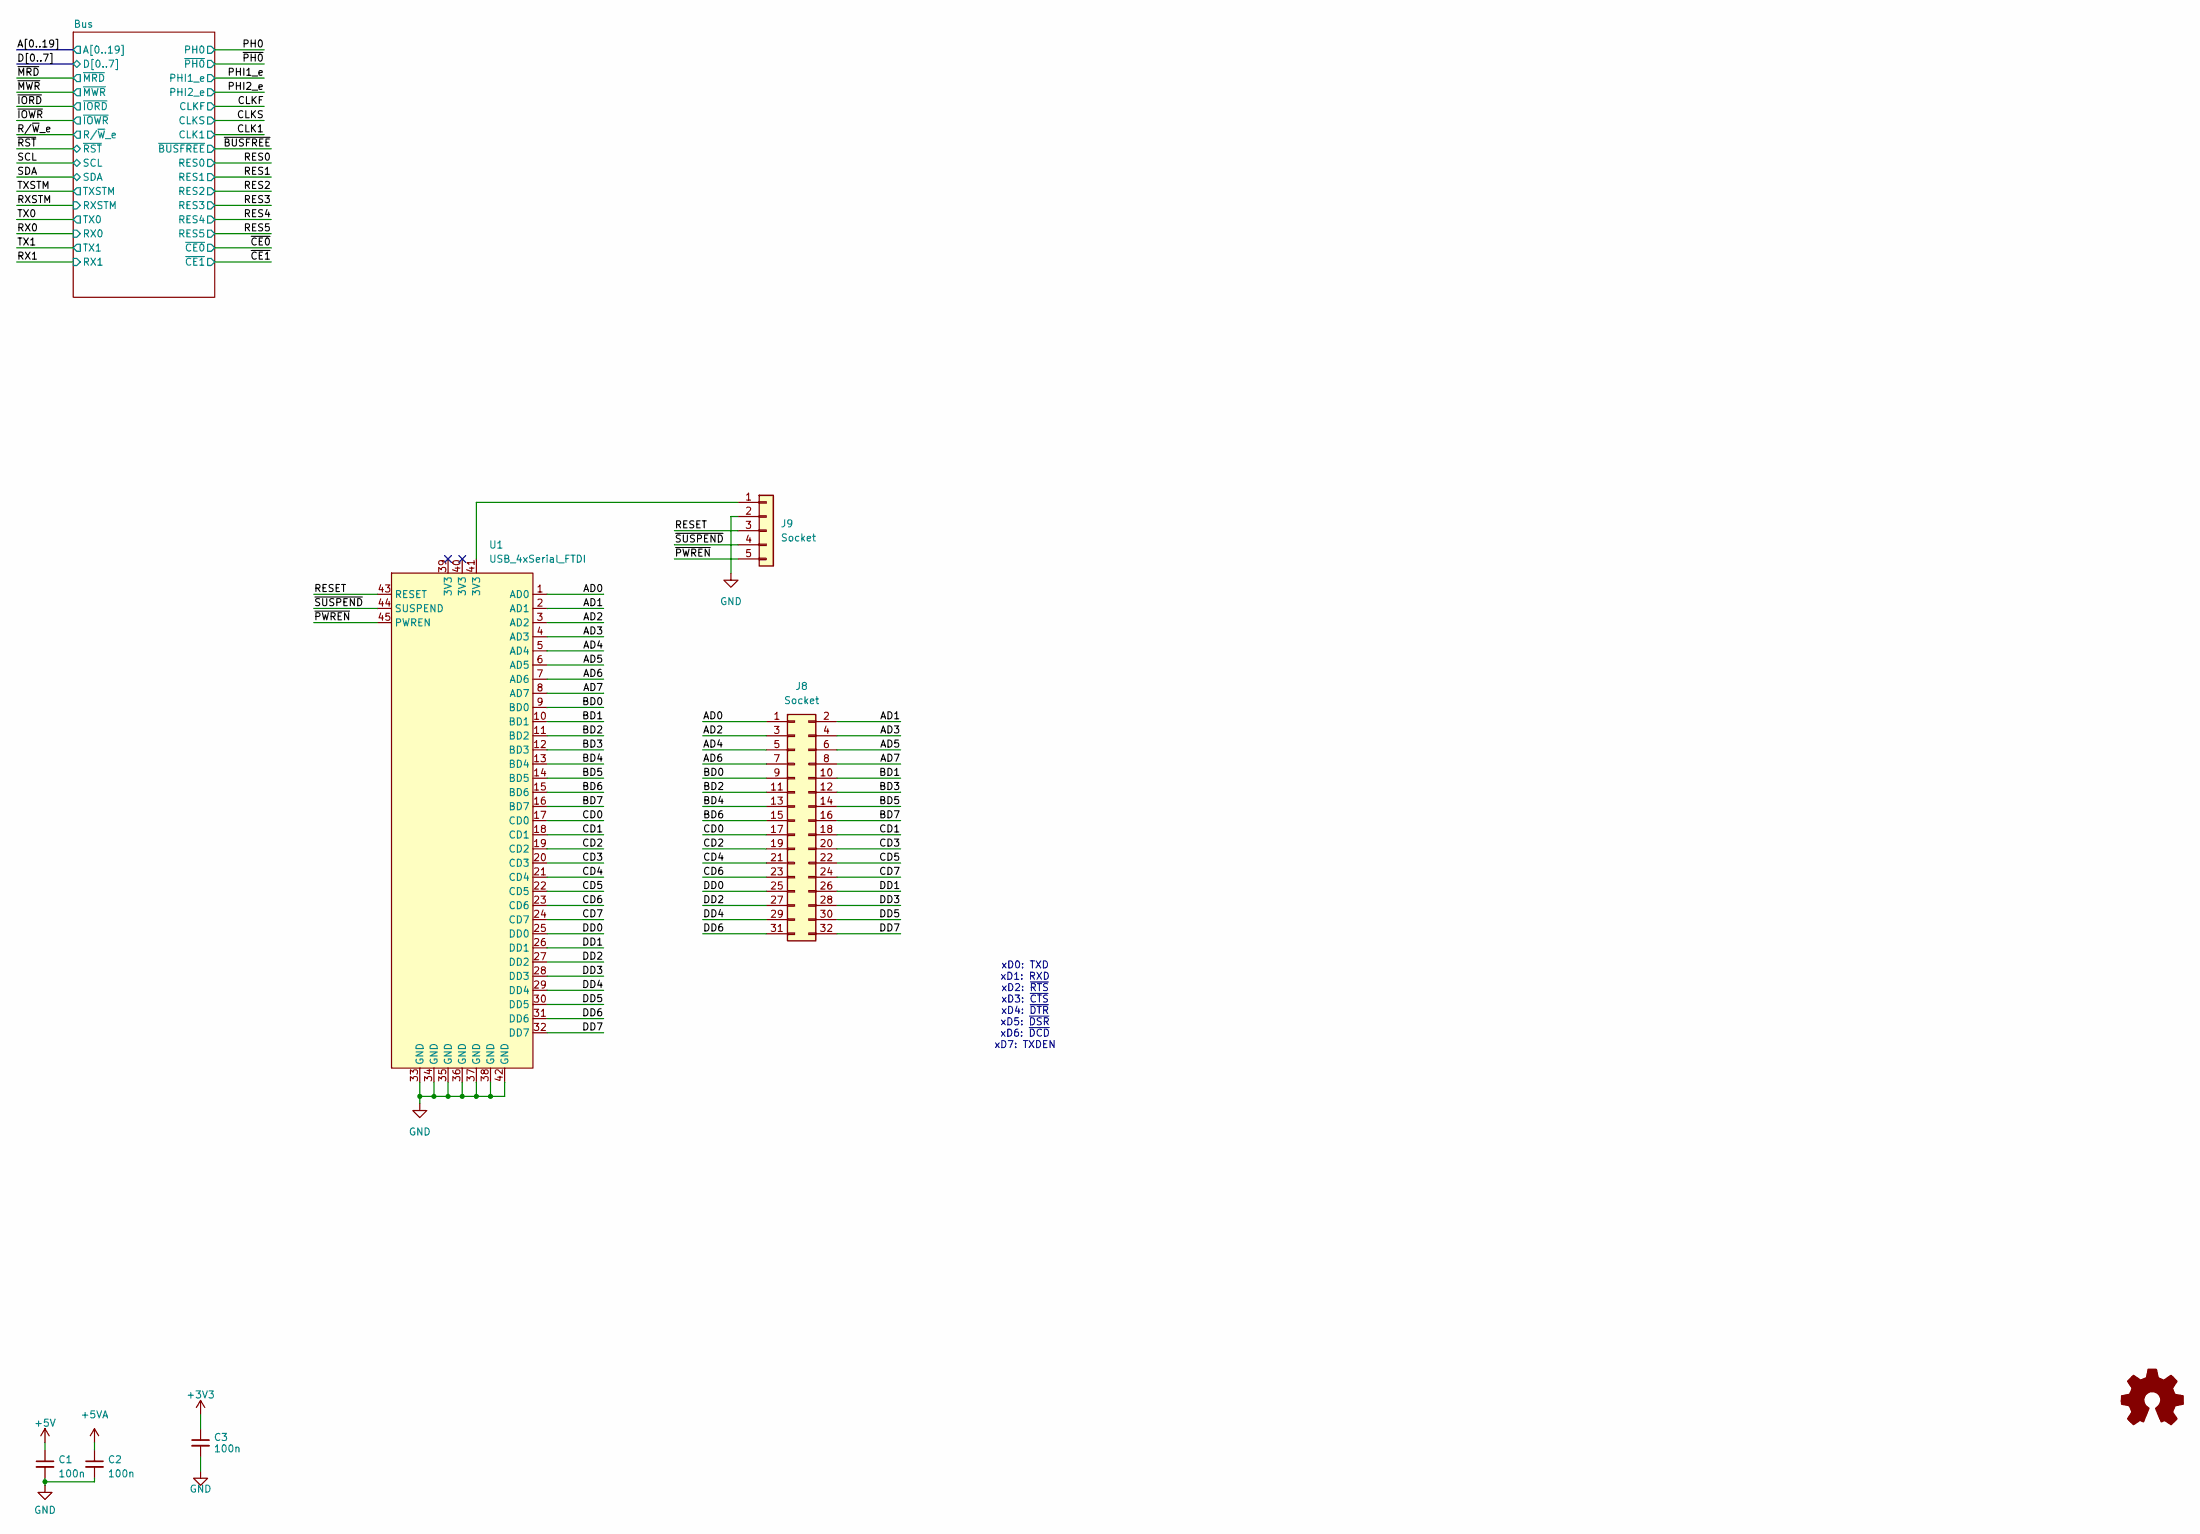
[picture p99: schematic USB-Serial InputBoard.kicad_sch, Unicomp v3 - USB Serial Board]

Parts:
C1, C2, C3: 100n; C_1206_3216Metric
J8: Socket; PinSocket_2x16_P2.54mm_Vertical
J9: Socket; PinSocket_1x05_P2.54mm_Vertical
U1: USB_4xSerial_FTDI

Connections:
+3V3: C3.1; also elsewhere on the board
+5V: C1.1; also elsewhere on the board
+5VA: C2.1; also elsewhere on the board
/AD0: J8.1, U1.1 (AD0)
/AD1: J8.2, U1.2 (AD1)
/AD2: J8.3, U1.3 (AD2)
/AD3: J8.4, U1.4 (AD3)
/AD4: J8.5, U1.5 (AD4)
/AD5: J8.6, U1.6 (AD5)
/AD6: J8.7, U1.7 (AD6)
/AD7: J8.8, U1.8 (AD7)
/BD0: J8.9, U1.9 (BD0)
/BD1: J8.10, U1.10 (BD1)
/BD2: J8.11, U1.11 (BD2)
/BD3: J8.12, U1.12 (BD3)
/BD4: J8.13, U1.13 (BD4)
/BD5: J8.14, U1.14 (BD5)
/BD6: J8.15, U1.15 (BD6)
/BD7: J8.16, U1.16 (BD7)
/CD0: J8.17, U1.17 (CD0)
/CD1: J8.18, U1.18 (CD1)
/CD2: J8.19, U1.19 (CD2)
/CD3: J8.20, U1.20 (CD3)
/CD4: J8.21, U1.21 (CD4)
/CD5: J8.22, U1.22 (CD5)
/CD6: J8.23, U1.23 (CD6)
/CD7: J8.24, U1.24 (CD7)
/DD0: J8.25, U1.25 (DD0)
/DD1: J8.26, U1.26 (DD1)
/DD2: J8.27, U1.27 (DD2)
/DD3: J8.28, U1.28 (DD3)
/DD4: J8.29, U1.29 (DD4)
/DD5: J8.30, U1.30 (DD5)
/DD6: J8.31, U1.31 (DD6)
/DD7: J8.32, U1.32 (DD7)
/RESET: J9.3, U1.43 (RESET)
/~PWREN: J9.5, U1.45 (PWREN)
/~SUSPEND: J9.4, U1.44 (SUSPEND)
GND: C1.2, C2.2, C3.2, J9.2, U1.33 (GND), U1.34 (GND), U1.35 (GND), U1.36 (GND), U1.37 (GND), U1.38 (GND), U1.42 (GND); also elsewhere on the board
unnamed: J9.1, U1.41 (3V3)

Notes on the sheet:
xD0: TXD xD1: RXD xD2: ~{RTS} xD3: ~{CTS} xD4: ~{DTR} xD5: ~{DSR} xD6: ~{DCD} xD7: TXDEN

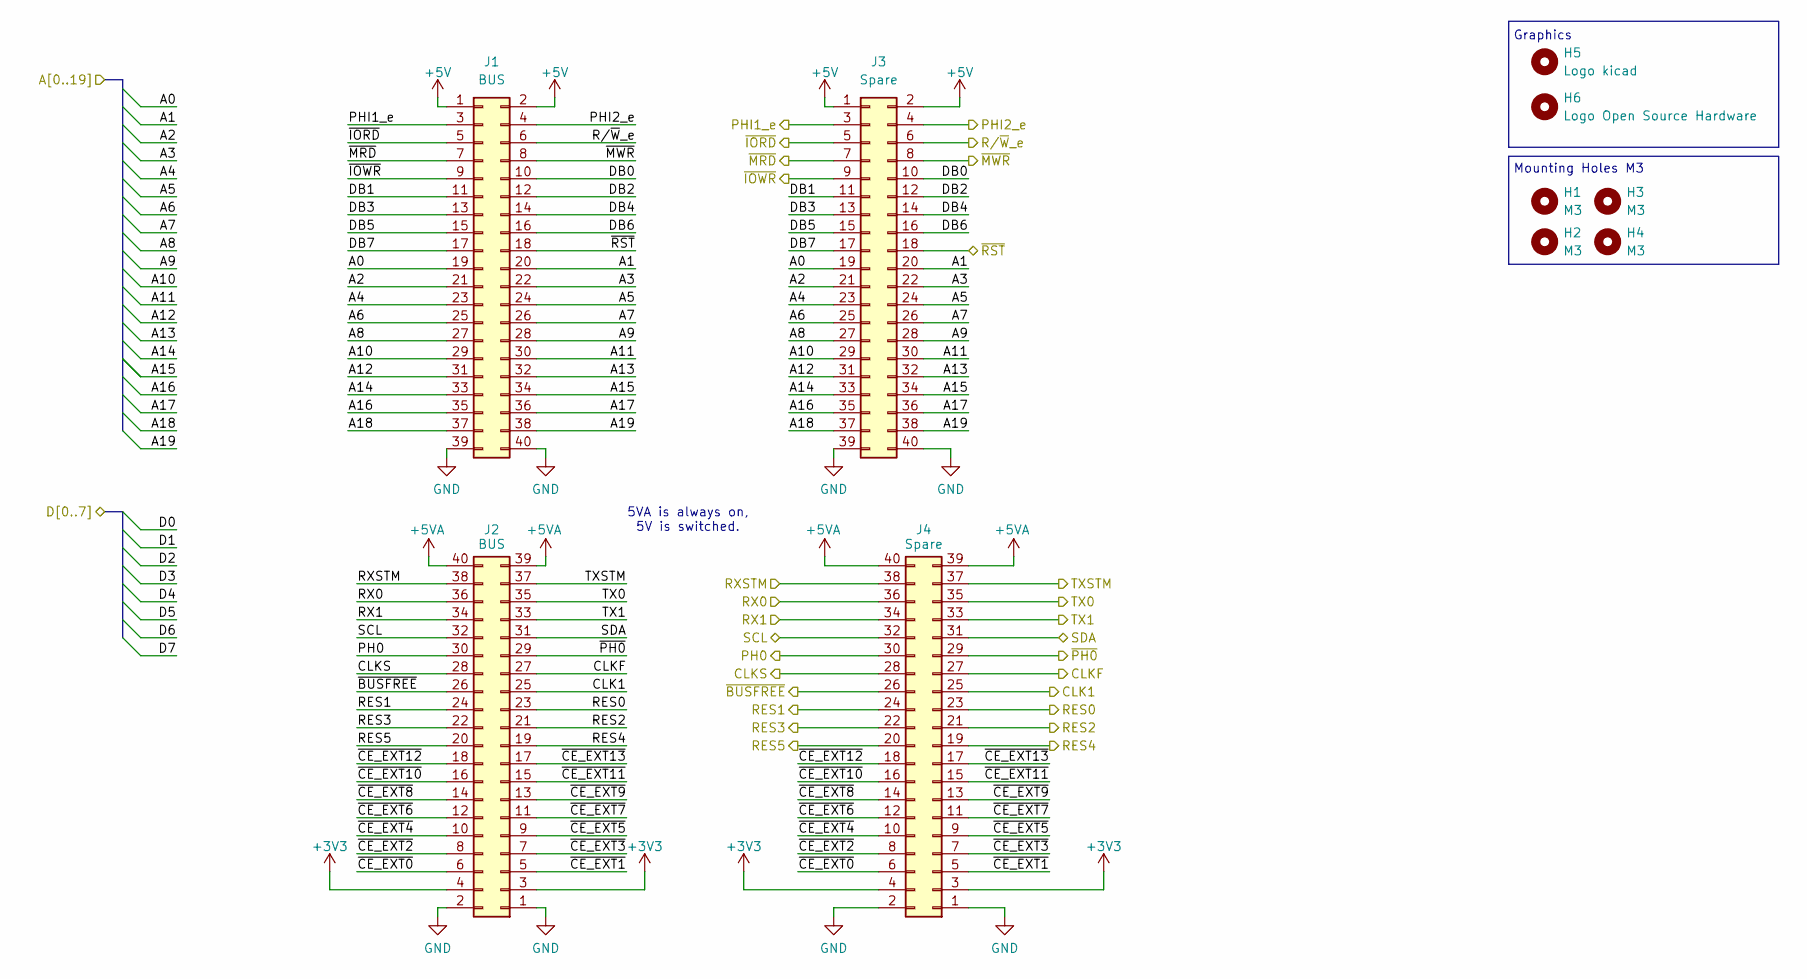
[picture p100: schematic bus.kicad_sch, Unicomp v3 - Bus]

Parts:
H1, H2, H3, H4: M3; MountingHole_3.2mm_M3
H5: Logo kicad; KiCad-Logo2_6mm_SilkScreen
H6: Logo Open Source Hardware; OSHW-Logo2_7.3x6mm_SilkScreen
J1, J2: BUS; PinSocket_2x20_P2.54mm_Vertical
J3, J4: Spare; PinSocket_2x20_P2.54mm_Vertical

Connections:
+3V3: J2.3, J2.4, J4.3, J4.4; also elsewhere on the board
+5V: J1.1, J1.2, J3.1, J3.2; also elsewhere on the board
+5VA: J2.39, J2.40, J4.39, J4.40; also elsewhere on the board
/A0: J1.19, J3.19
/A1: J1.20, J3.20
/A2: J1.21, J3.21
/A3: J1.22, J3.22
/A4: J1.23, J3.23
/A5: J1.24, J3.24
/A6: J1.25, J3.25
/A7: J1.26, J3.26
/A8: J1.27, J3.27
/A9: J1.28, J3.28
/A10: J1.29, J3.29
/A11: J1.30, J3.30
/A12: J1.31, J3.31
/A13: J1.32, J3.32
/A14: J1.33, J3.33
/A15: J1.34, J3.34
/A16: J1.35, J3.35
/A17: J1.36, J3.36
/A18: J1.37, J3.37
/A19: J1.38, J3.38
/Bus/DB0: J1.10, J3.10
/Bus/DB1: J1.11, J3.11
/Bus/DB2: J1.12, J3.12
/Bus/DB3: J1.13, J3.13
/Bus/DB4: J1.14, J3.14
/Bus/DB5: J1.15, J3.15
/Bus/DB6: J1.16, J3.16
/Bus/DB7: J1.17, J3.17
/Bus/~CE_EXT0: J2.6, J4.6
/Bus/~CE_EXT1: J2.5, J4.5
/Bus/~CE_EXT2: J2.8, J4.8
/Bus/~CE_EXT3: J2.7, J4.7
/Bus/~CE_EXT4: J2.10, J4.10
/Bus/~CE_EXT5: J2.9, J4.9
/Bus/~CE_EXT6: J2.12, J4.12
/Bus/~CE_EXT7: J2.11, J4.11
/Bus/~CE_EXT8: J2.14, J4.14
/Bus/~CE_EXT9: J2.13, J4.13
/Bus/~CE_EXT10: J2.16, J4.16
/Bus/~CE_EXT11: J2.15, J4.15
/Bus/~CE_EXT12: J2.18, J4.18
/Bus/~CE_EXT13: J2.17, J4.17
/CLK1: J2.25, J4.25
/CLKF: J2.27, J4.27
/CLKS: J2.28, J4.28
/PH0: J2.30, J4.30
/PHI1_e: J1.3, J3.3
/PHI2_e: J1.4, J3.4
/RES0: J2.23, J4.23
/RES1: J2.24, J4.24
/RES2: J2.21, J4.21
/RES3: J2.22, J4.22
/RES4: J2.19, J4.19
/RES5: J2.20, J4.20
/RX0: J2.36, J4.36
/RX1: J2.34, J4.34
/RXSTM: J2.38, J4.38
/R/~W_e: J1.6, J3.6
/SCL: J2.32, J4.32
/SDA: J2.31, J4.31
/TX0: J2.35, J4.35
/TX1: J2.33, J4.33
/TXSTM: J2.37, J4.37
/~BUSFREE: J2.26, J4.26
/~IORD: J1.5, J3.5
/~IOWR: J1.9, J3.9
/~MRD: J1.7, J3.7
/~MWR: J1.8, J3.8
/~PH0: J2.29, J4.29
/~RST: J1.18, J3.18
GND: J1.39, J1.40, J2.1, J2.2, J3.39, J3.40, J4.1, J4.2; also elsewhere on the board

Notes on the sheet:
Graphics
5VA is always on, 5V is switched.
Mounting Holes M3
