roberto314/Unicomp3/USB-Serial InputBoard/USB-Serial InputBoard.kicad_pcb

## KiCad design USB-Serial InputBoard/USB-Serial InputBoard.kicad_pcb (continued)

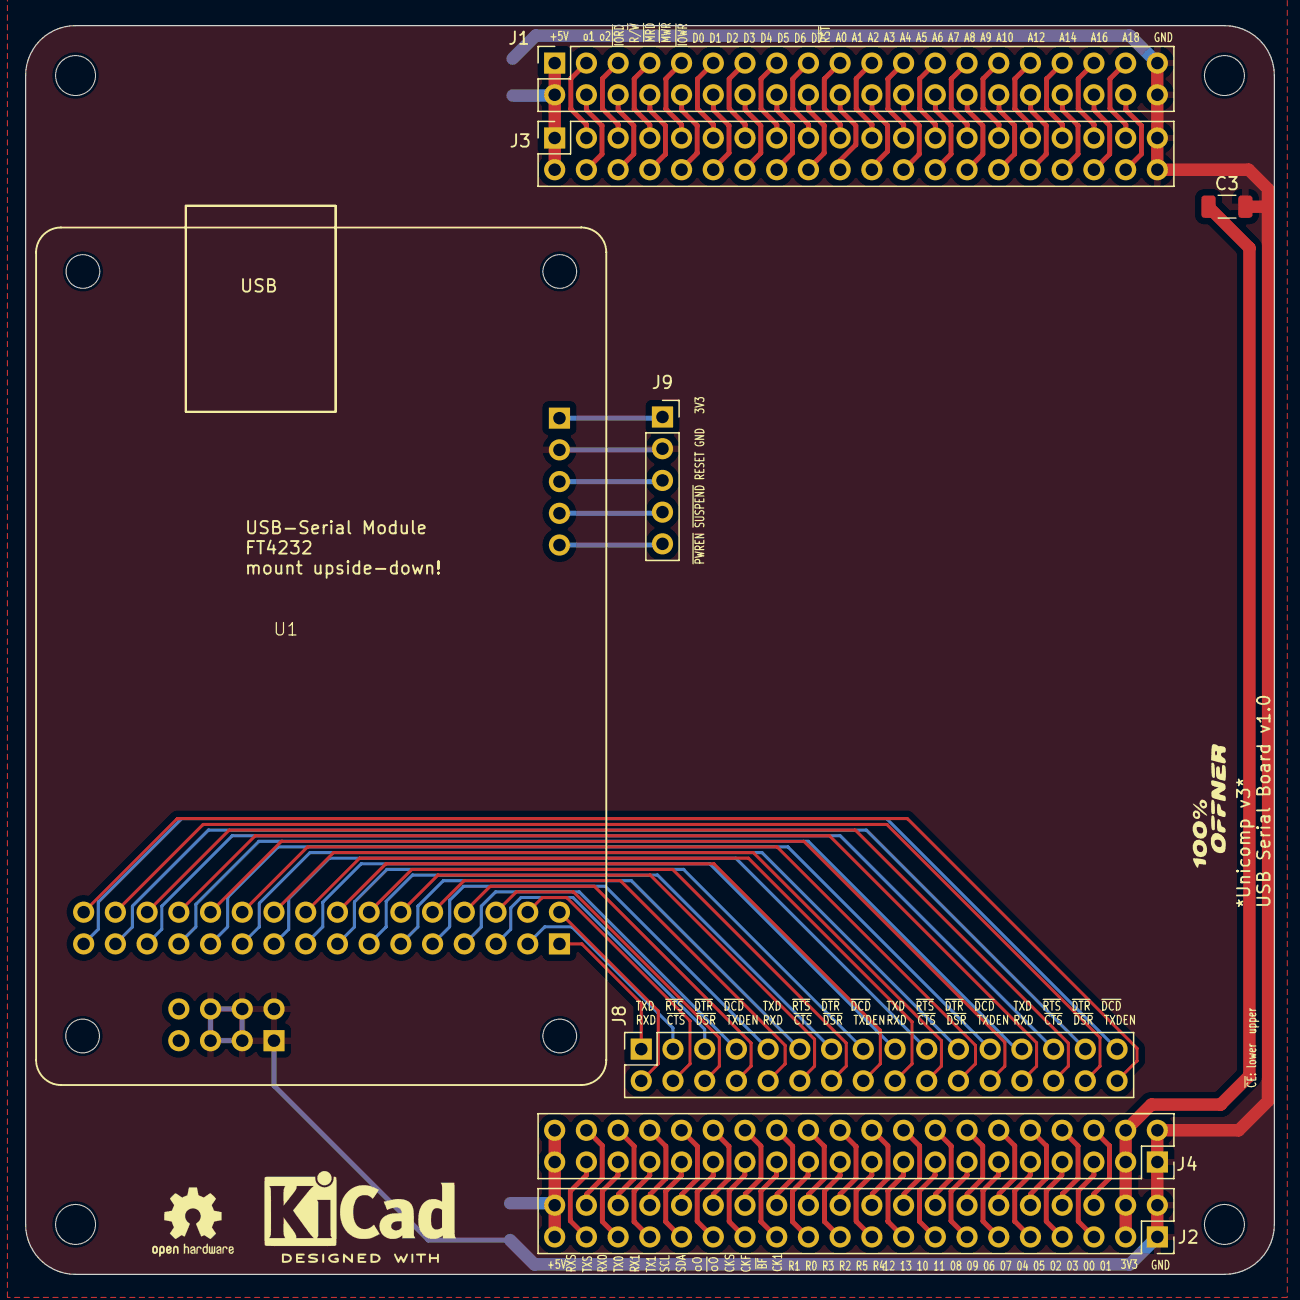
[picture p101: board USB-Serial InputBoard.kicad_pcb from above]

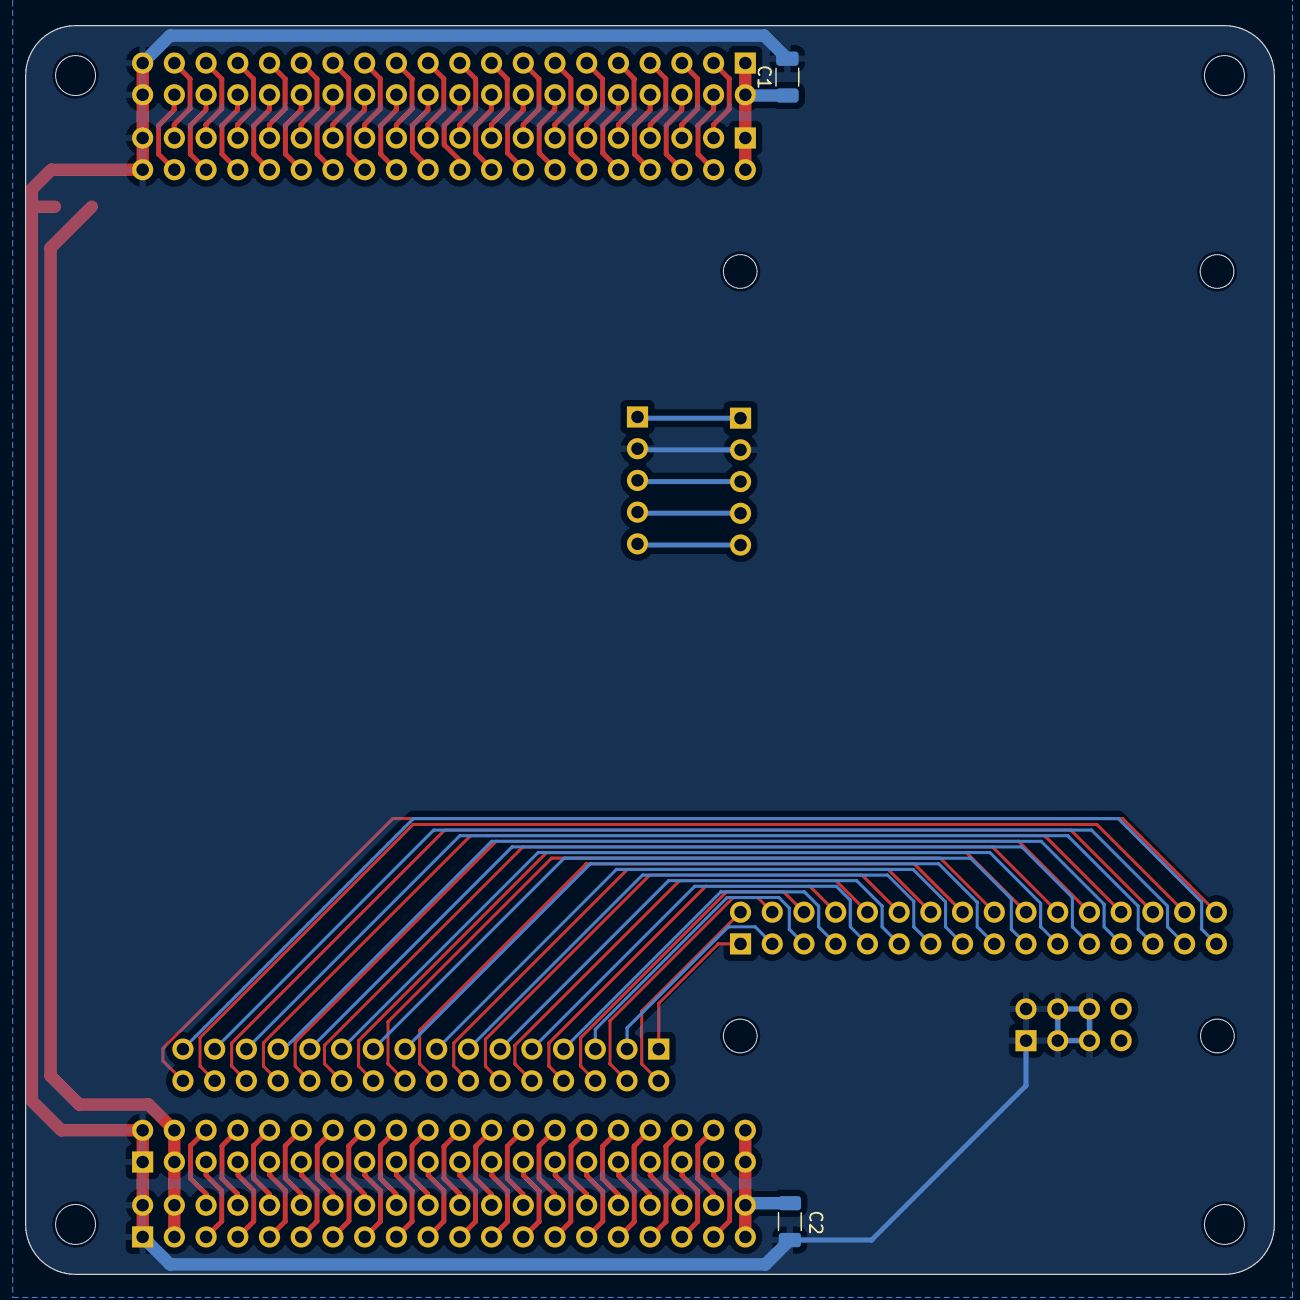
[picture p102: board USB-Serial InputBoard.kicad_pcb from below]

Board: 2 copper layers, 100.0 x 100.0 mm, 16 parts (2 on the bottom side), 110 nets.
