roberto314/Unicomp3/CPU_Boards/AdapterBoards/6303X_FP_Addon/6303_FP.kicad_pcb

## KiCad design CPU_Boards/AdapterBoards/6303X_FP_Addon/6303_FP.kicad_pcb (2024-10-12)

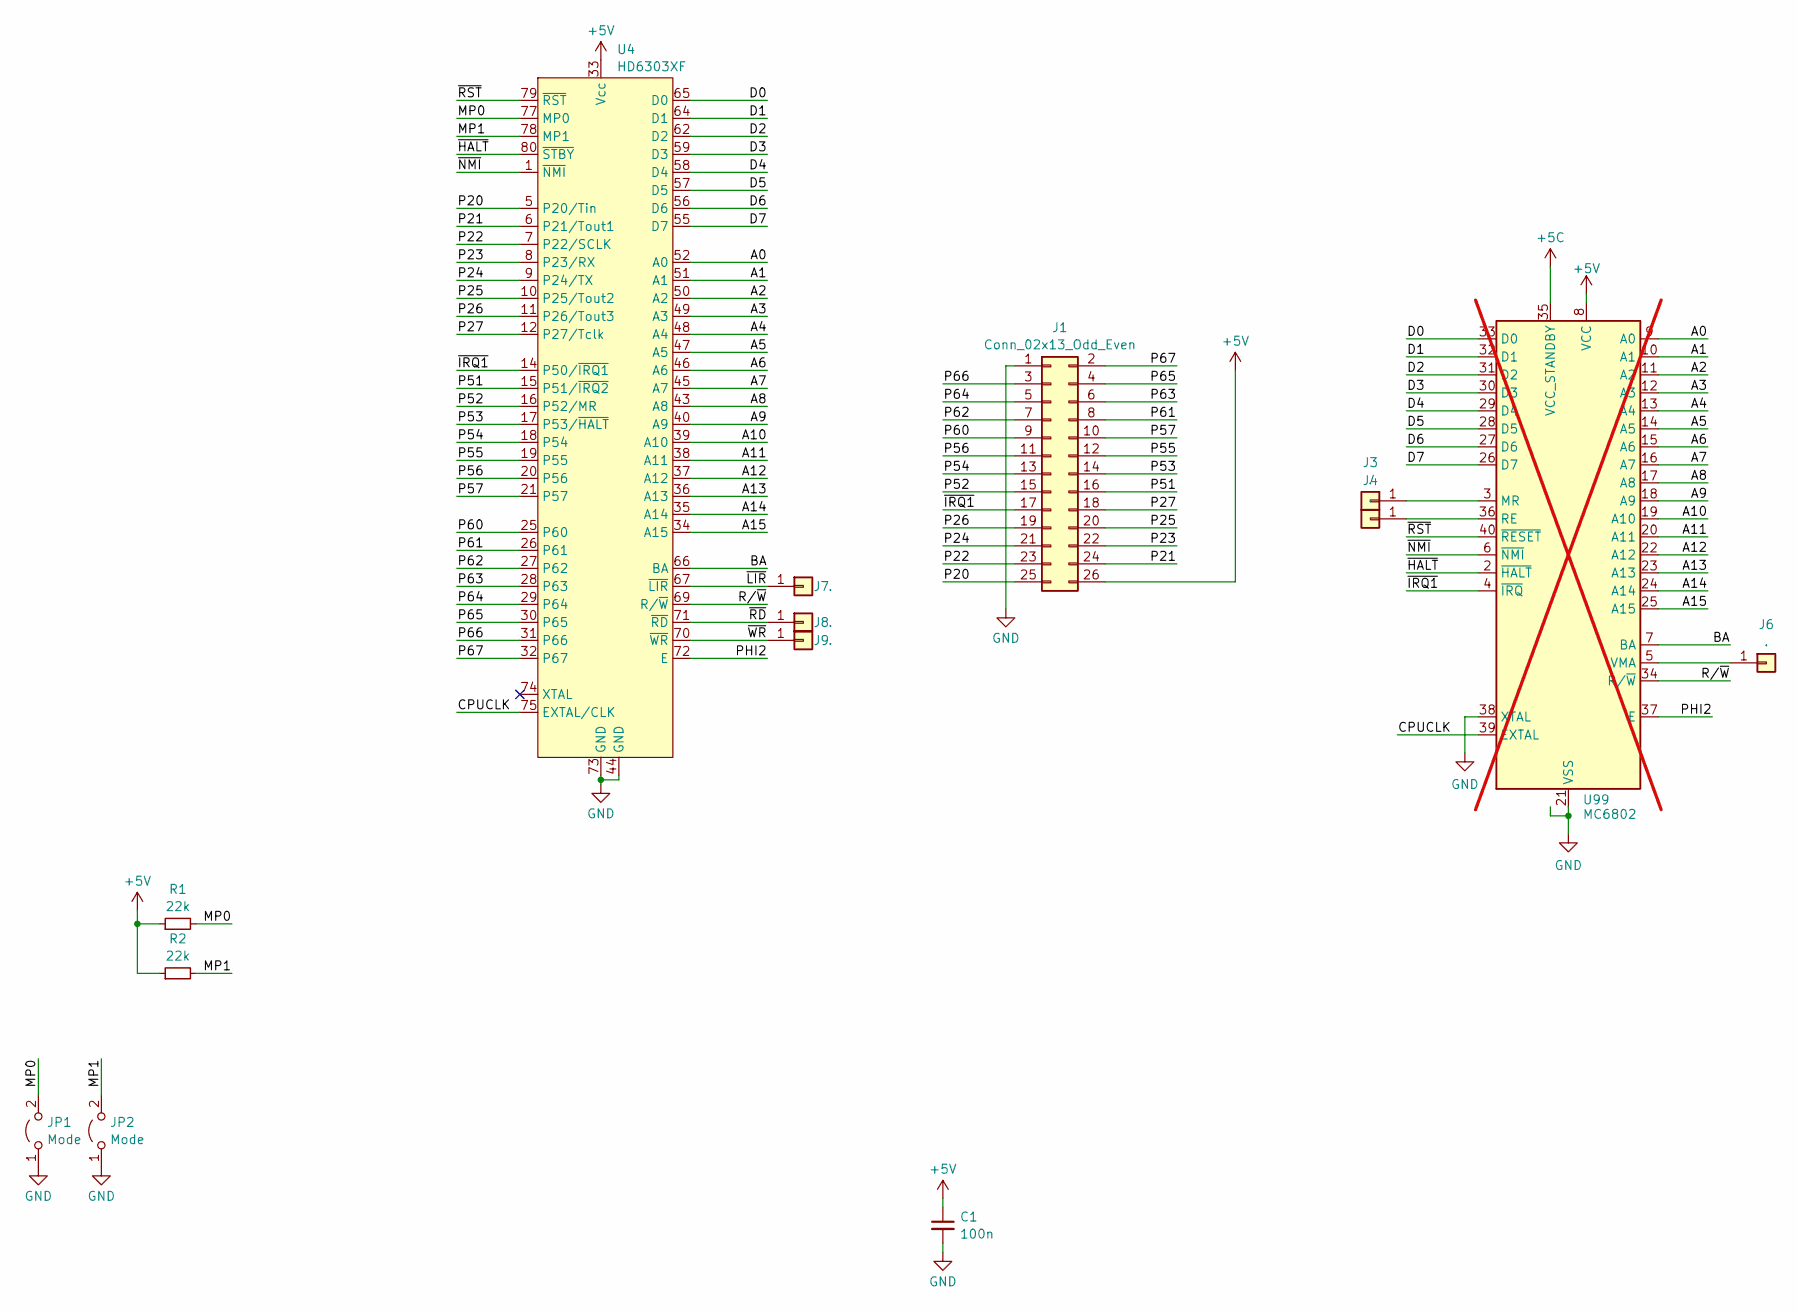
[picture p103: schematic 6303_FP.kicad_sch]

Parts:
C1: 100n; C_1206_3216Metric_Pad1.33x1.80mm_HandSolder
J1: Conn_02x13_Odd_Even; PinHeader_2x13_P2.54mm_Horizontal
J3, J4, J6, J7, J8, J9: .; PinHeader_1x01_P2.00mm_Vertical
JP1, JP2: Mode; PinHeader_1x02_P2.54mm_Vertical
R1, R2: 22k; R_1206_3216Metric_Pad1.30x1.75mm_HandSolder
U4: HD6303XF; PQFP-80_14x20mm_P0.8mm
U99: MC6802; DIP-40_W15.24mm; not fitted

Connections:
+5V: C1.1, J1.26, R1.1, R2.1, U4.33 (Vcc); also elsewhere on the board
/A0: U4.52 (A0); also elsewhere on the board
/A1: U4.51 (A1); also elsewhere on the board
/A2: U4.50 (A2); also elsewhere on the board
/A3: U4.49 (A3); also elsewhere on the board
/A4: U4.48 (A4); also elsewhere on the board
/A5: U4.47 (A5); also elsewhere on the board
/A6: U4.46 (A6); also elsewhere on the board
/A7: U4.45 (A7); also elsewhere on the board
/A8: U4.43 (A8); also elsewhere on the board
/A9: U4.40 (A9); also elsewhere on the board
/A10: U4.39 (A10); also elsewhere on the board
/A11: U4.38 (A11); also elsewhere on the board
/A12: U4.37 (A12); also elsewhere on the board
/A13: U4.36 (A13); also elsewhere on the board
/A14: U4.35 (A14); also elsewhere on the board
/A15: U4.34 (A15); also elsewhere on the board
/BA: U4.66 (BA); also elsewhere on the board
/CPUCLK: U4.75 (EXTAL/CLK); also elsewhere on the board
/D0: U4.65 (D0); also elsewhere on the board
/D1: U4.64 (D1); also elsewhere on the board
/D2: U4.62 (D2); also elsewhere on the board
/D3: U4.59 (D3); also elsewhere on the board
/D4: U4.58 (D4); also elsewhere on the board
/D5: U4.57 (D5); also elsewhere on the board
/D6: U4.56 (D6); also elsewhere on the board
/D7: U4.55 (D7); also elsewhere on the board
/MP0: JP1.2 (B), R1.2, U4.77 (MP0)
/MP1: JP2.2 (B), R2.2, U4.78 (MP1)
/P20: J1.25, U4.5 (P20/Tin)
/P21: J1.24, U4.6 (P21/Tout1)
/P22: J1.23, U4.7 (P22/SCLK)
/P23: J1.22, U4.8 (P23/RX)
/P24: J1.21, U4.9 (P24/TX)
/P25: J1.20, U4.10 (P25/Tout2)
/P26: J1.19, U4.11 (P26/Tout3)
/P27: J1.18, U4.12 (P27/Tclk)
/P51: J1.16, U4.15 (P51/~IRQ2)
/P52: J1.15, U4.16 (P52/MR)
/P53: J1.14, U4.17 (P53/~HALT)
/P54: J1.13, U4.18 (P54)
/P55: J1.12, U4.19 (P55)
/P56: J1.11, U4.20 (P56)
/P57: J1.10, U4.21 (P57)
/P60: J1.9, U4.25 (P60)
/P61: J1.8, U4.26 (P61)
/P62: J1.7, U4.27 (P62)
/P63: J1.6, U4.28 (P63)
/P64: J1.5, U4.29 (P64)
/P65: J1.4, U4.30 (P65)
/P66: J1.3, U4.31 (P66)
/P67: J1.2, U4.32 (P67)
/PHI2: U4.72 (E); also elsewhere on the board
/R/~W: U4.69 (R/~W); also elsewhere on the board
/~HALT: U4.80 (~STBY); also elsewhere on the board
/~IRQ1: J1.17, U4.14 (P50/~IRQ1); also elsewhere on the board
/~LIR: J7.1, U4.67 (~LIR)
/~NMI: U4.1 (~NMI); also elsewhere on the board
/~RD: J8.1, U4.71 (~RD)
/~RST: U4.79 (~RST); also elsewhere on the board
/~WR: J9.1, U4.70 (~WR)
GND: C1.2, J1.1, JP1.1 (A), JP2.1 (A), U4.44 (GND), U4.73 (GND); also elsewhere on the board
unnamed 63: J3.1; also elsewhere on the board
unnamed 64: J4.1; also elsewhere on the board
unnamed 65: J6.1; also elsewhere on the board

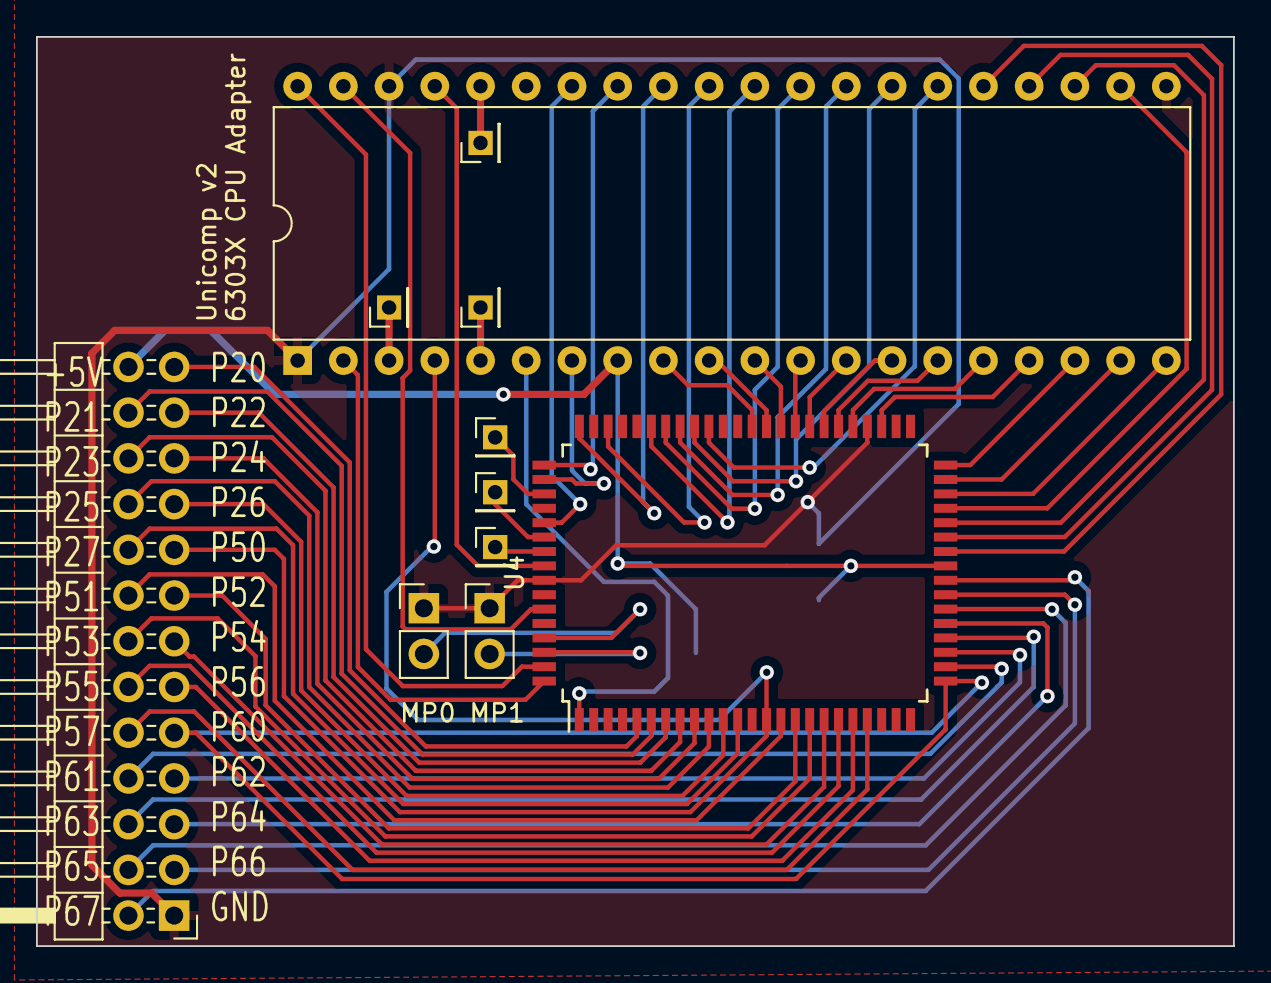
[picture p104: board 6303_FP.kicad_pcb from above]

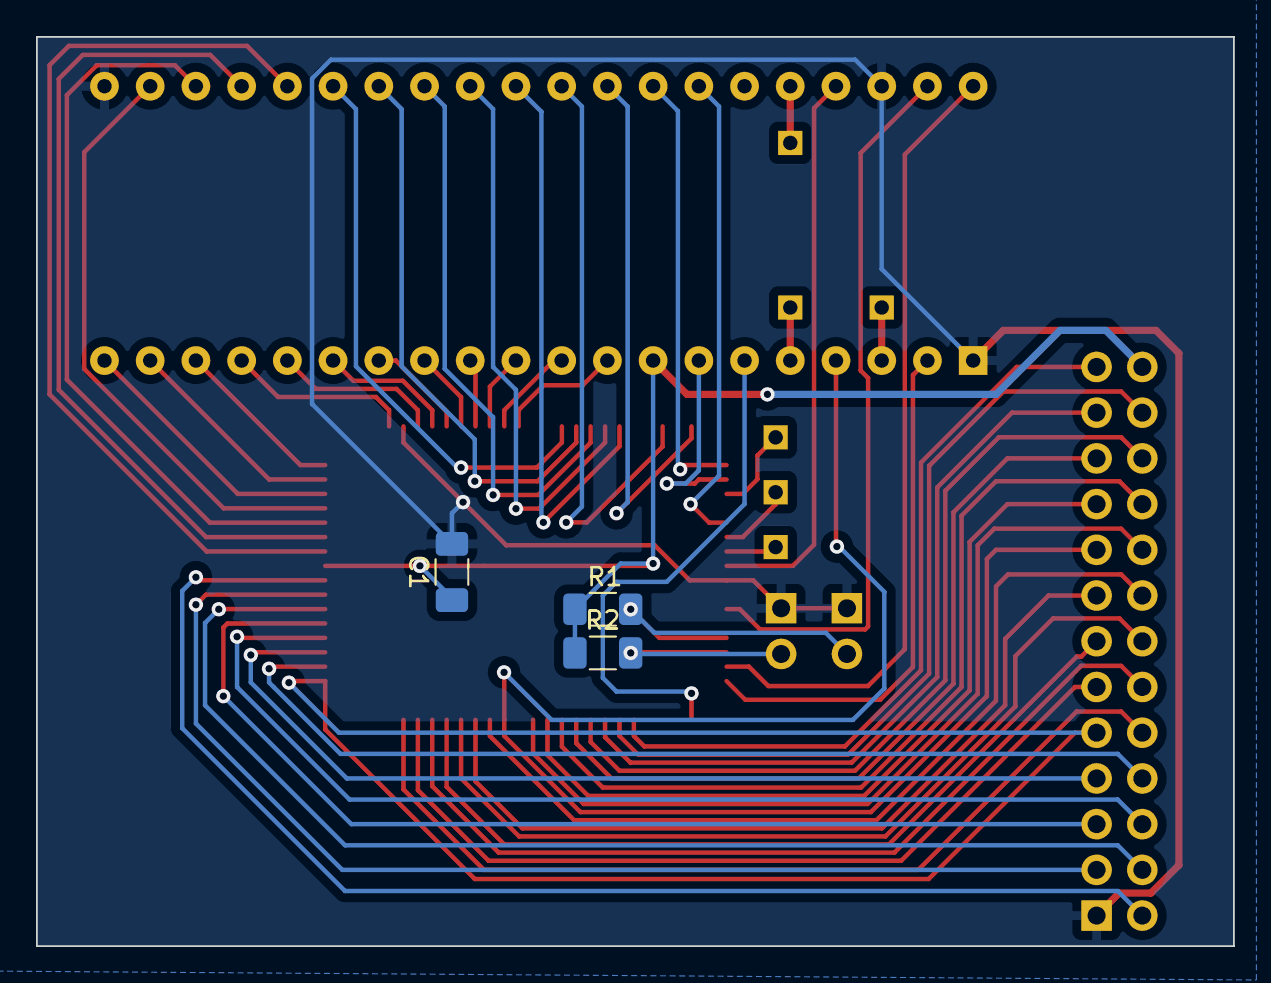
[picture p105: board 6303_FP.kicad_pcb from below]

Board: 2 copper layers, 66.5 x 50.5 mm, 14 parts (3 on the bottom side), 65 nets.

Other parts of the board:
U3: MC6802; DIP-40_W15.24mm

Their connections:
+5V: U3.8 (VCC); also elsewhere on the board
/A0: U3.9 (A0); also elsewhere on the board
/A1: U3.10 (A1); also elsewhere on the board
/A2: U3.11 (A2); also elsewhere on the board
/A3: U3.12 (A3); also elsewhere on the board
/A4: U3.13 (A4); also elsewhere on the board
/A5: U3.14 (A5); also elsewhere on the board
/A6: U3.15 (A6); also elsewhere on the board
/A7: U3.16 (A7); also elsewhere on the board
/A8: U3.17 (A8); also elsewhere on the board
/A9: U3.18 (A9); also elsewhere on the board
/A10: U3.19 (A10); also elsewhere on the board
/A11: U3.20 (A11); also elsewhere on the board
/A12: U3.22 (A12); also elsewhere on the board
/A13: U3.23 (A13); also elsewhere on the board
/A14: U3.24 (A14); also elsewhere on the board
/A15: U3.25 (A15); also elsewhere on the board
/BA: U3.7 (BA); also elsewhere on the board
/CPUCLK: U3.39 (EXTAL); also elsewhere on the board
/D0: U3.33 (D0); also elsewhere on the board
/D1: U3.32 (D1); also elsewhere on the board
/D2: U3.31 (D2); also elsewhere on the board
/D3: U3.30 (D3); also elsewhere on the board
/D4: U3.29 (D4); also elsewhere on the board
/D5: U3.28 (D5); also elsewhere on the board
/D6: U3.27 (D6); also elsewhere on the board
/D7: U3.26 (D7); also elsewhere on the board
/PHI2: U3.37 (E); also elsewhere on the board
/R/~W: U3.34 (R/~W); also elsewhere on the board
/~HALT: U3.2 (~HALT); also elsewhere on the board
/~IRQ1: U3.4 (~IRQ); also elsewhere on the board
/~NMI: U3.6 (~NMI); also elsewhere on the board
/~RST: U3.40 (~RESET); also elsewhere on the board
GND: U3.1 (VSS), U3.21 (VSS), U3.38 (XTAL); also elsewhere on the board
unnamed 63: U3.3 (MR); also elsewhere on the board
unnamed 64: U3.36 (RE); also elsewhere on the board
unnamed 65: U3.5 (VMA); also elsewhere on the board
