roberto314/Unicomp3/CPU_Boards/AdapterBoards/6303X_FP64/6303X_FP64.kicad_pcb

## KiCad design CPU_Boards/AdapterBoards/6303X_FP64/6303X_FP64.kicad_pcb (2024-10-12)

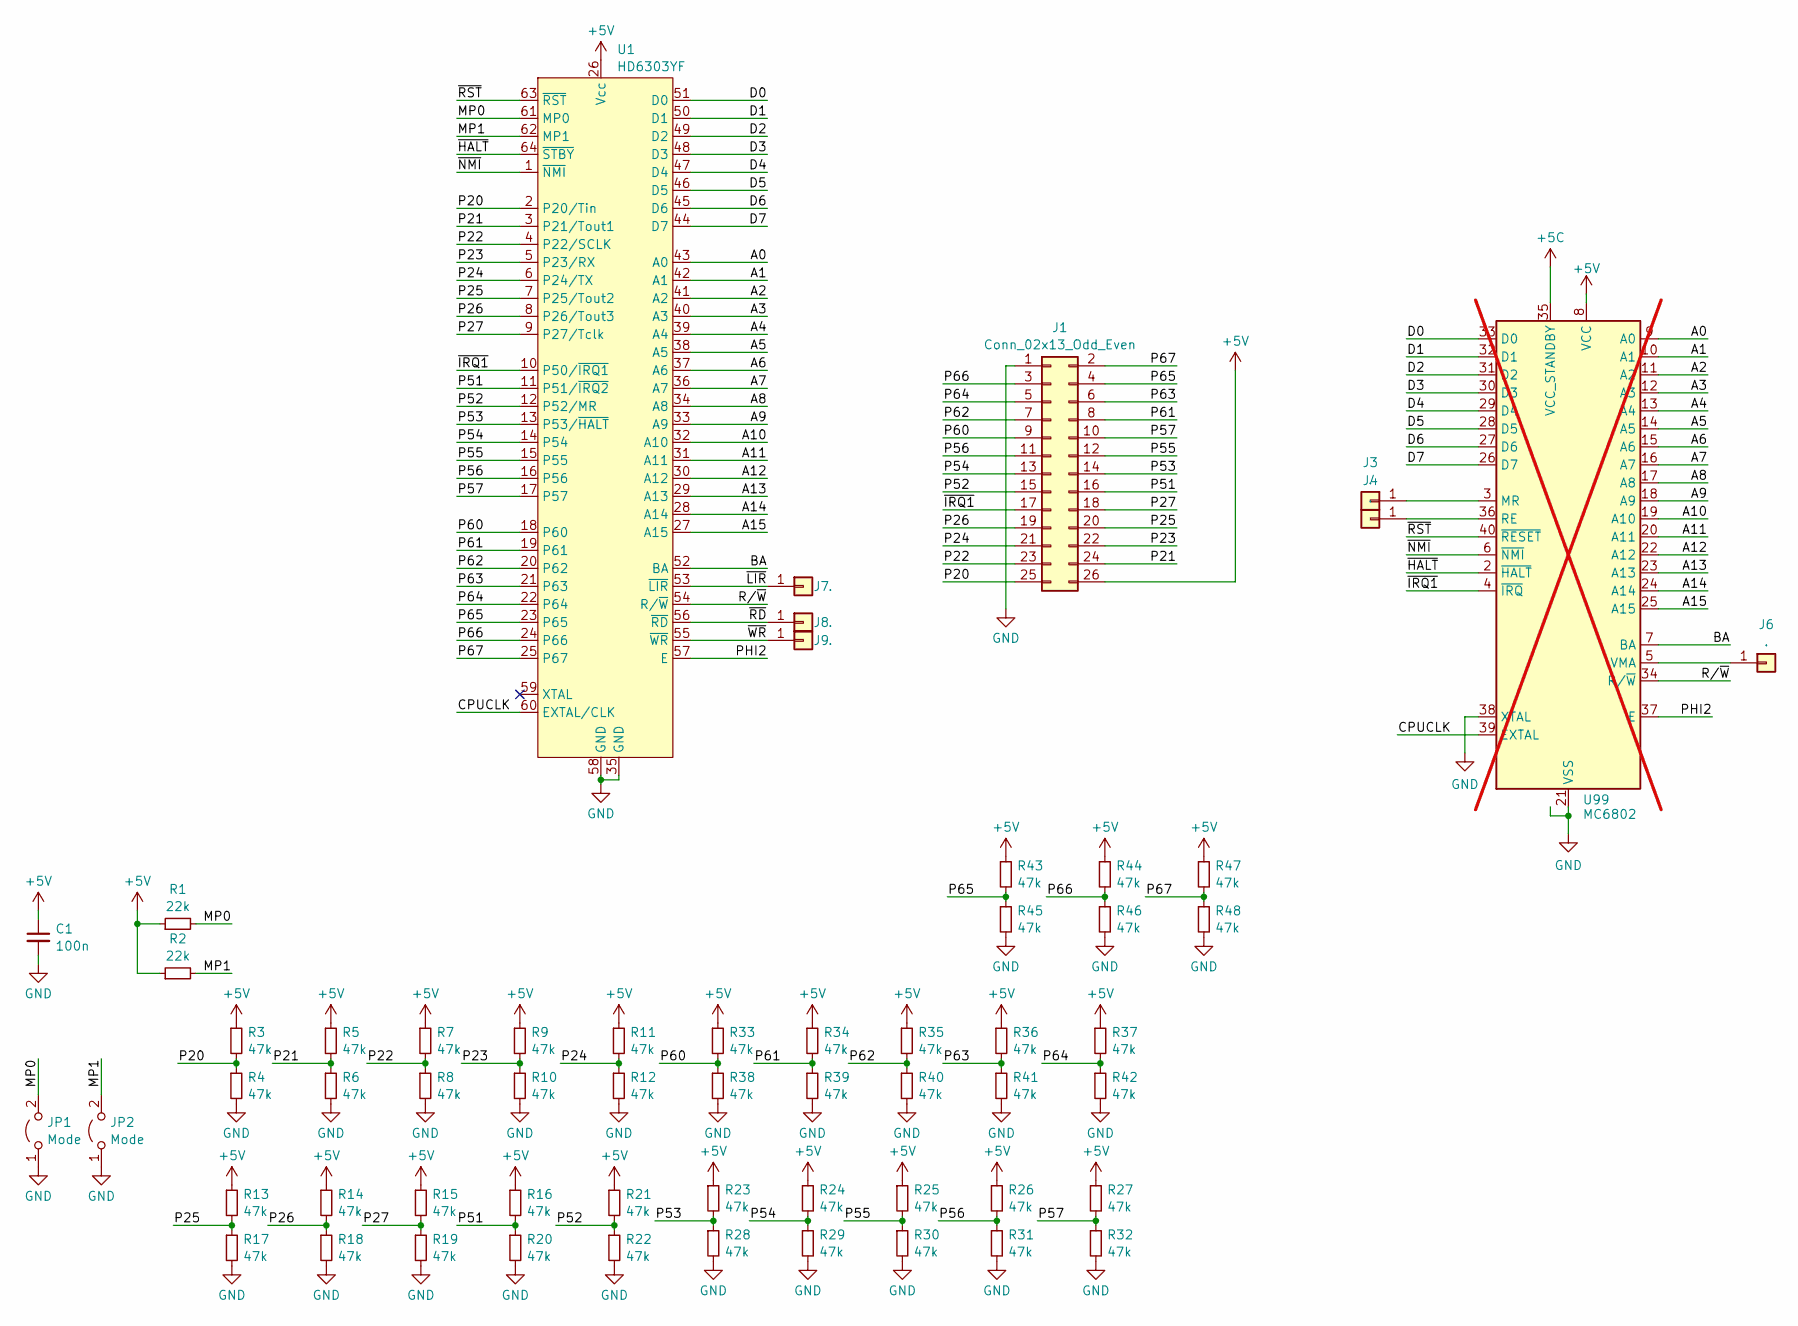
[picture p106: schematic 6303X_FP64.kicad_sch]

Parts:
C1: 100n; C_1206_3216Metric_Pad1.33x1.80mm_HandSolder
J1: Conn_02x13_Odd_Even; PinHeader_2x13_P2.54mm_Horizontal
J3, J4, J6, J7, J8, J9: .; PinHeader_1x01_P2.00mm_Vertical
JP1, JP2: Mode; PinHeader_1x02_P2.54mm_Vertical
R1, R2: 22k; R_1206_3216Metric_Pad1.30x1.75mm_HandSolder
R3, R4, R5, R6, R7, R8, R9, R10, R11, R12, R13, R14, R15, R16, R17, R18, R19, R20, R21, R22, R23, R24, R25, R26, R27, R28, R29, R30, R31, R32, R33, R34, R35, R36, R37, R38, R39, R40, R41, R42, R43, R44, R45, R46, R47, R48: 47k; R_1206_3216Metric_Pad1.30x1.75mm_HandSolder
U1: HD6303YF; QFP-64_14x20_Pitch1mm
U99: MC6802; DIP-40_W15.24mm; not fitted

Connections:
+5V: C1.1, J1.26, R1.1, R2.1, R3.1, R5.1, R7.1, R9.1, R11.1, R13.1, R14.1, R15.1, R16.1, R21.1, R23.1, R24.1, R25.1, R26.1, R27.1, R33.1, R34.1, R35.1, R36.1, R37.1, R43.1, R44.1, R47.1, U1.26 (Vcc); also elsewhere on the board
/A0: U1.43 (A0); also elsewhere on the board
/A1: U1.42 (A1); also elsewhere on the board
/A2: U1.41 (A2); also elsewhere on the board
/A3: U1.40 (A3); also elsewhere on the board
/A4: U1.39 (A4); also elsewhere on the board
/A5: U1.38 (A5); also elsewhere on the board
/A6: U1.37 (A6); also elsewhere on the board
/A7: U1.36 (A7); also elsewhere on the board
/A8: U1.34 (A8); also elsewhere on the board
/A9: U1.33 (A9); also elsewhere on the board
/A10: U1.32 (A10); also elsewhere on the board
/A11: U1.31 (A11); also elsewhere on the board
/A12: U1.30 (A12); also elsewhere on the board
/A13: U1.29 (A13); also elsewhere on the board
/A14: U1.28 (A14); also elsewhere on the board
/A15: U1.27 (A15); also elsewhere on the board
/BA: U1.52 (BA); also elsewhere on the board
/CPUCLK: U1.60 (EXTAL/CLK); also elsewhere on the board
/D0: U1.51 (D0); also elsewhere on the board
/D1: U1.50 (D1); also elsewhere on the board
/D2: U1.49 (D2); also elsewhere on the board
/D3: U1.48 (D3); also elsewhere on the board
/D4: U1.47 (D4); also elsewhere on the board
/D5: U1.46 (D5); also elsewhere on the board
/D6: U1.45 (D6); also elsewhere on the board
/D7: U1.44 (D7); also elsewhere on the board
/MP0: JP1.2 (B), R1.2, U1.61 (MP0)
/MP1: JP2.2 (B), R2.2, U1.62 (MP1)
/P20: J1.25, R3.2, R4.1, U1.2 (P20/Tin)
/P21: J1.24, R5.2, R6.1, U1.3 (P21/Tout1)
/P22: J1.23, R7.2, R8.1, U1.4 (P22/SCLK)
/P23: J1.22, R9.2, R10.1, U1.5 (P23/RX)
/P24: J1.21, R11.2, R12.1, U1.6 (P24/TX)
/P25: J1.20, R13.2, R17.1, U1.7 (P25/Tout2)
/P26: J1.19, R14.2, R18.1, U1.8 (P26/Tout3)
/P27: J1.18, R15.2, R19.1, U1.9 (P27/Tclk)
/P51: J1.16, R16.2, R20.1, U1.11 (P51/~IRQ2)
/P52: J1.15, R21.2, R22.1, U1.12 (P52/MR)
/P53: J1.14, R23.2, R28.1, U1.13 (P53/~HALT)
/P54: J1.13, R24.2, R29.1, U1.14 (P54)
/P55: J1.12, R25.2, R30.1, U1.15 (P55)
/P56: J1.11, R26.2, R31.1, U1.16 (P56)
/P57: J1.10, R27.2, R32.1, U1.17 (P57)
/P60: J1.9, R33.2, R38.1, U1.18 (P60)
/P61: J1.8, R34.2, R39.1, U1.19 (P61)
/P62: J1.7, R35.2, R40.1, U1.20 (P62)
/P63: J1.6, R36.2, R41.1, U1.21 (P63)
/P64: J1.5, R37.2, R42.1, U1.22 (P64)
/P65: J1.4, R43.2, R45.1, U1.23 (P65)
/P66: J1.3, R44.2, R46.1, U1.24 (P66)
/P67: J1.2, R47.2, R48.1, U1.25 (P67)
/PHI2: U1.57 (E); also elsewhere on the board
/R/~W: U1.54 (R/~W); also elsewhere on the board
/~HALT: U1.64 (~STBY); also elsewhere on the board
/~IRQ1: J1.17, U1.10 (P50/~IRQ1); also elsewhere on the board
/~LIR: J7.1, U1.53 (~LIR)
/~NMI: U1.1 (~NMI); also elsewhere on the board
/~RD: J8.1, U1.56 (~RD)
/~RST: U1.63 (~RST); also elsewhere on the board
/~WR: J9.1, U1.55 (~WR)
GND: C1.2, J1.1, JP1.1 (A), JP2.1 (A), R4.2, R6.2, R8.2, R10.2, R12.2, R17.2, R18.2, R19.2, R20.2, R22.2, R28.2, R29.2, R30.2, R31.2, R32.2, R38.2, R39.2, R40.2, R41.2, R42.2, R45.2, R46.2, R48.2, U1.35 (GND), U1.58 (GND); also elsewhere on the board
unnamed 63: J3.1; also elsewhere on the board
unnamed 64: J4.1; also elsewhere on the board
unnamed 65: J6.1; also elsewhere on the board

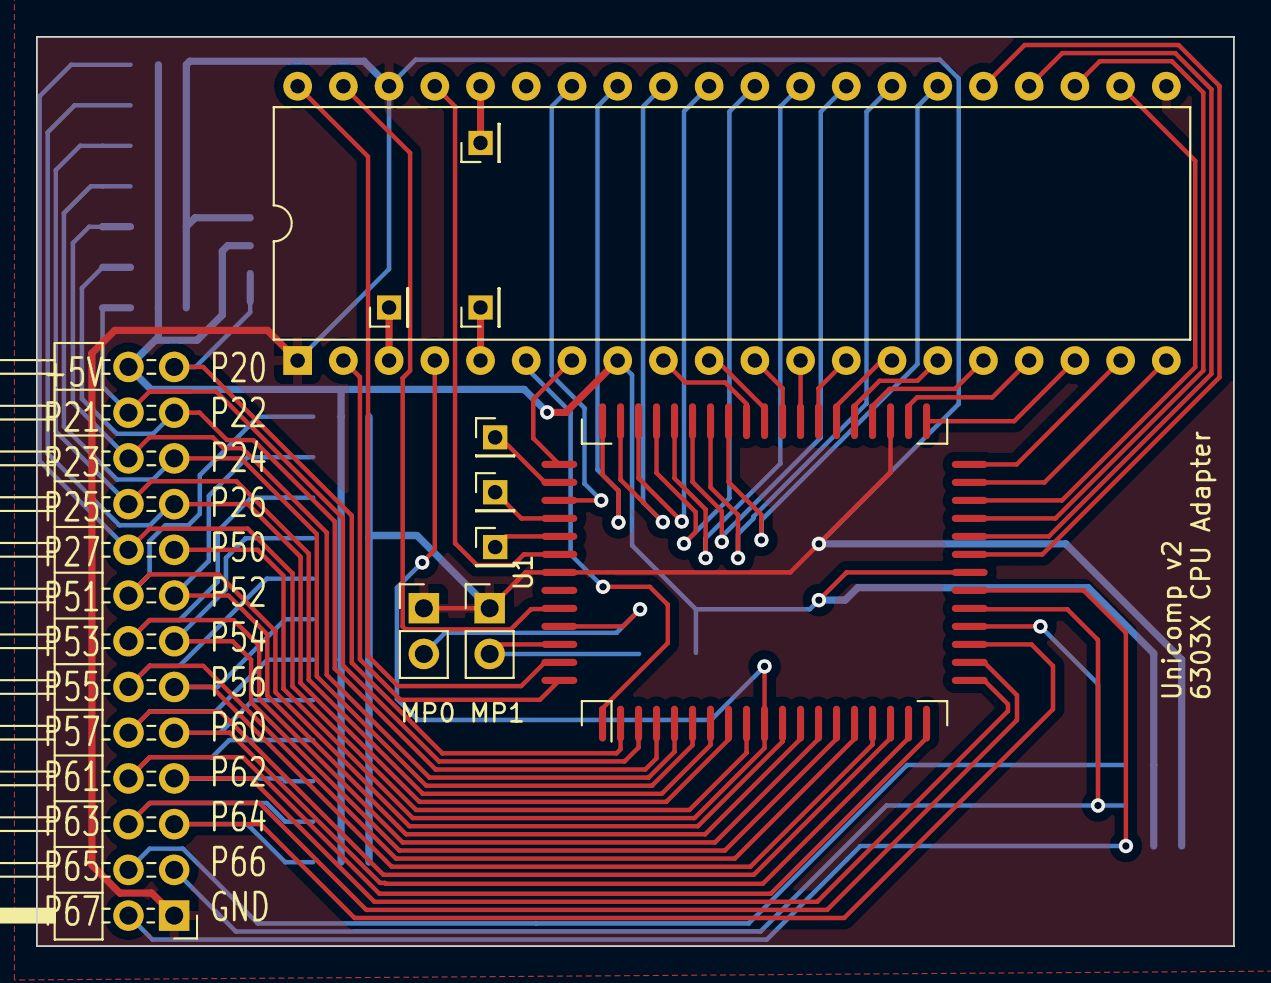
[picture p107: board 6303X_FP64.kicad_pcb from above]

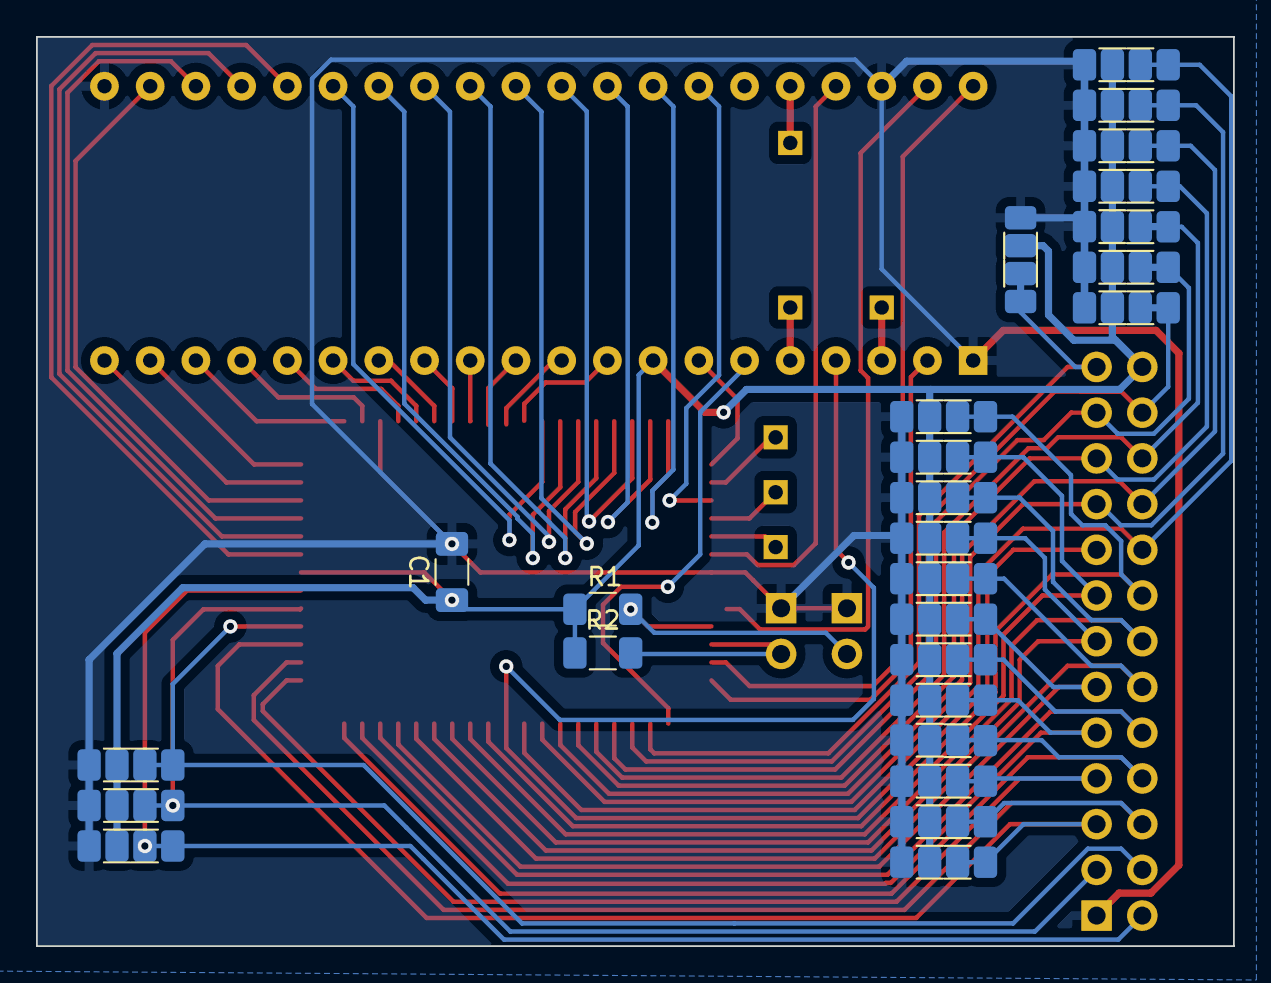
[picture p108: board 6303X_FP64.kicad_pcb from below]

Board: 2 copper layers, 66.5 x 50.5 mm, 60 parts (49 on the bottom side), 65 nets.

Other parts of the board:
U3: MC6802; DIP-40_W15.24mm

Their connections:
+5V: U3.8 (VCC); also elsewhere on the board
/A0: U3.9 (A0); also elsewhere on the board
/A1: U3.10 (A1); also elsewhere on the board
/A2: U3.11 (A2); also elsewhere on the board
/A3: U3.12 (A3); also elsewhere on the board
/A4: U3.13 (A4); also elsewhere on the board
/A5: U3.14 (A5); also elsewhere on the board
/A6: U3.15 (A6); also elsewhere on the board
/A7: U3.16 (A7); also elsewhere on the board
/A8: U3.17 (A8); also elsewhere on the board
/A9: U3.18 (A9); also elsewhere on the board
/A10: U3.19 (A10); also elsewhere on the board
/A11: U3.20 (A11); also elsewhere on the board
/A12: U3.22 (A12); also elsewhere on the board
/A13: U3.23 (A13); also elsewhere on the board
/A14: U3.24 (A14); also elsewhere on the board
/A15: U3.25 (A15); also elsewhere on the board
/BA: U3.7 (BA); also elsewhere on the board
/CPUCLK: U3.39 (EXTAL); also elsewhere on the board
/D0: U3.33 (D0); also elsewhere on the board
/D1: U3.32 (D1); also elsewhere on the board
/D2: U3.31 (D2); also elsewhere on the board
/D3: U3.30 (D3); also elsewhere on the board
/D4: U3.29 (D4); also elsewhere on the board
/D5: U3.28 (D5); also elsewhere on the board
/D6: U3.27 (D6); also elsewhere on the board
/D7: U3.26 (D7); also elsewhere on the board
/PHI2: U3.37 (E); also elsewhere on the board
/R/~W: U3.34 (R/~W); also elsewhere on the board
/~HALT: U3.2 (~HALT); also elsewhere on the board
/~IRQ1: U3.4 (~IRQ); also elsewhere on the board
/~NMI: U3.6 (~NMI); also elsewhere on the board
/~RST: U3.40 (~RESET); also elsewhere on the board
GND: U3.1 (VSS), U3.21 (VSS), U3.38 (XTAL); also elsewhere on the board
unnamed 63: U3.3 (MR); also elsewhere on the board
unnamed 64: U3.36 (RE); also elsewhere on the board
unnamed 65: U3.5 (VMA); also elsewhere on the board
