roberto314/Unicomp3/RamRomBoard/stm32_firmware/F401-blackpill_Unicomp3_RAMROM/main.h

/*
 * main.h
 *
 *  Created on: Sep 23, 2020
 *      Author: rob
 */

#ifndef MAIN_H_
#define MAIN_H_

#include <stdio.h>
#include <string.h>
#include "ch.h"
#include "hal.h"

#include "shell.h"
#include "chprintf.h"
#include "comm.h"

#endif /* MAIN_H_ */
